maccody/KanaChordPlus/software/kanji_ms.h

/* kanji_ms.h */
/**
This file is part of KanaChordPlus Keyboard.
 Copyright (C) 2024 Mac A. Cody

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
 You should have received a copy of the GNU General Public License
 along with this program.  If not, see <http://www.gnu.org/licenses/>.
**/

const char kanji_ms4E00[] = "one, one radical (no.1)";
const char kanji_ms5927[] = "large, big";
const char kanji_ms4EBA[] = "person";
const char kanji_ms898B[] = "see, hopes, chances, idea, opinion, look at, visible";
const char kanji_ms51FA[] = "exit, leave, go out, come out, put out, protrude";
const char kanji_ms4E2D[] = "in, inside, middle, mean, center";
const char kanji_ms601D[] = "think";
const char kanji_ms6642[] = "time, hour";
const char kanji_ms65E5[] = "day, sun, Japan, counter for days";
const char kanji_ms4E0A[] = "above, up";
const char kanji_ms6C17[] = "spirit, mind, air, atmosphere, mood";
const char kanji_ms884C[] = "going, journey, carry out, conduct, act, line, row, bank";
const char kanji_ms76EE[] = "eye, class, look, insight, experience, care, favor";
const char kanji_ms9593[] = "interval, space";
const char kanji_ms751F[] = "life, genuine, birth";
const char kanji_ms5F8C[] = "behind, back, later";
const char kanji_ms8A00[] = "say, word";
const char kanji_ms5206[] = "part, minute of time, segment, share, degree, one's lot, duty, understand, know, rate, 1%, chances, shaku/100";
const char kanji_ms524D[] = "in front, before";
const char kanji_ms81EA[] = "oneself";
const char kanji_ms77E5[] = "know, wisdom";
const char kanji_ms624B[] = "hand";
const char kanji_ms5168[] = "whole, entire, all, complete, fulfill";
const char kanji_ms672C[] = "book, present, main, origin, true, real, counter for long cylindrical things";
const char kanji_ms6765[] = "come, due, next, cause, become";
const char kanji_ms4E8B[] = "matter, thing, fact, business, reason, possibly";
const char kanji_ms65B9[] = "direction, person, alternative";
const char kanji_ms7269[] = "thing, object, matter";
const char kanji_ms4E0B[] = "below, down, descend, give, low, inferior";
const char kanji_ms610F[] = "idea, mind, heart, taste, thought, desire, care, liking";
const char kanji_ms5EA6[] = "degrees, occurrence, time, counter for occurrences, consider, attitude";
const char kanji_ms5165[] = "enter, insert";
const char kanji_ms5B50[] = "child, sign of the rat, 11PM-1AM, first sign of Chinese zodiac";
const char kanji_ms4E8C[] = "two, two radical (no. 7)";
const char kanji_ms8A71[] = "tale, talk";
const char kanji_ms7ACB[] = "stand up, rise, set up, erect";
const char kanji_ms4F53[] = "body, substance, object, reality, counter for images";
const char kanji_ms4E0D[] = "negative, non-, bad, ugly, clumsy";
const char kanji_ms5FC3[] = "heart, mind, spirit, heart radical (no. 61)";
const char kanji_ms8EAB[] = "somebody, person, one's station in life";
const char kanji_ms660E[] = "bright, light";
const char kanji_ms4F55[] = "what";
const char kanji_ms5473[] = "flavor, taste";
const char kanji_ms90E8[] = "section, bureau, dept, class, copy, part, portion, counter for copies of a newspaper or magazine";
const char kanji_ms5E74[] = "year, counter for years";
const char kanji_ms5834[] = "location, place";
const char kanji_ms7121[] = "nothingness, none, ain't, nothing, nil, not";
const char kanji_ms6700[] = "utmost, most, extreme";
const char kanji_ms5C0F[] = "little, small";
const char kanji_ms8005[] = "someone, person";
const char kanji_ms9577[] = "long, leader, superior, senior";
const char kanji_ms901A[] = "traffic, pass through, avenue, commute, counter for letters, notes, documents, etc.";
const char kanji_ms540C[] = "same, agree, equal";
const char kanji_ms611F[] = "emotion, feeling, sensation";
const char kanji_ms5F53[] = "hit, right, appropriate, himself";
const char kanji_ms529B[] = "power, strength, strong, strain, bear up, exert";
const char kanji_ms5916[] = "outside";
const char kanji_ms5730[] = "ground, earth";
const char kanji_ms9762[] = "mask, face, features, surface";
const char kanji_ms5408[] = "fit, suit, join, 0.1";
const char kanji_ms7406[] = "logic, arrangement, reason, justice, truth";
const char kanji_ms4EE5[] = "by means of, because, in view of, compared with";
const char kanji_ms9AD8[] = "tall, high, expensive";
const char kanji_ms8FD1[] = "near, early, akin, tantamount";
const char kanji_ms4F1A[] = "meeting, meet, party, association, interview, join";
const char kanji_ms6301[] = "hold, have";
const char kanji_ms5B9F[] = "reality, truth, seed, fruit, nut";
const char kanji_ms767D[] = "white";
const char kanji_ms58F0[] = "voice";
const char kanji_ms53E3[] = "mouth";
const char kanji_ms5148[] = "before, ahead, previous, future, precedence";
const char kanji_ms52D5[] = "move, motion, change, confusion, shift, shake";
const char kanji_ms982D[] = "head, counter for large animals";
const char kanji_ms4ECA[] = "now";
const char kanji_ms6240[] = "place, extent";
const char kanji_ms6587[] = "sentence, literature, style, art, decoration, figures, plan, literary radical (no. 67)";
const char kanji_ms5909[] = "unusual, change, strange";
const char kanji_ms9854[] = "face, expression";
const char kanji_ms4E16[] = "generation, world, society, public";
const char kanji_ms767A[] = "departure, discharge, publish, emit, start from, disclose, counter for gunshots";
const char kanji_ms540D[] = "name, noted, distinguished, reputation";
const char kanji_ms8DB3[] = "leg, foot, be sufficient, counter for pairs of footwear";
const char kanji_ms7684[] = "bull's eye, mark, target, object, adjective ending";
const char kanji_ms8272[] = "color";
const char kanji_ms60AA[] = "bad, vice, rascal, false, evil, wrong";
const char kanji_ms60C5[] = "feelings, emotion, passion, sympathy, circumstances, facts";
const char kanji_ms5207[] = "cut, cutoff, be sharp";
const char kanji_ms7136[] = "sort of thing, so, if so, in that case, well";
const char kanji_ms8003[] = "consider, think over";
const char kanji_ms4F5C[] = "make, production, prepare, build";
const char kanji_ms8FD4[] = "return, answer, fade, repay";
const char kanji_ms843D[] = "fall, drop, come down, village, hamlet";
const char kanji_ms7D50[] = "tie, bind, contract, join, organize, do up hair, fasten";
const char kanji_ms958B[] = "open, unfold, unseal";
const char kanji_ms5BB6[] = "house, home, family, professional, expert, performer";
const char kanji_ms6B63[] = "correct, justice, righteous, 10**40";
const char kanji_ms98A8[] = "wind, air, style, manner";
const char kanji_ms521D[] = "first time, beginning";
const char kanji_ms4E09[] = "three";
const char kanji_ms91CD[] = "heavy, important, esteem, respect, heap up, pile up, nest of boxes, -fold";
const char kanji_ms5C11[] = "few, little";
const char kanji_ms5411[] = "yonder, facing, beyond, confront, defy, tend toward, approach";
const char kanji_ms6708[] = "month, moon";
const char kanji_ms73FE[] = "present, existing, actual";
const char kanji_ms6570[] = "number, strength, fate, law, figures";
const char kanji_ms7528[] = "utilize, business, service, use, employ";
const char kanji_ms7A7A[] = "empty, sky, void, vacant, vacuum";
const char kanji_ms8868[] = "surface, table, chart, diagram";
const char kanji_ms5185[] = "inside, within, between, among, house, home";
const char kanji_ms97F3[] = "sound, noise";
const char kanji_ms805E[] = "hear, ask, listen";
const char kanji_ms69D8[] = "Esq., way, manner, situation, polite suffix";
const char kanji_ms771F[] = "true, reality, Buddhist sect";
const char kanji_ms9053[] = "road-way, street, district, journey, course, moral, teachings";
const char kanji_ms7740[] = "don, arrive, wear, counter for suits of clothing";
const char kanji_ms4EE3[] = "substitute, change, convert, replace, period, age, counter for decades of ages, eras, etc., generation, charge, rate, fee";
const char kanji_ms5973[] = "woman, female";
const char kanji_ms76F8[] = "inter-, mutual, together, each other, minister of state, councillor, aspect, phase, physiognomy";
const char kanji_ms8449[] = "leaf, plane, lobe, needle, blade, spear, counter for flat things, fragment, piece";
const char kanji_ms597D[] = "fond, pleasing, like something";
const char kanji_ms591A[] = "many, frequent, much";
const char kanji_ms5B89[] = "relax, cheap, low, quiet, rested, contented, peaceful";
const char kanji_ms554F[] = "question, ask, problem";
const char kanji_ms5F85[] = "wait, depend on";
const char kanji_ms76F4[] = "straightaway, honesty, frankness, fix, repair";
const char kanji_ms5B9A[] = "determine, fix, establish, decide";
const char kanji_ms66F8[] = "write";
const char kanji_ms4FE1[] = "faith, truth, fidelity, trust";
const char kanji_ms5BFE[] = "vis-a-vis, opposite, even, equal, versus, anti-, compare";
const char kanji_ms5149[] = "ray, light";
const char kanji_ms534A[] = "half, middle, odd number, semi-, part-";
const char kanji_ms96C6[] = "gather, meet, congregate, swarm, flock";
const char kanji_ms5225[] = "separate, branch off, diverge, fork, another, extra, specially";
const char kanji_ms6C7A[] = "decide, fix, agree upon, appoint";
const char kanji_ms4E3B[] = "lord, chief, master, main thing, principal";
const char kanji_ms6B69[] = "walk, counter for steps";
const char kanji_ms89E3[] = "unravel, notes, key, explanation, understanding, untie, undo, solve, answer, cancel, absolve, explain, minute";
const char kanji_ms6B7B[] = "death, die";
const char kanji_ms6027[] = "sex, gender, nature";
const char kanji_ms5F37[] = "strong";
const char kanji_ms7F6E[] = "placement, put, set, deposit, leave behind, keep, employ, pawn";
const char kanji_ms7B11[] = "laugh";
const char kanji_ms98DF[] = "eat, food";
const char kanji_ms6307[] = "finger, point to, indicate, put into, play (chess), measure (ruler)";
const char kanji_ms6B8B[] = "remainder, leftover, balance";
const char kanji_ms5143[] = "beginning, former time, origin";
const char kanji_ms5C4B[] = "roof, house, shop, dealer, seller";
const char kanji_ms6D41[] = "current, a sink, flow, forfeit";
const char kanji_ms65B0[] = "new";
const char kanji_ms547C[] = "call, call out to, invite";
const char kanji_ms9060[] = "distant, far";
const char kanji_ms5341[] = "ten";
const char kanji_ms4F7F[] = "use, send on a mission, order, messenger, envoy, ambassador, cause";
const char kanji_ms7D42[] = "end, finish";
const char kanji_ms6559[] = "teach, faith, doctrine";
const char kanji_ms95A2[] = "connection, barrier, gateway, involve, concerning";
const char kanji_ms606F[] = "breath, respiration, son, interest (on money), nuture, rest, coming to an end";
const char kanji_ms914D[] = "distribute, spouse, exile, rationing";
const char kanji_ms8AAC[] = "opinion, theory, explanation, rumor";
const char kanji_ms795E[] = "gods, mind, soul";
const char kanji_ms53D6[] = "take, fetch, take up";
const char kanji_ms7537[] = "male";
const char kanji_ms5929[] = "heavens, sky, imperial";
const char kanji_ms8ABF[] = "tune, tone, meter, key (music), writing style, prepare, exorcise, investigate, harmonize, mediate";
const char kanji_ms6B21[] = "next, order, sequence";
const char kanji_ms59FF[] = "figure, form, shape";
const char kanji_ms80CC[] = "stature, height, back, behind, disobey, defy, go back on, rebel";
const char kanji_ms899A[] = "memorize, learn, remember, awake, sober up";
const char kanji_ms697D[] = "music, comfort, ease";
const char kanji_ms7D76[] = "discontinue, sever, cut off, abstain, interrupt, suppress, be beyond, without match, peerless, unparalleled";
const char kanji_ms91D1[] = "gold";
const char kanji_ms60F3[] = "concept, think, idea, thought";
const char kanji_ms679C[] = "fruit, reward, carry out, achieve, complete, end, finish, succeed";
const char kanji_ms8D77[] = "rouse, wake up, get up";
const char kanji_ms5F62[] = "shape, form, style";
const char kanji_ms5E73[] = "even, flat, peace";
const char kanji_ms8981[] = "need, main point, essence, pivot, key to";
const char kanji_ms5F15[] = "pull, tug, jerk, admit, install, quote, refer to";
const char kanji_ms547D[] = "fate, command, decree, destiny, life, appoint";
const char kanji_ms904B[] = "carry, luck, destiny, fate, lot, transport, progress, advance";
const char kanji_ms82E6[] = "suffering, trial, worry, hardship, feel bitter, scowl";
const char kanji_ms5F97[] = "gain, get, find, earn, acquire, can, may, able to, profit, advantage, benefit";
const char kanji_ms4ED5[] = "attend, doing, official, serve";
const char kanji_ms591C[] = "night, evening";
const char kanji_ms4F1D[] = "transmit, go along, walk along, follow, report, communicate, legend, tradition";
const char kanji_ms653E[] = "set free, release, fire, shoot, emit, banish, liberate";
const char kanji_ms5931[] = "lose, error, fault, disadvantage, loss";
const char kanji_ms9023[] = "take along, lead, join, connect, party, gang, clique";
const char kanji_ms6DF1[] = "deep, heighten, intensify, strengthen";
const char kanji_ms7A81[] = "stab, protruding, thrust, pierce, prick, collision, sudden";
const char kanji_ms754C[] = "world, boundary";
const char kanji_ms6210[] = "turn into, become, get, grow, elapse, reach";
const char kanji_ms70B9[] = "spot, point, mark, speck, decimal point";
const char kanji_ms65E9[] = "early, fast";
const char kanji_ms6D88[] = "extinguish, blow out, turn off, neutralize, cancel";
const char kanji_ms56DE[] = "-times, round, game, revolve, counter for occurrences";
const char kanji_ms53D7[] = "accept, undergo, answer (phone), take, get, catch, receive";
const char kanji_ms5F35[] = "counter for bows & stringed instruments, stretch, spread, put up (tent)";
const char kanji_ms53CD[] = "anti-";
const char kanji_ms7531[] = "wherefore, a reason";
const char kanji_ms5B57[] = "character, letter, word, section of village";
const char kanji_ms5FC5[] = "invariably, certain, inevitable";
const char kanji_ms5316[] = "change, take the form of, influence, enchant, delude, -ization";
const char kanji_ms96E2[] = "detach, separation, disjoin, digress";
const char kanji_ms7279[] = "special";
const char kanji_ms8A18[] = "scribe, account, narrative";
const char kanji_ms5728[] = "exist, outskirts, suburbs, located in";
const char kanji_ms904E[] = "overdo, exceed, go beyond, error";
const char kanji_ms4ED6[] = "other, another, the others";
const char kanji_ms6A5F[] = "loom, mechanism, machine, airplane, opportunity, potency, efficacy, occasion";
const char kanji_ms8FFD[] = "chase, drive away, follow, pursue, meanwhile";
const char kanji_ms53BB[] = "gone, past, quit, leave, elapse, eliminate, divorce";
const char kanji_ms5E30[] = "homecoming, arrive at, lead to, result in";
const char kanji_ms4E57[] = "ride, power, multiplication, record, counter for vehicles, board, mount, join";
const char kanji_ms6025[] = "hurry, emergency, sudden, steep";
const char kanji_ms6C34[] = "water";
const char kanji_ms65AD[] = "severance, decline, refuse, apologize, warn, dismiss, prohibit, decision, judgement, cutting";
const char kanji_ms89AA[] = "parent, intimacy, relative, familiarity, dealer (cards)";
const char kanji_ms5B66[] = "study, learning, science";
const char kanji_ms4E21[] = "both, old Japanese coin, counter for carriages (e.g., in a train), two";
const char kanji_ms6A2A[] = "sideways, side, horizontal, width, woof, unreasonable, perverse";
const char kanji_ms5E83[] = "wide, broad, spacious";
const char kanji_ms5E38[] = "usual, ordinary, normal, common, regular, continually, always, long-lasting";
const char kanji_ms5F7C[] = "he, that, the";
const char kanji_ms8A9E[] = "word, speech, language";
const char kanji_ms8D70[] = "run";
const char kanji_ms6E80[] = "full, fullness, enough, satisfy";
const char kanji_ms91CE[] = "plains, field, rustic, civilian life";
const char kanji_ms9996[] = "neck, counter for songs and poems";
const char kanji_ms5BC4[] = "draw near, stop in, bring near, gather, collect, send, forward";
const char kanji_ms56DB[] = "four";
const char kanji_ms9ED2[] = "black";
const char kanji_ms696D[] = "business, vocation, arts, performance";
const char kanji_ms756A[] = "turn, number in a series";
const char kanji_ms9032[] = "advance, proceed, progress, promote";
const char kanji_ms984C[] = "topic, subject";
const char kanji_ms7F8E[] = "beauty, beautiful";
const char kanji_ms6BB5[] = "grade, steps, stairs";
const char kanji_ms7DDA[] = "line, track";
const char kanji_ms6253[] = "strike, hit, knock, pound, dozen";
const char kanji_ms7D4C[] = "sutra, longitude, pass thru, expire, warp";
const char kanji_ms6697[] = "darkness, disappear, shade, informal, grow dark, be blinded";
const char kanji_ms7D30[] = "dainty, get thin, taper, slender, narrow, detailed, precise";
const char kanji_ms5FF5[] = "wish, sense, idea, thought, feeling, desire, attention";
const char kanji_ms72B6[] = "status quo, conditions, circumstances, form, appearance";
const char kanji_ms671F[] = "period, time, date, term";
const char kanji_ms9001[] = "escort, send";
const char kanji_ms98DB[] = "fly, skip (pages), scatter";
const char kanji_ms4F3C[] = "becoming, resemble, counterfeit, imitate, suitable";
const char kanji_ms6709[] = "possess, have, exist, happen, occur, approx";
const char kanji_ms7D20[] = "elementary, principle, naked, uncovered";
const char kanji_ms7B54[] = "solution, answer";
const char kanji_ms8AAD[] = "read";
const char kanji_ms544A[] = "revelation, tell, inform, announce";
const char kanji_ms611B[] = "love, affection, favourite";
const char kanji_ms6B62[] = "stop, halt";
const char kanji_ms9003[] = "escape, flee, shirk, evade, set free";
const char kanji_ms6D6E[] = "floating, float, rise to surface";
const char kanji_ms683C[] = "status, rank, capacity, character, case (law, grammar)";
const char kanji_ms51B7[] = "cool, cold (beer, person), chill";
const char kanji_ms8D64[] = "red";
const char kanji_ms78BA[] = "assurance, firm, tight, hard, solid, confirm, clear, evident";
const char kanji_ms8033[] = "ear";
const char kanji_ms59CB[] = "commence, begin";
const char kanji_ms52DD[] = "victory, win, prevail, excel";
const char kanji_ms80FD[] = "ability, talent, skill, capacity";
const char kanji_ms4E94[] = "five";
const char kanji_ms6CE8[] = "pour, irrigate, shed (tears), flow into, concentrate on, notes, comment, annotate";
const char kanji_ms5C71[] = "mountain";
const char kanji_ms8EE2[] = "revolve, turn around, change";
const char kanji_ms5FDC[] = "apply, answer, yes, OK, reply, accept";
const char kanji_ms5FD8[] = "forget";
const char kanji_ms5B58[] = "exist, suppose, be aware of, believe, feel";
const char kanji_ms614B[] = "attitude, condition, figure, appearance, voice (of verbs)";
const char kanji_ms670D[] = "clothing, admit, obey, discharge";
const char kanji_ms6839[] = "root, radical, head (pimple)";
const char kanji_ms539F[] = "meadow, original, primitive, field, plain, prairie, tundra, wilderness";
const char kanji_ms671B[] = "ambition, full moon, hope, desire, aspire to, expect";
const char kanji_ms7247[] = "one-sided, leaf, sheet, right-side kata radical (no. 91)";
const char kanji_ms5012[] = "overthrow, fall, collapse, drop, break down";
const char kanji_ms6050[] = "fear, dread, awe";
const char kanji_ms9759[] = "quiet";
const char kanji_ms7B2C[] = "No., residence";
const char kanji_ms671D[] = "morning, dynasty, regime, epoch, period, (North) Korea";
const char kanji_ms53F0[] = "pedestal, a stand, counter for machines and vehicles";
const char kanji_ms8B70[] = "deliberation, consultation, debate, consideration";
const char kanji_ms62BC[] = "push, stop, check, subdue, attach, seize, weight, shove, press, seal, do in spite of";
const char kanji_ms9752[] = "blue, green";
const char kanji_ms6CD5[] = "method, law, rule, principle, model, system";
const char kanji_ms6D3B[] = "lively, resuscitation, being helped, living";
const char kanji_ms9CF4[] = "chirp, cry, bark, sound, ring, echo, honk";
const char kanji_ms7D44[] = "association, braid, plait, construct, assemble, unite, cooperate, grapple";
const char kanji_ms5177[] = "tool, utensil, means, possess, ingredients, counter for armor, suits, sets of furniture";
const char kanji_ms592B[] = "husband, man";
const char kanji_ms8A08[] = "plot, plan, scheme, measure";
const char kanji_ms4ED8[] = "adhere, attach, refer to, append";
const char kanji_ms54C1[] = "goods, refinement, dignity, article, counter for meal courses";
const char kanji_ms60B2[] = "grieve, sad, deplore, regret";
const char kanji_ms52A0[] = "add, addition, increase, join, include, Canada";
const char kanji_ms7D04[] = "promise, approximately, shrink";
const char kanji_ms5EA7[] = "squat, seat, cushion, gathering, sit";
const char kanji_ms52E2[] = "forces, energy, military strength";
const char kanji_ms4EA4[] = "mingle, mixing, association, coming & going";
const char kanji_ms53EF[] = "can, passable, mustn't, should not, do not";
const char kanji_ms80F8[] = "bosom, breast, chest, heart, feelings";
const char kanji_ms8996[] = "inspection, regard as, see, look at";
const char kanji_ms53E4[] = "old";
const char kanji_ms5999[] = "exquisite, strange, queer, mystery, miracle, excellent, delicate, charming";
const char kanji_ms71B1[] = "heat, temperature, fever, mania, passion";
const char kanji_ms4E88[] = "beforehand, previous, myself, I";
const char kanji_ms8CEA[] = "substance, quality, matter, temperament";
const char kanji_ms6728[] = "tree, wood";
const char kanji_ms629C[] = "slip out, extract, pull out, pilfer, quote, remove, omit";
const char kanji_ms5074[] = "side, lean, oppose, regret";
const char kanji_ms5229[] = "profit, advantage, benefit";
const char kanji_ms9858[] = "petition, request, vow, wish, hope";
const char kanji_ms5F71[] = "shadow, silhouette, phantom";
const char kanji_ms6BBA[] = "kill, murder, butcher, slice off, split, diminish, reduce, spoil";
const char kanji_ms5922[] = "dream, vision, illusion";
const char kanji_ms592A[] = "plump, thick, big around";
const char kanji_ms5F79[] = "duty, war, campaign, drafted labor, office, service, role";
const char kanji_ms8B58[] = "discriminating, know, write";
const char kanji_ms5B88[] = "guard, protect, defend, obey";
const char kanji_ms5E95[] = "bottom, sole, depth, bottom price, base, kind, sort";
const char kanji_ms9650[] = "limit, restrict, to best of ability";
const char kanji_ms9014[] = "route, way, road";
const char kanji_ms6563[] = "scatter, disperse, spend, squander";
const char kanji_ms8840[] = "blood";
const char kanji_ms7D9A[] = "continue, series, sequel";
const char kanji_ms5C45[] = "reside, to be, exist, live with";
const char kanji_ms88CF[] = "back, amidst, in, reverse, inside, palm, sole, rear, lining, wrong side";
const char kanji_ms8EFD[] = "lightly, trifling, unimportant";
const char kanji_ms4E71[] = "riot, war, disorder, disturb";
const char kanji_ms4F4F[] = "dwell, reside, live, inhabit";
const char kanji_ms5DEE[] = "distinction, difference, variation, discrepancy, margin, balance";
const char kanji_ms5BB9[] = "contain, form, looks";
const char kanji_ms7AEF[] = "edge, origin, end, point, border, verge, cape";
const char kanji_ms82E5[] = "young, if, perhaps, possibly, low number, immature";
const char kanji_ms969B[] = "occasion, side, edge, verge, dangerous, adventurous, indecent, time, when";
const char kanji_ms6295[] = "throw, discard, abandon, launch into, join, invest in, hurl, give up, sell at a loss";
const char kanji_ms4FC2[] = "person in charge, connection, duty, concern oneself";
const char kanji_ms96E3[] = "difficult, impossible, trouble, accident, defect";
const char kanji_ms5358[] = "simple, one, single, merely";
const char kanji_ms56F2[] = "surround, besiege, store, paling, enclosure, encircle, preserve, keep";
const char kanji_ms8CA0[] = "defeat, negative, -, minus, bear, owe, assume a responsibility";
const char kanji_ms516B[] = "eight, eight radical (no. 12)";
const char kanji_ms5668[] = "utensil, vessel, receptacle, implement, instrument, ability, container, tool, set";
const char kanji_ms666F[] = "scenery, view";
const char kanji_ms5965[] = "heart, interior";
const char kanji_ms5DFB[] = "scroll, volume, book, part, roll up, wind up, tie, coil, counter for texts (or book scrolls)";
const char kanji_ms56FD[] = "country";
const char kanji_ms52A9[] = "help, rescue, assist";
const char kanji_ms7CBE[] = "refined, ghost, fairy, energy, vitality, semen, excellence, purity, skill";
const char kanji_ms62B1[] = "embrace, hug, hold in arms";
const char kanji_ms7834[] = "rend, rip, tear, break, destroy, defeat, frustrate";
const char kanji_ms9055[] = "difference, differ";
const char kanji_ms75DB[] = "pain, hurt, damage, bruise";
const char kanji_ms5BA4[] = "room, apartment, chamber, greenhouse, cellar";
const char kanji_ms8155[] = "arm, ability, talent";
const char kanji_ms6E21[] = "transit, ford, ferry, cross, import, deliver, diameter, migrate";
const char kanji_ms50CF[] = "statue, picture, image, figure, portrait";
const char kanji_ms9054[] = "accomplished, reach, arrive, attain";
const char kanji_ms983C[] = "trust, request";
const char kanji_ms8179[] = "abdomen, belly, stomach";
const char kanji_ms4F8B[] = "example, custom, usage, precedent";
const char kanji_ms53F3[] = "right";
const char kanji_ms8208[] = "entertain, revive, retrieve, interest, pleasure";
const char kanji_ms706B[] = "fire";
const char kanji_ms793C[] = "salute, bow, ceremony, thanks, remuneration";
const char kanji_ms523B[] = "engrave, cut fine, chop, hash, mince, time, carving";
const char kanji_ms5BDD[] = "lie down, sleep, rest, bed, remain unsold";
const char kanji_ms53CB[] = "friend";
const char kanji_ms5272[] = "proportion, comparatively, divide, cut, separate, split";
const char kanji_ms8DEF[] = "path, route, road, distance";
const char kanji_ms7570[] = "uncommon, different, queerness, strangeness, wonderful, curious, unusual";
const char kanji_ms5F0F[] = "style, ceremony, rite, function, method, system, form, expression";
const char kanji_ms4F59[] = "too much, myself, surplus, other, remainder";
const char kanji_ms56F0[] = "quandary, become distressed, annoyed";
const char kanji_ms632F[] = "shake, wave, wag, swing";
const char kanji_ms89D2[] = "angle, corner, square, horn, antlers";
const char kanji_ms8AC7[] = "discuss, talk";
const char kanji_ms675F[] = "bundle, sheaf, ream, tie in bundles, govern, manage, control";
const char kanji_ms6539[] = "reformation, change, modify, mend, renew, examine, inspect, search";
const char kanji_ms516D[] = "six";
const char kanji_ms5E78[] = "happiness, blessing, fortune";
const char kanji_ms6298[] = "fold, break, fracture, bend, yield, submit";
const char kanji_ms6848[] = "plan, suggestion, draft, ponder, fear, proposition, idea, expectation, worry, table, bench";
const char kanji_ms5F31[] = "weak, frail";
const char kanji_ms58EB[] = "gentleman, scholar, samurai, samurai radical (no. 33)";
const char kanji_ms571F[] = "soil, earth, ground, Turkey";
const char kanji_ms8089[] = "meat";
const char kanji_ms7A2E[] = "species, kind, class, variety, seed";
const char kanji_ms8D8A[] = "surpass, cross over, move to, exceed, Vietnam";
const char kanji_ms77F3[] = "stone";
const char kanji_ms6012[] = "angry, be offended";
const char kanji_ms652F[] = "branch, support, sustain, branch radical (no. 65)";
const char kanji_ms56F3[] = "map, drawing, plan, extraordinary, audacious";
const char kanji_ms767E[] = "hundred";
const char kanji_ms4E03[] = "seven";
const char kanji_ms88C5[] = "attire, dress, pretend, disguise, profess";
const char kanji_ms826F[] = "good, pleasing, skilled";
const char kanji_ms964D[] = "descend, precipitate, fall, surrender";
const char kanji_ms9ED9[] = "silence, become silent, stop speaking, leave as is";
const char kanji_ms9589[] = "closed, shut";
const char kanji_ms4F11[] = "rest, day off, retire, sleep";
const char kanji_ms5224[] = "judgement, judgment, signature, stamp, seal";
const char kanji_ms80A9[] = "shoulder";
const char kanji_ms7167[] = "illuminate, shine, compare, bashful";
const char kanji_ms5DE6[] = "left";
const char kanji_ms8A31[] = "permit, approve";
const char kanji_ms7D19[] = "paper";
const char kanji_ms4F9B[] = "submit, offer, present, serve (meal), accompany";
const char kanji_ms77AC[] = "wink, blink, twinkle";
const char kanji_ms6599[] = "fee, materials";
const char kanji_ms548C[] = "harmony, Japanese style, peace, soften, Japan";
const char kanji_ms4F4D[] = "rank, grade, throne, crown, about, some";
const char kanji_ms968E[] = "storey, stair, counter for storeys of a building";
const char kanji_ms96D1[] = "miscellaneous";
const char kanji_ms985E[] = "sort, kind, variety, class, genus";
const char kanji_ms8FF7[] = "astray, be perplexed, in doubt, lost, err, illusion";
const char kanji_ms98F2[] = "drink, smoke, take";
const char kanji_ms672B[] = "end, close, tip, powder, posterity";
const char kanji_ms4E26[] = "row, and, besides, as well as, line up, rank with, rival, equal";
const char kanji_ms4EF6[] = "affair, case, matter, item";
const char kanji_ms4EF2[] = "go-between, relationship";
const char kanji_ms9000[] = "retreat, withdraw, retire, resign, repel, expel, reject";
const char kanji_ms89B3[] = "outlook, look, appearance, condition, view";
const char kanji_ms821E[] = "dance, flit, circle, wheel";
const char kanji_ms5BC6[] = "secrecy, density (pop), minuteness, carefulness";
const char kanji_ms9AEA[] = "hair of the head";
const char kanji_ms5831[] = "report, news, reward, retribution";
const char kanji_ms5947[] = "strange, strangeness, curiosity";
const char kanji_ms9006[] = "inverted, reverse, opposite, wicked";
const char kanji_ms516C[] = "public, prince, official, governmental";
const char kanji_ms5439[] = "blow, breathe, puff, emit, smoke";
const char kanji_ms4E07[] = "ten thousand, 10,000";
const char kanji_ms5371[] = "dangerous, fear, uneasy";
const char kanji_ms8170[] = "loins, hips, waist, low wainscoting";
const char kanji_ms5B8C[] = "perfect, completion, end";
const char kanji_ms60D1[] = "beguile, delusion, perplexity";
const char kanji_ms6FC0[] = "violent, get excited, enraged, chafe, incite";
const char kanji_ms90FD[] = "metropolis, capital, all, everything";
const char kanji_ms77ED[] = "short, brevity, fault, defect, weak point";
const char kanji_ms6226[] = "war, battle, match";
const char kanji_ms9A5A[] = "wonder, be surprised, frightened, amazed";
const char kanji_ms4FDD[] = "protect, guarantee, keep, preserve, sustain, support";
const char kanji_ms75C5[] = "ill, sick";
const char kanji_ms79C1[] = "private, I, me";
const char kanji_ms8A3C[] = "evidence, proof, certificate";
const char kanji_ms8ECA[] = "car";
const char kanji_ms753B[] = "brush-stroke, picture";
const char kanji_ms6B32[] = "longing, covetousness, greed, passion, desire, craving";
const char kanji_ms4EFB[] = "responsibility, duty, term, entrust to, appoint";
const char kanji_ms8CB7[] = "buy";
const char kanji_ms72EC[] = "single, alone, spontaneously, Germany";
const char kanji_ms9B54[] = "witch, demon, evil spirit";
const char kanji_ms904A[] = "play";
const char kanji_ms4F4E[] = "lower, short, humble";
const char kanji_ms9580[] = "gate, counter for cannons";
const char kanji_ms69CB[] = "posture, stance, appearance, build, set up";
const char kanji_ms99AC[] = "horse";
const char kanji_ms5BA2[] = "guest, visitor, customer, client";
const char kanji_ms793A[] = "show, indicate, point out, express, display";
const char kanji_ms7591[] = "doubt, distrust, be suspicious, question";
const char kanji_ms6C42[] = "request, want, wish for, require, demand";
const char kanji_ms512A[] = "tenderness, excel, surpass, actor, superiority, gentleness";
const char kanji_ms6BCD[] = "mother";
const char kanji_ms7720[] = "sleep, die, sleepy";
const char kanji_ms8584[] = "dilute, thin, weak (tea), pampas grass";
const char kanji_ms8E0F[] = "step, trample, carry through, appraise, evade payment";
const char kanji_ms8A8D[] = "acknowledge, witness, discern, recognize, appreciate, believe";
const char kanji_ms5FAE[] = "delicate, minuteness, insignificance";
const char kanji_ms5099[] = "equip, provision, preparation";
const char kanji_ms52B4[] = "labor, thank for, reward for, toil, trouble";
const char kanji_ms5ACC[] = "dislike, detest, hate";
const char kanji_ms7533[] = "have the honor to, sign of the monkey, 3-5PM, ninth sign of Chinese zodiac";
const char kanji_ms5BDF[] = "guess, presume, surmise, judge, understand";
const char kanji_ms5236[] = "system, law, rule";
const char kanji_ms79FB[] = "shift, move, change, drift, catch (cold, fire), pass into";
const char kanji_ms8FBC[] = "crowded, mixture, in bulk, included, (kokuji)";
const char kanji_ms7236[] = "father";
const char kanji_ms82B1[] = "flower";
const char kanji_ms518D[] = "again, twice, second time";
const char kanji_ms559C[] = "rejoice, take pleasure in";
const char kanji_ms58F2[] = "sell";
const char kanji_ms50B7[] = "wound, hurt, injure, impair, pain, injury, cut, gash, scar, weak point";
const char kanji_ms6B73[] = "year-end, age, occasion, opportunity";
const char kanji_ms58C1[] = "wall, lining (stomach), fence";
const char kanji_ms8336[] = "tea";
const char kanji_ms65CF[] = "tribe, family";
const char kanji_ms713C[] = "bake, burning";
const char kanji_ms4ECB[] = "jammed in, shellfish, mediate, concern oneself with";
const char kanji_ms8FBA[] = "environs, boundary, border, vicinity";
const char kanji_ms66AE[] = "evening, twilight, season's end, livelihood, make a living, spend time";
const char kanji_ms6C88[] = "sink, be submerged, subside, be depressed, aloes";
const char kanji_ms7B4B[] = "muscle, sinew, tendon, fiber, plot, plan, descent";
const char kanji_ms6211[] = "ego, I, selfish, our, oneself";
const char kanji_ms6255[] = "pay, clear out, prune, banish, dispose of";
const char kanji_ms5468[] = "circumference, circuit, lap";
const char kanji_ms975E[] = "un-, mistake, negative, injustice, non-";
const char kanji_ms672A[] = "un-, not yet, hitherto, still, even now, sign of the ram, 1-3PM, eighth sign of Chinese zodiac";
const char kanji_ms7FA9[] = "righteousness, justice, morality, honor, loyalty, meaning";
const char kanji_ms663C[] = "daytime, noon";
const char kanji_ms54E1[] = "employee, member, number, the one in charge";
const char kanji_ms5915[] = "evening";
const char kanji_ms5E8A[] = "bed, counter for beds, floor, padding, tatami";
const char kanji_ms6483[] = "beat, attack, defeat, conquer";
const char kanji_ms8AD6[] = "argument, discourse";
const char kanji_ms63A2[] = "grope, search, look for";
const char kanji_ms53C2[] = "nonplussed, three (in documents), going, coming, visiting, visit, be defeated, die, be madly in love, participate, take part in";
const char kanji_ms96A0[] = "conceal, hide, cover";
const char kanji_ms9020[] = "create, make, structure, physique";
const char kanji_ms5370[] = "stamp, seal, mark, imprint, symbol, emblem, trademark, evidence, souvenir, India";
const char kanji_ms5EFA[] = "build";
const char kanji_ms8853[] = "art, technique, skill, means, trick, resources, magic";
const char kanji_ms63A5[] = "touch, contact, adjoin, piece together";
const char kanji_ms5C40[] = "bureau, board, office, affair, conclusion, court lady, lady-in-waiting, her apartment";
const char kanji_ms6BDB[] = "fur, hair, feather, down";
const char kanji_ms5E2F[] = "sash, belt, obi, zone, region";
const char kanji_ms6D3E[] = "faction, group, party, clique, sect, school";
const char kanji_ms8C61[] = "elephant, pattern after, imitate, image, shape, sign (of the times)";
const char kanji_ms523A[] = "thorn, pierce, stab, prick, sting, calling card";
const char kanji_ms6CE3[] = "cry, weep, moan";
const char kanji_ms6238[] = "door, counter for houses, door radical (no. 63)";
const char kanji_ms5438[] = "suck, imbibe, inhale, sip";
const char kanji_ms6614[] = "once upon a time, antiquity, old times";
const char kanji_ms6016[] = "dreadful, be frightened, fearful";
const char kanji_ms9078[] = "elect, select, choose, prefer";
const char kanji_ms773C[] = "eyeball";
const char kanji_ms8349[] = "grass, weeds, herbs, pasture, write, draft";
const char kanji_ms9A12[] = "boisterous, make noise, clamor, disturb, excite";
const char kanji_ms5FEB[] = "cheerful, pleasant, agreeable, comfortable";
const char kanji_ms56FA[] = "harden, set, clot, curdle";
const char kanji_ms6BCE[] = "every";
const char kanji_ms9A13[] = "verification, effect, testing";
const char kanji_ms79D8[] = "secret, conceal";
const char kanji_ms6D77[] = "sea, ocean";
const char kanji_ms89E6[] = "contact, touch, feel, hit, proclaim, announce, conflict";
const char kanji_ms6545[] = "happenstance, especially, intentionally, reason, cause, circumstances, the late, therefore, consequently";
const char kanji_ms8131[] = "undress, removing, escape from, get rid of, be left out, take off";
const char kanji_ms967A[] = "precipitous, inaccessible place, impregnable position, steep place, sharp eyes";
const char kanji_ms97FF[] = "echo, sound, resound, ring, vibrate";
const char kanji_ms9F3B[] = "nose, snout";
const char kanji_ms5C48[] = "yield, bend, flinch, submit";
const char kanji_ms793E[] = "company, firm, office, association, shrine";
const char kanji_ms4E08[] = "length, ten shaku, measure, Mr., Ms., height, stature, all (one has), only, that's all, merely";
const char kanji_ms5305[] = "wrap, pack up, cover, conceal";
const char kanji_ms6DF7[] = "mix, blend, confuse";
const char kanji_ms8FCE[] = "welcome, meet, greet";
const char kanji_ms4E38[] = "round, full (month), perfection, -ship, pills, make round, roll up, curl up, seduce, explain away";
const char kanji_ms4E5D[] = "nine";
const char kanji_ms5171[] = "together, both, neither, all, and, alike, with";
const char kanji_ms5343[] = "thousand";
const char kanji_ms5E03[] = "linen, cloth, spread, distribute";
const char kanji_ms8352[] = "laid waste, rough, rude, wild";
const char kanji_ms5E2B[] = "expert, teacher, master, model, exemplar, army (incl. counter), war";
const char kanji_ms5E2D[] = "seat, mat, occasion, place";
const char kanji_ms50CD[] = "work, (kokuji)";
const char kanji_ms7D0D[] = "settlement, obtain, reap, pay, supply, store";
const char kanji_ms7A0B[] = "extent, degree, law, formula, distance, limits, amount";
const char kanji_ms6975[] = "poles, settlement, conclusion, end, highest rank, electric poles, very, extremely, most, highly, 10**48";
const char kanji_ms66F2[] = "bend, music, melody, composition, pleasure, injustice, fault, curve, crooked, perverse, lean";
const char kanji_ms901F[] = "quick, fast";
const char kanji_ms63E1[] = "grip, hold, mould sushi, bribe";
const char kanji_ms967D[] = "sunshine, yang principle, positive, male, heaven, daytime";
const char kanji_ms66B4[] = "outburst, rave, fret, force, violence, cruelty, outrage";
const char kanji_ms53F7[] = "nickname, number, item, title, pseudonym, name, call";
const char kanji_ms7A4D[] = "volume, product (x*y), acreage, contents, pile up, stack, load, amass";
const char kanji_ms53EB[] = "shout, exclaim, yell";
const char kanji_ms80B2[] = "bring up, grow up, raise, rear";
const char kanji_ms5EAD[] = "courtyard, garden, yard";
const char kanji_ms9AA8[] = "skeleton, bone, remains, frame";
const char kanji_ms7A93[] = "window, pane";
const char kanji_ms6575[] = "enemy, foe, opponent";
const char kanji_ms56E3[] = "group, association";
const char kanji_ms7523[] = "products, bear, give birth, yield, childbirth, native, property";
const char kanji_ms602A[] = "suspicious, mystery, apparition";
const char kanji_ms76AE[] = "pelt, skin, hide, leather, skin radical (no. 107)";
const char kanji_ms7E01[] = "affinity, relation, connection, edge, border, verge, brink";
const char kanji_ms6368[] = "discard, throw away, abandon, resign, reject, sacrifice";
const char kanji_ms5BBF[] = "inn, lodging, relay station, dwell, lodge, be pregnant, home, dwelling";
const char kanji_ms67C4[] = "design, pattern, build, nature, character, handle, crank, grip, knob, shaft";
const char kanji_ms90AA[] = "wicked, injustice, wrong";
const char kanji_ms53CE[] = "income, obtain, reap, pay, supply, store";
const char kanji_ms8001[] = "old man, old age, grow old";
const char kanji_ms6CBB[] = "reign, be at peace, calm down, subdue, quell, govt, cure, heal, rule, conserve";
const char kanji_ms53E5[] = "phrase, clause, sentence, passage, paragraph, counter for haiku";
const char kanji_ms7FD2[] = "learn";
const char kanji_ms8FEB[] = "urge, force, imminent, spur on";
const char kanji_ms6771[] = "east";
const char kanji_ms5DE5[] = "craft, construction, katakana e radical (no. 48)";
const char kanji_ms91CF[] = "quantity, measure, weight, amount, consider, estimate, surmise";
const char kanji_ms8CAC[] = "blame, condemn, censure";
const char kanji_ms7B49[] = "etc., and so forth, class (first), quality, equal, similar";
const char kanji_ms76DB[] = "boom, prosper, copulate";
const char kanji_ms7C21[] = "simplicity, brevity";
const char kanji_ms6BD4[] = "compare, race, ratio, Philippines";
const char kanji_ms4E95[] = "well, well crib, town, community";
const char kanji_ms6620[] = "reflect, reflection, projection";
const char kanji_ms52D9[] = "task, duties";
const char kanji_ms5F93[] = "accompany, obey, submit to, comply, follow, secondary, incidental, subordinate";
const char kanji_ms4E0E[] = "bestow, participate in, give, award, impart, provide, cause, gift, godsend";
const char kanji_ms75B2[] = "exhausted, tire, weary";
const char kanji_ms8A2A[] = "call on, visit, look up, offer sympathy";
const char kanji_ms7BC0[] = "node, season, period, occasion, verse, clause, stanza, honor, joint, knuckle, knob, knot, tune, melody";
const char kanji_ms5410[] = "spit, vomit, belch, confess, tell (lies)";
const char kanji_ms679A[] = "sheet of..., counter for flat thin objects or sheets";
const char kanji_ms6CE2[] = "waves, billows, Poland";
const char kanji_ms67D3[] = "dye, color, paint, stain, print";
const char kanji_ms5C04[] = "shoot, shine into, onto, archery";
const char kanji_ms65C5[] = "trip, travel";
const char kanji_ms9045[] = "slow, late, back, later";
const char kanji_ms541B[] = "mister, you, ruler, male name suffix";
const char kanji_ms8A98[] = "entice, lead, tempt, invite, ask, call for, seduce, allure";
const char kanji_ms7559[] = "detain, fasten, halt, stop";
const char kanji_ms53B3[] = "stern, strictness, severity, rigidity";
const char kanji_ms6D17[] = "wash, inquire into, probe";
const char kanji_ms6B20[] = "lack, gap, fail, yawning radical (no. 76)";
const char kanji_ms6577[] = "spread, pave, sit, promulgate";
const char kanji_ms8077[] = "post, employment, work";
const char kanji_ms5BB3[] = "harm, injury";
const char kanji_ms5897[] = "increase, add, augment, gain, promote";
const char kanji_ms8DE1[] = "tracks, mark, print, impression";
const char kanji_ms5883[] = "boundary, border, region";
const char kanji_ms8F2A[] = "wheel, ring, circle, link, loop, counter for wheels and flowers";
const char kanji_ms7F6A[] = "guilt, sin, crime, fault, blame, offense";
const char kanji_ms6162[] = "ridicule, laziness";
const char kanji_ms5FA9[] = "restore, return to, revert, resume";
const char kanji_ms501F[] = "borrow, rent";
const char kanji_ms4E45[] = "long time, old story";
const char kanji_ms5A18[] = "daughter, girl";
const char kanji_ms51E6[] = "dispose, manage, deal with, sentence, condemn, act, behave, place";
const char kanji_ms6EC5[] = "destroy, ruin, overthrow, perish";
const char kanji_ms9664[] = "exclude, division (x/3), remove, abolish, cancel, except";
const char kanji_ms500B[] = "individual, counter for articles";
const char kanji_ms99C6[] = "drive, run, gallop, advance, inspire, impel";
const char kanji_ms7DD2[] = "thong, beginning, inception, end, cord, strap, mental or emotional state";
const char kanji_ms9244[] = "iron";
const char kanji_ms61B6[] = "recollection, think, remember";
const char kanji_ms72C2[] = "lunatic, insane, crazy, confuse";
const char kanji_ms6674[] = "clear up";
const char kanji_ms6297[] = "confront, resist, defy, oppose";
const char kanji_ms62E0[] = "foothold, based on, follow, therefore";
const char kanji_ms767B[] = "ascend, climb up";
const char kanji_ms56E0[] = "cause, factor, be associated with, depend on, be limited to";
const char kanji_ms5100[] = "ceremony, rule, affair, case, a matter";
const char kanji_ms677F[] = "plank, board, plate, stage";
const char kanji_ms7518[] = "sweet, coax, pamper, be content, sugary";
const char kanji_ms6557[] = "failure, defeat, reversal";
const char kanji_ms7DF4[] = "practice, gloss, train, drill, polish, refine";
const char kanji_ms578B[] = "mould, type, model";
const char kanji_ms4E89[] = "contend, dispute, argue";
const char kanji_ms984D[] = "forehead, tablet, plaque, framed picture, sum, amount, volume";
const char kanji_ms9670[] = "shade, yin, negative, sex organs, secret, shadow";
const char kanji_ms6628[] = "yesterday, previous";
const char kanji_ms8B1D[] = "apologize, thank, refuse";
const char kanji_ms8B66[] = "admonish, commandment";
const char kanji_ms96A3[] = "neighboring";
const char kanji_ms5F01[] = "valve, petal, braid, speech, dialect, discrimination, dispose of, distinguish, conical cap";
const char kanji_ms5217[] = "file, row, rank, tier, column";
const char kanji_ms6065[] = "shame, dishonor";
const char kanji_ms6551[] = "salvation, save, help, rescue, reclaim";
const char kanji_ms666E[] = "universal, wide(ly), generally, Prussia";
const char kanji_ms6B6F[] = "tooth, cog";
const char kanji_ms50BE[] = "lean, incline, tilt, trend, wane, sink, ruin, bias";
const char kanji_ms7530[] = "rice field, rice paddy";
const char kanji_ms907F[] = "evade, avoid, avert, ward off, shirk, shun";
const char kanji_ms9806[] = "obey, order, turn, right, docility, occasion";
const char kanji_ms8CB4[] = "precious, value, prize, esteem, honor";
const char kanji_ms8A66[] = "test, try, attempt, experiment, ordeal";
const char kanji_ms6A29[] = "authority, power, rights";
const char kanji_ms6574[] = "organize, arranging, tune, tone, meter, key (music)";
const char kanji_ms8863[] = "garment, clothes, dressing";
const char kanji_ms63FA[] = "swing, shake, sway, rock, tremble, vibrate";
const char kanji_ms539A[] = "thick, heavy, rich, kind, cordial, brazen, shameless";
const char kanji_ms6163[] = "accustomed, get used to, become experienced";
const char kanji_ms7D14[] = "genuine, purity, innocence, net (profit)";
const char kanji_ms616E[] = "prudence, thought, concern, consider, deliberate, fear";
const char kanji_ms5C3E[] = "tail, end, counter for fish, lower slope of mountain";
const char kanji_ms8A70[] = "packed, close, pressed, reprove, rebuke, blame";
const char kanji_ms6D99[] = "tears, sympathy";
const char kanji_ms63CF[] = "sketch, compose, write, draw, paint";
const char kanji_ms5426[] = "negate, no, noes, refuse, decline, deny";
const char kanji_ms6669[] = "nightfall, night";
const char kanji_ms5263[] = "sabre, sword, blade, clock hand";
const char kanji_ms57CB[] = "bury, be filled up, embedded";
const char kanji_ms8B77[] = "safeguard, protect";
const char kanji_ms9280[] = "silver";
const char kanji_ms5E97[] = "store, shop";
const char kanji_ms4F0F[] = "prostrated, bend down, bow, cover, lay (pipes)";
const char kanji_ms5802[] = "public chamber, hall";
const char kanji_ms5DDD[] = "stream, river, river or three-stroke river radical (no. 47)";
const char kanji_ms8857[] = "boulevard, street, town";
const char kanji_ms4EA1[] = "deceased, the late, dying, perish";
const char kanji_ms6BD2[] = "poison, virus, venom, germ, harm, injury, spite";
const char kanji_ms5186[] = "circle, yen, round";
const char kanji_ms5FD7[] = "intention, plan, resolve, aspire, motive, hopes, shilling";
const char kanji_ms8972[] = "attack, advance on, succeed to, pile, heap";
const char kanji_ms4FBF[] = "convenience, facility, excrement, feces, letter, chance";
const char kanji_ms8AB0[] = "who, someone, somebody";
const char kanji_ms820C[] = "tongue, reed, clapper";
const char kanji_ms5024[] = "price, cost, value";
const char kanji_ms6E1B[] = "dwindle, decrease, reduce, decline, curtail, get hungry";
const char kanji_ms627F[] = "acquiesce, hear, listen to, be informed, receive";
const char kanji_ms63D0[] = "propose, take along, carry in hand";
const char kanji_ms9069[] = "suitable, occasional, rare, qualified, capable";
const char kanji_ms52B9[] = "merit, efficacy, efficiency, benefit";
const char kanji_ms5EAB[] = "warehouse, storehouse";
const char kanji_ms7A74[] = "hole, aperture, slit, cave, den";
const char kanji_ms897F[] = "west, Spain";
const char kanji_ms85AC[] = "medicine, chemical, enamel, gunpowder, benefit";
const char kanji_ms609F[] = "enlightenment, perceive, discern, realize, understand";
const char kanji_ms96FB[] = "electricity";
const char kanji_ms7FBD[] = "feathers, counter for birds, rabbits";
const char kanji_ms639B[] = "hang, suspend, depend, arrive at, tax, pour";
const char kanji_ms5317[] = "north";
const char kanji_ms6E29[] = "warm";
const char kanji_ms9152[] = "sake, alcohol";
const char kanji_ms5C4A[] = "deliver, reach, arrive, report, notify, forward";
const char kanji_ms5727[] = "pressure, push, overwhelm, oppress, dominate";
const char kanji_ms6E96[] = "semi-, correspond to, proportionate to, conform, imitate";
const char kanji_ms5E02[] = "market, city, town";
const char kanji_ms5546[] = "make a deal, selling, dealing in, merchant";
const char kanji_ms7389[] = "jewel, ball";
const char kanji_ms5F3E[] = "bullet, twang, flip, snap";
const char kanji_ms4FA1[] = "value, price";
const char kanji_ms4E92[] = "mutually, reciprocally, together";
const char kanji_ms5FA1[] = "honorable, manipulate, govern";
const char kanji_ms623B[] = "re-, return, revert, resume, restore, go backwards";
const char kanji_ms6C11[] = "people, nation, subjects";
const char kanji_ms6A21[] = "imitation, copy, mock";
const char kanji_ms4F38[] = "expand, stretch, extend, lengthen, increase";
const char kanji_ms96E8[] = "rain";
const char kanji_ms888B[] = "sack, bag, pouch";
const char kanji_ms5BD2[] = "cold";
const char kanji_ms8377[] = "baggage, shoulder-pole load, bear (a burden), shoulder (a gun), load, cargo, freight";
const char kanji_ms6C57[] = "sweat, perspire";
const char kanji_ms6C5A[] = "dirty, pollute, disgrace, rape, defile";
const char kanji_ms4EF0[] = "face-up, look up, depend, seek, respect, revere, drink, take";
const char kanji_ms9632[] = "ward off, defend, protect, resist";
const char kanji_ms8A33[] = "translate, reason, circumstance, case";
const char kanji_ms4FEE[] = "discipline, conduct oneself well, study, master";
const char kanji_ms6761[] = "article, clause, counter for articles, clauses, paragraphs, etc., twig, item, stripe, streak";
const char kanji_ms7159[] = "smoke";
const char kanji_ms5A66[] = "lady, woman, wife, bride";
const char kanji_ms9732[] = "dew, tears, expose, Russia";
const char kanji_ms4EE4[] = "orders, laws, command, decree, good";
const char kanji_ms6750[] = "lumber, log, timber, wood, materials, ingredients, talent";
const char kanji_ms7D75[] = "picture, drawing, painting, sketch";
const char kanji_ms7532[] = "armor, high (voice), A grade, first class, former, instep, carapace";
const char kanji_ms99C4[] = "burdensome, pack horse, horse load, send by horse, trivial, worthless";
const char kanji_ms7BA1[] = "pipe, tube, wind instrument, drunken talk, control, jurisdiction";
const char kanji_ms5230[] = "arrival, proceed, reach, attain, result in";
const char kanji_ms81F3[] = "climax, arrive, proceed, reach, attain, result in";
const char kanji_ms6821[] = "exam, school, printing, proof, correction";
const char kanji_ms5A01[] = "intimidate, dignity, majesty, menace, threaten";
const char kanji_ms71C3[] = "burn, blaze, glow";
const char kanji_ms93E1[] = "mirror, speculum, barrel-head, round rice-cake offering";
const char kanji_ms68D2[] = "rod, stick, cane, pole, club, line";
const char kanji_ms7DCA[] = "tense, solid, hard, reliable, tight";
const char kanji_ms8CC7[] = "assets, resources, capital, funds, data, be conducive to, contribute to";
const char kanji_ms9685[] = "corner, nook";
const char kanji_ms5348[] = "noon, sign of the horse, 11AM-1PM, seventh sign of Chinese zodiac";
const char kanji_ms9CE5[] = "bird, chicken";
const char kanji_ms5B98[] = "bureaucrat, the government, organ";
const char kanji_ms9EC4[] = "yellow";
const char kanji_ms5144[] = "elder brother, big brother";
const char kanji_ms8A55[] = "evaluate, criticism, comment";
const char kanji_ms95C7[] = "get dark, gloom, disorder";
const char kanji_ms66FF[] = "exchange, spare, substitute, per-";
const char kanji_ms60A9[] = "trouble, worry, in pain, distress, illness";
const char kanji_ms6B4C[] = "song, sing";
const char kanji_ms6F14[] = "performance, act, play, render, stage";
const char kanji_ms7BB1[] = "box, chest, case, bin, railway car";
const char kanji_ms73CD[] = "rare, curious, strange";
const char kanji_ms676F[] = "counter for cupfuls, wine glass, glass, toast";
const char kanji_ms6625[] = "springtime, spring (season)";
const char kanji_ms6D74[] = "bathe, be favored with, bask in";
const char kanji_ms6280[] = "skill, art, craft, ability, feat, performance, vocation, arts";
const char kanji_ms92ED[] = "pointed, sharpness, edge, weapon, sharp, violent";
const char kanji_ms9662[] = "Inst., institution, temple, mansion, school";
const char kanji_ms6094[] = "repent, regret";
const char kanji_ms604B[] = "romance, in love, yearn for, miss, darling";
const char kanji_ms4E01[] = "street, ward, town, counter for guns, tools, leaves or cakes of something, even number, 4th calendar sign";
const char kanji_ms590F[] = "summer";
const char kanji_ms661F[] = "star, spot, dot, mark";
const char kanji_ms5199[] = "copy, be photographed, describe";
const char kanji_ms6CB9[] = "oil, fat";
const char kanji_ms8F1D[] = "radiance, shine, sparkle, gleam, twinkle";
const char kanji_ms83EF[] = "splendor, flower, petal, shine, luster, ostentatious, showy, gay, gorgeous";
const char kanji_ms596A[] = "rob, take by force, snatch away, dispossess, plunder, usurp";
const char kanji_ms7FA4[] = "flock, group, crowd, herd, swarm, cluster";
const char kanji_ms8A2D[] = "establishment, provision, prepare";
const char kanji_ms753A[] = "town, village, block, street";
const char kanji_ms7981[] = "prohibition, ban, forbid";
const char kanji_ms98FE[] = "decorate, ornament, adorn, embellish";
const char kanji_ms5712[] = "park, garden, yard, farm";
const char kanji_ms88C2[] = "split, rend, tear";
const char kanji_ms9154[] = "drunk, feel sick, poisoned, elated, spellbound";
const char kanji_ms982C[] = "cheeks, jaw";
const char kanji_ms6355[] = "catch, capture";
const char kanji_ms7D1A[] = "class, rank, grade";
const char kanji_ms798F[] = "blessing, fortune, luck, wealth";
const char kanji_ms5C5E[] = "belong, genus, subordinate official, affiliated";
const char kanji_ms7B97[] = "calculate, divining, number, abacus, probability";
const char kanji_ms6C38[] = "eternity, long, lengthy";
const char kanji_ms9818[] = "jurisdiction, dominion, territory, fief, reign";
const char kanji_ms5065[] = "healthy, health, strength, persistence";
const char kanji_ms6E08[] = "settle (debt, etc.), relieve (burden), finish, come to an end, excusable, need not";
const char kanji_ms70BA[] = "do, change, make, benefit, welfare, be of use, reach to, try, practice, cost, serve as, good, advantage, as a result of";
const char kanji_ms533A[] = "ward, district";
const char kanji_ms9999[] = "incense, smell, perfume";
const char kanji_ms62C5[] = "shouldering, carry, raise, bear";
const char kanji_ms8F9E[] = "resign, word, term, expression";
const char kanji_ms5D29[] = "crumble, die, demolish, level";
const char kanji_ms773A[] = "stare, watch, look at, see, scrutinize";
const char kanji_ms88FD[] = "made in..., manufacture";
const char kanji_ms6B74[] = "curriculum, continuation, passage of time";
const char kanji_ms6B66[] = "warrior, military, chivalry, arms";
const char kanji_ms529F[] = "achievement, merits, success, honor, credit";
const char kanji_ms885D[] = "collide, brunt, highway, opposition (astronomy), thrust, pierce, stab, prick";
const char kanji_ms52C7[] = "courage, cheer up, be in high spirits, bravery, heroism";
const char kanji_ms6E05[] = "pure, purify, cleanse, exorcise, Manchu dynasty";
const char kanji_ms656C[] = "awe, respect, honor, revere";
const char kanji_ms866B[] = "insect, bug, temper";
const char kanji_ms72AF[] = "crime, sin, offense";
const char kanji_ms63DB[] = "interchange, period, change, convert, replace, renew";
const char kanji_ms7D61[] = "entwine, coil around, get caught in";
const char kanji_ms738B[] = "king, rule, magnate";
const char kanji_ms53CA[] = "reach out, exert, exercise, cause";
const char kanji_ms62DB[] = "beckon, invite, summon, engage";
const char kanji_ms990A[] = "foster, bring up, rear, develop, nurture";
const char kanji_ms72AC[] = "dog";
const char kanji_ms5357[] = "south";
const char kanji_ms9802[] = "place on the head, receive, top of head, top, summit, peak";
const char kanji_ms808C[] = "texture, skin, body, grain";
const char kanji_ms7DE8[] = "compilation, knit, plait, braid, twist, editing, completed poem, part of a book";
const char kanji_ms618E[] = "hate, detest";
const char kanji_ms59BB[] = "wife, spouse";
const char kanji_ms9707[] = "quake, shake, tremble, quiver, shiver";
const char kanji_ms61D0[] = "feelings, heart, yearn, miss someone, become attached to, bosom, breast, pocket";
const char kanji_ms72ED[] = "cramped, narrow, contract, tight";
const char kanji_ms969C[] = "hinder, hurt, harm";
const char kanji_ms8CB8[] = "lend";
const char kanji_ms500D[] = "double, twice, times, fold";
const char kanji_ms9803[] = "time, about, toward";
const char kanji_ms596E[] = "stirred up, be invigorated, flourish";
const char kanji_ms5C06[] = "leader, commander, general, admiral, or, and again, soon, from now on, just about";
const char kanji_ms96F2[] = "cloud";
const char kanji_ms6CC1[] = "condition, situation";
const char kanji_ms6613[] = "easy, ready to, simple, fortune-telling, divination";
const char kanji_ms706F[] = "lamp, a light, light, counter for lights";
const char kanji_ms5C02[] = "specialty, exclusive, mainly, solely";
const char kanji_ms6FC3[] = "concentrated, thick, dark, undiluted";
const char kanji_ms63A8[] = "conjecture, infer, guess, suppose, support, push (for)";
const char kanji_ms7FCC[] = "the following, next";
const char kanji_ms5A5A[] = "marriage";
const char kanji_ms5E7C[] = "infancy, childhood";
const char kanji_ms4EEE[] = "sham, temporary, interim, assumed (name), informal";
const char kanji_ms6271[] = "handle, entertain, thresh, strip";
const char kanji_ms5B85[] = "home, house, residence, our house, my husband";
const char kanji_ms8F9B[] = "spicy, bitter, hot, acrid";
const char kanji_ms54C0[] = "pathetic, grief, sorrow, pathos, pity, sympathize";
const char kanji_ms542B[] = "contain, include, hold in the mouth, bear in mind, understand, cherish";
const char kanji_ms7709[] = "eyebrow";
const char kanji_ms62FE[] = "pick up, gather, find, go on foot, ten";
const char kanji_ms5F1F[] = "younger brother, faithful service to elders";
const char kanji_ms6319[] = "raise, plan, project, behavior, actions";
const char kanji_ms8133[] = "brain, memory";
const char kanji_ms5197[] = "superfluous, uselessness";
const char kanji_ms9928[] = "building, mansion, large building, palace";
const char kanji_ms5C0E[] = "guidance, leading, conduct, usher";
const char kanji_ms8AA4[] = "mistake, err, do wrong, mislead";
const char kanji_ms6804[] = "flourish, prosperity, honor, glory, splendor";
const char kanji_ms623F[] = "tassel, tuft, fringe, bunch, lock (hair), segment (orange), house, room";
const char kanji_ms691C[] = "examination, investigate";
const char kanji_ms57F7[] = "tenacious, take hold, grasp, take to heart";
const char kanji_ms52D8[] = "intuition, perception, check, compare, sixth sense";
const char kanji_ms90CE[] = "son, counter for sons";
const char kanji_ms5C3B[] = "buttocks, hips, butt, rear";
const char kanji_ms508D[] = "bystander, side, besides, while, nearby, third person";
const char kanji_ms58CA[] = "demolition, break, destroy";
const char kanji_ms7D05[] = "crimson, deep red";
const char kanji_ms7DCF[] = "general, whole, all, full, total";
const char kanji_ms95D8[] = "fight, war";
const char kanji_ms5C3D[] = "exhaust, use up, run out of, deplete, befriend, serve";
const char kanji_ms8DDD[] = "long-distance, spur, fetlock";
const char kanji_ms907A[] = "bequeath, leave behind, reserve";
const char kanji_ms4E7E[] = "drought, dry, dessicate, drink up, heaven, emperor";
const char kanji_ms7E2E[] = "shrink, contract, shrivel, wrinkle, reduce";
const char kanji_ms7802[] = "sand";
const char kanji_ms898F[] = "standard, measure";
const char kanji_ms88D5[] = "abundant, rich, fertile";
const char kanji_ms79D1[] = "department, course, section";
const char kanji_ms819D[] = "knee, lap";
const char kanji_ms5DE8[] = "gigantic, big, large, great";
const char kanji_ms70C8[] = "ardent, violent, vehement, furious, severe, extreme";
const char kanji_ms5ECA[] = "corridor, hall, tower";
const char kanji_ms5C55[] = "unfold, expand";
const char kanji_ms5373[] = "instant, namely, as is, conform, agree, adapt";
const char kanji_ms76D7[] = "steal, rob, pilfer";
const char kanji_ms62B5[] = "resist, reach, touch";
const char kanji_ms5E72[] = "dry, parch, ebb, recede, interfere, intercede";
const char kanji_ms653B[] = "aggression, attack, criticize, polish";
const char kanji_ms8CA1[] = "property, money, wealth, assets";
const char kanji_ms5076[] = "accidentally, even number, couple, man & wife, same kind";
const char kanji_ms82B8[] = "technique, art, craft, performance, acting, trick, stunt";
const char kanji_ms79F0[] = "appellation, praise, admire, name, title, fame";
const char kanji_ms7B46[] = "writing brush, writing, painting brush, handwriting";
const char kanji_ms7E54[] = "weave, fabric";
const char kanji_ms9BAE[] = "fresh, vivid, clear, brilliant, Korea";
const char kanji_ms533B[] = "doctor, medicine";
const char kanji_ms9031[] = "week";
const char kanji_ms5C01[] = "seal, closing";
const char kanji_ms8A87[] = "boast, be proud, pride, triumphantly";
const char kanji_ms9E7F[] = "deer";
const char kanji_ms5145[] = "allot, fill";
const char kanji_ms5FCD[] = "endure, bear, put up with, conceal, secrete, spy, sneak";
const char kanji_ms7D66[] = "salary, wage, gift, allow, grant, bestow on";
const char kanji_ms52AA[] = "toil, diligent, as much as possible";
const char kanji_ms8E8D[] = "leap, dance, skip";
const char kanji_ms5618[] = "lie, falsehood";
const char kanji_ms8CBB[] = "expense, cost, spend, consume, waste";
const char kanji_ms9F62[] = "age";
const char kanji_ms5404[] = "each, every, either";
const char kanji_ms8239[] = "ship, boat";
const char kanji_ms91DD[] = "needle, pin, staple, stinger";
const char kanji_ms91C8[] = "explanation";
const char kanji_ms8907[] = "duplicate, double, compound, multiple";
const char kanji_ms8DA3[] = "purport, gist, elegance, interest, proceed to, tend, become";
const char kanji_ms7DE0[] = "tighten, tie, shut, lock, fasten";
const char kanji_ms624D[] = "genius, years old, cubic shaku";
const char kanji_ms55B6[] = "camp, perform, build, conduct (business)";
const char kanji_ms81ED[] = "stinking, ill-smelling, suspicious looking, odor, savor, fragrance, be fragrant, stink, glow, be bright";
const char kanji_ms7384[] = "mysterious, occultness, black, deep, profound";
const char kanji_ms81F4[] = "doth, do, send, forward, cause, exert, incur, engage";
const char kanji_ms9811[] = "stubborn, foolish, firmly";
const char kanji_ms640D[] = "damage, loss, disadvantage, hurt, injure";
const char kanji_ms7387[] = "ratio, rate, proportion, %, factor, lead, spearhead, command";
const char kanji_ms6075[] = "favor, blessing, grace, kindness";
const char kanji_ms88AB[] = "incur, cover, veil, brood over, shelter, wear, put on, be exposed (film), receiving";
const char kanji_ms6B53[] = "delight, joy";
const char kanji_ms7D99[] = "inherit, succeed, continue, patch, graft (tree)";
const char kanji_ms7126[] = "char, hurry, impatient, irritate, burn, scorch, singe";
const char kanji_ms6687[] = "spare time, rest, leisure, time, leave of absence";
const char kanji_ms820E[] = "cottage, inn, hut, house, mansion";
const char kanji_ms5CF6[] = "island";
const char kanji_ms6751[] = "village, town";
const char kanji_ms57FA[] = "fundamentals, radical (chem), counter for machines, foundation";
const char kanji_ms8010[] = "-proof, enduring";
const char kanji_ms5507[] = "lips";
const char kanji_ms5360[] = "fortune-telling, divining, forecasting, occupy, hold, have, get, take";
const char kanji_ms5E0C[] = "hope, beg, request, pray, beseech, Greece, dilute (acid), rare, few, phenomenal";
const char kanji_ms9063[] = "dispatch, despatch, send, give, donate, do, undertake";
const char kanji_ms6CA2[] = "swamp, marsh, brilliance, grace";
const char kanji_ms865A[] = "void, emptiness, unpreparedness, crack, fissure, untruth";
const char kanji_ms8F09[] = "ride, board, get on, place, spread, 10**44, record, publish";
const char kanji_ms5354[] = "co-, cooperation";
const char kanji_ms66F4[] = "grow late, night watch, sit up late, of course, renew, renovate, again, more and more, further";
const char kanji_ms81D3[] = "entrails, viscera, bowels";
const char kanji_ms6CCA[] = "overnight stay, put up at, ride at anchor";
const char kanji_ms7686[] = "all, everything";
const char kanji_ms5F92[] = "on foot, junior, emptiness, vanity, futility, uselessness, ephemeral thing, gang, set, party, people";
const char kanji_ms4E86[] = "complete, finish";
const char kanji_ms53E9[] = "strike, beat, kow tow, hit, thrash, criticize";
const char kanji_ms52E4[] = "diligence, become employed, serve";
const char kanji_ms8CA7[] = "poverty, poor";
const char kanji_ms5857[] = "paint, plaster, daub, smear, coating";
const char kanji_ms8535[] = "storehouse, hide, own, have, possess";
const char kanji_ms9332[] = "record";
const char kanji_ms7CF8[] = "thread";
const char kanji_ms7248[] = "printing block, printing plate, edition, impression, label";
const char kanji_ms7D39[] = "introduce, inherit, help";
const char kanji_ms7AE0[] = "badge, chapter, composition, poem, design";
const char kanji_ms5DF1[] = "self";
const char kanji_ms77E2[] = "dart, arrow";
const char kanji_ms822C[] = "carrier, carry, all, general, sort, kind";
const char kanji_ms67D4[] = "tender, weakness, gentleness, softness";
const char kanji_ms61F8[] = "state of suspension, hang, depend, consult, distant, far apart";
const char kanji_ms8ECD[] = "army, force, troops, war, battle";
const char kanji_ms5584[] = "virtuous, good, goodness";
const char kanji_ms5974[] = "guy, slave, manservant, fellow";
const char kanji_ms6CE5[] = "mud, mire, adhere to, be attached to";
const char kanji_ms7E70[] = "winding, reel, spin, turn (pages), look up, refer to";
const char kanji_ms6ED1[] = "slippery, slide, slip, fail exam";
const char kanji_ms60DC[] = "pity, be sparing of, frugal, stingy, regret";
const char kanji_ms9177[] = "cruel, severe, atrocious, unjust";
const char kanji_ms690D[] = "plant";
const char kanji_ms67F1[] = "pillar, post, cylinder, support";
const char kanji_ms770B[] = "watch over, see";
const char kanji_ms5C0A[] = "revered, valuable, precious, noble, exalted";
const char kanji_ms811A[] = "skids, leg, undercarriage, lower part, base";
const char kanji_ms5EF6[] = "prolong, stretching";
const char kanji_ms62CD[] = "clap, beat (music)";
const char kanji_ms82F1[] = "England, English, hero, outstanding, calyx";
const char kanji_ms6E6F[] = "hot water, bath, hot spring";
const char kanji_ms5446[] = "be amazed, disgusted, shocked";
const char kanji_ms5FB4[] = "indications, sign, omen, symptom, collect, seek, refer to, question";
const char kanji_ms574A[] = "boy, priest's residence, priest";
const char kanji_ms67FB[] = "investigate";
const char kanji_ms6D45[] = "shallow, superficial, frivolous, wretched, shameful";
const char kanji_ms8C4A[] = "bountiful, excellent, rich";
const char kanji_ms505C[] = "halt, stopping";
const char kanji_ms5B9D[] = "treasure, wealth, valuables";
const char kanji_ms7070[] = "ashes, puckery juice, cremate";
const char kanji_ms552F[] = "solely, only, merely, simply";
const char kanji_ms5FD9[] = "busy, occupied, restless";
const char kanji_ms98EF[] = "meal, boiled rice";
const char kanji_ms6E2C[] = "fathom, plan, scheme, measure";
const char kanji_ms900F[] = "transparent, permeate, filter, penetrate";
const char kanji_ms63DA[] = "raise, elevate, hoist, praise, extol, fry in deep fat";
const char kanji_ms5E45[] = "hanging scroll, width";
const char kanji_ms731B[] = "fierce, rave, rush, become furious, wildness, strength";
const char kanji_ms8C37[] = "valley";
const char kanji_ms5FE0[] = "loyalty, fidelity, faithfulness";
const char kanji_ms5287[] = "drama, play";
const char kanji_ms8D85[] = "transcend, super-, ultra-";
const char kanji_ms8C6A[] = "overpowering, great, powerful, excelling, Australia";
const char kanji_ms7DD1[] = "green";
const char kanji_ms653F[] = "politics, government";
const char kanji_ms53F2[] = "history, chronicle";
const char kanji_ms592E[] = "center, middle";
const char kanji_ms5C64[] = "stratum, social class, layer, story, floor";
const char kanji_ms5BCC[] = "wealth, enrich, abundant";
const char kanji_ms6905[] = "chair";
const char kanji_ms5BA3[] = "proclaim, say, announce";
const char kanji_ms5302[] = "fragrant, stink, glow, insinuate, (kokuji)";
const char kanji_ms5642[] = "rumor, gossip, hearsay";
const char kanji_ms6DFB[] = "annexed, accompany, marry, suit, meet, satisfy, attach, append, garnish, imitate";
const char kanji_ms8107[] = "armpit, the other way, another place, flank, supporting role";
const char kanji_ms8A34[] = "accusation, sue, complain of pain, appeal to";
const char kanji_ms6A4B[] = "bridge";
const char kanji_ms5F80[] = "journey, travel, chase away, let go, going, before, formerly";
const char kanji_ms6D0B[] = "ocean, sea, foreign, Western style";
const char kanji_ms9B5A[] = "fish";
const char kanji_ms6212[] = "commandment";
const char kanji_ms53F8[] = "director, official, govt office, rule, administer";
const char kanji_ms7D71[] = "overall, relationship, ruling, governing";
const char kanji_ms5150[] = "newborn babe, child, young of animals";
const char kanji_ms5FB9[] = "penetrate, clear, pierce, strike home, sit up (all night)";
const char kanji_ms51AC[] = "winter";
const char kanji_ms8A73[] = "detailed, full, minute, accurate, well-informed";
const char kanji_ms68EE[] = "forest, woods";
const char kanji_ms611A[] = "foolish, folly, absurdity, stupid";
const char kanji_ms7B56[] = "scheme, plan, policy, step, means";
const char kanji_ms79CB[] = "autumn";
const char kanji_ms8846[] = "masses, great numbers, multitude, populace";
const char kanji_ms6DE1[] = "thin, faint, pale, fleeting";
const char kanji_ms885B[] = "defense, protection";
const char kanji_ms9B45[] = "fascination, charm, bewitch";
const char kanji_ms5B99[] = "mid-air, air, space, sky, memorization, interval of time";
const char kanji_ms7948[] = "pray, wish";
const char kanji_ms88DC[] = "supplement, supply, make good, offset, compensate, assistant, learner";
const char kanji_ms6383[] = "sweep, brush";
const char kanji_ms7A4F[] = "calm, quiet, moderation";
const char kanji_ms64CD[] = "maneuver, manipulate, operate, steer, chastity, virginity, fidelity";
const char kanji_ms6328[] = "approach, draw near, push open";
const char kanji_ms76E3[] = "oversee, official, govt office, rule, administer";
const char kanji_ms5782[] = "droop, suspend, hang, slouch";
const char kanji_ms970A[] = "spirits, soul";
const char kanji_ms5DE1[] = "patrol, go around, circumference";
const char kanji_ms62F6[] = "be imminent, draw close";
const char kanji_ms5E55[] = "curtain, bunting, act of play";
const char kanji_ms5606[] = "sigh, lament, moan, grieve, sigh of admiration";
const char kanji_ms5175[] = "soldier, private, troops, army, warfare, strategy, tactics";
const char kanji_ms6607[] = "rise up";
const char kanji_ms5019[] = "climate, season, weather, wait for, expect";
const char kanji_ms7BC9[] = "fabricate, build, construct";
const char kanji_ms7814[] = "polish, study of, sharpen";
const char kanji_ms6797[] = "grove, forest";
const char kanji_ms4F9D[] = "reliant, depend on, consequently, therefore, due to";
const char kanji_ms5247[] = "rule, law, follow, based on, model after";
const char kanji_ms5BF8[] = "measurement, tenth of a shaku, a little, small";
const char kanji_ms5BAE[] = "Shinto shrine, constellations, palace, princess";
const char kanji_ms68DA[] = "shelf, ledge, rack, mount, mantle, trellis";
const char kanji_ms5E33[] = "notebook, account book, album, curtain, veil, net, tent";
const char kanji_ms59B9[] = "younger sister";
const char kanji_ms6388[] = "impart, instruct, grant, confer";
const char kanji_ms673A[] = "desk, table";
const char kanji_ms7403[] = "ball, sphere";
const char kanji_ms51DD[] = "congeal, freeze, stiff, be absorbed in";
const char kanji_ms9B3C[] = "ghost, devil";
const char kanji_ms5E7E[] = "how many, how much, how far, how long, some, several";
const char kanji_ms7C89[] = "flour, powder, dust";
const char kanji_ms96EA[] = "snow";
const char kanji_ms565B[] = "chew, bite, gnaw";
const char kanji_ms62D2[] = "repel, refuse, reject, decline";
const char kanji_ms80C6[] = "gall bladder, courage, pluck, nerve";
const char kanji_ms9EBB[] = "hemp, flax, numb";
const char kanji_ms5F8B[] = "rhythm, law, regulation, gauge, control";
const char kanji_ms7206[] = "bomb, burst open, pop, split";
const char kanji_ms8074[] = "listen, headstrong, naughty, careful inquiry";
const char kanji_ms88F8[] = "naked, nude, uncovered, partially clothed";
const char kanji_ms4EAC[] = "capital, 10**16";
const char kanji_ms6C0F[] = "family name, surname, clan";
const char kanji_ms7701[] = "government ministry, conserve, omit";
const char kanji_ms5409[] = "good luck, joy, congratulations";
const char kanji_ms5C0B[] = "inquire, fathom, look for";
const char kanji_ms659C[] = "diagonal, slanting, oblique";
const char kanji_ms5CB8[] = "beach";
const char kanji_ms614E[] = "humility, be careful, discreet, prudent";
const char kanji_ms968A[] = "regiment, party, company, squad";
const char kanji_ms6291[] = "repress, well, now, in the first place, push, shove, press, seal, do in spite of";
const char kanji_ms672D[] = "tag, paper money, counter for bonds, placard, bid";
const char kanji_ms732B[] = "cat";
const char kanji_ms5BC2[] = "loneliness, quietly, mellow, mature, death of a priest";
const char kanji_ms6F5C[] = "submerge, conceal, hide, lower (voice), hush";
const char kanji_ms7956[] = "ancestor, pioneer, founder";
const char kanji_ms8150[] = "rot, decay, sour";
const char kanji_ms60E8[] = "wretched, disaster, cruelty, harsh";
const char kanji_ms6E90[] = "source, origin";
const char kanji_ms7CFB[] = "lineage, system";
const char kanji_ms57CE[] = "castle";
const char kanji_ms7565[] = "abbreviation, omission, outline, shorten, capture, plunder";
const char kanji_ms6A19[] = "signpost, seal, mark, stamp, imprint, symbol, emblem, trademark, evidence, souvenir, target";
const char kanji_ms96F0[] = "atmosphere, fog";
const char kanji_ms796D[] = "ritual, offer prayers, celebrate, deify, enshrine, worship";
const char kanji_ms7656[] = "mannerism, habit, vice, trait, fault, kink";
const char kanji_ms6F6E[] = "tide, salt water, opportunity";
const char kanji_ms708E[] = "inflammation, flame, blaze";
const char kanji_ms719F[] = "mellow, ripen, mature, acquire skill";
const char kanji_ms62DD[] = "worship, adore, pray to";
const char kanji_ms8986[] = "capsize, cover, shade, mantle, be ruined";
const char kanji_ms96C4[] = "masculine, male, hero, leader, superiority, excellence";
const char kanji_ms6068[] = "regret, bear a grudge, resentment, malice, hatred";
const char kanji_ms5BE9[] = "hearing, judge, trial";
const char kanji_ms8ACB[] = "solicit, invite, ask";
const char kanji_ms7A76[] = "research, study";
const char kanji_ms6CA1[] = "drown, sink, hide, fall into, disappear, die";
const char kanji_ms9774[] = "shoes";
const char kanji_ms88C1[] = "tailor, judge, decision, cut out (pattern)";
const char kanji_ms72D9[] = "aim at, sight, shadow, stalk";
const char kanji_ms59C9[] = "elder sister";
const char kanji_ms9699[] = "crevice, fissure, discord, opportunity, leisure";
const char kanji_ms8FF0[] = "mention, state, speak, relate";
const char kanji_ms5339[] = "equal, head, counter for small animals, roll of cloth";
const char kanji_ms5E7B[] = "phantasm, vision, dream, illusion, apparition";
const char kanji_ms8CAB[] = "pierce, 8 1/3lbs, penetrate, brace";
const char kanji_ms829D[] = "turf, lawn";
const char kanji_ms795D[] = "celebrate, congratulate";
const char kanji_ms6CB3[] = "river";
const char kanji_ms679D[] = "bough, branch, twig, limb, counter for branches";
const char kanji_ms8E74[] = "kick";
const char kanji_ms5200[] = "sword, saber, knife";
const char kanji_ms9375[] = "key";
const char kanji_ms6249[] = "front door, title page, front page";
const char kanji_ms9B42[] = "soul, spirit";
const char kanji_ms6696[] = "warmth";
const char kanji_ms6FE1[] = "get wet, damp, make love";
const char kanji_ms5451[] = "drink";
const char kanji_ms920D[] = "dull, slow, foolish, blunt";
const char kanji_ms7E1B[] = "truss, arrest, bind, tie, restrain";
const char kanji_ms7E41[] = "luxuriant, thick, overgrown, frequency, complexity, trouble";
const char kanji_ms8F29[] = "comrade, fellow, people, companions";
const char kanji_ms76BF[] = "dish, a helping, plate";
const char kanji_ms5589[] = "throat, voice";
const char kanji_ms62ED[] = "wipe, mop, swab";
const char kanji_ms8E0A[] = "jump, dance, leap, skip";
const char kanji_ms5CA9[] = "boulder, rock, cliff";
const char kanji_ms4F01[] = "undertake, scheme, design, attempt, plan";
const char kanji_ms8CDE[] = "prize, reward, praise";
const char kanji_ms786C[] = "stiff, hard";
const char kanji_ms5049[] = "admirable, greatness, remarkable, conceited, famous, excellent";
const char kanji_ms809D[] = "liver, pluck, nerve, chutzpah";
const char kanji_ms90F7[] = "home town, village, native place, district";
const char kanji_ms8ED2[] = "flats, counter for houses, eaves";
const char kanji_ms5982[] = "likeness, like, such as, as if, better, best, equal";
const char kanji_ms5742[] = "slope, incline, hill";
const char kanji_ms6F02[] = "drift, float (on liquid)";
const char kanji_ms6F84[] = "lucidity, be clear, clear, clarify, settle, strain, look grave";
const char kanji_ms5352[] = "graduate, soldier, private, die";
const char kanji_ms5EB7[] = "ease, peace";
const char kanji_ms9678[] = "land, six";
const char kanji_ms6A39[] = "timber, trees, wood, establish, set up";
const char kanji_ms654F[] = "cleverness, agile, alert";
const char kanji_ms52C9[] = "exertion, endeavour, encourage, strive, make effort, diligent";
const char kanji_ms514D[] = "excuse, dismissal";
const char kanji_ms7573[] = "tatami mat, counter for tatami mats, fold, shut up, do away with";
const char kanji_ms63EE[] = "brandish, wave, wag, swing, shake";
const char kanji_ms57DF[] = "range, region, limits, stage, level";
const char kanji_ms5B09[] = "glad, pleased, rejoice";
const char kanji_ms7344[] = "prison, jail";
const char kanji_ms6398[] = "dig, delve, excavate";
const char kanji_ms55A7[] = "noisy, boisterous";
const char kanji_ms9047[] = "meet, encounter, interview, treat, entertain, receive, deal with";
const char kanji_ms63F4[] = "abet, help, save";
const char kanji_ms65E7[] = "old times, old things, old friend, former, ex-";
const char kanji_ms8AB2[] = "chapter, lesson, section, department, division, counter for chapters (of a book)";
const char kanji_ms8896[] = "sleeve, wing (building), extension, give cold shoulder";
const char kanji_ms74B0[] = "ring, circle, loop";
const char kanji_ms8108[] = "vein, pulse, hope";
const char kanji_ms5211[] = "punish, penalty, sentence, punishment";
const char kanji_ms5178[] = "code, ceremony, law, rule";
const char kanji_ms507D[] = "falsehood, lie, deceive, pretend, counterfeit, forgery";
const char kanji_ms6F54[] = "undefiled, pure, clean, righteous, gallant";
const char kanji_ms6E0B[] = "astringent, hesitate, reluctant, have diarrhea";
const char kanji_ms52A3[] = "inferiority, be inferior to, be worse";
const char kanji_ms53F1[] = "scold, reprove";
const char kanji_ms8105[] = "threaten, coerce";
const char kanji_ms846C[] = "interment, bury, shelve";
const char kanji_ms520A[] = "publish, carve, engrave";
const char kanji_ms5805[] = "strict, hard, solid, tough, tight, reliable";
const char kanji_ms5B63[] = "seasons";
const char kanji_ms5B64[] = "orphan, alone";
const char kanji_ms725B[] = "cow";
const char kanji_ms7D22[] = "cord, rope, searching, inquiring";
const char kanji_ms7E26[] = "vertical, length, height, self-indulgent, wayward";
const char kanji_ms8C8C[] = "form, appearance, countenance";
const char kanji_ms5351[] = "lowly, base, vile, vulgar, despise";
const char kanji_ms677E[] = "pine tree";
const char kanji_ms635C[] = "search, look for, locate";
const char kanji_ms9810[] = "deposit, custody, leave with, entrust to";
const char kanji_ms63A7[] = "withdraw, draw in, hold back, refrain from, be moderate";
const char kanji_ms4E73[] = "milk, breasts";
const char kanji_ms6109[] = "pleasure, happy, rejoice";
const char kanji_ms9769[] = "leather, skin, reform, become serious";
const char kanji_ms7BC4[] = "pattern, example, model";
const char kanji_ms932F[] = "confused, mix, be in disorder";
const char kanji_ms7C8B[] = "chic, style, purity, essence, pith, cream, elite, choice";
const char kanji_ms79C0[] = "excel, excellence, beauty, surpass";
const char kanji_ms5275[] = "genesis, wound, injury, hurt, start, originate";
const char kanji_ms9663[] = "camp, battle array, ranks, position, sudden, brief time";
const char kanji_ms6691[] = "sultry, hot, summer heat";
const char kanji_ms5009[] = "godown, warehouse, storehouse, cellar, treasury";
const char kanji_ms722A[] = "claw, nail, talon";
const char kanji_ms7AF6[] = "emulate, compete with, bid, sell at auction, bout, contest, race";
const char kanji_ms7DB2[] = "netting, network";
const char kanji_ms6E9C[] = "collect, gather, be in arrears";
const char kanji_ms53CC[] = "pair, set, comparison, counter for pairs";
const char kanji_ms9665[] = "collapse, fall into, cave in, fall (castle), slide into";
const char kanji_ms8A0E[] = "chastise, attack, defeat, destroy, conquer";
const char kanji_ms81E8[] = "look to, face, meet, confront, attend, call on";
const char kanji_ms8AF8[] = "various, many, several, together";
const char kanji_ms6CBF[] = "run alongside, follow along, run along, lie along";
const char kanji_ms8056[] = "holy, saint, sage, master, priest";
const char kanji_ms6B8A[] = "particularly, especially, exceptionally";
const char kanji_ms6458[] = "pinch, pick, pluck, trim, clip, summarize";
const char kanji_ms8B1B[] = "lecture, club, association";
const char kanji_ms5DE7[] = "adroit, skilled, ingenuity";
const char kanji_ms5203[] = "blade, sword, edge";
const char kanji_ms9E97[] = "lovely, beautiful, graceful, resplendent";
const char kanji_ms6069[] = "grace, kindness, goodness, favor, mercy, blessing, benefit";
const char kanji_ms4F34[] = "consort, accompany, bring with, companion";
const char kanji_ms8CDB[] = "approve, praise, title or inscription on picture, assist, agree with";
const char kanji_ms8A8C[] = "document, records";
const char kanji_ms8DF3[] = "hop, leap up, spring, jerk, prance, buck, splash, sputter, snap";
const char kanji_ms9019[] = "crawl, creep, grovel, trail (vines)";
const char kanji_ms51CD[] = "frozen, congeal, refrigerate";
const char kanji_ms7F70[] = "penalty, punishment";
const char kanji_ms9F13[] = "drum, beat, rouse, muster";
const char kanji_ms6BBF[] = "Mr., hall, mansion, palace, temple, lord";
const char kanji_ms9694[] = "isolate, alternate, distance, separate, gulf";
const char kanji_ms64AB[] = "stroke, pat, smooth down";
const char kanji_ms5FB3[] = "benevolence, virtue, goodness, commanding respect";
const char kanji_ms7815[] = "smash, break, crush, familiar, popular";
const char kanji_ms84CB[] = "cover, lid, flap";
const char kanji_ms50AC[] = "sponsor, hold (a meeting), give (a dinner)";
const char kanji_ms6182[] = "melancholy, grieve, lament, be anxious, sad, unhappy";
const char kanji_ms5531[] = "chant, recite, call upon, yell";
const char kanji_ms6170[] = "consolation, amusement, seduce, cheer, make sport of, comfort, console";
const char kanji_ms8457[] = "renowned, publish, write, remarkable, phenomenal, put on, don, wear, arrival, finish (race), counter for suits of clothing, literary work";
const char kanji_ms7363[] = "animal, beast";
const char kanji_ms63C3[] = "be complete, uniform, all present";
const char kanji_ms65BD[] = "give, bestow, perform, alms";
const char kanji_ms51C4[] = "uncanny, weird, threatening, horrible";
const char kanji_ms62F3[] = "fist";
const char kanji_ms7D5E[] = "strangle, constrict, wring";
const char kanji_ms99C5[] = "station";
const char kanji_ms7D00[] = "chronicle, account, narrative, history, annals, geologic period";
const char kanji_ms7B52[] = "cylinder, pipe, tube, gun barrel, sleeve";
const char kanji_ms6E67[] = "boil, ferment, seethe, uproar, breed";
const char kanji_ms7C97[] = "coarse, rough, rugged";
const char kanji_ms5192[] = "risk, face, defy, dare, damage, assume (a name)";
const char kanji_ms8B72[] = "defer, turnover, transfer, convey";
const char kanji_ms85E4[] = "wisteria";
const char kanji_ms6795[] = "pillow";
const char kanji_ms6311[] = "challenge, contend for, make love to";
const char kanji_ms4E4F[] = "destitution, scarce, limited";
const char kanji_ms535A[] = "Dr., command, esteem, win acclaim, Ph.D., exposition, fair";
const char kanji_ms602F[] = "cowardice, wince, flinch, hesitate, waver";
const char kanji_ms91CC[] = "ri, village, parent's home, league";
const char kanji_ms6DBC[] = "refreshing, nice and cool";
const char kanji_ms8F03[] = "contrast, compare";
const char kanji_ms4ECF[] = "Buddha, the dead, France";
const char kanji_ms5C31[] = "concerning, settle, take position, depart, study, per";
const char kanji_ms5EC3[] = "abolish, obsolete, cessation, discarding, abandon";
const char kanji_ms5442[] = "spine, backbone";
const char kanji_ms6DB2[] = "fluid, liquid, juice, sap, secretion";
const char kanji_ms50D5[] = "me, I (male), servant, manservant";
const char kanji_ms86C7[] = "snake, serpent, hard drinker";
const char kanji_ms68C4[] = "abandon, throw away, discard, resign, reject, sacrifice";
const char kanji_ms76E4[] = "tray, shallow bowl, platter, tub, board, phonograph record";
const char kanji_ms5F69[] = "coloring, paint, makeup";
const char kanji_ms7C73[] = "rice, USA, metre";
const char kanji_ms6C37[] = "icicle, ice, hail, freeze, congeal";
const char kanji_ms517C[] = "concurrently, and, beforehand, in advance";
const char kanji_ms54B2[] = "blossom, bloom";
const char kanji_ms716E[] = "boil, cook";
const char kanji_ms4FB5[] = "encroach, invade, raid, trespass, violate";
const char kanji_ms53EC[] = "seduce, call, send for, wear, put on, ride in, buy, eat, drink, catch (cold)";
const char kanji_ms5E79[] = "tree trunk, main part, talent, capability";
const char kanji_ms6CF3[] = "swim";
const char kanji_ms60DA[] = "fall in love with, admire, grow senile";
const char kanji_ms78E8[] = "grind, polish, scour, improve, brush (teeth)";
const char kanji_ms9038[] = "deviate, idleness, leisure, miss the mark, evade, elude, parry, diverge";
const char kanji_ms546A[] = "spell, curse, charm, malediction";
const char kanji_ms5893[] = "grave, tomb";
const char kanji_ms9396[] = "chain, irons, connection";
const char kanji_ms61A4[] = "aroused, resent, be indignant, anger";
const char kanji_ms5510[] = "T'ang, China, foreign";
const char kanji_ms90A3[] = "what?";
const char kanji_ms6C60[] = "pond, cistern, pool, reservoir";
const char kanji_ms8A89[] = "reputation, praise, honor, glory";
const char kanji_ms8B0E[] = "riddle, puzzle, enigma, hint, tip";
const char kanji_ms7372[] = "seize, get, find, earn, acquire, can, may, able to";
const char kanji_ms6E7F[] = "damp, wet, moist";
const char kanji_ms7D2B[] = "purple, violet";
const char kanji_ms707D[] = "disaster, calamity, woe, curse, evil";
const char kanji_ms63A1[] = "pick, take, fetch, take up";
const char kanji_ms5B22[] = "lass, girl, Miss, daughter";
const char kanji_ms91E3[] = "angling, fish, catch, allure, ensnare";
const char kanji_ms6EDE[] = "stagnate, be delayed, overdue, arrears";
const char kanji_ms6EB6[] = "melt, dissolve, thaw";
const char kanji_ms9042[] = "consummate, accomplish, attain, commit (suicide)";
const char kanji_ms638C[] = "manipulate, rule, administer, conduct, palm of hand";
const char kanji_ms8CE2[] = "intelligent, wise, wisdom, cleverness";
const char kanji_ms5E8F[] = "preface, beginning, order, precedence, occasion, chance, incidentally";
const char kanji_ms8A17[] = "consign, requesting, entrusting with, pretend, hint";
const char kanji_ms76CA[] = "benefit, gain, profit, advantage";
const char kanji_ms4F50[] = "assistant, help";
const char kanji_ms66DC[] = "weekday";
const char kanji_ms5353[] = "eminent, table, desk, high";
const char kanji_ms7C92[] = "grains, drop, counter for tiny particles";
const char kanji_ms5E3D[] = "cap, headgear";
const char kanji_ms7761[] = "drowsy, sleep, die";
const char kanji_ms8A93[] = "vow, swear, pledge";
const char kanji_ms7AAE[] = "hard up, destitute, suffer, perplexed, cornered";
const char kanji_ms5265[] = "come off, peel, fade, discolor";
const char kanji_ms68B0[] = "contraption, fetter, machine, instrument";
const char kanji_ms5DE3[] = "nest, rookery, hive, cobweb, den";
const char kanji_ms98FD[] = "sated, tired of, bored, satiate";
const char kanji_ms6F22[] = "Sino-, China";
const char kanji_ms58C7[] = "podium, stage, rostrum, terrace";
const char kanji_ms8AA0[] = "sincerity, admonish, warn, prohibit, truth, fidelity";
const char kanji_ms8B00[] = "conspire, cheat, impose on, plan, devise, scheme, have in mind, deceive";
const char kanji_ms8A13[] = "instruction, Japanese character reading, explanation, read";
const char kanji_ms7D1B[] = "distract, be mistaken for, go astray, divert";
const char kanji_ms5674[] = "erupt, spout, emit, flush out";
const char kanji_ms98FC[] = "domesticate, raise, keep, feed";
const char kanji_ms80A1[] = "thigh, crotch";
const char kanji_ms6D6A[] = "wandering, waves, billows, reckless, unrestrained";
const char kanji_ms4FC3[] = "stimulate, urge, press, demand, incite";
const char kanji_ms99B4[] = "get used to, experienced, tamed";
const char kanji_ms518A[] = "tome, counter for books, volume";
const char kanji_ms8CED[] = "gamble, wager, bet";
const char kanji_ms5384[] = "unlucky, misfortune, bad luck, disaster";
const char kanji_ms51E1[] = "commonplace, ordinary, mediocre";
const char kanji_ms636E[] = "set, lay a foundation, install, equip, squat down, sit down";
const char kanji_ms92AD[] = "coin, .01 yen, money";
const char kanji_ms7A3C[] = "earnings, work, earn money";
const char kanji_ms6CC9[] = "spring, fountain";
const char kanji_ms5F6B[] = "carve, engrave, chisel";
const char kanji_ms72A0[] = "sacrifice";
const char kanji_ms7C60[] = "basket, devote oneself, seclude oneself, cage, coop, implied";
const char kanji_ms7272[] = "animal sacrifice, offering";
const char kanji_ms968F[] = "follow, though, notwithstanding, while, during, both, all, obey, submit to, comply, at the mercy of (the waves)";
const char kanji_ms906D[] = "encounter, meet, party, association, interview, join";
const char kanji_ms66C7[] = "cloudy weather, cloud up";
const char kanji_ms84BC[] = "blue, pale";
const char kanji_ms72FC[] = "wolf";
const char kanji_ms4FD7[] = "vulgar, customs, manners, worldliness, mundane things";
const char kanji_ms77B3[] = "pupil (of eye)";
const char kanji_ms9727[] = "fog, mist";
const char kanji_ms9B31[] = "gloom, depression, melancholy, luxuriant";
const char kanji_ms5B97[] = "religion, sect, denomination, main point, origin, essence";
const char kanji_ms8A5E[] = "part of speech, words, poetry";
const char kanji_ms7E3E[] = "exploits, achievements, unreeling cocoons";
const char kanji_ms8997[] = "peep, peek, come in sight";
const char kanji_ms5AC1[] = "marry into, bride";
const char kanji_ms57A3[] = "hedge, fence, wall";
const char kanji_ms65E6[] = "daybreak, dawn, morning";
const char kanji_ms6E09[] = "ford, go cross, transit, ferry, import, involve";
const char kanji_ms6D78[] = "immersed, soak, dip, steep, moisten, wet, dunk";
const char kanji_ms5B6B[] = "grandchild, descendants";
const char kanji_ms984E[] = "jaw, chin, gill";
const char kanji_ms52B1[] = "encourage, be diligent, inspire";
const char kanji_ms6CE1[] = "bubbles, foam, suds, froth";
const char kanji_ms7642[] = "heal, cure";
const char kanji_ms79D2[] = "second (1/60 minute)";
const char kanji_ms5629[] = "noisy";
const char kanji_ms58EE[] = "robust, manhood, prosperity";
const char kanji_ms59D4[] = "committee, entrust to, leave to, devote, discard";
const char kanji_ms89A7[] = "perusal, see";
const char kanji_ms6F70[] = "crush, smash, break, dissipate";
const char kanji_ms5374[] = "instead, on the contrary, rather, step back, withdraw, retreat";
const char kanji_ms7E2B[] = "sew, stitch, embroider";
const char kanji_ms67AF[] = "wither, die, dry up, be seasoned";
const char kanji_ms63B2[] = "put up (a notice), put up, hoist, display, hang out, publish, describe";
const char kanji_ms8CBC[] = "stick, paste, apply";
const char kanji_ms5237[] = "printing, print, brush";
const char kanji_ms82DB[] = "torment, scold, chastise";
const char kanji_ms8FB1[] = "embarrass, humiliate, shame";
const char kanji_ms75F4[] = "stupid, foolish";
const char kanji_ms7DBF[] = "cotton";
const char kanji_ms5BFA[] = "Buddhist temple";
const char kanji_ms5BE7[] = "rather, preferably, peaceful, quiet, tranquility";
const char kanji_ms6E26[] = "whirlpool, eddy, vortex";
const char kanji_ms6BB4[] = "assault, hit, beat, thrash";
const char kanji_ms6EF4[] = "drip, drop";
const char kanji_ms622F[] = "frolic, play, sport";
const char kanji_ms8D66[] = "pardon, forgiveness";
const char kanji_ms5DDE[] = "state, province";
const char kanji_ms6C99[] = "sand";
const char kanji_ms540A[] = "suspend, hang, wear (sword)";
const char kanji_ms8A0A[] = "request, question, investigate";
const char kanji_ms7768[] = "glaring at, authority, power, scowl at";
const char kanji_ms6DAF[] = "horizon, shore, limit, bound";
const char kanji_ms7D0B[] = "family crest, figures";
const char kanji_ms7C4D[] = "enroll, domiciliary register, membership";
const char kanji_ms8511[] = "ignore, despise, neglect, ridicule";
const char kanji_ms88FE[] = "cuff, hem, foot of mountain";
const char kanji_ms6C5F[] = "creek, inlet, bay";
const char kanji_ms5869[] = "salt";
const char kanji_ms75C7[] = "symptoms, illness";
const char kanji_ms8870[] = "decline, wane, weaken";
const char kanji_ms5E9C[] = "borough, urban prefecture, govt office, representative body, storehouse";
const char kanji_ms6F20[] = "vague, obscure, desert, wide";
const char kanji_ms9AB8[] = "bone, body, corpse";
const char kanji_ms7B1B[] = "flute, clarinet, pipe, whistle, bagpipe, piccolo";
const char kanji_ms84B8[] = "steam, heat, sultry, foment, get musty";
const char kanji_ms62E1[] = "broaden, extend, expand, enlarge";
const char kanji_ms96F7[] = "thunder, lightning bolt";
const char kanji_ms8FB2[] = "agriculture, farmers";
const char kanji_ms50E7[] = "Buddhist priest, monk";
const char kanji_ms75E9[] = "get thin";
const char kanji_ms7CA7[] = "cosmetics, adorn (one's person)";
const char kanji_ms51F6[] = "villain, evil, bad luck, disaster";
const char kanji_ms643A[] = "portable, carry (in hand), armed with, bring along";
const char kanji_ms59D3[] = "surname";
const char kanji_ms582A[] = "withstand, endure, support, resist";
const char kanji_ms919C[] = "ugly, unclean, shame, bad looking";
const char kanji_ms74F6[] = "bottle, vial, jar, jug, vat, urn";
const char kanji_ms96C5[] = "gracious, elegant, graceful, refined";
const char kanji_ms8302[] = "overgrown, grow thick, be luxuriant";
const char kanji_ms75D5[] = "mark, foot print";
const char kanji_ms5632[] = "ridicule, insult";
const char kanji_ms4FFA[] = "I, myself";
const char kanji_ms7FFB[] = "flip, turn over, wave, flutter, change (mind)";
const char kanji_ms5B87[] = "eaves, roof, house, heaven";
const char kanji_ms52E7[] = "persuade, recommend, advise, encourage, offer";
const char kanji_ms8A95[] = "nativity, be born, declension, lie, be arbitrary";
const char kanji_ms895F[] = "collar, neck, lapel, one's inner feelings";
const char kanji_ms8C46[] = "beans, pea, midget";
const char kanji_ms584A[] = "clod, lump, chunk, clot, mass";
const char kanji_ms8AE6[] = "truth, clarity, abandon, give up";
const char kanji_ms6E2F[] = "harbor";
const char kanji_ms83DC[] = "vegetable, side dish, greens";
const char kanji_ms5E7D[] = "seclude, confine to a room, deep, profound, secluded, faint, dark, tranquil, calm";
const char kanji_ms524A[] = "plane, sharpen, whittle, pare, shave";
const char kanji_ms7832[] = "cannon, gun";
const char kanji_ms6020[] = "neglect, laziness";
const char kanji_ms63BB[] = "scratch, rake, comb, paddle, behead";
const char kanji_ms55AB[] = "consume, eat, drink, smoke, receive (a blow)";
const char kanji_ms553E[] = "saliva, sputum";
const char kanji_ms8D08[] = "presents, send, give to, award to, confer on, presenting something";
const char kanji_ms93AE[] = "tranquilize, ancient peace-preservation centers";
const char kanji_ms59AC[] = "jealous, envy";
const char kanji_ms682A[] = "stocks, stump, shares, stock, counter for small plants";
const char kanji_ms5747[] = "level, average";
const char kanji_ms4E18[] = "hill, knoll";
const char kanji_ms6D25[] = "haven, port, harbor, ferry";
const char kanji_ms67B6[] = "erect, frame, mount, support, shelf, construct";
const char kanji_ms819A[] = "skin, body, grain, texture, disposition";
const char kanji_ms6FC1[] = "voiced, uncleanness, wrong, nigori, impurity";
const char kanji_ms7551[] = "farm, field, garden, one's specialty, (kokuji)";
const char kanji_ms65D7[] = "national flag, banner, standard";
const char kanji_ms9262[] = "bowl, rice tub, pot, crown";
const char kanji_ms7DB1[] = "hawser, class (genus), rope, cord, cable";
const char kanji_ms6115[] = "surprised, frightened";
const char kanji_ms594F[] = "play music, speak to a ruler, complete";
const char kanji_ms7E04[] = "straw rope, cord";
const char kanji_ms614C[] = "disconcerted, be confused, lose one's head";
const char kanji_ms8102[] = "fat, grease, tallow, lard, rosin, gum, tar";
const char kanji_ms9283[] = "gun, arms";
const char kanji_ms81C6[] = "timidity, heart, mind, fear, cowardly";
const char kanji_ms9234[] = "small bell, buzzer";
const char kanji_ms7AE5[] = "juvenile, child";
const char kanji_ms7DE9[] = "slacken, loosen, relax, lessen, be moderate, ease";
const char kanji_ms80A5[] = "fertilizer, get fat, fertile, manure, pamper";
const char kanji_ms732E[] = "offering, counter for drinks, present, offer";
const char kanji_ms9298[] = "inscription, signature (of artisan)";
const char kanji_ms5375[] = "egg, ovum, spawn, roe";
const char kanji_ms6C70[] = "washing, sieving, filtering, weeding out, luxury";
const char kanji_ms906E[] = "intercept, interrupt, obstruct";
const char kanji_ms65CB[] = "rotation, go around";
const char kanji_ms7F85[] = "gauze, thin silk, Rome, arrange, spread out";
const char kanji_ms6392[] = "repudiate, exclude, expel, reject, line up, arrange";
const char kanji_ms7AF9[] = "bamboo";
const char kanji_ms5C16[] = "be pointed, sharp, taper, displeased, angry, edgy";
const char kanji_ms8CA8[] = "freight, goods, property";
const char kanji_ms7A3D[] = "think, consider";
const char kanji_ms4F0A[] = "Italy, that one";
const char kanji_ms9084[] = "send back, return";
const char kanji_ms80C3[] = "stomach, paunch, crop, craw";
const char kanji_ms9451[] = "specimen, take warning from, learn from";
const char kanji_ms702C[] = "rapids, current, torrent, shallows, shoal";
const char kanji_ms7B26[] = "token, sign, mark, tally, charm";
const char kanji_ms76FE[] = "shield, escutcheon, pretext";
const char kanji_ms60A3[] = "afflicted, disease, suffer from, be ill";
const char kanji_ms5C65[] = "perform, complete, footgear, shoes, boots, put on (the feet)";
const char kanji_ms515A[] = "party, faction, clique";
const char kanji_ms6EA2[] = "overflow, inundate, spill";
const char kanji_ms7F72[] = "signature, govt office, police station";
const char kanji_ms80F4[] = "trunk, torso, hull (ship), hub of wheel";
const char kanji_ms9178[] = "acid, bitterness, sour, tart";
const char kanji_ms511F[] = "reparation, make up for, recompense, redeem";
const char kanji_ms50DA[] = "colleague, official, companion";
const char kanji_ms629E[] = "choose, select, elect, prefer";
const char kanji_ms6D5C[] = "seacoast, beach, seashore";
const char kanji_ms6589[] = "adjusted, alike, equal, similar variety of";
const char kanji_ms6168[] = "rue, be sad, sigh, lament";
const char kanji_ms5A46[] = "old woman, grandma, wet nurse";
const char kanji_ms6B6A[] = "warp, bend, strained, distort";
const char kanji_ms65E8[] = "delicious, relish, show a liking for, purport, will, clever, expert";
const char kanji_ms55C5[] = "smell, sniff, scent";
const char kanji_ms81A8[] = "swell, get fat, thick";
const char kanji_ms6F0F[] = "leak, escape, time";
const char kanji_ms60A0[] = "permanence, distant, long time, leisure";
const char kanji_ms54B3[] = "cough, clear throat";
const char kanji_ms83D3[] = "candy, cakes, fruit";
const char kanji_ms91D8[] = "nail, tack, peg";
const char kanji_ms7DAD[] = "fiber, tie, rope";
const char kanji_ms5949[] = "observance, offer, present, dedicate";
const char kanji_ms6982[] = "outline, condition, approximation, generally";
const char kanji_ms585E[] = "close, shut, cover, block, obstruct";
const char kanji_ms6562[] = "daring, brave, bold, sad, tragic, pitiful";
const char kanji_ms5951[] = "pledge, promise, vow";
const char kanji_ms99B3[] = "run, gallop, sail, drive (a wagon), win (fame), despatch";
const char kanji_ms963F[] = "Africa, flatter, fawn upon, corner, nook, recess";
const char kanji_ms5D50[] = "storm, tempest";
const char kanji_ms7D10[] = "string, cord, braid, lace, tape, strap, ribbon";
const char kanji_ms5AC9[] = "jealous, envy";
const char kanji_ms631F[] = "pinch, between";
const char kanji_ms6D1E[] = "den, cave, excavation";
const char kanji_ms96C7[] = "employ, hire";
const char kanji_ms8A69[] = "poem, poetry";
const char kanji_ms8358[] = "villa, inn, cottage, feudal manor, solemn, dignified";
const char kanji_ms990C[] = "food, bait, prey, tempting profit";
const char kanji_ms7763[] = "coach, command, urge, lead, supervise";
const char kanji_ms8A3A[] = "checkup, seeing, diagnose, examine";
const char kanji_ms628A[] = "grasp, faggot, bunch, counter for bundles";
const char kanji_ms6627[] = "dark, foolish";
const char kanji_ms5FCC[] = "mourning, abhor, detestable, death anniversary";
const char kanji_ms5996[] = "attractive, bewitching, calamity";
const char kanji_ms4EAD[] = "pavilion, restaurant, mansion, arbor, cottage, vaudeville, music hall, stage name";
const char kanji_ms5BFF[] = "longevity, congratulations, one's natural life";
const char kanji_ms7F75[] = "abuse, insult";
const char kanji_ms5BB4[] = "banquet, feast, party";
const char kanji_ms8098[] = "elbow, arm";
const char kanji_ms5835[] = "fence, railing, enclosure";
const char kanji_ms526F[] = "vice-, assistant, aide, duplicate, copy";
const char kanji_ms99D0[] = "stop-over, reside in, resident";
const char kanji_ms60B6[] = "be in agony, worry";
const char kanji_ms6590[] = "beautiful, patterned";
const char kanji_ms7FFC[] = "wing, plane, flank";
const char kanji_ms6C41[] = "soup, juice, broth, sap, gravy, pus";
const char kanji_ms5875[] = "dust, trash, garbage";
const char kanji_ms77DB[] = "halberd, arms, festival float";
const char kanji_ms755C[] = "livestock, domestic fowl and animals";
const char kanji_ms9676[] = "pottery, porcelain";
const char kanji_ms5F90[] = "gradually, slowly, deliberately, gently";
const char kanji_ms8A6E[] = "discussion, methods called for, selection, result";
const char kanji_ms72E9[] = "hunt, raid, gather";
const char kanji_ms5264[] = "dose, medicine, drug";
const char kanji_ms63B4[] = "catch, seize, grasp, hold, arrest, capture";
const char kanji_ms65E2[] = "previously, already, long ago";
const char kanji_ms9805[] = "paragraph, nape of neck, clause, item, term (expression)";
const char kanji_ms76C6[] = "basin, lantern festival, tray";
const char kanji_ms822A[] = "navigate, sail, cruise, fly";
const char kanji_ms821F[] = "boat, ship";
const char kanji_ms55AA[] = "miss, mourning";
const char kanji_ms621A[] = "grieve, relatives";
const char kanji_ms925B[] = "lead";
const char kanji_ms5854[] = "pagoda, tower, steeple";
const char kanji_ms6CB8[] = "seethe, boil, ferment, uproar, breed";
const char kanji_ms5CA1[] = "mount, hill, knoll";
const char kanji_ms6148[] = "mercy";
const char kanji_ms64AE[] = "snapshot, take pictures";
const char kanji_ms98E2[] = "hungry, starve";
const char kanji_ms662D[] = "shining, bright";
const char kanji_ms559A[] = "yell, cry, call, scream, summon";
const char kanji_ms8CAF[] = "savings, store, lay in, keep, wear mustache";
const char kanji_ms770C[] = "prefecture";
const char kanji_ms5BDB[] = "tolerant, leniency, generosity, relax, feel at home, be at ease, broadminded";
const char kanji_ms5538[] = "groan, roar";
const char kanji_ms758E[] = "alienate, rough, neglect, shun, sparse, penetrate";
const char kanji_ms7FA8[] = "envious, be jealous, covet";
const char kanji_ms74A7[] = "sphere, ball";
const char kanji_ms685C[] = "cherry";
const char kanji_ms4E39[] = "rust-colored, red, red lead, pills, sincerity";
const char kanji_ms55B0[] = "eat, drink, receive (a blow), (kokuji)";
const char kanji_ms8650[] = "tyrannize, oppress";
const char kanji_ms4EC1[] = "humanity, virtue, benevolence, charity, man, kernel";
const char kanji_ms82BD[] = "bud, sprout, spear, germ";
const char kanji_ms6D29[] = "leak, escape";
const char kanji_ms5F04[] = "play with, tamper, trifle with";
const char kanji_ms5D0E[] = "promontory, cape, spit";
const char kanji_ms5E1D[] = "sovereign, the emperor, god, creator";
const char kanji_ms90B8[] = "residence, mansion";
const char kanji_ms54F2[] = "philosophy, clear";
const char kanji_ms64E6[] = "grate, rub, scratch, scrape, chafe, scour";
const char kanji_ms9867[] = "look back, review, examine oneself, turn around";
const char kanji_ms6279[] = "criticism, strike";
const char kanji_ms545F[] = "mutter, grumble, murmur";
const char kanji_ms504F[] = "partial, side, left-side radical, inclining, biased";
const char kanji_ms81E3[] = "retainer, subject";
const char kanji_ms5984[] = "delusion, unnecessarily, without authority, reckless";
const char kanji_ms5104[] = "hundred million, 10**8";
const char kanji_ms7A32[] = "rice plant";
const char kanji_ms9813[] = "suddenly, immediately, in a hurry, arrange, stay in place, bow, kowtow";
const char kanji_ms6EBA[] = "drown, indulge";
const char kanji_ms75BE[] = "rapidly";
const char kanji_ms6BBB[] = "husk, nut shell";
const char kanji_ms662F[] = "just so, this, right, justice";
const char kanji_ms7652[] = "healing, cure, quench (thirst), wreak";
const char kanji_ms6756[] = "staff, cane";
const char kanji_ms4FAE[] = "scorn, despise, make light of, contempt";
const char kanji_ms7C98[] = "sticky, glutinous, greasy, persevere";
const char kanji_ms70AD[] = "charcoal, coal";
const char kanji_ms61C7[] = "sociable, kind, courteous, hospitable, cordial";
const char kanji_ms6469[] = "chafe, rub, polish, grind, scrape";
const char kanji_ms9EA6[] = "barley, wheat";
const char kanji_ms9192[] = "awake, be disillusioned, sober up";
const char kanji_ms6367[] = "lift up, give, offer, consecrate, sacrifice, dedicate";
const char kanji_ms9591[] = "leisure";
const char kanji_ms65AC[] = "beheading, kill, murder";
const char kanji_ms59EB[] = "princess";
const char kanji_ms5840[] = "fence, wall, (kokuji)";
const char kanji_ms57C3[] = "dust";
const char kanji_ms733F[] = "monkey";
const char kanji_ms90ED[] = "enclosure, quarters, fortification, red-light district";
const char kanji_ms7A1A[] = "immature, young";
const char kanji_ms6CBC[] = "marsh, lake, bog, swamp, pond";
const char kanji_ms7259[] = "tusk, fang, tusk radical (no. 92)";
const char kanji_ms7ADC[] = "dragon, imperial";
const char kanji_ms8276[] = "glossy, luster, glaze, polish, charm, colorful, captivating";
const char kanji_ms4E5E[] = "beg, invite, ask";
const char kanji_ms935B[] = "forge, discipline, train";
const char kanji_ms5F84[] = "diameter, path, method";
const char kanji_ms74E6[] = "tile, gram";
const char kanji_ms8A6B[] = "apologize";
const char kanji_ms5075[] = "spy";
const char kanji_ms8B90[] = "enemy, revenge";
const char kanji_ms9418[] = "bell, gong, chimes";
const char kanji_ms6F01[] = "fishing, fishery";
const char kanji_ms878D[] = "dissolve, melt";
const char kanji_ms6E56[] = "lake";
const char kanji_ms7A3F[] = "draft, copy, manuscript, straw";
const char kanji_ms5954[] = "run, bustle";
const char kanji_ms8AFE[] = "consent, assent, agreement";
const char kanji_ms59A8[] = "disturb, prevent, hamper, obstruct";
const char kanji_ms7729[] = "faint, dizzy";
const char kanji_ms75FA[] = "palsy, become numb, paralysed";
const char kanji_ms9320[] = "lock, fetters, shackles";
const char kanji_ms718A[] = "bear";
const char kanji_ms4E80[] = "tortoise, turtle";
const char kanji_ms7F8A[] = "sheep";
const char kanji_ms9583[] = "flash, brandish";
const char kanji_ms6190[] = "pity, have mercy, sympathise, compassion";
const char kanji_ms558B[] = "talk, chat, chatter";
const char kanji_ms7E4A[] = "slender, fine, thin kimono";
const char kanji_ms5750[] = "sit";
const char kanji_ms76BA[] = "wrinkles, creases, folds";
const char kanji_ms6602[] = "rise";
const char kanji_ms6885[] = "plum";
const char kanji_ms7687[] = "emperor";
const char kanji_ms6FEF[] = "laundry, wash, pour on, rinse";
const char kanji_ms4F3A[] = "pay respects, visit, ask, inquire, question, implore";
const char kanji_ms8D05[] = "luxury";
const char kanji_ms73E0[] = "pearl, gem, jewel";
const char kanji_ms6838[] = "nucleus, core, kernel";
const char kanji_ms8EDF[] = "soft";
const char kanji_ms51A0[] = "crown, best, peerless";
const char kanji_ms90CA[] = "outskirts, suburbs, rural area";
const char kanji_ms8F38[] = "transport, send, be inferior";
const char kanji_ms76F2[] = "blind, blind man, ignoramus";
const char kanji_ms658E[] = "purification, Buddhist food, room, worship, avoid, alike";
const char kanji_ms6F2B[] = "cartoon, involuntarily, unrestrained, in spite of oneself, corrupt";
const char kanji_ms6070[] = "just as, as though, fortunately";
const char kanji_ms559D[] = "hoarse, scold";
const char kanji_ms5098[] = "umbrella";
const char kanji_ms8CC3[] = "fare, fee, hire, rent, wages, charge";
const char kanji_ms62D7[] = "crooked, twisted, distorted, perverted, cross";
const char kanji_ms6717[] = "melodious, clear, bright, serene, cheerful";
const char kanji_ms9285[] = "copper";
const char kanji_ms5948[] = "Nara, what?";
const char kanji_ms6B3A[] = "deceit, cheat, delude";
const char kanji_ms6247[] = "fan, folding fan";
const char kanji_ms7A0E[] = "tax, duty";
const char kanji_ms56C1[] = "whisper, murmur";
const char kanji_ms9A0E[] = "equestrian, riding on horses, counter for equestrians";
const char kanji_ms68F2[] = "live, dwell";
const char kanji_ms7089[] = "hearth, furnace, kiln, reactor";
const char kanji_ms80AF[] = "agreement, consent, comply with";
const char kanji_ms80A2[] = "limb, arms & legs";
const char kanji_ms5208[] = "reap, cut, clip, trim, prune";
const char kanji_ms62D8[] = "arrest, seize, concerned, adhere to, despite";
const char kanji_ms84C4[] = "amass, raise, hoard, store";
const char kanji_ms4F2F[] = "chief, count, earl, uncle, Brazil";
const char kanji_ms52DF[] = "recruit, campaign, gather (contributions), enlist, grow violent";
const char kanji_ms62AB[] = "expose, open";
const char kanji_ms67A0[] = "frame, framework, spindle, spool, bounding-box, (kokuji)";
const char kanji_ms6790[] = "chop, divide, tear, analyze";
const char kanji_ms6349[] = "catch, capture";
const char kanji_ms5F13[] = "bow, bow (archery, violin)";
const char kanji_ms5146[] = "portent, 10**12, trillion, sign, omen, symptoms";
const char kanji_ms5F81[] = "subjugate, attack the rebellious, collect taxes";
const char kanji_ms832B[] = "wide, extensive";
const char kanji_ms57A2[] = "dirt, grime, earwax";
const char kanji_ms61A7[] = "yearn after, long for, aspire to, admire, adore";
const char kanji_ms80BA[] = "lungs";
const char kanji_ms6843[] = "peach";
const char kanji_ms8F5F[] = "roar, thunder, boom resound";
const char kanji_ms6E07[] = "thirst, dry up, parch";
const char kanji_ms934B[] = "pot, pan, kettle";
const char kanji_ms6191[] = "depend, rely, evidence, proof, according to, possess, haunt";
const char kanji_ms8A1D[] = "doubt";
const char kanji_ms723D[] = "refreshing, bracing, resonant, sweet, clear";
const char kanji_ms5962[] = "extravagance, luxury";
const char kanji_ms5448[] = "display, offer, present, send, exhibit";
const char kanji_ms633F[] = "insert, put in, graft, wear (sword)";
const char kanji_ms7D3A[] = "dark blue, navy";
const char kanji_ms7267[] = "breed, care for, shepherd, feed, pasture";
const char kanji_ms5E81[] = "government office";
const char kanji_ms6F64[] = "wet, be watered, profit by, receive benefits, favor, charm, steep";
const char kanji_ms7D33[] = "sire, good belt, gentleman";
const char kanji_ms58A8[] = "black ink, India ink, ink stick, Mexico";
const char kanji_ms66D6[] = "dark, not clear";
const char kanji_ms5D16[] = "cliff, bluff, precipice";
const char kanji_ms9AED[] = "beard, mustache";
const char kanji_ms67F3[] = "willow";
const char kanji_ms9DF9[] = "hawk";
const char kanji_ms8E87[] = "hesitate";
const char kanji_ms8E8A[] = "hesitate";
const char kanji_ms8912[] = "praise, extol";
const char kanji_ms5DFE[] = "towel, hanging scroll, width, cloth radical (no. 50)";
const char kanji_ms90F5[] = "mail, stagecoach stop";
const char kanji_ms5420[] = "bark, howl, cry";
const char kanji_ms4E4B[] = "of, this";
const char kanji_ms983B[] = "repeatedly, recur";
const char kanji_ms6D44[] = "clean, purify, cleanse, exorcise, Manchu Dynasty";
const char kanji_ms667A[] = "wisdom, intellect, reason";
const char kanji_ms8CC0[] = "congratulations, joy";
const char kanji_ms7D79[] = "silk";
const char kanji_ms7E4B[] = "tie, fasten, chain, tether, connect";
const char kanji_ms819C[] = "membrane";
const char kanji_ms71E5[] = "parch, dry up";
const char kanji_ms7A00[] = "rare, phenomenal, dilute (acid)";
const char kanji_ms9855[] = "appear, existing";
const char kanji_ms72FD[] = "wolf, be flurried";
const char kanji_ms9686[] = "hump, high, noble, prosperity";
const char kanji_ms5B54[] = "cavity, hole, slit, very, great, exceedingly";
const char kanji_ms916C[] = "repay, reward, retribution";
const char kanji_ms6234[] = "be crowned with, live under (a ruler), receive";
const char kanji_ms60F9[] = "attract, captivate";
const char kanji_ms6734[] = "crude, simple, plain, docile";
const char kanji_ms7BB8[] = "chopsticks";
const char kanji_ms69CC[] = "hammer, mallet";
const char kanji_ms61A9[] = "recess, rest, relax, repose";
const char kanji_ms60A6[] = "ecstasy, joy, rapture";
const char kanji_ms864E[] = "tiger, drunkard";
const char kanji_ms5B9B[] = "address, just like, fortunately";
const char kanji_ms6B04[] = "column, handrail, blank, space";
const char kanji_ms6676[] = "sparkle, clear, crystal";
const char kanji_ms8ECC[] = "rut, wheel, track, model, way of doing";
const char kanji_ms547B[] = "moan, groan";
const char kanji_ms80E1[] = "barbarian, foreign";
const char kanji_ms963B[] = "thwart, separate from, prevent, obstruct, deter, impede";
const char kanji_ms8776[] = "butterfly";
const char kanji_ms6EDD[] = "waterfall, rapids, cascade";
const char kanji_ms77AD[] = "clear";
const char kanji_ms6731[] = "vermilion, cinnabar, scarlet, red, bloody";
const char kanji_ms5EFB[] = "round, game, revolve, go around, circumference";
const char kanji_ms6028[] = "grudge, show resentment, be jealous";
const char kanji_ms7DBA[] = "figured cloth, beautiful";
const char kanji_ms69CD[] = "spear, lance, javelin";
const char kanji_ms7CD6[] = "sugar";
const char kanji_ms68DF[] = "ridgepole, ridge";
const char kanji_ms8CB0[] = "get, have, obtain";
const char kanji_ms8607[] = "be resuscitated, revived, perilla, shiso";
const char kanji_ms754F[] = "fear, majestic, graciously, be apprehensive";
const char kanji_ms902E[] = "apprehend, chase";
const char kanji_ms51B4[] = "be clear, serene, cold, skilful";
const char kanji_ms8FBF[] = "follow (road), pursue";
const char kanji_ms4EC7[] = "foe, enemy, revenge, grudge, feud";
const char kanji_ms8CCA[] = "burglar, rebel, traitor, robber";
const char kanji_ms6144[] = "fear";
const char kanji_ms54BD[] = "throat, choked, smothered, stuffy";
const char kanji_ms5815[] = "degenerate, descend to, lapse into";
const char kanji_ms9673[] = "exhibit, state, relate, explain";
const char kanji_ms6C72[] = "draw (water), ladle, scoop, pump";
const char kanji_ms7B87[] = "counter for articles";
const char kanji_ms8CD1[] = "flourish, be bustling, prosperity";
const char kanji_ms5516[] = "mute, dumb";
const char kanji_ms63C9[] = "rub, massage, shampoo, debate vigorously, train, coach, worry, get in trouble";
const char kanji_ms5132[] = "be profitable, yield profit";
const char kanji_ms6E7E[] = "gulf, bay, inlet";
const char kanji_ms731F[] = "game-hunting, shooting, game, bag";
const char kanji_ms660F[] = "dark, evening, dusk";
const char kanji_ms6155[] = "pining, yearn for, love dearly, adore";
const char kanji_ms6749[] = "cedar, cryptomeria";
const char kanji_ms5D07[] = "adore, respect, revere, worship";
const char kanji_ms61F2[] = "penal, chastise, punish, discipline";
const char kanji_ms8C9E[] = "upright, chastity, constancy, righteousness";
const char kanji_ms82B3[] = "perfume, balmy, favorable, fragrant";
const char kanji_ms97AD[] = "whip, rod, counter for whippings";
const char kanji_ms5C3A[] = "shaku, Japanese foot, measure, scale, rule";
const char kanji_ms7169[] = "anxiety, trouble, worry, pain, ill, annoy, nuisance, irksome";
const char kanji_ms7F60[] = "trap, snare";
const char kanji_ms53D4[] = "uncle, youth";
const char kanji_ms8217[] = "shop, store, pave";
const char kanji_ms6E9D[] = "gutter, ditch, sewer, drain, 10**32";
const char kanji_ms8CA9[] = "marketing, sell, trade";
const char kanji_ms6D12[] = "wash, sprinkle";
const char kanji_ms723A[] = "old man, grampa";
const char kanji_ms8FC2[] = "roundabout way";
const char kanji_ms7262[] = "prison, jail, hardness";
const char kanji_ms6F2C[] = "pickling, soak, moisten, steep";
const char kanji_ms50B2[] = "be proud";
const char kanji_ms56DA[] = "captured, criminal, arrest, catch";
const char kanji_ms96C0[] = "sparrow";
const char kanji_ms5F66[] = "lad, boy (ancient)";
const char kanji_ms7CE7[] = "provisions, food, bread";
const char kanji_ms7ABA[] = "lie in wait, spy on, reconnoiter";
const char kanji_ms9A19[] = "deceive";
const char kanji_ms5091[] = "greatness, excellence";
const char kanji_ms6C96[] = "open sea, offing, rise high into sky";
const char kanji_ms6DF5[] = "abyss, edge, deep pool, the depths";
const char kanji_ms816B[] = "tumor, swelling";
const char kanji_ms59A5[] = "gentle, peace, depravity";
const char kanji_ms7C3F[] = "register, record book";
const char kanji_ms95A3[] = "tower, tall building, palace";
const char kanji_ms6817[] = "chestnut";
const char kanji_ms8D74[] = "proceed, get, become, tend";
const char kanji_ms9D8F[] = "chicken";
const char kanji_ms5C1A[] = "esteem, furthermore, still, yet";
const char kanji_ms62B9[] = "rub, paint, erase";
const char kanji_ms548E[] = "blame, censure, reprimand";
const char kanji_ms8CFC[] = "subscription, buy";
const char kanji_ms9022[] = "meeting, tryst, date, rendezvous";
const char kanji_ms6F06[] = "lacquer, varnish, seven";
const char kanji_ms64B2[] = "slap, strike, hit, beat, tell, speak";
const char kanji_ms514B[] = "overcome, kindly, skillfully";
const char kanji_ms8E35[] = "heel";
const char kanji_ms9905[] = "mochi rice cake";
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
