maccody/KanaChordPlus/software/kana.h

// kana.h - Hiragana and Katakana Unicode characters.
/**
This file is part of KanaChordPlus Keyboard.
 Copyright (C) 2024 Mac A. Cody

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
 You should have received a copy of the GNU General Public License
 along with this program.  If not, see <http://www.gnu.org/licenses/>.
**/

// Hiragana base table.
//    a       i       u       e       o       n
const uint32_t hiraBase[10][6] =
  {{0x00003042, 0x00003044, 0x00003046, 0x00003048, 0x0000304a, 0x00003093},  // vowel
   {0x0000304b, 0x0000304d, 0x0000304f, 0x00003051, 0x00003053, 0x00000000},  // k
   {0x00003055, 0x00003057, 0x00003059, 0x0000305b, 0x0000305d, 0x00000000},  // s
   {0x0000305f, 0x00003061, 0x00003064, 0x00003066, 0x00003068, 0x00000000},  // t
   {0x0000306a, 0x0000306b, 0x0000306c, 0x0000306d, 0x0000306e, 0x00000000},  // n
   {0x0000306f, 0x00003072, 0x00003075, 0x00003078, 0x0000307b, 0x00000000},  // h
   {0x0000307e, 0x0000307f, 0x00003080, 0x00003081, 0x00003082, 0x00000000},  // m
   {0x00003084, 0x00000000, 0x00003086, 0x00000000, 0x00003088, 0x00000000},  // y
   {0x00003089, 0x0000308a, 0x0000308b, 0x0000308c, 0x0000308d, 0x00000000},  // r
   {0x0000308f, 0x00000000, 0x00000000, 0x00000000, 0x00003092, 0x00000000}}; // w
//    a       i       u       e       o       n

// Hiragana Ten-Ten table.
//    a       i       u       e       o       n
const uint32_t hiraTenTen[10][6] =
  {{0x00000000, 0x00000000, 0x00003094, 0x00000000, 0x00000000, 0x00000000},  // vowel
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
   {0x00000000, 0x00000000, 0x00000000, 0x00000000, 0x00000000, 0x00000000}};

const uint32_t specialKataChi [2][6] =
  {{0x01003005, 0x01003035, 0x010030fb, 0x01003001, 0x0100ff1f, 0x01002026},
   {0x0100300e, 0x0100300f, 0x01003008, 0x01003009, 0x0100203b, 0x00000000}};
