maccody/KanaChordPlus/software/kanji_md.h

/* kanji_md.h */
/**
This file is part of KanaChordPlus Keyboard.
 Copyright (C) 2024 Mac A. Cody

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
 You should have received a copy of the GNU General Public License
 along with this program.  If not, see <http://www.gnu.org/licenses/>.
**/

#ifndef KANJI_METADATA_TYPE
#define KANJI_METADATA_TYPE
typedef struct kanji_md {
  const uint16_t unicode;
  const uint16_t rank;
  const char* const meaning;
} kanji_md;
#endif

const kanji_md kanji_md4E00 = {0x4E00, 1, kanji_ms4E00};
const kanji_md kanji_md5927 = {0x5927, 2, kanji_ms5927};
const kanji_md kanji_md4EBA = {0x4EBA, 3, kanji_ms4EBA};
const kanji_md kanji_md898B = {0x898B, 4, kanji_ms898B};
const kanji_md kanji_md51FA = {0x51FA, 5, kanji_ms51FA};
const kanji_md kanji_md4E2D = {0x4E2D, 6, kanji_ms4E2D};
const kanji_md kanji_md601D = {0x601D, 7, kanji_ms601D};
const kanji_md kanji_md6642 = {0x6642, 8, kanji_ms6642};
const kanji_md kanji_md65E5 = {0x65E5, 9, kanji_ms65E5};
const kanji_md kanji_md4E0A = {0x4E0A, 10, kanji_ms4E0A};
const kanji_md kanji_md6C17 = {0x6C17, 11, kanji_ms6C17};
const kanji_md kanji_md884C = {0x884C, 12, kanji_ms884C};
const kanji_md kanji_md76EE = {0x76EE, 13, kanji_ms76EE};
const kanji_md kanji_md9593 = {0x9593, 14, kanji_ms9593};
const kanji_md kanji_md751F = {0x751F, 15, kanji_ms751F};
const kanji_md kanji_md5F8C = {0x5F8C, 16, kanji_ms5F8C};
const kanji_md kanji_md8A00 = {0x8A00, 17, kanji_ms8A00};
const kanji_md kanji_md5206 = {0x5206, 18, kanji_ms5206};
const kanji_md kanji_md524D = {0x524D, 19, kanji_ms524D};
const kanji_md kanji_md81EA = {0x81EA, 20, kanji_ms81EA};
const kanji_md kanji_md77E5 = {0x77E5, 21, kanji_ms77E5};
const kanji_md kanji_md624B = {0x624B, 22, kanji_ms624B};
const kanji_md kanji_md5168 = {0x5168, 23, kanji_ms5168};
const kanji_md kanji_md672C = {0x672C, 24, kanji_ms672C};
const kanji_md kanji_md6765 = {0x6765, 25, kanji_ms6765};
const kanji_md kanji_md4E8B = {0x4E8B, 26, kanji_ms4E8B};
const kanji_md kanji_md65B9 = {0x65B9, 27, kanji_ms65B9};
const kanji_md kanji_md7269 = {0x7269, 28, kanji_ms7269};
const kanji_md kanji_md4E0B = {0x4E0B, 29, kanji_ms4E0B};
const kanji_md kanji_md610F = {0x610F, 30, kanji_ms610F};
const kanji_md kanji_md5EA6 = {0x5EA6, 31, kanji_ms5EA6};
const kanji_md kanji_md5165 = {0x5165, 32, kanji_ms5165};
const kanji_md kanji_md5B50 = {0x5B50, 33, kanji_ms5B50};
const kanji_md kanji_md4E8C = {0x4E8C, 34, kanji_ms4E8C};
const kanji_md kanji_md8A71 = {0x8A71, 35, kanji_ms8A71};
const kanji_md kanji_md7ACB = {0x7ACB, 36, kanji_ms7ACB};
const kanji_md kanji_md4F53 = {0x4F53, 37, kanji_ms4F53};
const kanji_md kanji_md4E0D = {0x4E0D, 38, kanji_ms4E0D};
const kanji_md kanji_md5FC3 = {0x5FC3, 39, kanji_ms5FC3};
const kanji_md kanji_md8EAB = {0x8EAB, 40, kanji_ms8EAB};
const kanji_md kanji_md660E = {0x660E, 41, kanji_ms660E};
const kanji_md kanji_md4F55 = {0x4F55, 42, kanji_ms4F55};
const kanji_md kanji_md5473 = {0x5473, 43, kanji_ms5473};
const kanji_md kanji_md90E8 = {0x90E8, 44, kanji_ms90E8};
const kanji_md kanji_md5E74 = {0x5E74, 45, kanji_ms5E74};
const kanji_md kanji_md5834 = {0x5834, 46, kanji_ms5834};
const kanji_md kanji_md7121 = {0x7121, 47, kanji_ms7121};
const kanji_md kanji_md6700 = {0x6700, 48, kanji_ms6700};
const kanji_md kanji_md5C0F = {0x5C0F, 49, kanji_ms5C0F};
const kanji_md kanji_md8005 = {0x8005, 50, kanji_ms8005};
const kanji_md kanji_md9577 = {0x9577, 51, kanji_ms9577};
const kanji_md kanji_md901A = {0x901A, 52, kanji_ms901A};
const kanji_md kanji_md540C = {0x540C, 53, kanji_ms540C};
const kanji_md kanji_md611F = {0x611F, 54, kanji_ms611F};
const kanji_md kanji_md5F53 = {0x5F53, 55, kanji_ms5F53};
const kanji_md kanji_md529B = {0x529B, 56, kanji_ms529B};
const kanji_md kanji_md5916 = {0x5916, 57, kanji_ms5916};
const kanji_md kanji_md5730 = {0x5730, 58, kanji_ms5730};
const kanji_md kanji_md9762 = {0x9762, 59, kanji_ms9762};
const kanji_md kanji_md5408 = {0x5408, 60, kanji_ms5408};
const kanji_md kanji_md7406 = {0x7406, 61, kanji_ms7406};
const kanji_md kanji_md4EE5 = {0x4EE5, 62, kanji_ms4EE5};
const kanji_md kanji_md9AD8 = {0x9AD8, 63, kanji_ms9AD8};
const kanji_md kanji_md8FD1 = {0x8FD1, 64, kanji_ms8FD1};
const kanji_md kanji_md4F1A = {0x4F1A, 65, kanji_ms4F1A};
const kanji_md kanji_md6301 = {0x6301, 66, kanji_ms6301};
const kanji_md kanji_md5B9F = {0x5B9F, 67, kanji_ms5B9F};
const kanji_md kanji_md767D = {0x767D, 68, kanji_ms767D};
const kanji_md kanji_md58F0 = {0x58F0, 69, kanji_ms58F0};
const kanji_md kanji_md53E3 = {0x53E3, 70, kanji_ms53E3};
const kanji_md kanji_md5148 = {0x5148, 71, kanji_ms5148};
const kanji_md kanji_md52D5 = {0x52D5, 72, kanji_ms52D5};
const kanji_md kanji_md982D = {0x982D, 73, kanji_ms982D};
const kanji_md kanji_md4ECA = {0x4ECA, 74, kanji_ms4ECA};
const kanji_md kanji_md6240 = {0x6240, 75, kanji_ms6240};
const kanji_md kanji_md6587 = {0x6587, 76, kanji_ms6587};
const kanji_md kanji_md5909 = {0x5909, 77, kanji_ms5909};
const kanji_md kanji_md9854 = {0x9854, 78, kanji_ms9854};
const kanji_md kanji_md4E16 = {0x4E16, 79, kanji_ms4E16};
const kanji_md kanji_md767A = {0x767A, 80, kanji_ms767A};
const kanji_md kanji_md540D = {0x540D, 81, kanji_ms540D};
const kanji_md kanji_md8DB3 = {0x8DB3, 82, kanji_ms8DB3};
const kanji_md kanji_md7684 = {0x7684, 83, kanji_ms7684};
const kanji_md kanji_md8272 = {0x8272, 84, kanji_ms8272};
const kanji_md kanji_md60AA = {0x60AA, 85, kanji_ms60AA};
const kanji_md kanji_md60C5 = {0x60C5, 86, kanji_ms60C5};
const kanji_md kanji_md5207 = {0x5207, 87, kanji_ms5207};
const kanji_md kanji_md7136 = {0x7136, 88, kanji_ms7136};
const kanji_md kanji_md8003 = {0x8003, 89, kanji_ms8003};
const kanji_md kanji_md4F5C = {0x4F5C, 90, kanji_ms4F5C};
const kanji_md kanji_md8FD4 = {0x8FD4, 91, kanji_ms8FD4};
const kanji_md kanji_md843D = {0x843D, 92, kanji_ms843D};
const kanji_md kanji_md7D50 = {0x7D50, 93, kanji_ms7D50};
const kanji_md kanji_md958B = {0x958B, 94, kanji_ms958B};
const kanji_md kanji_md5BB6 = {0x5BB6, 95, kanji_ms5BB6};
const kanji_md kanji_md6B63 = {0x6B63, 96, kanji_ms6B63};
const kanji_md kanji_md98A8 = {0x98A8, 97, kanji_ms98A8};
const kanji_md kanji_md521D = {0x521D, 98, kanji_ms521D};
const kanji_md kanji_md4E09 = {0x4E09, 99, kanji_ms4E09};
const kanji_md kanji_md91CD = {0x91CD, 100, kanji_ms91CD};
const kanji_md kanji_md5C11 = {0x5C11, 101, kanji_ms5C11};
const kanji_md kanji_md5411 = {0x5411, 102, kanji_ms5411};
const kanji_md kanji_md6708 = {0x6708, 103, kanji_ms6708};
const kanji_md kanji_md73FE = {0x73FE, 104, kanji_ms73FE};
const kanji_md kanji_md6570 = {0x6570, 105, kanji_ms6570};
const kanji_md kanji_md7528 = {0x7528, 106, kanji_ms7528};
const kanji_md kanji_md7A7A = {0x7A7A, 107, kanji_ms7A7A};
const kanji_md kanji_md8868 = {0x8868, 108, kanji_ms8868};
const kanji_md kanji_md5185 = {0x5185, 109, kanji_ms5185};
const kanji_md kanji_md97F3 = {0x97F3, 110, kanji_ms97F3};
const kanji_md kanji_md805E = {0x805E, 111, kanji_ms805E};
const kanji_md kanji_md69D8 = {0x69D8, 112, kanji_ms69D8};
const kanji_md kanji_md771F = {0x771F, 113, kanji_ms771F};
const kanji_md kanji_md9053 = {0x9053, 114, kanji_ms9053};
const kanji_md kanji_md7740 = {0x7740, 115, kanji_ms7740};
const kanji_md kanji_md4EE3 = {0x4EE3, 116, kanji_ms4EE3};
const kanji_md kanji_md5973 = {0x5973, 117, kanji_ms5973};
const kanji_md kanji_md76F8 = {0x76F8, 118, kanji_ms76F8};
const kanji_md kanji_md8449 = {0x8449, 119, kanji_ms8449};
const kanji_md kanji_md597D = {0x597D, 120, kanji_ms597D};
const kanji_md kanji_md591A = {0x591A, 121, kanji_ms591A};
const kanji_md kanji_md5B89 = {0x5B89, 122, kanji_ms5B89};
const kanji_md kanji_md554F = {0x554F, 123, kanji_ms554F};
const kanji_md kanji_md5F85 = {0x5F85, 124, kanji_ms5F85};
const kanji_md kanji_md76F4 = {0x76F4, 125, kanji_ms76F4};
const kanji_md kanji_md5B9A = {0x5B9A, 126, kanji_ms5B9A};
const kanji_md kanji_md66F8 = {0x66F8, 127, kanji_ms66F8};
const kanji_md kanji_md4FE1 = {0x4FE1, 128, kanji_ms4FE1};
const kanji_md kanji_md5BFE = {0x5BFE, 129, kanji_ms5BFE};
const kanji_md kanji_md5149 = {0x5149, 130, kanji_ms5149};
const kanji_md kanji_md534A = {0x534A, 131, kanji_ms534A};
const kanji_md kanji_md96C6 = {0x96C6, 132, kanji_ms96C6};
const kanji_md kanji_md5225 = {0x5225, 133, kanji_ms5225};
const kanji_md kanji_md6C7A = {0x6C7A, 134, kanji_ms6C7A};
const kanji_md kanji_md4E3B = {0x4E3B, 135, kanji_ms4E3B};
const kanji_md kanji_md6B69 = {0x6B69, 136, kanji_ms6B69};
const kanji_md kanji_md89E3 = {0x89E3, 137, kanji_ms89E3};
const kanji_md kanji_md6B7B = {0x6B7B, 138, kanji_ms6B7B};
const kanji_md kanji_md6027 = {0x6027, 139, kanji_ms6027};
const kanji_md kanji_md5F37 = {0x5F37, 140, kanji_ms5F37};
const kanji_md kanji_md7F6E = {0x7F6E, 141, kanji_ms7F6E};
const kanji_md kanji_md7B11 = {0x7B11, 142, kanji_ms7B11};
const kanji_md kanji_md98DF = {0x98DF, 143, kanji_ms98DF};
const kanji_md kanji_md6307 = {0x6307, 144, kanji_ms6307};
const kanji_md kanji_md6B8B = {0x6B8B, 145, kanji_ms6B8B};
const kanji_md kanji_md5143 = {0x5143, 146, kanji_ms5143};
const kanji_md kanji_md5C4B = {0x5C4B, 147, kanji_ms5C4B};
const kanji_md kanji_md6D41 = {0x6D41, 148, kanji_ms6D41};
const kanji_md kanji_md65B0 = {0x65B0, 149, kanji_ms65B0};
const kanji_md kanji_md547C = {0x547C, 150, kanji_ms547C};
const kanji_md kanji_md9060 = {0x9060, 151, kanji_ms9060};
const kanji_md kanji_md5341 = {0x5341, 152, kanji_ms5341};
const kanji_md kanji_md4F7F = {0x4F7F, 153, kanji_ms4F7F};
const kanji_md kanji_md7D42 = {0x7D42, 154, kanji_ms7D42};
const kanji_md kanji_md6559 = {0x6559, 155, kanji_ms6559};
const kanji_md kanji_md95A2 = {0x95A2, 156, kanji_ms95A2};
const kanji_md kanji_md606F = {0x606F, 157, kanji_ms606F};
const kanji_md kanji_md914D = {0x914D, 158, kanji_ms914D};
const kanji_md kanji_md8AAC = {0x8AAC, 159, kanji_ms8AAC};
const kanji_md kanji_md795E = {0x795E, 160, kanji_ms795E};
const kanji_md kanji_md53D6 = {0x53D6, 161, kanji_ms53D6};
const kanji_md kanji_md7537 = {0x7537, 162, kanji_ms7537};
const kanji_md kanji_md5929 = {0x5929, 163, kanji_ms5929};
const kanji_md kanji_md8ABF = {0x8ABF, 164, kanji_ms8ABF};
const kanji_md kanji_md6B21 = {0x6B21, 165, kanji_ms6B21};
const kanji_md kanji_md59FF = {0x59FF, 166, kanji_ms59FF};
const kanji_md kanji_md80CC = {0x80CC, 167, kanji_ms80CC};
const kanji_md kanji_md899A = {0x899A, 168, kanji_ms899A};
const kanji_md kanji_md697D = {0x697D, 169, kanji_ms697D};
const kanji_md kanji_md7D76 = {0x7D76, 170, kanji_ms7D76};
const kanji_md kanji_md91D1 = {0x91D1, 171, kanji_ms91D1};
const kanji_md kanji_md60F3 = {0x60F3, 172, kanji_ms60F3};
const kanji_md kanji_md679C = {0x679C, 173, kanji_ms679C};
const kanji_md kanji_md8D77 = {0x8D77, 174, kanji_ms8D77};
const kanji_md kanji_md5F62 = {0x5F62, 175, kanji_ms5F62};
const kanji_md kanji_md5E73 = {0x5E73, 176, kanji_ms5E73};
const kanji_md kanji_md8981 = {0x8981, 177, kanji_ms8981};
const kanji_md kanji_md5F15 = {0x5F15, 178, kanji_ms5F15};
const kanji_md kanji_md547D = {0x547D, 179, kanji_ms547D};
const kanji_md kanji_md904B = {0x904B, 180, kanji_ms904B};
const kanji_md kanji_md82E6 = {0x82E6, 181, kanji_ms82E6};
const kanji_md kanji_md5F97 = {0x5F97, 182, kanji_ms5F97};
const kanji_md kanji_md4ED5 = {0x4ED5, 183, kanji_ms4ED5};
const kanji_md kanji_md591C = {0x591C, 184, kanji_ms591C};
const kanji_md kanji_md4F1D = {0x4F1D, 185, kanji_ms4F1D};
const kanji_md kanji_md653E = {0x653E, 186, kanji_ms653E};
const kanji_md kanji_md5931 = {0x5931, 187, kanji_ms5931};
const kanji_md kanji_md9023 = {0x9023, 188, kanji_ms9023};
const kanji_md kanji_md6DF1 = {0x6DF1, 189, kanji_ms6DF1};
const kanji_md kanji_md7A81 = {0x7A81, 190, kanji_ms7A81};
const kanji_md kanji_md754C = {0x754C, 191, kanji_ms754C};
const kanji_md kanji_md6210 = {0x6210, 192, kanji_ms6210};
const kanji_md kanji_md70B9 = {0x70B9, 193, kanji_ms70B9};
const kanji_md kanji_md65E9 = {0x65E9, 194, kanji_ms65E9};
const kanji_md kanji_md6D88 = {0x6D88, 195, kanji_ms6D88};
const kanji_md kanji_md56DE = {0x56DE, 196, kanji_ms56DE};
const kanji_md kanji_md53D7 = {0x53D7, 197, kanji_ms53D7};
const kanji_md kanji_md5F35 = {0x5F35, 198, kanji_ms5F35};
const kanji_md kanji_md53CD = {0x53CD, 199, kanji_ms53CD};
const kanji_md kanji_md7531 = {0x7531, 200, kanji_ms7531};
const kanji_md kanji_md5B57 = {0x5B57, 201, kanji_ms5B57};
const kanji_md kanji_md5FC5 = {0x5FC5, 202, kanji_ms5FC5};
const kanji_md kanji_md5316 = {0x5316, 203, kanji_ms5316};
const kanji_md kanji_md96E2 = {0x96E2, 204, kanji_ms96E2};
const kanji_md kanji_md7279 = {0x7279, 205, kanji_ms7279};
const kanji_md kanji_md8A18 = {0x8A18, 206, kanji_ms8A18};
const kanji_md kanji_md5728 = {0x5728, 207, kanji_ms5728};
const kanji_md kanji_md904E = {0x904E, 208, kanji_ms904E};
const kanji_md kanji_md4ED6 = {0x4ED6, 209, kanji_ms4ED6};
const kanji_md kanji_md6A5F = {0x6A5F, 210, kanji_ms6A5F};
const kanji_md kanji_md8FFD = {0x8FFD, 211, kanji_ms8FFD};
const kanji_md kanji_md53BB = {0x53BB, 212, kanji_ms53BB};
const kanji_md kanji_md5E30 = {0x5E30, 213, kanji_ms5E30};
const kanji_md kanji_md4E57 = {0x4E57, 214, kanji_ms4E57};
const kanji_md kanji_md6025 = {0x6025, 215, kanji_ms6025};
const kanji_md kanji_md6C34 = {0x6C34, 216, kanji_ms6C34};
const kanji_md kanji_md65AD = {0x65AD, 217, kanji_ms65AD};
const kanji_md kanji_md89AA = {0x89AA, 218, kanji_ms89AA};
const kanji_md kanji_md5B66 = {0x5B66, 219, kanji_ms5B66};
const kanji_md kanji_md4E21 = {0x4E21, 220, kanji_ms4E21};
const kanji_md kanji_md6A2A = {0x6A2A, 221, kanji_ms6A2A};
const kanji_md kanji_md5E83 = {0x5E83, 222, kanji_ms5E83};
const kanji_md kanji_md5E38 = {0x5E38, 223, kanji_ms5E38};
const kanji_md kanji_md5F7C = {0x5F7C, 224, kanji_ms5F7C};
const kanji_md kanji_md8A9E = {0x8A9E, 225, kanji_ms8A9E};
const kanji_md kanji_md8D70 = {0x8D70, 226, kanji_ms8D70};
const kanji_md kanji_md6E80 = {0x6E80, 227, kanji_ms6E80};
const kanji_md kanji_md91CE = {0x91CE, 228, kanji_ms91CE};
const kanji_md kanji_md9996 = {0x9996, 229, kanji_ms9996};
const kanji_md kanji_md5BC4 = {0x5BC4, 230, kanji_ms5BC4};
const kanji_md kanji_md56DB = {0x56DB, 231, kanji_ms56DB};
const kanji_md kanji_md9ED2 = {0x9ED2, 232, kanji_ms9ED2};
const kanji_md kanji_md696D = {0x696D, 233, kanji_ms696D};
const kanji_md kanji_md756A = {0x756A, 234, kanji_ms756A};
const kanji_md kanji_md9032 = {0x9032, 235, kanji_ms9032};
const kanji_md kanji_md984C = {0x984C, 236, kanji_ms984C};
const kanji_md kanji_md7F8E = {0x7F8E, 237, kanji_ms7F8E};
const kanji_md kanji_md6BB5 = {0x6BB5, 238, kanji_ms6BB5};
const kanji_md kanji_md7DDA = {0x7DDA, 239, kanji_ms7DDA};
const kanji_md kanji_md6253 = {0x6253, 240, kanji_ms6253};
const kanji_md kanji_md7D4C = {0x7D4C, 241, kanji_ms7D4C};
const kanji_md kanji_md6697 = {0x6697, 242, kanji_ms6697};
const kanji_md kanji_md7D30 = {0x7D30, 243, kanji_ms7D30};
const kanji_md kanji_md5FF5 = {0x5FF5, 244, kanji_ms5FF5};
const kanji_md kanji_md72B6 = {0x72B6, 245, kanji_ms72B6};
const kanji_md kanji_md671F = {0x671F, 246, kanji_ms671F};
const kanji_md kanji_md9001 = {0x9001, 247, kanji_ms9001};
const kanji_md kanji_md98DB = {0x98DB, 248, kanji_ms98DB};
const kanji_md kanji_md4F3C = {0x4F3C, 249, kanji_ms4F3C};
const kanji_md kanji_md6709 = {0x6709, 250, kanji_ms6709};
const kanji_md kanji_md7D20 = {0x7D20, 251, kanji_ms7D20};
const kanji_md kanji_md7B54 = {0x7B54, 252, kanji_ms7B54};
const kanji_md kanji_md8AAD = {0x8AAD, 253, kanji_ms8AAD};
const kanji_md kanji_md544A = {0x544A, 254, kanji_ms544A};
const kanji_md kanji_md611B = {0x611B, 255, kanji_ms611B};
const kanji_md kanji_md6B62 = {0x6B62, 256, kanji_ms6B62};
const kanji_md kanji_md9003 = {0x9003, 257, kanji_ms9003};
const kanji_md kanji_md6D6E = {0x6D6E, 258, kanji_ms6D6E};
const kanji_md kanji_md683C = {0x683C, 259, kanji_ms683C};
const kanji_md kanji_md51B7 = {0x51B7, 260, kanji_ms51B7};
const kanji_md kanji_md8D64 = {0x8D64, 261, kanji_ms8D64};
const kanji_md kanji_md78BA = {0x78BA, 262, kanji_ms78BA};
const kanji_md kanji_md8033 = {0x8033, 263, kanji_ms8033};
const kanji_md kanji_md59CB = {0x59CB, 264, kanji_ms59CB};
const kanji_md kanji_md52DD = {0x52DD, 265, kanji_ms52DD};
const kanji_md kanji_md80FD = {0x80FD, 266, kanji_ms80FD};
const kanji_md kanji_md4E94 = {0x4E94, 267, kanji_ms4E94};
const kanji_md kanji_md6CE8 = {0x6CE8, 268, kanji_ms6CE8};
const kanji_md kanji_md5C71 = {0x5C71, 269, kanji_ms5C71};
const kanji_md kanji_md8EE2 = {0x8EE2, 270, kanji_ms8EE2};
const kanji_md kanji_md5FDC = {0x5FDC, 271, kanji_ms5FDC};
const kanji_md kanji_md5FD8 = {0x5FD8, 272, kanji_ms5FD8};
const kanji_md kanji_md5B58 = {0x5B58, 273, kanji_ms5B58};
const kanji_md kanji_md614B = {0x614B, 274, kanji_ms614B};
const kanji_md kanji_md670D = {0x670D, 275, kanji_ms670D};
const kanji_md kanji_md6839 = {0x6839, 276, kanji_ms6839};
const kanji_md kanji_md539F = {0x539F, 277, kanji_ms539F};
const kanji_md kanji_md671B = {0x671B, 278, kanji_ms671B};
const kanji_md kanji_md7247 = {0x7247, 279, kanji_ms7247};
const kanji_md kanji_md5012 = {0x5012, 280, kanji_ms5012};
const kanji_md kanji_md6050 = {0x6050, 281, kanji_ms6050};
const kanji_md kanji_md9759 = {0x9759, 282, kanji_ms9759};
const kanji_md kanji_md7B2C = {0x7B2C, 283, kanji_ms7B2C};
const kanji_md kanji_md671D = {0x671D, 284, kanji_ms671D};
const kanji_md kanji_md53F0 = {0x53F0, 285, kanji_ms53F0};
const kanji_md kanji_md8B70 = {0x8B70, 286, kanji_ms8B70};
const kanji_md kanji_md62BC = {0x62BC, 287, kanji_ms62BC};
const kanji_md kanji_md9752 = {0x9752, 288, kanji_ms9752};
const kanji_md kanji_md6CD5 = {0x6CD5, 289, kanji_ms6CD5};
const kanji_md kanji_md6D3B = {0x6D3B, 290, kanji_ms6D3B};
const kanji_md kanji_md9CF4 = {0x9CF4, 291, kanji_ms9CF4};
const kanji_md kanji_md7D44 = {0x7D44, 292, kanji_ms7D44};
const kanji_md kanji_md5177 = {0x5177, 293, kanji_ms5177};
const kanji_md kanji_md592B = {0x592B, 294, kanji_ms592B};
const kanji_md kanji_md8A08 = {0x8A08, 295, kanji_ms8A08};
const kanji_md kanji_md4ED8 = {0x4ED8, 296, kanji_ms4ED8};
const kanji_md kanji_md54C1 = {0x54C1, 297, kanji_ms54C1};
const kanji_md kanji_md60B2 = {0x60B2, 298, kanji_ms60B2};
const kanji_md kanji_md52A0 = {0x52A0, 299, kanji_ms52A0};
const kanji_md kanji_md7D04 = {0x7D04, 300, kanji_ms7D04};
const kanji_md kanji_md5EA7 = {0x5EA7, 301, kanji_ms5EA7};
const kanji_md kanji_md52E2 = {0x52E2, 302, kanji_ms52E2};
const kanji_md kanji_md4EA4 = {0x4EA4, 303, kanji_ms4EA4};
const kanji_md kanji_md53EF = {0x53EF, 304, kanji_ms53EF};
const kanji_md kanji_md80F8 = {0x80F8, 305, kanji_ms80F8};
const kanji_md kanji_md8996 = {0x8996, 306, kanji_ms8996};
const kanji_md kanji_md53E4 = {0x53E4, 307, kanji_ms53E4};
const kanji_md kanji_md5999 = {0x5999, 308, kanji_ms5999};
const kanji_md kanji_md71B1 = {0x71B1, 309, kanji_ms71B1};
const kanji_md kanji_md4E88 = {0x4E88, 310, kanji_ms4E88};
const kanji_md kanji_md8CEA = {0x8CEA, 311, kanji_ms8CEA};
const kanji_md kanji_md6728 = {0x6728, 312, kanji_ms6728};
const kanji_md kanji_md629C = {0x629C, 313, kanji_ms629C};
const kanji_md kanji_md5074 = {0x5074, 314, kanji_ms5074};
const kanji_md kanji_md5229 = {0x5229, 315, kanji_ms5229};
const kanji_md kanji_md9858 = {0x9858, 316, kanji_ms9858};
const kanji_md kanji_md5F71 = {0x5F71, 317, kanji_ms5F71};
const kanji_md kanji_md6BBA = {0x6BBA, 318, kanji_ms6BBA};
const kanji_md kanji_md5922 = {0x5922, 319, kanji_ms5922};
const kanji_md kanji_md592A = {0x592A, 320, kanji_ms592A};
const kanji_md kanji_md5F79 = {0x5F79, 321, kanji_ms5F79};
const kanji_md kanji_md8B58 = {0x8B58, 322, kanji_ms8B58};
const kanji_md kanji_md5B88 = {0x5B88, 323, kanji_ms5B88};
const kanji_md kanji_md5E95 = {0x5E95, 324, kanji_ms5E95};
const kanji_md kanji_md9650 = {0x9650, 325, kanji_ms9650};
const kanji_md kanji_md9014 = {0x9014, 326, kanji_ms9014};
const kanji_md kanji_md6563 = {0x6563, 327, kanji_ms6563};
const kanji_md kanji_md8840 = {0x8840, 328, kanji_ms8840};
const kanji_md kanji_md7D9A = {0x7D9A, 329, kanji_ms7D9A};
const kanji_md kanji_md5C45 = {0x5C45, 330, kanji_ms5C45};
const kanji_md kanji_md88CF = {0x88CF, 331, kanji_ms88CF};
const kanji_md kanji_md8EFD = {0x8EFD, 332, kanji_ms8EFD};
const kanji_md kanji_md4E71 = {0x4E71, 333, kanji_ms4E71};
const kanji_md kanji_md4F4F = {0x4F4F, 334, kanji_ms4F4F};
const kanji_md kanji_md5DEE = {0x5DEE, 335, kanji_ms5DEE};
const kanji_md kanji_md5BB9 = {0x5BB9, 336, kanji_ms5BB9};
const kanji_md kanji_md7AEF = {0x7AEF, 337, kanji_ms7AEF};
const kanji_md kanji_md82E5 = {0x82E5, 338, kanji_ms82E5};
const kanji_md kanji_md969B = {0x969B, 339, kanji_ms969B};
const kanji_md kanji_md6295 = {0x6295, 340, kanji_ms6295};
const kanji_md kanji_md4FC2 = {0x4FC2, 341, kanji_ms4FC2};
const kanji_md kanji_md96E3 = {0x96E3, 342, kanji_ms96E3};
const kanji_md kanji_md5358 = {0x5358, 343, kanji_ms5358};
const kanji_md kanji_md56F2 = {0x56F2, 344, kanji_ms56F2};
const kanji_md kanji_md8CA0 = {0x8CA0, 345, kanji_ms8CA0};
const kanji_md kanji_md516B = {0x516B, 346, kanji_ms516B};
const kanji_md kanji_md5668 = {0x5668, 347, kanji_ms5668};
const kanji_md kanji_md666F = {0x666F, 348, kanji_ms666F};
const kanji_md kanji_md5965 = {0x5965, 349, kanji_ms5965};
const kanji_md kanji_md5DFB = {0x5DFB, 350, kanji_ms5DFB};
const kanji_md kanji_md56FD = {0x56FD, 351, kanji_ms56FD};
const kanji_md kanji_md52A9 = {0x52A9, 352, kanji_ms52A9};
const kanji_md kanji_md7CBE = {0x7CBE, 353, kanji_ms7CBE};
const kanji_md kanji_md62B1 = {0x62B1, 354, kanji_ms62B1};
const kanji_md kanji_md7834 = {0x7834, 355, kanji_ms7834};
const kanji_md kanji_md9055 = {0x9055, 356, kanji_ms9055};
const kanji_md kanji_md75DB = {0x75DB, 357, kanji_ms75DB};
const kanji_md kanji_md5BA4 = {0x5BA4, 358, kanji_ms5BA4};
const kanji_md kanji_md8155 = {0x8155, 359, kanji_ms8155};
const kanji_md kanji_md6E21 = {0x6E21, 360, kanji_ms6E21};
const kanji_md kanji_md50CF = {0x50CF, 361, kanji_ms50CF};
const kanji_md kanji_md9054 = {0x9054, 362, kanji_ms9054};
const kanji_md kanji_md983C = {0x983C, 363, kanji_ms983C};
const kanji_md kanji_md8179 = {0x8179, 364, kanji_ms8179};
const kanji_md kanji_md4F8B = {0x4F8B, 365, kanji_ms4F8B};
const kanji_md kanji_md53F3 = {0x53F3, 366, kanji_ms53F3};
const kanji_md kanji_md8208 = {0x8208, 367, kanji_ms8208};
const kanji_md kanji_md706B = {0x706B, 368, kanji_ms706B};
const kanji_md kanji_md793C = {0x793C, 369, kanji_ms793C};
const kanji_md kanji_md523B = {0x523B, 370, kanji_ms523B};
const kanji_md kanji_md5BDD = {0x5BDD, 371, kanji_ms5BDD};
const kanji_md kanji_md53CB = {0x53CB, 372, kanji_ms53CB};
const kanji_md kanji_md5272 = {0x5272, 373, kanji_ms5272};
const kanji_md kanji_md8DEF = {0x8DEF, 374, kanji_ms8DEF};
const kanji_md kanji_md7570 = {0x7570, 375, kanji_ms7570};
const kanji_md kanji_md5F0F = {0x5F0F, 376, kanji_ms5F0F};
const kanji_md kanji_md4F59 = {0x4F59, 377, kanji_ms4F59};
const kanji_md kanji_md56F0 = {0x56F0, 378, kanji_ms56F0};
const kanji_md kanji_md632F = {0x632F, 379, kanji_ms632F};
const kanji_md kanji_md89D2 = {0x89D2, 380, kanji_ms89D2};
const kanji_md kanji_md8AC7 = {0x8AC7, 381, kanji_ms8AC7};
const kanji_md kanji_md675F = {0x675F, 382, kanji_ms675F};
const kanji_md kanji_md6539 = {0x6539, 383, kanji_ms6539};
const kanji_md kanji_md516D = {0x516D, 384, kanji_ms516D};
const kanji_md kanji_md5E78 = {0x5E78, 385, kanji_ms5E78};
const kanji_md kanji_md6298 = {0x6298, 386, kanji_ms6298};
const kanji_md kanji_md6848 = {0x6848, 387, kanji_ms6848};
const kanji_md kanji_md5F31 = {0x5F31, 388, kanji_ms5F31};
const kanji_md kanji_md58EB = {0x58EB, 389, kanji_ms58EB};
const kanji_md kanji_md571F = {0x571F, 390, kanji_ms571F};
const kanji_md kanji_md8089 = {0x8089, 391, kanji_ms8089};
const kanji_md kanji_md7A2E = {0x7A2E, 392, kanji_ms7A2E};
const kanji_md kanji_md8D8A = {0x8D8A, 393, kanji_ms8D8A};
const kanji_md kanji_md77F3 = {0x77F3, 394, kanji_ms77F3};
const kanji_md kanji_md6012 = {0x6012, 395, kanji_ms6012};
const kanji_md kanji_md652F = {0x652F, 396, kanji_ms652F};
const kanji_md kanji_md56F3 = {0x56F3, 397, kanji_ms56F3};
const kanji_md kanji_md767E = {0x767E, 398, kanji_ms767E};
const kanji_md kanji_md4E03 = {0x4E03, 399, kanji_ms4E03};
const kanji_md kanji_md88C5 = {0x88C5, 400, kanji_ms88C5};
const kanji_md kanji_md826F = {0x826F, 401, kanji_ms826F};
const kanji_md kanji_md964D = {0x964D, 402, kanji_ms964D};
const kanji_md kanji_md9ED9 = {0x9ED9, 403, kanji_ms9ED9};
const kanji_md kanji_md9589 = {0x9589, 404, kanji_ms9589};
const kanji_md kanji_md4F11 = {0x4F11, 405, kanji_ms4F11};
const kanji_md kanji_md5224 = {0x5224, 406, kanji_ms5224};
const kanji_md kanji_md80A9 = {0x80A9, 407, kanji_ms80A9};
const kanji_md kanji_md7167 = {0x7167, 408, kanji_ms7167};
const kanji_md kanji_md5DE6 = {0x5DE6, 409, kanji_ms5DE6};
const kanji_md kanji_md8A31 = {0x8A31, 410, kanji_ms8A31};
const kanji_md kanji_md7D19 = {0x7D19, 411, kanji_ms7D19};
const kanji_md kanji_md4F9B = {0x4F9B, 412, kanji_ms4F9B};
const kanji_md kanji_md77AC = {0x77AC, 413, kanji_ms77AC};
const kanji_md kanji_md6599 = {0x6599, 414, kanji_ms6599};
const kanji_md kanji_md548C = {0x548C, 415, kanji_ms548C};
const kanji_md kanji_md4F4D = {0x4F4D, 416, kanji_ms4F4D};
const kanji_md kanji_md968E = {0x968E, 417, kanji_ms968E};
const kanji_md kanji_md96D1 = {0x96D1, 418, kanji_ms96D1};
const kanji_md kanji_md985E = {0x985E, 419, kanji_ms985E};
const kanji_md kanji_md8FF7 = {0x8FF7, 420, kanji_ms8FF7};
const kanji_md kanji_md98F2 = {0x98F2, 421, kanji_ms98F2};
const kanji_md kanji_md672B = {0x672B, 422, kanji_ms672B};
const kanji_md kanji_md4E26 = {0x4E26, 423, kanji_ms4E26};
const kanji_md kanji_md4EF6 = {0x4EF6, 424, kanji_ms4EF6};
const kanji_md kanji_md4EF2 = {0x4EF2, 425, kanji_ms4EF2};
const kanji_md kanji_md9000 = {0x9000, 426, kanji_ms9000};
const kanji_md kanji_md89B3 = {0x89B3, 427, kanji_ms89B3};
const kanji_md kanji_md821E = {0x821E, 428, kanji_ms821E};
const kanji_md kanji_md5BC6 = {0x5BC6, 429, kanji_ms5BC6};
const kanji_md kanji_md9AEA = {0x9AEA, 430, kanji_ms9AEA};
const kanji_md kanji_md5831 = {0x5831, 431, kanji_ms5831};
const kanji_md kanji_md5947 = {0x5947, 432, kanji_ms5947};
const kanji_md kanji_md9006 = {0x9006, 433, kanji_ms9006};
const kanji_md kanji_md516C = {0x516C, 434, kanji_ms516C};
const kanji_md kanji_md5439 = {0x5439, 435, kanji_ms5439};
const kanji_md kanji_md4E07 = {0x4E07, 436, kanji_ms4E07};
const kanji_md kanji_md5371 = {0x5371, 437, kanji_ms5371};
const kanji_md kanji_md8170 = {0x8170, 438, kanji_ms8170};
const kanji_md kanji_md5B8C = {0x5B8C, 439, kanji_ms5B8C};
const kanji_md kanji_md60D1 = {0x60D1, 440, kanji_ms60D1};
const kanji_md kanji_md6FC0 = {0x6FC0, 441, kanji_ms6FC0};
const kanji_md kanji_md90FD = {0x90FD, 442, kanji_ms90FD};
const kanji_md kanji_md77ED = {0x77ED, 443, kanji_ms77ED};
const kanji_md kanji_md6226 = {0x6226, 444, kanji_ms6226};
const kanji_md kanji_md9A5A = {0x9A5A, 445, kanji_ms9A5A};
const kanji_md kanji_md4FDD = {0x4FDD, 446, kanji_ms4FDD};
const kanji_md kanji_md75C5 = {0x75C5, 447, kanji_ms75C5};
const kanji_md kanji_md79C1 = {0x79C1, 448, kanji_ms79C1};
const kanji_md kanji_md8A3C = {0x8A3C, 449, kanji_ms8A3C};
const kanji_md kanji_md8ECA = {0x8ECA, 450, kanji_ms8ECA};
const kanji_md kanji_md753B = {0x753B, 451, kanji_ms753B};
const kanji_md kanji_md6B32 = {0x6B32, 452, kanji_ms6B32};
const kanji_md kanji_md4EFB = {0x4EFB, 453, kanji_ms4EFB};
const kanji_md kanji_md8CB7 = {0x8CB7, 454, kanji_ms8CB7};
const kanji_md kanji_md72EC = {0x72EC, 455, kanji_ms72EC};
const kanji_md kanji_md9B54 = {0x9B54, 456, kanji_ms9B54};
const kanji_md kanji_md904A = {0x904A, 457, kanji_ms904A};
const kanji_md kanji_md4F4E = {0x4F4E, 458, kanji_ms4F4E};
const kanji_md kanji_md9580 = {0x9580, 459, kanji_ms9580};
const kanji_md kanji_md69CB = {0x69CB, 460, kanji_ms69CB};
const kanji_md kanji_md99AC = {0x99AC, 461, kanji_ms99AC};
const kanji_md kanji_md5BA2 = {0x5BA2, 462, kanji_ms5BA2};
const kanji_md kanji_md793A = {0x793A, 463, kanji_ms793A};
const kanji_md kanji_md7591 = {0x7591, 464, kanji_ms7591};
const kanji_md kanji_md6C42 = {0x6C42, 465, kanji_ms6C42};
const kanji_md kanji_md512A = {0x512A, 466, kanji_ms512A};
const kanji_md kanji_md6BCD = {0x6BCD, 467, kanji_ms6BCD};
const kanji_md kanji_md7720 = {0x7720, 468, kanji_ms7720};
const kanji_md kanji_md8584 = {0x8584, 469, kanji_ms8584};
const kanji_md kanji_md8E0F = {0x8E0F, 470, kanji_ms8E0F};
const kanji_md kanji_md8A8D = {0x8A8D, 471, kanji_ms8A8D};
const kanji_md kanji_md5FAE = {0x5FAE, 472, kanji_ms5FAE};
const kanji_md kanji_md5099 = {0x5099, 473, kanji_ms5099};
const kanji_md kanji_md52B4 = {0x52B4, 474, kanji_ms52B4};
const kanji_md kanji_md5ACC = {0x5ACC, 475, kanji_ms5ACC};
const kanji_md kanji_md7533 = {0x7533, 476, kanji_ms7533};
const kanji_md kanji_md5BDF = {0x5BDF, 477, kanji_ms5BDF};
const kanji_md kanji_md5236 = {0x5236, 478, kanji_ms5236};
const kanji_md kanji_md79FB = {0x79FB, 479, kanji_ms79FB};
const kanji_md kanji_md8FBC = {0x8FBC, 480, kanji_ms8FBC};
const kanji_md kanji_md7236 = {0x7236, 481, kanji_ms7236};
const kanji_md kanji_md82B1 = {0x82B1, 482, kanji_ms82B1};
const kanji_md kanji_md518D = {0x518D, 483, kanji_ms518D};
const kanji_md kanji_md559C = {0x559C, 484, kanji_ms559C};
const kanji_md kanji_md58F2 = {0x58F2, 485, kanji_ms58F2};
const kanji_md kanji_md50B7 = {0x50B7, 486, kanji_ms50B7};
const kanji_md kanji_md6B73 = {0x6B73, 487, kanji_ms6B73};
const kanji_md kanji_md58C1 = {0x58C1, 488, kanji_ms58C1};
const kanji_md kanji_md8336 = {0x8336, 489, kanji_ms8336};
const kanji_md kanji_md65CF = {0x65CF, 490, kanji_ms65CF};
const kanji_md kanji_md713C = {0x713C, 491, kanji_ms713C};
const kanji_md kanji_md4ECB = {0x4ECB, 492, kanji_ms4ECB};
const kanji_md kanji_md8FBA = {0x8FBA, 493, kanji_ms8FBA};
const kanji_md kanji_md66AE = {0x66AE, 494, kanji_ms66AE};
const kanji_md kanji_md6C88 = {0x6C88, 495, kanji_ms6C88};
const kanji_md kanji_md7B4B = {0x7B4B, 496, kanji_ms7B4B};
const kanji_md kanji_md6211 = {0x6211, 497, kanji_ms6211};
const kanji_md kanji_md6255 = {0x6255, 498, kanji_ms6255};
const kanji_md kanji_md5468 = {0x5468, 499, kanji_ms5468};
const kanji_md kanji_md975E = {0x975E, 500, kanji_ms975E};
const kanji_md kanji_md672A = {0x672A, 501, kanji_ms672A};
const kanji_md kanji_md7FA9 = {0x7FA9, 502, kanji_ms7FA9};
const kanji_md kanji_md663C = {0x663C, 503, kanji_ms663C};
const kanji_md kanji_md54E1 = {0x54E1, 504, kanji_ms54E1};
const kanji_md kanji_md5915 = {0x5915, 505, kanji_ms5915};
const kanji_md kanji_md5E8A = {0x5E8A, 506, kanji_ms5E8A};
const kanji_md kanji_md6483 = {0x6483, 507, kanji_ms6483};
const kanji_md kanji_md8AD6 = {0x8AD6, 508, kanji_ms8AD6};
const kanji_md kanji_md63A2 = {0x63A2, 509, kanji_ms63A2};
const kanji_md kanji_md53C2 = {0x53C2, 510, kanji_ms53C2};
const kanji_md kanji_md96A0 = {0x96A0, 511, kanji_ms96A0};
const kanji_md kanji_md9020 = {0x9020, 512, kanji_ms9020};
const kanji_md kanji_md5370 = {0x5370, 513, kanji_ms5370};
const kanji_md kanji_md5EFA = {0x5EFA, 514, kanji_ms5EFA};
const kanji_md kanji_md8853 = {0x8853, 515, kanji_ms8853};
const kanji_md kanji_md63A5 = {0x63A5, 516, kanji_ms63A5};
const kanji_md kanji_md5C40 = {0x5C40, 517, kanji_ms5C40};
const kanji_md kanji_md6BDB = {0x6BDB, 518, kanji_ms6BDB};
const kanji_md kanji_md5E2F = {0x5E2F, 519, kanji_ms5E2F};
const kanji_md kanji_md6D3E = {0x6D3E, 520, kanji_ms6D3E};
const kanji_md kanji_md8C61 = {0x8C61, 521, kanji_ms8C61};
const kanji_md kanji_md523A = {0x523A, 522, kanji_ms523A};
const kanji_md kanji_md6CE3 = {0x6CE3, 523, kanji_ms6CE3};
const kanji_md kanji_md6238 = {0x6238, 524, kanji_ms6238};
const kanji_md kanji_md5438 = {0x5438, 525, kanji_ms5438};
const kanji_md kanji_md6614 = {0x6614, 526, kanji_ms6614};
const kanji_md kanji_md6016 = {0x6016, 527, kanji_ms6016};
const kanji_md kanji_md9078 = {0x9078, 528, kanji_ms9078};
const kanji_md kanji_md773C = {0x773C, 529, kanji_ms773C};
const kanji_md kanji_md8349 = {0x8349, 530, kanji_ms8349};
const kanji_md kanji_md9A12 = {0x9A12, 531, kanji_ms9A12};
const kanji_md kanji_md5FEB = {0x5FEB, 532, kanji_ms5FEB};
const kanji_md kanji_md56FA = {0x56FA, 533, kanji_ms56FA};
const kanji_md kanji_md6BCE = {0x6BCE, 534, kanji_ms6BCE};
const kanji_md kanji_md9A13 = {0x9A13, 535, kanji_ms9A13};
const kanji_md kanji_md79D8 = {0x79D8, 536, kanji_ms79D8};
const kanji_md kanji_md6D77 = {0x6D77, 537, kanji_ms6D77};
const kanji_md kanji_md89E6 = {0x89E6, 538, kanji_ms89E6};
const kanji_md kanji_md6545 = {0x6545, 539, kanji_ms6545};
const kanji_md kanji_md8131 = {0x8131, 540, kanji_ms8131};
const kanji_md kanji_md967A = {0x967A, 541, kanji_ms967A};
const kanji_md kanji_md97FF = {0x97FF, 542, kanji_ms97FF};
const kanji_md kanji_md9F3B = {0x9F3B, 543, kanji_ms9F3B};
const kanji_md kanji_md5C48 = {0x5C48, 544, kanji_ms5C48};
const kanji_md kanji_md793E = {0x793E, 545, kanji_ms793E};
const kanji_md kanji_md4E08 = {0x4E08, 546, kanji_ms4E08};
const kanji_md kanji_md5305 = {0x5305, 547, kanji_ms5305};
const kanji_md kanji_md6DF7 = {0x6DF7, 548, kanji_ms6DF7};
const kanji_md kanji_md8FCE = {0x8FCE, 549, kanji_ms8FCE};
const kanji_md kanji_md4E38 = {0x4E38, 550, kanji_ms4E38};
const kanji_md kanji_md4E5D = {0x4E5D, 551, kanji_ms4E5D};
const kanji_md kanji_md5171 = {0x5171, 552, kanji_ms5171};
const kanji_md kanji_md5343 = {0x5343, 553, kanji_ms5343};
const kanji_md kanji_md5E03 = {0x5E03, 554, kanji_ms5E03};
const kanji_md kanji_md8352 = {0x8352, 555, kanji_ms8352};
const kanji_md kanji_md5E2B = {0x5E2B, 556, kanji_ms5E2B};
const kanji_md kanji_md5E2D = {0x5E2D, 557, kanji_ms5E2D};
const kanji_md kanji_md50CD = {0x50CD, 558, kanji_ms50CD};
const kanji_md kanji_md7D0D = {0x7D0D, 559, kanji_ms7D0D};
const kanji_md kanji_md7A0B = {0x7A0B, 560, kanji_ms7A0B};
const kanji_md kanji_md6975 = {0x6975, 561, kanji_ms6975};
const kanji_md kanji_md66F2 = {0x66F2, 562, kanji_ms66F2};
const kanji_md kanji_md901F = {0x901F, 563, kanji_ms901F};
const kanji_md kanji_md63E1 = {0x63E1, 564, kanji_ms63E1};
const kanji_md kanji_md967D = {0x967D, 565, kanji_ms967D};
const kanji_md kanji_md66B4 = {0x66B4, 566, kanji_ms66B4};
const kanji_md kanji_md53F7 = {0x53F7, 567, kanji_ms53F7};
const kanji_md kanji_md7A4D = {0x7A4D, 568, kanji_ms7A4D};
const kanji_md kanji_md53EB = {0x53EB, 569, kanji_ms53EB};
const kanji_md kanji_md80B2 = {0x80B2, 570, kanji_ms80B2};
const kanji_md kanji_md5EAD = {0x5EAD, 571, kanji_ms5EAD};
const kanji_md kanji_md9AA8 = {0x9AA8, 572, kanji_ms9AA8};
const kanji_md kanji_md7A93 = {0x7A93, 573, kanji_ms7A93};
const kanji_md kanji_md6575 = {0x6575, 574, kanji_ms6575};
const kanji_md kanji_md56E3 = {0x56E3, 575, kanji_ms56E3};
const kanji_md kanji_md7523 = {0x7523, 576, kanji_ms7523};
const kanji_md kanji_md602A = {0x602A, 577, kanji_ms602A};
const kanji_md kanji_md76AE = {0x76AE, 578, kanji_ms76AE};
const kanji_md kanji_md7E01 = {0x7E01, 579, kanji_ms7E01};
const kanji_md kanji_md6368 = {0x6368, 580, kanji_ms6368};
const kanji_md kanji_md5BBF = {0x5BBF, 581, kanji_ms5BBF};
const kanji_md kanji_md67C4 = {0x67C4, 582, kanji_ms67C4};
const kanji_md kanji_md90AA = {0x90AA, 583, kanji_ms90AA};
const kanji_md kanji_md53CE = {0x53CE, 584, kanji_ms53CE};
const kanji_md kanji_md8001 = {0x8001, 585, kanji_ms8001};
const kanji_md kanji_md6CBB = {0x6CBB, 586, kanji_ms6CBB};
const kanji_md kanji_md53E5 = {0x53E5, 587, kanji_ms53E5};
const kanji_md kanji_md7FD2 = {0x7FD2, 588, kanji_ms7FD2};
const kanji_md kanji_md8FEB = {0x8FEB, 589, kanji_ms8FEB};
const kanji_md kanji_md6771 = {0x6771, 590, kanji_ms6771};
const kanji_md kanji_md5DE5 = {0x5DE5, 591, kanji_ms5DE5};
const kanji_md kanji_md91CF = {0x91CF, 592, kanji_ms91CF};
const kanji_md kanji_md8CAC = {0x8CAC, 593, kanji_ms8CAC};
const kanji_md kanji_md7B49 = {0x7B49, 594, kanji_ms7B49};
const kanji_md kanji_md76DB = {0x76DB, 595, kanji_ms76DB};
const kanji_md kanji_md7C21 = {0x7C21, 596, kanji_ms7C21};
const kanji_md kanji_md6BD4 = {0x6BD4, 597, kanji_ms6BD4};
const kanji_md kanji_md4E95 = {0x4E95, 598, kanji_ms4E95};
const kanji_md kanji_md6620 = {0x6620, 599, kanji_ms6620};
const kanji_md kanji_md52D9 = {0x52D9, 600, kanji_ms52D9};
const kanji_md kanji_md5F93 = {0x5F93, 601, kanji_ms5F93};
const kanji_md kanji_md4E0E = {0x4E0E, 602, kanji_ms4E0E};
const kanji_md kanji_md75B2 = {0x75B2, 603, kanji_ms75B2};
const kanji_md kanji_md8A2A = {0x8A2A, 604, kanji_ms8A2A};
const kanji_md kanji_md7BC0 = {0x7BC0, 605, kanji_ms7BC0};
const kanji_md kanji_md5410 = {0x5410, 606, kanji_ms5410};
const kanji_md kanji_md679A = {0x679A, 607, kanji_ms679A};
const kanji_md kanji_md6CE2 = {0x6CE2, 608, kanji_ms6CE2};
const kanji_md kanji_md67D3 = {0x67D3, 609, kanji_ms67D3};
const kanji_md kanji_md5C04 = {0x5C04, 610, kanji_ms5C04};
const kanji_md kanji_md65C5 = {0x65C5, 611, kanji_ms65C5};
const kanji_md kanji_md9045 = {0x9045, 612, kanji_ms9045};
const kanji_md kanji_md541B = {0x541B, 613, kanji_ms541B};
const kanji_md kanji_md8A98 = {0x8A98, 614, kanji_ms8A98};
const kanji_md kanji_md7559 = {0x7559, 615, kanji_ms7559};
const kanji_md kanji_md53B3 = {0x53B3, 616, kanji_ms53B3};
const kanji_md kanji_md6D17 = {0x6D17, 617, kanji_ms6D17};
const kanji_md kanji_md6B20 = {0x6B20, 618, kanji_ms6B20};
const kanji_md kanji_md6577 = {0x6577, 619, kanji_ms6577};
const kanji_md kanji_md8077 = {0x8077, 620, kanji_ms8077};
const kanji_md kanji_md5BB3 = {0x5BB3, 621, kanji_ms5BB3};
const kanji_md kanji_md5897 = {0x5897, 622, kanji_ms5897};
const kanji_md kanji_md8DE1 = {0x8DE1, 623, kanji_ms8DE1};
const kanji_md kanji_md5883 = {0x5883, 624, kanji_ms5883};
const kanji_md kanji_md8F2A = {0x8F2A, 625, kanji_ms8F2A};
const kanji_md kanji_md7F6A = {0x7F6A, 626, kanji_ms7F6A};
const kanji_md kanji_md6162 = {0x6162, 627, kanji_ms6162};
const kanji_md kanji_md5FA9 = {0x5FA9, 628, kanji_ms5FA9};
const kanji_md kanji_md501F = {0x501F, 629, kanji_ms501F};
const kanji_md kanji_md4E45 = {0x4E45, 630, kanji_ms4E45};
const kanji_md kanji_md5A18 = {0x5A18, 631, kanji_ms5A18};
const kanji_md kanji_md51E6 = {0x51E6, 632, kanji_ms51E6};
const kanji_md kanji_md6EC5 = {0x6EC5, 633, kanji_ms6EC5};
const kanji_md kanji_md9664 = {0x9664, 634, kanji_ms9664};
const kanji_md kanji_md500B = {0x500B, 635, kanji_ms500B};
const kanji_md kanji_md99C6 = {0x99C6, 636, kanji_ms99C6};
const kanji_md kanji_md7DD2 = {0x7DD2, 637, kanji_ms7DD2};
const kanji_md kanji_md9244 = {0x9244, 638, kanji_ms9244};
const kanji_md kanji_md61B6 = {0x61B6, 639, kanji_ms61B6};
const kanji_md kanji_md72C2 = {0x72C2, 640, kanji_ms72C2};
const kanji_md kanji_md6674 = {0x6674, 641, kanji_ms6674};
const kanji_md kanji_md6297 = {0x6297, 642, kanji_ms6297};
const kanji_md kanji_md62E0 = {0x62E0, 643, kanji_ms62E0};
const kanji_md kanji_md767B = {0x767B, 644, kanji_ms767B};
const kanji_md kanji_md56E0 = {0x56E0, 645, kanji_ms56E0};
const kanji_md kanji_md5100 = {0x5100, 646, kanji_ms5100};
const kanji_md kanji_md677F = {0x677F, 647, kanji_ms677F};
const kanji_md kanji_md7518 = {0x7518, 648, kanji_ms7518};
const kanji_md kanji_md6557 = {0x6557, 649, kanji_ms6557};
const kanji_md kanji_md7DF4 = {0x7DF4, 650, kanji_ms7DF4};
const kanji_md kanji_md578B = {0x578B, 651, kanji_ms578B};
const kanji_md kanji_md4E89 = {0x4E89, 652, kanji_ms4E89};
const kanji_md kanji_md984D = {0x984D, 653, kanji_ms984D};
const kanji_md kanji_md9670 = {0x9670, 654, kanji_ms9670};
const kanji_md kanji_md6628 = {0x6628, 655, kanji_ms6628};
const kanji_md kanji_md8B1D = {0x8B1D, 656, kanji_ms8B1D};
const kanji_md kanji_md8B66 = {0x8B66, 657, kanji_ms8B66};
const kanji_md kanji_md96A3 = {0x96A3, 658, kanji_ms96A3};
const kanji_md kanji_md5F01 = {0x5F01, 659, kanji_ms5F01};
const kanji_md kanji_md5217 = {0x5217, 660, kanji_ms5217};
const kanji_md kanji_md6065 = {0x6065, 661, kanji_ms6065};
const kanji_md kanji_md6551 = {0x6551, 662, kanji_ms6551};
const kanji_md kanji_md666E = {0x666E, 663, kanji_ms666E};
const kanji_md kanji_md6B6F = {0x6B6F, 664, kanji_ms6B6F};
const kanji_md kanji_md50BE = {0x50BE, 665, kanji_ms50BE};
const kanji_md kanji_md7530 = {0x7530, 666, kanji_ms7530};
const kanji_md kanji_md907F = {0x907F, 667, kanji_ms907F};
const kanji_md kanji_md9806 = {0x9806, 668, kanji_ms9806};
const kanji_md kanji_md8CB4 = {0x8CB4, 669, kanji_ms8CB4};
const kanji_md kanji_md8A66 = {0x8A66, 670, kanji_ms8A66};
const kanji_md kanji_md6A29 = {0x6A29, 671, kanji_ms6A29};
const kanji_md kanji_md6574 = {0x6574, 672, kanji_ms6574};
const kanji_md kanji_md8863 = {0x8863, 673, kanji_ms8863};
const kanji_md kanji_md63FA = {0x63FA, 674, kanji_ms63FA};
const kanji_md kanji_md539A = {0x539A, 675, kanji_ms539A};
const kanji_md kanji_md6163 = {0x6163, 676, kanji_ms6163};
const kanji_md kanji_md7D14 = {0x7D14, 677, kanji_ms7D14};
const kanji_md kanji_md616E = {0x616E, 678, kanji_ms616E};
const kanji_md kanji_md5C3E = {0x5C3E, 679, kanji_ms5C3E};
const kanji_md kanji_md8A70 = {0x8A70, 680, kanji_ms8A70};
const kanji_md kanji_md6D99 = {0x6D99, 681, kanji_ms6D99};
const kanji_md kanji_md63CF = {0x63CF, 682, kanji_ms63CF};
const kanji_md kanji_md5426 = {0x5426, 683, kanji_ms5426};
const kanji_md kanji_md6669 = {0x6669, 684, kanji_ms6669};
const kanji_md kanji_md5263 = {0x5263, 685, kanji_ms5263};
const kanji_md kanji_md57CB = {0x57CB, 686, kanji_ms57CB};
const kanji_md kanji_md8B77 = {0x8B77, 687, kanji_ms8B77};
const kanji_md kanji_md9280 = {0x9280, 688, kanji_ms9280};
const kanji_md kanji_md5E97 = {0x5E97, 689, kanji_ms5E97};
const kanji_md kanji_md4F0F = {0x4F0F, 690, kanji_ms4F0F};
const kanji_md kanji_md5802 = {0x5802, 691, kanji_ms5802};
const kanji_md kanji_md5DDD = {0x5DDD, 692, kanji_ms5DDD};
const kanji_md kanji_md8857 = {0x8857, 693, kanji_ms8857};
const kanji_md kanji_md4EA1 = {0x4EA1, 694, kanji_ms4EA1};
const kanji_md kanji_md6BD2 = {0x6BD2, 695, kanji_ms6BD2};
const kanji_md kanji_md5186 = {0x5186, 696, kanji_ms5186};
const kanji_md kanji_md5FD7 = {0x5FD7, 697, kanji_ms5FD7};
const kanji_md kanji_md8972 = {0x8972, 698, kanji_ms8972};
const kanji_md kanji_md4FBF = {0x4FBF, 699, kanji_ms4FBF};
const kanji_md kanji_md8AB0 = {0x8AB0, 700, kanji_ms8AB0};
const kanji_md kanji_md820C = {0x820C, 701, kanji_ms820C};
const kanji_md kanji_md5024 = {0x5024, 702, kanji_ms5024};
const kanji_md kanji_md6E1B = {0x6E1B, 703, kanji_ms6E1B};
const kanji_md kanji_md627F = {0x627F, 704, kanji_ms627F};
const kanji_md kanji_md63D0 = {0x63D0, 705, kanji_ms63D0};
const kanji_md kanji_md9069 = {0x9069, 706, kanji_ms9069};
const kanji_md kanji_md52B9 = {0x52B9, 707, kanji_ms52B9};
const kanji_md kanji_md5EAB = {0x5EAB, 708, kanji_ms5EAB};
const kanji_md kanji_md7A74 = {0x7A74, 709, kanji_ms7A74};
const kanji_md kanji_md897F = {0x897F, 710, kanji_ms897F};
const kanji_md kanji_md85AC = {0x85AC, 711, kanji_ms85AC};
const kanji_md kanji_md609F = {0x609F, 712, kanji_ms609F};
const kanji_md kanji_md96FB = {0x96FB, 713, kanji_ms96FB};
const kanji_md kanji_md7FBD = {0x7FBD, 714, kanji_ms7FBD};
const kanji_md kanji_md639B = {0x639B, 715, kanji_ms639B};
const kanji_md kanji_md5317 = {0x5317, 716, kanji_ms5317};
const kanji_md kanji_md6E29 = {0x6E29, 717, kanji_ms6E29};
const kanji_md kanji_md9152 = {0x9152, 718, kanji_ms9152};
const kanji_md kanji_md5C4A = {0x5C4A, 719, kanji_ms5C4A};
const kanji_md kanji_md5727 = {0x5727, 720, kanji_ms5727};
const kanji_md kanji_md6E96 = {0x6E96, 721, kanji_ms6E96};
const kanji_md kanji_md5E02 = {0x5E02, 722, kanji_ms5E02};
const kanji_md kanji_md5546 = {0x5546, 723, kanji_ms5546};
const kanji_md kanji_md7389 = {0x7389, 724, kanji_ms7389};
const kanji_md kanji_md5F3E = {0x5F3E, 725, kanji_ms5F3E};
const kanji_md kanji_md4FA1 = {0x4FA1, 726, kanji_ms4FA1};
const kanji_md kanji_md4E92 = {0x4E92, 727, kanji_ms4E92};
const kanji_md kanji_md5FA1 = {0x5FA1, 728, kanji_ms5FA1};
const kanji_md kanji_md623B = {0x623B, 729, kanji_ms623B};
const kanji_md kanji_md6C11 = {0x6C11, 730, kanji_ms6C11};
const kanji_md kanji_md6A21 = {0x6A21, 731, kanji_ms6A21};
const kanji_md kanji_md4F38 = {0x4F38, 732, kanji_ms4F38};
const kanji_md kanji_md96E8 = {0x96E8, 733, kanji_ms96E8};
const kanji_md kanji_md888B = {0x888B, 734, kanji_ms888B};
const kanji_md kanji_md5BD2 = {0x5BD2, 735, kanji_ms5BD2};
const kanji_md kanji_md8377 = {0x8377, 736, kanji_ms8377};
const kanji_md kanji_md6C57 = {0x6C57, 737, kanji_ms6C57};
const kanji_md kanji_md6C5A = {0x6C5A, 738, kanji_ms6C5A};
const kanji_md kanji_md4EF0 = {0x4EF0, 739, kanji_ms4EF0};
const kanji_md kanji_md9632 = {0x9632, 740, kanji_ms9632};
const kanji_md kanji_md8A33 = {0x8A33, 741, kanji_ms8A33};
const kanji_md kanji_md4FEE = {0x4FEE, 742, kanji_ms4FEE};
const kanji_md kanji_md6761 = {0x6761, 743, kanji_ms6761};
const kanji_md kanji_md7159 = {0x7159, 744, kanji_ms7159};
const kanji_md kanji_md5A66 = {0x5A66, 745, kanji_ms5A66};
const kanji_md kanji_md9732 = {0x9732, 746, kanji_ms9732};
const kanji_md kanji_md4EE4 = {0x4EE4, 747, kanji_ms4EE4};
const kanji_md kanji_md6750 = {0x6750, 748, kanji_ms6750};
const kanji_md kanji_md7D75 = {0x7D75, 749, kanji_ms7D75};
const kanji_md kanji_md7532 = {0x7532, 750, kanji_ms7532};
const kanji_md kanji_md99C4 = {0x99C4, 751, kanji_ms99C4};
const kanji_md kanji_md7BA1 = {0x7BA1, 752, kanji_ms7BA1};
const kanji_md kanji_md5230 = {0x5230, 753, kanji_ms5230};
const kanji_md kanji_md81F3 = {0x81F3, 754, kanji_ms81F3};
const kanji_md kanji_md6821 = {0x6821, 755, kanji_ms6821};
const kanji_md kanji_md5A01 = {0x5A01, 756, kanji_ms5A01};
const kanji_md kanji_md71C3 = {0x71C3, 757, kanji_ms71C3};
const kanji_md kanji_md93E1 = {0x93E1, 758, kanji_ms93E1};
const kanji_md kanji_md68D2 = {0x68D2, 759, kanji_ms68D2};
const kanji_md kanji_md7DCA = {0x7DCA, 760, kanji_ms7DCA};
const kanji_md kanji_md8CC7 = {0x8CC7, 761, kanji_ms8CC7};
const kanji_md kanji_md9685 = {0x9685, 762, kanji_ms9685};
const kanji_md kanji_md5348 = {0x5348, 763, kanji_ms5348};
const kanji_md kanji_md9CE5 = {0x9CE5, 764, kanji_ms9CE5};
const kanji_md kanji_md5B98 = {0x5B98, 765, kanji_ms5B98};
const kanji_md kanji_md9EC4 = {0x9EC4, 766, kanji_ms9EC4};
const kanji_md kanji_md5144 = {0x5144, 767, kanji_ms5144};
const kanji_md kanji_md8A55 = {0x8A55, 768, kanji_ms8A55};
const kanji_md kanji_md95C7 = {0x95C7, 769, kanji_ms95C7};
const kanji_md kanji_md66FF = {0x66FF, 770, kanji_ms66FF};
const kanji_md kanji_md60A9 = {0x60A9, 771, kanji_ms60A9};
const kanji_md kanji_md6B4C = {0x6B4C, 772, kanji_ms6B4C};
const kanji_md kanji_md6F14 = {0x6F14, 773, kanji_ms6F14};
const kanji_md kanji_md7BB1 = {0x7BB1, 774, kanji_ms7BB1};
const kanji_md kanji_md73CD = {0x73CD, 775, kanji_ms73CD};
const kanji_md kanji_md676F = {0x676F, 776, kanji_ms676F};
const kanji_md kanji_md6625 = {0x6625, 777, kanji_ms6625};
const kanji_md kanji_md6D74 = {0x6D74, 778, kanji_ms6D74};
const kanji_md kanji_md6280 = {0x6280, 779, kanji_ms6280};
const kanji_md kanji_md92ED = {0x92ED, 780, kanji_ms92ED};
const kanji_md kanji_md9662 = {0x9662, 781, kanji_ms9662};
const kanji_md kanji_md6094 = {0x6094, 782, kanji_ms6094};
const kanji_md kanji_md604B = {0x604B, 783, kanji_ms604B};
const kanji_md kanji_md4E01 = {0x4E01, 784, kanji_ms4E01};
const kanji_md kanji_md590F = {0x590F, 785, kanji_ms590F};
const kanji_md kanji_md661F = {0x661F, 786, kanji_ms661F};
const kanji_md kanji_md5199 = {0x5199, 787, kanji_ms5199};
const kanji_md kanji_md6CB9 = {0x6CB9, 788, kanji_ms6CB9};
const kanji_md kanji_md8F1D = {0x8F1D, 789, kanji_ms8F1D};
const kanji_md kanji_md83EF = {0x83EF, 790, kanji_ms83EF};
const kanji_md kanji_md596A = {0x596A, 791, kanji_ms596A};
const kanji_md kanji_md7FA4 = {0x7FA4, 792, kanji_ms7FA4};
const kanji_md kanji_md8A2D = {0x8A2D, 793, kanji_ms8A2D};
const kanji_md kanji_md753A = {0x753A, 794, kanji_ms753A};
const kanji_md kanji_md7981 = {0x7981, 795, kanji_ms7981};
const kanji_md kanji_md98FE = {0x98FE, 796, kanji_ms98FE};
const kanji_md kanji_md5712 = {0x5712, 797, kanji_ms5712};
const kanji_md kanji_md88C2 = {0x88C2, 798, kanji_ms88C2};
const kanji_md kanji_md9154 = {0x9154, 799, kanji_ms9154};
const kanji_md kanji_md982C = {0x982C, 800, kanji_ms982C};
const kanji_md kanji_md6355 = {0x6355, 801, kanji_ms6355};
const kanji_md kanji_md7D1A = {0x7D1A, 802, kanji_ms7D1A};
const kanji_md kanji_md798F = {0x798F, 803, kanji_ms798F};
const kanji_md kanji_md5C5E = {0x5C5E, 804, kanji_ms5C5E};
const kanji_md kanji_md7B97 = {0x7B97, 805, kanji_ms7B97};
const kanji_md kanji_md6C38 = {0x6C38, 806, kanji_ms6C38};
const kanji_md kanji_md9818 = {0x9818, 807, kanji_ms9818};
const kanji_md kanji_md5065 = {0x5065, 808, kanji_ms5065};
const kanji_md kanji_md6E08 = {0x6E08, 809, kanji_ms6E08};
const kanji_md kanji_md70BA = {0x70BA, 810, kanji_ms70BA};
const kanji_md kanji_md533A = {0x533A, 811, kanji_ms533A};
const kanji_md kanji_md9999 = {0x9999, 812, kanji_ms9999};
const kanji_md kanji_md62C5 = {0x62C5, 813, kanji_ms62C5};
const kanji_md kanji_md8F9E = {0x8F9E, 814, kanji_ms8F9E};
const kanji_md kanji_md5D29 = {0x5D29, 815, kanji_ms5D29};
const kanji_md kanji_md773A = {0x773A, 816, kanji_ms773A};
const kanji_md kanji_md88FD = {0x88FD, 817, kanji_ms88FD};
const kanji_md kanji_md6B74 = {0x6B74, 818, kanji_ms6B74};
const kanji_md kanji_md6B66 = {0x6B66, 819, kanji_ms6B66};
const kanji_md kanji_md529F = {0x529F, 820, kanji_ms529F};
const kanji_md kanji_md885D = {0x885D, 821, kanji_ms885D};
const kanji_md kanji_md52C7 = {0x52C7, 822, kanji_ms52C7};
const kanji_md kanji_md6E05 = {0x6E05, 823, kanji_ms6E05};
const kanji_md kanji_md656C = {0x656C, 824, kanji_ms656C};
const kanji_md kanji_md866B = {0x866B, 825, kanji_ms866B};
const kanji_md kanji_md72AF = {0x72AF, 826, kanji_ms72AF};
const kanji_md kanji_md63DB = {0x63DB, 827, kanji_ms63DB};
const kanji_md kanji_md7D61 = {0x7D61, 828, kanji_ms7D61};
const kanji_md kanji_md738B = {0x738B, 829, kanji_ms738B};
const kanji_md kanji_md53CA = {0x53CA, 830, kanji_ms53CA};
const kanji_md kanji_md62DB = {0x62DB, 831, kanji_ms62DB};
const kanji_md kanji_md990A = {0x990A, 832, kanji_ms990A};
const kanji_md kanji_md72AC = {0x72AC, 833, kanji_ms72AC};
const kanji_md kanji_md5357 = {0x5357, 834, kanji_ms5357};
const kanji_md kanji_md9802 = {0x9802, 835, kanji_ms9802};
const kanji_md kanji_md808C = {0x808C, 836, kanji_ms808C};
const kanji_md kanji_md7DE8 = {0x7DE8, 837, kanji_ms7DE8};
const kanji_md kanji_md618E = {0x618E, 838, kanji_ms618E};
const kanji_md kanji_md59BB = {0x59BB, 839, kanji_ms59BB};
const kanji_md kanji_md9707 = {0x9707, 840, kanji_ms9707};
const kanji_md kanji_md61D0 = {0x61D0, 841, kanji_ms61D0};
const kanji_md kanji_md72ED = {0x72ED, 842, kanji_ms72ED};
const kanji_md kanji_md969C = {0x969C, 843, kanji_ms969C};
const kanji_md kanji_md8CB8 = {0x8CB8, 844, kanji_ms8CB8};
const kanji_md kanji_md500D = {0x500D, 845, kanji_ms500D};
const kanji_md kanji_md9803 = {0x9803, 846, kanji_ms9803};
const kanji_md kanji_md596E = {0x596E, 847, kanji_ms596E};
const kanji_md kanji_md5C06 = {0x5C06, 848, kanji_ms5C06};
const kanji_md kanji_md96F2 = {0x96F2, 849, kanji_ms96F2};
const kanji_md kanji_md6CC1 = {0x6CC1, 850, kanji_ms6CC1};
const kanji_md kanji_md6613 = {0x6613, 851, kanji_ms6613};
const kanji_md kanji_md706F = {0x706F, 852, kanji_ms706F};
const kanji_md kanji_md5C02 = {0x5C02, 853, kanji_ms5C02};
const kanji_md kanji_md6FC3 = {0x6FC3, 854, kanji_ms6FC3};
const kanji_md kanji_md63A8 = {0x63A8, 855, kanji_ms63A8};
const kanji_md kanji_md7FCC = {0x7FCC, 856, kanji_ms7FCC};
const kanji_md kanji_md5A5A = {0x5A5A, 857, kanji_ms5A5A};
const kanji_md kanji_md5E7C = {0x5E7C, 858, kanji_ms5E7C};
const kanji_md kanji_md4EEE = {0x4EEE, 859, kanji_ms4EEE};
const kanji_md kanji_md6271 = {0x6271, 860, kanji_ms6271};
const kanji_md kanji_md5B85 = {0x5B85, 861, kanji_ms5B85};
const kanji_md kanji_md8F9B = {0x8F9B, 862, kanji_ms8F9B};
const kanji_md kanji_md54C0 = {0x54C0, 863, kanji_ms54C0};
const kanji_md kanji_md542B = {0x542B, 864, kanji_ms542B};
const kanji_md kanji_md7709 = {0x7709, 865, kanji_ms7709};
const kanji_md kanji_md62FE = {0x62FE, 866, kanji_ms62FE};
const kanji_md kanji_md5F1F = {0x5F1F, 867, kanji_ms5F1F};
const kanji_md kanji_md6319 = {0x6319, 868, kanji_ms6319};
const kanji_md kanji_md8133 = {0x8133, 869, kanji_ms8133};
const kanji_md kanji_md5197 = {0x5197, 870, kanji_ms5197};
const kanji_md kanji_md9928 = {0x9928, 871, kanji_ms9928};
const kanji_md kanji_md5C0E = {0x5C0E, 872, kanji_ms5C0E};
const kanji_md kanji_md8AA4 = {0x8AA4, 873, kanji_ms8AA4};
const kanji_md kanji_md6804 = {0x6804, 874, kanji_ms6804};
const kanji_md kanji_md623F = {0x623F, 875, kanji_ms623F};
const kanji_md kanji_md691C = {0x691C, 876, kanji_ms691C};
const kanji_md kanji_md57F7 = {0x57F7, 877, kanji_ms57F7};
const kanji_md kanji_md52D8 = {0x52D8, 878, kanji_ms52D8};
const kanji_md kanji_md90CE = {0x90CE, 879, kanji_ms90CE};
const kanji_md kanji_md5C3B = {0x5C3B, 880, kanji_ms5C3B};
const kanji_md kanji_md508D = {0x508D, 881, kanji_ms508D};
const kanji_md kanji_md58CA = {0x58CA, 882, kanji_ms58CA};
const kanji_md kanji_md7D05 = {0x7D05, 883, kanji_ms7D05};
const kanji_md kanji_md7DCF = {0x7DCF, 884, kanji_ms7DCF};
const kanji_md kanji_md95D8 = {0x95D8, 885, kanji_ms95D8};
const kanji_md kanji_md5C3D = {0x5C3D, 886, kanji_ms5C3D};
const kanji_md kanji_md8DDD = {0x8DDD, 887, kanji_ms8DDD};
const kanji_md kanji_md907A = {0x907A, 888, kanji_ms907A};
const kanji_md kanji_md4E7E = {0x4E7E, 889, kanji_ms4E7E};
const kanji_md kanji_md7E2E = {0x7E2E, 890, kanji_ms7E2E};
const kanji_md kanji_md7802 = {0x7802, 891, kanji_ms7802};
const kanji_md kanji_md898F = {0x898F, 892, kanji_ms898F};
const kanji_md kanji_md88D5 = {0x88D5, 893, kanji_ms88D5};
const kanji_md kanji_md79D1 = {0x79D1, 894, kanji_ms79D1};
const kanji_md kanji_md819D = {0x819D, 895, kanji_ms819D};
const kanji_md kanji_md5DE8 = {0x5DE8, 896, kanji_ms5DE8};
const kanji_md kanji_md70C8 = {0x70C8, 897, kanji_ms70C8};
const kanji_md kanji_md5ECA = {0x5ECA, 898, kanji_ms5ECA};
const kanji_md kanji_md5C55 = {0x5C55, 899, kanji_ms5C55};
const kanji_md kanji_md5373 = {0x5373, 900, kanji_ms5373};
const kanji_md kanji_md76D7 = {0x76D7, 901, kanji_ms76D7};
const kanji_md kanji_md62B5 = {0x62B5, 902, kanji_ms62B5};
const kanji_md kanji_md5E72 = {0x5E72, 903, kanji_ms5E72};
const kanji_md kanji_md653B = {0x653B, 904, kanji_ms653B};
const kanji_md kanji_md8CA1 = {0x8CA1, 905, kanji_ms8CA1};
const kanji_md kanji_md5076 = {0x5076, 906, kanji_ms5076};
const kanji_md kanji_md82B8 = {0x82B8, 907, kanji_ms82B8};
const kanji_md kanji_md79F0 = {0x79F0, 908, kanji_ms79F0};
const kanji_md kanji_md7B46 = {0x7B46, 909, kanji_ms7B46};
const kanji_md kanji_md7E54 = {0x7E54, 910, kanji_ms7E54};
const kanji_md kanji_md9BAE = {0x9BAE, 911, kanji_ms9BAE};
const kanji_md kanji_md533B = {0x533B, 912, kanji_ms533B};
const kanji_md kanji_md9031 = {0x9031, 913, kanji_ms9031};
const kanji_md kanji_md5C01 = {0x5C01, 914, kanji_ms5C01};
const kanji_md kanji_md8A87 = {0x8A87, 915, kanji_ms8A87};
const kanji_md kanji_md9E7F = {0x9E7F, 916, kanji_ms9E7F};
const kanji_md kanji_md5145 = {0x5145, 917, kanji_ms5145};
const kanji_md kanji_md5FCD = {0x5FCD, 918, kanji_ms5FCD};
const kanji_md kanji_md7D66 = {0x7D66, 919, kanji_ms7D66};
const kanji_md kanji_md52AA = {0x52AA, 920, kanji_ms52AA};
const kanji_md kanji_md8E8D = {0x8E8D, 921, kanji_ms8E8D};
const kanji_md kanji_md5618 = {0x5618, 922, kanji_ms5618};
const kanji_md kanji_md8CBB = {0x8CBB, 923, kanji_ms8CBB};
const kanji_md kanji_md9F62 = {0x9F62, 924, kanji_ms9F62};
const kanji_md kanji_md5404 = {0x5404, 925, kanji_ms5404};
const kanji_md kanji_md8239 = {0x8239, 926, kanji_ms8239};
const kanji_md kanji_md91DD = {0x91DD, 927, kanji_ms91DD};
const kanji_md kanji_md91C8 = {0x91C8, 928, kanji_ms91C8};
const kanji_md kanji_md8907 = {0x8907, 929, kanji_ms8907};
const kanji_md kanji_md8DA3 = {0x8DA3, 930, kanji_ms8DA3};
const kanji_md kanji_md7DE0 = {0x7DE0, 931, kanji_ms7DE0};
const kanji_md kanji_md624D = {0x624D, 932, kanji_ms624D};
const kanji_md kanji_md55B6 = {0x55B6, 933, kanji_ms55B6};
const kanji_md kanji_md81ED = {0x81ED, 934, kanji_ms81ED};
const kanji_md kanji_md7384 = {0x7384, 935, kanji_ms7384};
const kanji_md kanji_md81F4 = {0x81F4, 936, kanji_ms81F4};
const kanji_md kanji_md9811 = {0x9811, 937, kanji_ms9811};
const kanji_md kanji_md640D = {0x640D, 938, kanji_ms640D};
const kanji_md kanji_md7387 = {0x7387, 939, kanji_ms7387};
const kanji_md kanji_md6075 = {0x6075, 940, kanji_ms6075};
const kanji_md kanji_md88AB = {0x88AB, 941, kanji_ms88AB};
const kanji_md kanji_md6B53 = {0x6B53, 942, kanji_ms6B53};
const kanji_md kanji_md7D99 = {0x7D99, 943, kanji_ms7D99};
const kanji_md kanji_md7126 = {0x7126, 944, kanji_ms7126};
const kanji_md kanji_md6687 = {0x6687, 945, kanji_ms6687};
const kanji_md kanji_md820E = {0x820E, 946, kanji_ms820E};
const kanji_md kanji_md5CF6 = {0x5CF6, 947, kanji_ms5CF6};
const kanji_md kanji_md6751 = {0x6751, 948, kanji_ms6751};
const kanji_md kanji_md57FA = {0x57FA, 949, kanji_ms57FA};
const kanji_md kanji_md8010 = {0x8010, 950, kanji_ms8010};
const kanji_md kanji_md5507 = {0x5507, 951, kanji_ms5507};
const kanji_md kanji_md5360 = {0x5360, 952, kanji_ms5360};
const kanji_md kanji_md5E0C = {0x5E0C, 953, kanji_ms5E0C};
const kanji_md kanji_md9063 = {0x9063, 954, kanji_ms9063};
const kanji_md kanji_md6CA2 = {0x6CA2, 955, kanji_ms6CA2};
const kanji_md kanji_md865A = {0x865A, 956, kanji_ms865A};
const kanji_md kanji_md8F09 = {0x8F09, 957, kanji_ms8F09};
const kanji_md kanji_md5354 = {0x5354, 958, kanji_ms5354};
const kanji_md kanji_md66F4 = {0x66F4, 959, kanji_ms66F4};
const kanji_md kanji_md81D3 = {0x81D3, 960, kanji_ms81D3};
const kanji_md kanji_md6CCA = {0x6CCA, 961, kanji_ms6CCA};
const kanji_md kanji_md7686 = {0x7686, 962, kanji_ms7686};
const kanji_md kanji_md5F92 = {0x5F92, 963, kanji_ms5F92};
const kanji_md kanji_md4E86 = {0x4E86, 964, kanji_ms4E86};
const kanji_md kanji_md53E9 = {0x53E9, 965, kanji_ms53E9};
const kanji_md kanji_md52E4 = {0x52E4, 966, kanji_ms52E4};
const kanji_md kanji_md8CA7 = {0x8CA7, 967, kanji_ms8CA7};
const kanji_md kanji_md5857 = {0x5857, 968, kanji_ms5857};
const kanji_md kanji_md8535 = {0x8535, 969, kanji_ms8535};
const kanji_md kanji_md9332 = {0x9332, 970, kanji_ms9332};
const kanji_md kanji_md7CF8 = {0x7CF8, 971, kanji_ms7CF8};
const kanji_md kanji_md7248 = {0x7248, 972, kanji_ms7248};
const kanji_md kanji_md7D39 = {0x7D39, 973, kanji_ms7D39};
const kanji_md kanji_md7AE0 = {0x7AE0, 974, kanji_ms7AE0};
const kanji_md kanji_md5DF1 = {0x5DF1, 975, kanji_ms5DF1};
const kanji_md kanji_md77E2 = {0x77E2, 976, kanji_ms77E2};
const kanji_md kanji_md822C = {0x822C, 977, kanji_ms822C};
const kanji_md kanji_md67D4 = {0x67D4, 978, kanji_ms67D4};
const kanji_md kanji_md61F8 = {0x61F8, 979, kanji_ms61F8};
const kanji_md kanji_md8ECD = {0x8ECD, 980, kanji_ms8ECD};
const kanji_md kanji_md5584 = {0x5584, 981, kanji_ms5584};
const kanji_md kanji_md5974 = {0x5974, 982, kanji_ms5974};
const kanji_md kanji_md6CE5 = {0x6CE5, 983, kanji_ms6CE5};
const kanji_md kanji_md7E70 = {0x7E70, 984, kanji_ms7E70};
const kanji_md kanji_md6ED1 = {0x6ED1, 985, kanji_ms6ED1};
const kanji_md kanji_md60DC = {0x60DC, 986, kanji_ms60DC};
const kanji_md kanji_md9177 = {0x9177, 987, kanji_ms9177};
const kanji_md kanji_md690D = {0x690D, 988, kanji_ms690D};
const kanji_md kanji_md67F1 = {0x67F1, 989, kanji_ms67F1};
const kanji_md kanji_md770B = {0x770B, 990, kanji_ms770B};
const kanji_md kanji_md5C0A = {0x5C0A, 991, kanji_ms5C0A};
const kanji_md kanji_md811A = {0x811A, 992, kanji_ms811A};
const kanji_md kanji_md5EF6 = {0x5EF6, 993, kanji_ms5EF6};
const kanji_md kanji_md62CD = {0x62CD, 994, kanji_ms62CD};
const kanji_md kanji_md82F1 = {0x82F1, 995, kanji_ms82F1};
const kanji_md kanji_md6E6F = {0x6E6F, 996, kanji_ms6E6F};
const kanji_md kanji_md5446 = {0x5446, 997, kanji_ms5446};
const kanji_md kanji_md5FB4 = {0x5FB4, 998, kanji_ms5FB4};
const kanji_md kanji_md574A = {0x574A, 999, kanji_ms574A};
const kanji_md kanji_md67FB = {0x67FB, 1000, kanji_ms67FB};
const kanji_md kanji_md6D45 = {0x6D45, 1001, kanji_ms6D45};
const kanji_md kanji_md8C4A = {0x8C4A, 1002, kanji_ms8C4A};
const kanji_md kanji_md505C = {0x505C, 1003, kanji_ms505C};
const kanji_md kanji_md5B9D = {0x5B9D, 1004, kanji_ms5B9D};
const kanji_md kanji_md7070 = {0x7070, 1005, kanji_ms7070};
const kanji_md kanji_md552F = {0x552F, 1006, kanji_ms552F};
const kanji_md kanji_md5FD9 = {0x5FD9, 1007, kanji_ms5FD9};
const kanji_md kanji_md98EF = {0x98EF, 1008, kanji_ms98EF};
const kanji_md kanji_md6E2C = {0x6E2C, 1009, kanji_ms6E2C};
const kanji_md kanji_md900F = {0x900F, 1010, kanji_ms900F};
const kanji_md kanji_md63DA = {0x63DA, 1011, kanji_ms63DA};
const kanji_md kanji_md5E45 = {0x5E45, 1012, kanji_ms5E45};
const kanji_md kanji_md731B = {0x731B, 1013, kanji_ms731B};
const kanji_md kanji_md8C37 = {0x8C37, 1014, kanji_ms8C37};
const kanji_md kanji_md5FE0 = {0x5FE0, 1015, kanji_ms5FE0};
const kanji_md kanji_md5287 = {0x5287, 1016, kanji_ms5287};
const kanji_md kanji_md8D85 = {0x8D85, 1017, kanji_ms8D85};
const kanji_md kanji_md8C6A = {0x8C6A, 1018, kanji_ms8C6A};
const kanji_md kanji_md7DD1 = {0x7DD1, 1019, kanji_ms7DD1};
const kanji_md kanji_md653F = {0x653F, 1020, kanji_ms653F};
const kanji_md kanji_md53F2 = {0x53F2, 1021, kanji_ms53F2};
const kanji_md kanji_md592E = {0x592E, 1022, kanji_ms592E};
const kanji_md kanji_md5C64 = {0x5C64, 1023, kanji_ms5C64};
const kanji_md kanji_md5BCC = {0x5BCC, 1024, kanji_ms5BCC};
const kanji_md kanji_md6905 = {0x6905, 1025, kanji_ms6905};
const kanji_md kanji_md5BA3 = {0x5BA3, 1026, kanji_ms5BA3};
const kanji_md kanji_md5302 = {0x5302, 1027, kanji_ms5302};
const kanji_md kanji_md5642 = {0x5642, 1028, kanji_ms5642};
const kanji_md kanji_md6DFB = {0x6DFB, 1029, kanji_ms6DFB};
const kanji_md kanji_md8107 = {0x8107, 1030, kanji_ms8107};
const kanji_md kanji_md8A34 = {0x8A34, 1031, kanji_ms8A34};
const kanji_md kanji_md6A4B = {0x6A4B, 1032, kanji_ms6A4B};
const kanji_md kanji_md5F80 = {0x5F80, 1033, kanji_ms5F80};
const kanji_md kanji_md6D0B = {0x6D0B, 1034, kanji_ms6D0B};
const kanji_md kanji_md9B5A = {0x9B5A, 1035, kanji_ms9B5A};
const kanji_md kanji_md6212 = {0x6212, 1036, kanji_ms6212};
const kanji_md kanji_md53F8 = {0x53F8, 1037, kanji_ms53F8};
const kanji_md kanji_md7D71 = {0x7D71, 1038, kanji_ms7D71};
const kanji_md kanji_md5150 = {0x5150, 1039, kanji_ms5150};
const kanji_md kanji_md5FB9 = {0x5FB9, 1040, kanji_ms5FB9};
const kanji_md kanji_md51AC = {0x51AC, 1041, kanji_ms51AC};
const kanji_md kanji_md8A73 = {0x8A73, 1042, kanji_ms8A73};
const kanji_md kanji_md68EE = {0x68EE, 1043, kanji_ms68EE};
const kanji_md kanji_md611A = {0x611A, 1044, kanji_ms611A};
const kanji_md kanji_md7B56 = {0x7B56, 1045, kanji_ms7B56};
const kanji_md kanji_md79CB = {0x79CB, 1046, kanji_ms79CB};
const kanji_md kanji_md8846 = {0x8846, 1047, kanji_ms8846};
const kanji_md kanji_md6DE1 = {0x6DE1, 1048, kanji_ms6DE1};
const kanji_md kanji_md885B = {0x885B, 1049, kanji_ms885B};
const kanji_md kanji_md9B45 = {0x9B45, 1050, kanji_ms9B45};
const kanji_md kanji_md5B99 = {0x5B99, 1051, kanji_ms5B99};
const kanji_md kanji_md7948 = {0x7948, 1052, kanji_ms7948};
const kanji_md kanji_md88DC = {0x88DC, 1053, kanji_ms88DC};
const kanji_md kanji_md6383 = {0x6383, 1054, kanji_ms6383};
const kanji_md kanji_md7A4F = {0x7A4F, 1055, kanji_ms7A4F};
const kanji_md kanji_md64CD = {0x64CD, 1056, kanji_ms64CD};
const kanji_md kanji_md6328 = {0x6328, 1057, kanji_ms6328};
const kanji_md kanji_md76E3 = {0x76E3, 1058, kanji_ms76E3};
const kanji_md kanji_md5782 = {0x5782, 1059, kanji_ms5782};
const kanji_md kanji_md970A = {0x970A, 1060, kanji_ms970A};
const kanji_md kanji_md5DE1 = {0x5DE1, 1061, kanji_ms5DE1};
const kanji_md kanji_md62F6 = {0x62F6, 1062, kanji_ms62F6};
const kanji_md kanji_md5E55 = {0x5E55, 1063, kanji_ms5E55};
const kanji_md kanji_md5606 = {0x5606, 1064, kanji_ms5606};
const kanji_md kanji_md5175 = {0x5175, 1065, kanji_ms5175};
const kanji_md kanji_md6607 = {0x6607, 1066, kanji_ms6607};
const kanji_md kanji_md5019 = {0x5019, 1067, kanji_ms5019};
const kanji_md kanji_md7BC9 = {0x7BC9, 1068, kanji_ms7BC9};
const kanji_md kanji_md7814 = {0x7814, 1069, kanji_ms7814};
const kanji_md kanji_md6797 = {0x6797, 1070, kanji_ms6797};
const kanji_md kanji_md4F9D = {0x4F9D, 1071, kanji_ms4F9D};
const kanji_md kanji_md5247 = {0x5247, 1072, kanji_ms5247};
const kanji_md kanji_md5BF8 = {0x5BF8, 1073, kanji_ms5BF8};
const kanji_md kanji_md5BAE = {0x5BAE, 1074, kanji_ms5BAE};
const kanji_md kanji_md68DA = {0x68DA, 1075, kanji_ms68DA};
const kanji_md kanji_md5E33 = {0x5E33, 1076, kanji_ms5E33};
const kanji_md kanji_md59B9 = {0x59B9, 1077, kanji_ms59B9};
const kanji_md kanji_md6388 = {0x6388, 1078, kanji_ms6388};
const kanji_md kanji_md673A = {0x673A, 1079, kanji_ms673A};
const kanji_md kanji_md7403 = {0x7403, 1080, kanji_ms7403};
const kanji_md kanji_md51DD = {0x51DD, 1081, kanji_ms51DD};
const kanji_md kanji_md9B3C = {0x9B3C, 1082, kanji_ms9B3C};
const kanji_md kanji_md5E7E = {0x5E7E, 1083, kanji_ms5E7E};
const kanji_md kanji_md7C89 = {0x7C89, 1084, kanji_ms7C89};
const kanji_md kanji_md96EA = {0x96EA, 1085, kanji_ms96EA};
const kanji_md kanji_md565B = {0x565B, 1086, kanji_ms565B};
const kanji_md kanji_md62D2 = {0x62D2, 1087, kanji_ms62D2};
const kanji_md kanji_md80C6 = {0x80C6, 1088, kanji_ms80C6};
const kanji_md kanji_md9EBB = {0x9EBB, 1089, kanji_ms9EBB};
const kanji_md kanji_md5F8B = {0x5F8B, 1090, kanji_ms5F8B};
const kanji_md kanji_md7206 = {0x7206, 1091, kanji_ms7206};
const kanji_md kanji_md8074 = {0x8074, 1092, kanji_ms8074};
const kanji_md kanji_md88F8 = {0x88F8, 1093, kanji_ms88F8};
const kanji_md kanji_md4EAC = {0x4EAC, 1094, kanji_ms4EAC};
const kanji_md kanji_md6C0F = {0x6C0F, 1095, kanji_ms6C0F};
const kanji_md kanji_md7701 = {0x7701, 1096, kanji_ms7701};
const kanji_md kanji_md5409 = {0x5409, 1097, kanji_ms5409};
const kanji_md kanji_md5C0B = {0x5C0B, 1098, kanji_ms5C0B};
const kanji_md kanji_md659C = {0x659C, 1099, kanji_ms659C};
const kanji_md kanji_md5CB8 = {0x5CB8, 1100, kanji_ms5CB8};
const kanji_md kanji_md614E = {0x614E, 1101, kanji_ms614E};
const kanji_md kanji_md968A = {0x968A, 1102, kanji_ms968A};
const kanji_md kanji_md6291 = {0x6291, 1103, kanji_ms6291};
const kanji_md kanji_md672D = {0x672D, 1104, kanji_ms672D};
const kanji_md kanji_md732B = {0x732B, 1105, kanji_ms732B};
const kanji_md kanji_md5BC2 = {0x5BC2, 1106, kanji_ms5BC2};
const kanji_md kanji_md6F5C = {0x6F5C, 1107, kanji_ms6F5C};
const kanji_md kanji_md7956 = {0x7956, 1108, kanji_ms7956};
const kanji_md kanji_md8150 = {0x8150, 1109, kanji_ms8150};
const kanji_md kanji_md60E8 = {0x60E8, 1110, kanji_ms60E8};
const kanji_md kanji_md6E90 = {0x6E90, 1111, kanji_ms6E90};
const kanji_md kanji_md7CFB = {0x7CFB, 1112, kanji_ms7CFB};
const kanji_md kanji_md57CE = {0x57CE, 1113, kanji_ms57CE};
const kanji_md kanji_md7565 = {0x7565, 1114, kanji_ms7565};
const kanji_md kanji_md6A19 = {0x6A19, 1115, kanji_ms6A19};
const kanji_md kanji_md96F0 = {0x96F0, 1116, kanji_ms96F0};
const kanji_md kanji_md796D = {0x796D, 1117, kanji_ms796D};
const kanji_md kanji_md7656 = {0x7656, 1118, kanji_ms7656};
const kanji_md kanji_md6F6E = {0x6F6E, 1119, kanji_ms6F6E};
const kanji_md kanji_md708E = {0x708E, 1120, kanji_ms708E};
const kanji_md kanji_md719F = {0x719F, 1121, kanji_ms719F};
const kanji_md kanji_md62DD = {0x62DD, 1122, kanji_ms62DD};
const kanji_md kanji_md8986 = {0x8986, 1123, kanji_ms8986};
const kanji_md kanji_md96C4 = {0x96C4, 1124, kanji_ms96C4};
const kanji_md kanji_md6068 = {0x6068, 1125, kanji_ms6068};
const kanji_md kanji_md5BE9 = {0x5BE9, 1126, kanji_ms5BE9};
const kanji_md kanji_md8ACB = {0x8ACB, 1127, kanji_ms8ACB};
const kanji_md kanji_md7A76 = {0x7A76, 1128, kanji_ms7A76};
const kanji_md kanji_md6CA1 = {0x6CA1, 1129, kanji_ms6CA1};
const kanji_md kanji_md9774 = {0x9774, 1130, kanji_ms9774};
const kanji_md kanji_md88C1 = {0x88C1, 1131, kanji_ms88C1};
const kanji_md kanji_md72D9 = {0x72D9, 1132, kanji_ms72D9};
const kanji_md kanji_md59C9 = {0x59C9, 1133, kanji_ms59C9};
const kanji_md kanji_md9699 = {0x9699, 1134, kanji_ms9699};
const kanji_md kanji_md8FF0 = {0x8FF0, 1135, kanji_ms8FF0};
const kanji_md kanji_md5339 = {0x5339, 1136, kanji_ms5339};
const kanji_md kanji_md5E7B = {0x5E7B, 1137, kanji_ms5E7B};
const kanji_md kanji_md8CAB = {0x8CAB, 1138, kanji_ms8CAB};
const kanji_md kanji_md829D = {0x829D, 1139, kanji_ms829D};
const kanji_md kanji_md795D = {0x795D, 1140, kanji_ms795D};
const kanji_md kanji_md6CB3 = {0x6CB3, 1141, kanji_ms6CB3};
const kanji_md kanji_md679D = {0x679D, 1142, kanji_ms679D};
const kanji_md kanji_md8E74 = {0x8E74, 1143, kanji_ms8E74};
const kanji_md kanji_md5200 = {0x5200, 1144, kanji_ms5200};
const kanji_md kanji_md9375 = {0x9375, 1145, kanji_ms9375};
const kanji_md kanji_md6249 = {0x6249, 1146, kanji_ms6249};
const kanji_md kanji_md9B42 = {0x9B42, 1147, kanji_ms9B42};
const kanji_md kanji_md6696 = {0x6696, 1148, kanji_ms6696};
const kanji_md kanji_md6FE1 = {0x6FE1, 1149, kanji_ms6FE1};
const kanji_md kanji_md5451 = {0x5451, 1150, kanji_ms5451};
const kanji_md kanji_md920D = {0x920D, 1151, kanji_ms920D};
const kanji_md kanji_md7E1B = {0x7E1B, 1152, kanji_ms7E1B};
const kanji_md kanji_md7E41 = {0x7E41, 1153, kanji_ms7E41};
const kanji_md kanji_md8F29 = {0x8F29, 1154, kanji_ms8F29};
const kanji_md kanji_md76BF = {0x76BF, 1155, kanji_ms76BF};
const kanji_md kanji_md5589 = {0x5589, 1156, kanji_ms5589};
const kanji_md kanji_md62ED = {0x62ED, 1157, kanji_ms62ED};
const kanji_md kanji_md8E0A = {0x8E0A, 1158, kanji_ms8E0A};
const kanji_md kanji_md5CA9 = {0x5CA9, 1159, kanji_ms5CA9};
const kanji_md kanji_md4F01 = {0x4F01, 1160, kanji_ms4F01};
const kanji_md kanji_md8CDE = {0x8CDE, 1161, kanji_ms8CDE};
const kanji_md kanji_md786C = {0x786C, 1162, kanji_ms786C};
const kanji_md kanji_md5049 = {0x5049, 1163, kanji_ms5049};
const kanji_md kanji_md809D = {0x809D, 1164, kanji_ms809D};
const kanji_md kanji_md90F7 = {0x90F7, 1165, kanji_ms90F7};
const kanji_md kanji_md8ED2 = {0x8ED2, 1166, kanji_ms8ED2};
const kanji_md kanji_md5982 = {0x5982, 1167, kanji_ms5982};
const kanji_md kanji_md5742 = {0x5742, 1168, kanji_ms5742};
const kanji_md kanji_md6F02 = {0x6F02, 1169, kanji_ms6F02};
const kanji_md kanji_md6F84 = {0x6F84, 1170, kanji_ms6F84};
const kanji_md kanji_md5352 = {0x5352, 1171, kanji_ms5352};
const kanji_md kanji_md5EB7 = {0x5EB7, 1172, kanji_ms5EB7};
const kanji_md kanji_md9678 = {0x9678, 1173, kanji_ms9678};
const kanji_md kanji_md6A39 = {0x6A39, 1174, kanji_ms6A39};
const kanji_md kanji_md654F = {0x654F, 1175, kanji_ms654F};
const kanji_md kanji_md52C9 = {0x52C9, 1176, kanji_ms52C9};
const kanji_md kanji_md514D = {0x514D, 1177, kanji_ms514D};
const kanji_md kanji_md7573 = {0x7573, 1178, kanji_ms7573};
const kanji_md kanji_md63EE = {0x63EE, 1179, kanji_ms63EE};
const kanji_md kanji_md57DF = {0x57DF, 1180, kanji_ms57DF};
const kanji_md kanji_md5B09 = {0x5B09, 1181, kanji_ms5B09};
const kanji_md kanji_md7344 = {0x7344, 1182, kanji_ms7344};
const kanji_md kanji_md6398 = {0x6398, 1183, kanji_ms6398};
const kanji_md kanji_md55A7 = {0x55A7, 1184, kanji_ms55A7};
const kanji_md kanji_md9047 = {0x9047, 1185, kanji_ms9047};
const kanji_md kanji_md63F4 = {0x63F4, 1186, kanji_ms63F4};
const kanji_md kanji_md65E7 = {0x65E7, 1187, kanji_ms65E7};
const kanji_md kanji_md8AB2 = {0x8AB2, 1188, kanji_ms8AB2};
const kanji_md kanji_md8896 = {0x8896, 1189, kanji_ms8896};
const kanji_md kanji_md74B0 = {0x74B0, 1190, kanji_ms74B0};
const kanji_md kanji_md8108 = {0x8108, 1191, kanji_ms8108};
const kanji_md kanji_md5211 = {0x5211, 1192, kanji_ms5211};
const kanji_md kanji_md5178 = {0x5178, 1193, kanji_ms5178};
const kanji_md kanji_md507D = {0x507D, 1194, kanji_ms507D};
const kanji_md kanji_md6F54 = {0x6F54, 1195, kanji_ms6F54};
const kanji_md kanji_md6E0B = {0x6E0B, 1196, kanji_ms6E0B};
const kanji_md kanji_md52A3 = {0x52A3, 1197, kanji_ms52A3};
const kanji_md kanji_md53F1 = {0x53F1, 1198, kanji_ms53F1};
const kanji_md kanji_md8105 = {0x8105, 1199, kanji_ms8105};
const kanji_md kanji_md846C = {0x846C, 1200, kanji_ms846C};
const kanji_md kanji_md520A = {0x520A, 1201, kanji_ms520A};
const kanji_md kanji_md5805 = {0x5805, 1202, kanji_ms5805};
const kanji_md kanji_md5B63 = {0x5B63, 1203, kanji_ms5B63};
const kanji_md kanji_md5B64 = {0x5B64, 1204, kanji_ms5B64};
const kanji_md kanji_md725B = {0x725B, 1205, kanji_ms725B};
const kanji_md kanji_md7D22 = {0x7D22, 1206, kanji_ms7D22};
const kanji_md kanji_md7E26 = {0x7E26, 1207, kanji_ms7E26};
const kanji_md kanji_md8C8C = {0x8C8C, 1208, kanji_ms8C8C};
const kanji_md kanji_md5351 = {0x5351, 1209, kanji_ms5351};
const kanji_md kanji_md677E = {0x677E, 1210, kanji_ms677E};
const kanji_md kanji_md635C = {0x635C, 1211, kanji_ms635C};
const kanji_md kanji_md9810 = {0x9810, 1212, kanji_ms9810};
const kanji_md kanji_md63A7 = {0x63A7, 1213, kanji_ms63A7};
const kanji_md kanji_md4E73 = {0x4E73, 1214, kanji_ms4E73};
const kanji_md kanji_md6109 = {0x6109, 1215, kanji_ms6109};
const kanji_md kanji_md9769 = {0x9769, 1216, kanji_ms9769};
const kanji_md kanji_md7BC4 = {0x7BC4, 1217, kanji_ms7BC4};
const kanji_md kanji_md932F = {0x932F, 1218, kanji_ms932F};
const kanji_md kanji_md7C8B = {0x7C8B, 1219, kanji_ms7C8B};
const kanji_md kanji_md79C0 = {0x79C0, 1220, kanji_ms79C0};
const kanji_md kanji_md5275 = {0x5275, 1221, kanji_ms5275};
const kanji_md kanji_md9663 = {0x9663, 1222, kanji_ms9663};
const kanji_md kanji_md6691 = {0x6691, 1223, kanji_ms6691};
const kanji_md kanji_md5009 = {0x5009, 1224, kanji_ms5009};
const kanji_md kanji_md722A = {0x722A, 1225, kanji_ms722A};
const kanji_md kanji_md7AF6 = {0x7AF6, 1226, kanji_ms7AF6};
const kanji_md kanji_md7DB2 = {0x7DB2, 1227, kanji_ms7DB2};
const kanji_md kanji_md6E9C = {0x6E9C, 1228, kanji_ms6E9C};
const kanji_md kanji_md53CC = {0x53CC, 1229, kanji_ms53CC};
const kanji_md kanji_md9665 = {0x9665, 1230, kanji_ms9665};
const kanji_md kanji_md8A0E = {0x8A0E, 1231, kanji_ms8A0E};
const kanji_md kanji_md81E8 = {0x81E8, 1232, kanji_ms81E8};
const kanji_md kanji_md8AF8 = {0x8AF8, 1233, kanji_ms8AF8};
const kanji_md kanji_md6CBF = {0x6CBF, 1234, kanji_ms6CBF};
const kanji_md kanji_md8056 = {0x8056, 1235, kanji_ms8056};
const kanji_md kanji_md6B8A = {0x6B8A, 1236, kanji_ms6B8A};
const kanji_md kanji_md6458 = {0x6458, 1237, kanji_ms6458};
const kanji_md kanji_md8B1B = {0x8B1B, 1238, kanji_ms8B1B};
const kanji_md kanji_md5DE7 = {0x5DE7, 1239, kanji_ms5DE7};
const kanji_md kanji_md5203 = {0x5203, 1240, kanji_ms5203};
const kanji_md kanji_md9E97 = {0x9E97, 1241, kanji_ms9E97};
const kanji_md kanji_md6069 = {0x6069, 1242, kanji_ms6069};
const kanji_md kanji_md4F34 = {0x4F34, 1243, kanji_ms4F34};
const kanji_md kanji_md8CDB = {0x8CDB, 1244, kanji_ms8CDB};
const kanji_md kanji_md8A8C = {0x8A8C, 1245, kanji_ms8A8C};
const kanji_md kanji_md8DF3 = {0x8DF3, 1246, kanji_ms8DF3};
const kanji_md kanji_md9019 = {0x9019, 1247, kanji_ms9019};
const kanji_md kanji_md51CD = {0x51CD, 1248, kanji_ms51CD};
const kanji_md kanji_md7F70 = {0x7F70, 1249, kanji_ms7F70};
const kanji_md kanji_md9F13 = {0x9F13, 1250, kanji_ms9F13};
const kanji_md kanji_md6BBF = {0x6BBF, 1251, kanji_ms6BBF};
const kanji_md kanji_md9694 = {0x9694, 1252, kanji_ms9694};
const kanji_md kanji_md64AB = {0x64AB, 1253, kanji_ms64AB};
const kanji_md kanji_md5FB3 = {0x5FB3, 1254, kanji_ms5FB3};
const kanji_md kanji_md7815 = {0x7815, 1255, kanji_ms7815};
const kanji_md kanji_md84CB = {0x84CB, 1256, kanji_ms84CB};
const kanji_md kanji_md50AC = {0x50AC, 1257, kanji_ms50AC};
const kanji_md kanji_md6182 = {0x6182, 1258, kanji_ms6182};
const kanji_md kanji_md5531 = {0x5531, 1259, kanji_ms5531};
const kanji_md kanji_md6170 = {0x6170, 1260, kanji_ms6170};
const kanji_md kanji_md8457 = {0x8457, 1261, kanji_ms8457};
const kanji_md kanji_md7363 = {0x7363, 1262, kanji_ms7363};
const kanji_md kanji_md63C3 = {0x63C3, 1263, kanji_ms63C3};
const kanji_md kanji_md65BD = {0x65BD, 1264, kanji_ms65BD};
const kanji_md kanji_md51C4 = {0x51C4, 1265, kanji_ms51C4};
const kanji_md kanji_md62F3 = {0x62F3, 1266, kanji_ms62F3};
const kanji_md kanji_md7D5E = {0x7D5E, 1267, kanji_ms7D5E};
const kanji_md kanji_md99C5 = {0x99C5, 1268, kanji_ms99C5};
const kanji_md kanji_md7D00 = {0x7D00, 1269, kanji_ms7D00};
const kanji_md kanji_md7B52 = {0x7B52, 1270, kanji_ms7B52};
const kanji_md kanji_md6E67 = {0x6E67, 1271, kanji_ms6E67};
const kanji_md kanji_md7C97 = {0x7C97, 1272, kanji_ms7C97};
const kanji_md kanji_md5192 = {0x5192, 1273, kanji_ms5192};
const kanji_md kanji_md8B72 = {0x8B72, 1274, kanji_ms8B72};
const kanji_md kanji_md85E4 = {0x85E4, 1275, kanji_ms85E4};
const kanji_md kanji_md6795 = {0x6795, 1276, kanji_ms6795};
const kanji_md kanji_md6311 = {0x6311, 1277, kanji_ms6311};
const kanji_md kanji_md4E4F = {0x4E4F, 1278, kanji_ms4E4F};
const kanji_md kanji_md535A = {0x535A, 1279, kanji_ms535A};
const kanji_md kanji_md602F = {0x602F, 1280, kanji_ms602F};
const kanji_md kanji_md91CC = {0x91CC, 1281, kanji_ms91CC};
const kanji_md kanji_md6DBC = {0x6DBC, 1282, kanji_ms6DBC};
const kanji_md kanji_md8F03 = {0x8F03, 1283, kanji_ms8F03};
const kanji_md kanji_md4ECF = {0x4ECF, 1284, kanji_ms4ECF};
const kanji_md kanji_md5C31 = {0x5C31, 1285, kanji_ms5C31};
const kanji_md kanji_md5EC3 = {0x5EC3, 1286, kanji_ms5EC3};
const kanji_md kanji_md5442 = {0x5442, 1287, kanji_ms5442};
const kanji_md kanji_md6DB2 = {0x6DB2, 1288, kanji_ms6DB2};
const kanji_md kanji_md50D5 = {0x50D5, 1289, kanji_ms50D5};
const kanji_md kanji_md86C7 = {0x86C7, 1290, kanji_ms86C7};
const kanji_md kanji_md68C4 = {0x68C4, 1291, kanji_ms68C4};
const kanji_md kanji_md76E4 = {0x76E4, 1292, kanji_ms76E4};
const kanji_md kanji_md5F69 = {0x5F69, 1293, kanji_ms5F69};
const kanji_md kanji_md7C73 = {0x7C73, 1294, kanji_ms7C73};
const kanji_md kanji_md6C37 = {0x6C37, 1295, kanji_ms6C37};
const kanji_md kanji_md517C = {0x517C, 1296, kanji_ms517C};
const kanji_md kanji_md54B2 = {0x54B2, 1297, kanji_ms54B2};
const kanji_md kanji_md716E = {0x716E, 1298, kanji_ms716E};
const kanji_md kanji_md4FB5 = {0x4FB5, 1299, kanji_ms4FB5};
const kanji_md kanji_md53EC = {0x53EC, 1300, kanji_ms53EC};
const kanji_md kanji_md5E79 = {0x5E79, 1301, kanji_ms5E79};
const kanji_md kanji_md6CF3 = {0x6CF3, 1302, kanji_ms6CF3};
const kanji_md kanji_md60DA = {0x60DA, 1303, kanji_ms60DA};
const kanji_md kanji_md78E8 = {0x78E8, 1304, kanji_ms78E8};
const kanji_md kanji_md9038 = {0x9038, 1305, kanji_ms9038};
const kanji_md kanji_md546A = {0x546A, 1306, kanji_ms546A};
const kanji_md kanji_md5893 = {0x5893, 1307, kanji_ms5893};
const kanji_md kanji_md9396 = {0x9396, 1308, kanji_ms9396};
const kanji_md kanji_md61A4 = {0x61A4, 1309, kanji_ms61A4};
const kanji_md kanji_md5510 = {0x5510, 1310, kanji_ms5510};
const kanji_md kanji_md90A3 = {0x90A3, 1311, kanji_ms90A3};
const kanji_md kanji_md6C60 = {0x6C60, 1312, kanji_ms6C60};
const kanji_md kanji_md8A89 = {0x8A89, 1313, kanji_ms8A89};
const kanji_md kanji_md8B0E = {0x8B0E, 1314, kanji_ms8B0E};
const kanji_md kanji_md7372 = {0x7372, 1315, kanji_ms7372};
const kanji_md kanji_md6E7F = {0x6E7F, 1316, kanji_ms6E7F};
const kanji_md kanji_md7D2B = {0x7D2B, 1317, kanji_ms7D2B};
const kanji_md kanji_md707D = {0x707D, 1318, kanji_ms707D};
const kanji_md kanji_md63A1 = {0x63A1, 1319, kanji_ms63A1};
const kanji_md kanji_md5B22 = {0x5B22, 1320, kanji_ms5B22};
const kanji_md kanji_md91E3 = {0x91E3, 1321, kanji_ms91E3};
const kanji_md kanji_md6EDE = {0x6EDE, 1322, kanji_ms6EDE};
const kanji_md kanji_md6EB6 = {0x6EB6, 1323, kanji_ms6EB6};
const kanji_md kanji_md9042 = {0x9042, 1324, kanji_ms9042};
const kanji_md kanji_md638C = {0x638C, 1325, kanji_ms638C};
const kanji_md kanji_md8CE2 = {0x8CE2, 1326, kanji_ms8CE2};
const kanji_md kanji_md5E8F = {0x5E8F, 1327, kanji_ms5E8F};
const kanji_md kanji_md8A17 = {0x8A17, 1328, kanji_ms8A17};
const kanji_md kanji_md76CA = {0x76CA, 1329, kanji_ms76CA};
const kanji_md kanji_md4F50 = {0x4F50, 1330, kanji_ms4F50};
const kanji_md kanji_md66DC = {0x66DC, 1331, kanji_ms66DC};
const kanji_md kanji_md5353 = {0x5353, 1332, kanji_ms5353};
const kanji_md kanji_md7C92 = {0x7C92, 1333, kanji_ms7C92};
const kanji_md kanji_md5E3D = {0x5E3D, 1334, kanji_ms5E3D};
const kanji_md kanji_md7761 = {0x7761, 1335, kanji_ms7761};
const kanji_md kanji_md8A93 = {0x8A93, 1336, kanji_ms8A93};
const kanji_md kanji_md7AAE = {0x7AAE, 1337, kanji_ms7AAE};
const kanji_md kanji_md5265 = {0x5265, 1338, kanji_ms5265};
const kanji_md kanji_md68B0 = {0x68B0, 1339, kanji_ms68B0};
const kanji_md kanji_md5DE3 = {0x5DE3, 1340, kanji_ms5DE3};
const kanji_md kanji_md98FD = {0x98FD, 1341, kanji_ms98FD};
const kanji_md kanji_md6F22 = {0x6F22, 1342, kanji_ms6F22};
const kanji_md kanji_md58C7 = {0x58C7, 1343, kanji_ms58C7};
const kanji_md kanji_md8AA0 = {0x8AA0, 1344, kanji_ms8AA0};
const kanji_md kanji_md8B00 = {0x8B00, 1345, kanji_ms8B00};
const kanji_md kanji_md8A13 = {0x8A13, 1346, kanji_ms8A13};
const kanji_md kanji_md7D1B = {0x7D1B, 1347, kanji_ms7D1B};
const kanji_md kanji_md5674 = {0x5674, 1348, kanji_ms5674};
const kanji_md kanji_md98FC = {0x98FC, 1349, kanji_ms98FC};
const kanji_md kanji_md80A1 = {0x80A1, 1350, kanji_ms80A1};
const kanji_md kanji_md6D6A = {0x6D6A, 1351, kanji_ms6D6A};
const kanji_md kanji_md4FC3 = {0x4FC3, 1352, kanji_ms4FC3};
const kanji_md kanji_md99B4 = {0x99B4, 1353, kanji_ms99B4};
const kanji_md kanji_md518A = {0x518A, 1354, kanji_ms518A};
const kanji_md kanji_md8CED = {0x8CED, 1355, kanji_ms8CED};
const kanji_md kanji_md5384 = {0x5384, 1356, kanji_ms5384};
const kanji_md kanji_md51E1 = {0x51E1, 1357, kanji_ms51E1};
const kanji_md kanji_md636E = {0x636E, 1358, kanji_ms636E};
const kanji_md kanji_md92AD = {0x92AD, 1359, kanji_ms92AD};
const kanji_md kanji_md7A3C = {0x7A3C, 1360, kanji_ms7A3C};
const kanji_md kanji_md6CC9 = {0x6CC9, 1361, kanji_ms6CC9};
const kanji_md kanji_md5F6B = {0x5F6B, 1362, kanji_ms5F6B};
const kanji_md kanji_md72A0 = {0x72A0, 1363, kanji_ms72A0};
const kanji_md kanji_md7C60 = {0x7C60, 1364, kanji_ms7C60};
const kanji_md kanji_md7272 = {0x7272, 1365, kanji_ms7272};
const kanji_md kanji_md968F = {0x968F, 1366, kanji_ms968F};
const kanji_md kanji_md906D = {0x906D, 1367, kanji_ms906D};
const kanji_md kanji_md66C7 = {0x66C7, 1368, kanji_ms66C7};
const kanji_md kanji_md84BC = {0x84BC, 1369, kanji_ms84BC};
const kanji_md kanji_md72FC = {0x72FC, 1370, kanji_ms72FC};
const kanji_md kanji_md4FD7 = {0x4FD7, 1371, kanji_ms4FD7};
const kanji_md kanji_md77B3 = {0x77B3, 1372, kanji_ms77B3};
const kanji_md kanji_md9727 = {0x9727, 1373, kanji_ms9727};
const kanji_md kanji_md9B31 = {0x9B31, 1374, kanji_ms9B31};
const kanji_md kanji_md5B97 = {0x5B97, 1375, kanji_ms5B97};
const kanji_md kanji_md8A5E = {0x8A5E, 1376, kanji_ms8A5E};
const kanji_md kanji_md7E3E = {0x7E3E, 1377, kanji_ms7E3E};
const kanji_md kanji_md8997 = {0x8997, 1378, kanji_ms8997};
const kanji_md kanji_md5AC1 = {0x5AC1, 1379, kanji_ms5AC1};
const kanji_md kanji_md57A3 = {0x57A3, 1380, kanji_ms57A3};
const kanji_md kanji_md65E6 = {0x65E6, 1381, kanji_ms65E6};
const kanji_md kanji_md6E09 = {0x6E09, 1382, kanji_ms6E09};
const kanji_md kanji_md6D78 = {0x6D78, 1383, kanji_ms6D78};
const kanji_md kanji_md5B6B = {0x5B6B, 1384, kanji_ms5B6B};
const kanji_md kanji_md984E = {0x984E, 1385, kanji_ms984E};
const kanji_md kanji_md52B1 = {0x52B1, 1386, kanji_ms52B1};
const kanji_md kanji_md6CE1 = {0x6CE1, 1387, kanji_ms6CE1};
const kanji_md kanji_md7642 = {0x7642, 1388, kanji_ms7642};
const kanji_md kanji_md79D2 = {0x79D2, 1389, kanji_ms79D2};
const kanji_md kanji_md5629 = {0x5629, 1390, kanji_ms5629};
const kanji_md kanji_md58EE = {0x58EE, 1391, kanji_ms58EE};
const kanji_md kanji_md59D4 = {0x59D4, 1392, kanji_ms59D4};
const kanji_md kanji_md89A7 = {0x89A7, 1393, kanji_ms89A7};
const kanji_md kanji_md6F70 = {0x6F70, 1394, kanji_ms6F70};
const kanji_md kanji_md5374 = {0x5374, 1395, kanji_ms5374};
const kanji_md kanji_md7E2B = {0x7E2B, 1396, kanji_ms7E2B};
const kanji_md kanji_md67AF = {0x67AF, 1397, kanji_ms67AF};
const kanji_md kanji_md63B2 = {0x63B2, 1398, kanji_ms63B2};
const kanji_md kanji_md8CBC = {0x8CBC, 1399, kanji_ms8CBC};
const kanji_md kanji_md5237 = {0x5237, 1400, kanji_ms5237};
const kanji_md kanji_md82DB = {0x82DB, 1401, kanji_ms82DB};
const kanji_md kanji_md8FB1 = {0x8FB1, 1402, kanji_ms8FB1};
const kanji_md kanji_md75F4 = {0x75F4, 1403, kanji_ms75F4};
const kanji_md kanji_md7DBF = {0x7DBF, 1404, kanji_ms7DBF};
const kanji_md kanji_md5BFA = {0x5BFA, 1405, kanji_ms5BFA};
const kanji_md kanji_md5BE7 = {0x5BE7, 1406, kanji_ms5BE7};
const kanji_md kanji_md6E26 = {0x6E26, 1407, kanji_ms6E26};
const kanji_md kanji_md6BB4 = {0x6BB4, 1408, kanji_ms6BB4};
const kanji_md kanji_md6EF4 = {0x6EF4, 1409, kanji_ms6EF4};
const kanji_md kanji_md622F = {0x622F, 1410, kanji_ms622F};
const kanji_md kanji_md8D66 = {0x8D66, 1411, kanji_ms8D66};
const kanji_md kanji_md5DDE = {0x5DDE, 1412, kanji_ms5DDE};
const kanji_md kanji_md6C99 = {0x6C99, 1413, kanji_ms6C99};
const kanji_md kanji_md540A = {0x540A, 1414, kanji_ms540A};
const kanji_md kanji_md8A0A = {0x8A0A, 1415, kanji_ms8A0A};
const kanji_md kanji_md7768 = {0x7768, 1416, kanji_ms7768};
const kanji_md kanji_md6DAF = {0x6DAF, 1417, kanji_ms6DAF};
const kanji_md kanji_md7D0B = {0x7D0B, 1418, kanji_ms7D0B};
const kanji_md kanji_md7C4D = {0x7C4D, 1419, kanji_ms7C4D};
const kanji_md kanji_md8511 = {0x8511, 1420, kanji_ms8511};
const kanji_md kanji_md88FE = {0x88FE, 1421, kanji_ms88FE};
const kanji_md kanji_md6C5F = {0x6C5F, 1422, kanji_ms6C5F};
const kanji_md kanji_md5869 = {0x5869, 1423, kanji_ms5869};
const kanji_md kanji_md75C7 = {0x75C7, 1424, kanji_ms75C7};
const kanji_md kanji_md8870 = {0x8870, 1425, kanji_ms8870};
const kanji_md kanji_md5E9C = {0x5E9C, 1426, kanji_ms5E9C};
const kanji_md kanji_md6F20 = {0x6F20, 1427, kanji_ms6F20};
const kanji_md kanji_md9AB8 = {0x9AB8, 1428, kanji_ms9AB8};
const kanji_md kanji_md7B1B = {0x7B1B, 1429, kanji_ms7B1B};
const kanji_md kanji_md84B8 = {0x84B8, 1430, kanji_ms84B8};
const kanji_md kanji_md62E1 = {0x62E1, 1431, kanji_ms62E1};
const kanji_md kanji_md96F7 = {0x96F7, 1432, kanji_ms96F7};
const kanji_md kanji_md8FB2 = {0x8FB2, 1433, kanji_ms8FB2};
const kanji_md kanji_md50E7 = {0x50E7, 1434, kanji_ms50E7};
const kanji_md kanji_md75E9 = {0x75E9, 1435, kanji_ms75E9};
const kanji_md kanji_md7CA7 = {0x7CA7, 1436, kanji_ms7CA7};
const kanji_md kanji_md51F6 = {0x51F6, 1437, kanji_ms51F6};
const kanji_md kanji_md643A = {0x643A, 1438, kanji_ms643A};
const kanji_md kanji_md59D3 = {0x59D3, 1439, kanji_ms59D3};
const kanji_md kanji_md582A = {0x582A, 1440, kanji_ms582A};
const kanji_md kanji_md919C = {0x919C, 1441, kanji_ms919C};
const kanji_md kanji_md74F6 = {0x74F6, 1442, kanji_ms74F6};
const kanji_md kanji_md96C5 = {0x96C5, 1443, kanji_ms96C5};
const kanji_md kanji_md8302 = {0x8302, 1444, kanji_ms8302};
const kanji_md kanji_md75D5 = {0x75D5, 1445, kanji_ms75D5};
const kanji_md kanji_md5632 = {0x5632, 1446, kanji_ms5632};
const kanji_md kanji_md4FFA = {0x4FFA, 1447, kanji_ms4FFA};
const kanji_md kanji_md7FFB = {0x7FFB, 1448, kanji_ms7FFB};
const kanji_md kanji_md5B87 = {0x5B87, 1449, kanji_ms5B87};
const kanji_md kanji_md52E7 = {0x52E7, 1450, kanji_ms52E7};
const kanji_md kanji_md8A95 = {0x8A95, 1451, kanji_ms8A95};
const kanji_md kanji_md895F = {0x895F, 1452, kanji_ms895F};
const kanji_md kanji_md8C46 = {0x8C46, 1453, kanji_ms8C46};
const kanji_md kanji_md584A = {0x584A, 1454, kanji_ms584A};
const kanji_md kanji_md8AE6 = {0x8AE6, 1455, kanji_ms8AE6};
const kanji_md kanji_md6E2F = {0x6E2F, 1456, kanji_ms6E2F};
const kanji_md kanji_md83DC = {0x83DC, 1457, kanji_ms83DC};
const kanji_md kanji_md5E7D = {0x5E7D, 1458, kanji_ms5E7D};
const kanji_md kanji_md524A = {0x524A, 1459, kanji_ms524A};
const kanji_md kanji_md7832 = {0x7832, 1460, kanji_ms7832};
const kanji_md kanji_md6020 = {0x6020, 1461, kanji_ms6020};
const kanji_md kanji_md63BB = {0x63BB, 1462, kanji_ms63BB};
const kanji_md kanji_md55AB = {0x55AB, 1463, kanji_ms55AB};
const kanji_md kanji_md553E = {0x553E, 1464, kanji_ms553E};
const kanji_md kanji_md8D08 = {0x8D08, 1465, kanji_ms8D08};
const kanji_md kanji_md93AE = {0x93AE, 1466, kanji_ms93AE};
const kanji_md kanji_md59AC = {0x59AC, 1467, kanji_ms59AC};
const kanji_md kanji_md682A = {0x682A, 1468, kanji_ms682A};
const kanji_md kanji_md5747 = {0x5747, 1469, kanji_ms5747};
const kanji_md kanji_md4E18 = {0x4E18, 1470, kanji_ms4E18};
const kanji_md kanji_md6D25 = {0x6D25, 1471, kanji_ms6D25};
const kanji_md kanji_md67B6 = {0x67B6, 1472, kanji_ms67B6};
const kanji_md kanji_md819A = {0x819A, 1473, kanji_ms819A};
const kanji_md kanji_md6FC1 = {0x6FC1, 1474, kanji_ms6FC1};
const kanji_md kanji_md7551 = {0x7551, 1475, kanji_ms7551};
const kanji_md kanji_md65D7 = {0x65D7, 1476, kanji_ms65D7};
const kanji_md kanji_md9262 = {0x9262, 1477, kanji_ms9262};
const kanji_md kanji_md7DB1 = {0x7DB1, 1478, kanji_ms7DB1};
const kanji_md kanji_md6115 = {0x6115, 1479, kanji_ms6115};
const kanji_md kanji_md594F = {0x594F, 1480, kanji_ms594F};
const kanji_md kanji_md7E04 = {0x7E04, 1481, kanji_ms7E04};
const kanji_md kanji_md614C = {0x614C, 1482, kanji_ms614C};
const kanji_md kanji_md8102 = {0x8102, 1483, kanji_ms8102};
const kanji_md kanji_md9283 = {0x9283, 1484, kanji_ms9283};
const kanji_md kanji_md81C6 = {0x81C6, 1485, kanji_ms81C6};
const kanji_md kanji_md9234 = {0x9234, 1486, kanji_ms9234};
const kanji_md kanji_md7AE5 = {0x7AE5, 1487, kanji_ms7AE5};
const kanji_md kanji_md7DE9 = {0x7DE9, 1488, kanji_ms7DE9};
const kanji_md kanji_md80A5 = {0x80A5, 1489, kanji_ms80A5};
const kanji_md kanji_md732E = {0x732E, 1490, kanji_ms732E};
const kanji_md kanji_md9298 = {0x9298, 1491, kanji_ms9298};
const kanji_md kanji_md5375 = {0x5375, 1492, kanji_ms5375};
const kanji_md kanji_md6C70 = {0x6C70, 1493, kanji_ms6C70};
const kanji_md kanji_md906E = {0x906E, 1494, kanji_ms906E};
const kanji_md kanji_md65CB = {0x65CB, 1495, kanji_ms65CB};
const kanji_md kanji_md7F85 = {0x7F85, 1496, kanji_ms7F85};
const kanji_md kanji_md6392 = {0x6392, 1497, kanji_ms6392};
const kanji_md kanji_md7AF9 = {0x7AF9, 1498, kanji_ms7AF9};
const kanji_md kanji_md5C16 = {0x5C16, 1499, kanji_ms5C16};
const kanji_md kanji_md8CA8 = {0x8CA8, 1500, kanji_ms8CA8};
const kanji_md kanji_md7A3D = {0x7A3D, 1501, kanji_ms7A3D};
const kanji_md kanji_md4F0A = {0x4F0A, 1502, kanji_ms4F0A};
const kanji_md kanji_md9084 = {0x9084, 1503, kanji_ms9084};
const kanji_md kanji_md80C3 = {0x80C3, 1504, kanji_ms80C3};
const kanji_md kanji_md9451 = {0x9451, 1505, kanji_ms9451};
const kanji_md kanji_md702C = {0x702C, 1506, kanji_ms702C};
const kanji_md kanji_md7B26 = {0x7B26, 1507, kanji_ms7B26};
const kanji_md kanji_md76FE = {0x76FE, 1508, kanji_ms76FE};
const kanji_md kanji_md60A3 = {0x60A3, 1509, kanji_ms60A3};
const kanji_md kanji_md5C65 = {0x5C65, 1510, kanji_ms5C65};
const kanji_md kanji_md515A = {0x515A, 1511, kanji_ms515A};
const kanji_md kanji_md6EA2 = {0x6EA2, 1512, kanji_ms6EA2};
const kanji_md kanji_md7F72 = {0x7F72, 1513, kanji_ms7F72};
const kanji_md kanji_md80F4 = {0x80F4, 1514, kanji_ms80F4};
const kanji_md kanji_md9178 = {0x9178, 1515, kanji_ms9178};
const kanji_md kanji_md511F = {0x511F, 1516, kanji_ms511F};
const kanji_md kanji_md50DA = {0x50DA, 1517, kanji_ms50DA};
const kanji_md kanji_md629E = {0x629E, 1518, kanji_ms629E};
const kanji_md kanji_md6D5C = {0x6D5C, 1519, kanji_ms6D5C};
const kanji_md kanji_md6589 = {0x6589, 1520, kanji_ms6589};
const kanji_md kanji_md6168 = {0x6168, 1521, kanji_ms6168};
const kanji_md kanji_md5A46 = {0x5A46, 1522, kanji_ms5A46};
const kanji_md kanji_md6B6A = {0x6B6A, 1523, kanji_ms6B6A};
const kanji_md kanji_md65E8 = {0x65E8, 1524, kanji_ms65E8};
const kanji_md kanji_md55C5 = {0x55C5, 1525, kanji_ms55C5};
const kanji_md kanji_md81A8 = {0x81A8, 1526, kanji_ms81A8};
const kanji_md kanji_md6F0F = {0x6F0F, 1527, kanji_ms6F0F};
const kanji_md kanji_md60A0 = {0x60A0, 1528, kanji_ms60A0};
const kanji_md kanji_md54B3 = {0x54B3, 1529, kanji_ms54B3};
const kanji_md kanji_md83D3 = {0x83D3, 1530, kanji_ms83D3};
const kanji_md kanji_md91D8 = {0x91D8, 1531, kanji_ms91D8};
const kanji_md kanji_md7DAD = {0x7DAD, 1532, kanji_ms7DAD};
const kanji_md kanji_md5949 = {0x5949, 1533, kanji_ms5949};
const kanji_md kanji_md6982 = {0x6982, 1534, kanji_ms6982};
const kanji_md kanji_md585E = {0x585E, 1535, kanji_ms585E};
const kanji_md kanji_md6562 = {0x6562, 1536, kanji_ms6562};
const kanji_md kanji_md5951 = {0x5951, 1537, kanji_ms5951};
const kanji_md kanji_md99B3 = {0x99B3, 1538, kanji_ms99B3};
const kanji_md kanji_md963F = {0x963F, 1539, kanji_ms963F};
const kanji_md kanji_md5D50 = {0x5D50, 1540, kanji_ms5D50};
const kanji_md kanji_md7D10 = {0x7D10, 1541, kanji_ms7D10};
const kanji_md kanji_md5AC9 = {0x5AC9, 1542, kanji_ms5AC9};
const kanji_md kanji_md631F = {0x631F, 1543, kanji_ms631F};
const kanji_md kanji_md6D1E = {0x6D1E, 1544, kanji_ms6D1E};
const kanji_md kanji_md96C7 = {0x96C7, 1545, kanji_ms96C7};
const kanji_md kanji_md8A69 = {0x8A69, 1546, kanji_ms8A69};
const kanji_md kanji_md8358 = {0x8358, 1547, kanji_ms8358};
const kanji_md kanji_md990C = {0x990C, 1548, kanji_ms990C};
const kanji_md kanji_md7763 = {0x7763, 1549, kanji_ms7763};
const kanji_md kanji_md8A3A = {0x8A3A, 1550, kanji_ms8A3A};
const kanji_md kanji_md628A = {0x628A, 1551, kanji_ms628A};
const kanji_md kanji_md6627 = {0x6627, 1552, kanji_ms6627};
const kanji_md kanji_md5FCC = {0x5FCC, 1553, kanji_ms5FCC};
const kanji_md kanji_md5996 = {0x5996, 1554, kanji_ms5996};
const kanji_md kanji_md4EAD = {0x4EAD, 1555, kanji_ms4EAD};
const kanji_md kanji_md5BFF = {0x5BFF, 1556, kanji_ms5BFF};
const kanji_md kanji_md7F75 = {0x7F75, 1557, kanji_ms7F75};
const kanji_md kanji_md5BB4 = {0x5BB4, 1558, kanji_ms5BB4};
const kanji_md kanji_md8098 = {0x8098, 1559, kanji_ms8098};
const kanji_md kanji_md5835 = {0x5835, 1560, kanji_ms5835};
const kanji_md kanji_md526F = {0x526F, 1561, kanji_ms526F};
const kanji_md kanji_md99D0 = {0x99D0, 1562, kanji_ms99D0};
const kanji_md kanji_md60B6 = {0x60B6, 1563, kanji_ms60B6};
const kanji_md kanji_md6590 = {0x6590, 1564, kanji_ms6590};
const kanji_md kanji_md7FFC = {0x7FFC, 1565, kanji_ms7FFC};
const kanji_md kanji_md6C41 = {0x6C41, 1566, kanji_ms6C41};
const kanji_md kanji_md5875 = {0x5875, 1567, kanji_ms5875};
const kanji_md kanji_md77DB = {0x77DB, 1568, kanji_ms77DB};
const kanji_md kanji_md755C = {0x755C, 1569, kanji_ms755C};
const kanji_md kanji_md9676 = {0x9676, 1570, kanji_ms9676};
const kanji_md kanji_md5F90 = {0x5F90, 1571, kanji_ms5F90};
const kanji_md kanji_md8A6E = {0x8A6E, 1572, kanji_ms8A6E};
const kanji_md kanji_md72E9 = {0x72E9, 1573, kanji_ms72E9};
const kanji_md kanji_md5264 = {0x5264, 1574, kanji_ms5264};
const kanji_md kanji_md63B4 = {0x63B4, 1575, kanji_ms63B4};
const kanji_md kanji_md65E2 = {0x65E2, 1576, kanji_ms65E2};
const kanji_md kanji_md9805 = {0x9805, 1577, kanji_ms9805};
const kanji_md kanji_md76C6 = {0x76C6, 1578, kanji_ms76C6};
const kanji_md kanji_md822A = {0x822A, 1579, kanji_ms822A};
const kanji_md kanji_md821F = {0x821F, 1580, kanji_ms821F};
const kanji_md kanji_md55AA = {0x55AA, 1581, kanji_ms55AA};
const kanji_md kanji_md621A = {0x621A, 1582, kanji_ms621A};
const kanji_md kanji_md925B = {0x925B, 1583, kanji_ms925B};
const kanji_md kanji_md5854 = {0x5854, 1584, kanji_ms5854};
const kanji_md kanji_md6CB8 = {0x6CB8, 1585, kanji_ms6CB8};
const kanji_md kanji_md5CA1 = {0x5CA1, 1586, kanji_ms5CA1};
const kanji_md kanji_md6148 = {0x6148, 1587, kanji_ms6148};
const kanji_md kanji_md64AE = {0x64AE, 1588, kanji_ms64AE};
const kanji_md kanji_md98E2 = {0x98E2, 1589, kanji_ms98E2};
const kanji_md kanji_md662D = {0x662D, 1590, kanji_ms662D};
const kanji_md kanji_md559A = {0x559A, 1591, kanji_ms559A};
const kanji_md kanji_md8CAF = {0x8CAF, 1592, kanji_ms8CAF};
const kanji_md kanji_md770C = {0x770C, 1593, kanji_ms770C};
const kanji_md kanji_md5BDB = {0x5BDB, 1594, kanji_ms5BDB};
const kanji_md kanji_md5538 = {0x5538, 1595, kanji_ms5538};
const kanji_md kanji_md758E = {0x758E, 1596, kanji_ms758E};
const kanji_md kanji_md7FA8 = {0x7FA8, 1597, kanji_ms7FA8};
const kanji_md kanji_md74A7 = {0x74A7, 1598, kanji_ms74A7};
const kanji_md kanji_md685C = {0x685C, 1599, kanji_ms685C};
const kanji_md kanji_md4E39 = {0x4E39, 1600, kanji_ms4E39};
const kanji_md kanji_md55B0 = {0x55B0, 1601, kanji_ms55B0};
const kanji_md kanji_md8650 = {0x8650, 1602, kanji_ms8650};
const kanji_md kanji_md4EC1 = {0x4EC1, 1603, kanji_ms4EC1};
const kanji_md kanji_md82BD = {0x82BD, 1604, kanji_ms82BD};
const kanji_md kanji_md6D29 = {0x6D29, 1605, kanji_ms6D29};
const kanji_md kanji_md5F04 = {0x5F04, 1606, kanji_ms5F04};
const kanji_md kanji_md5D0E = {0x5D0E, 1607, kanji_ms5D0E};
const kanji_md kanji_md5E1D = {0x5E1D, 1608, kanji_ms5E1D};
const kanji_md kanji_md90B8 = {0x90B8, 1609, kanji_ms90B8};
const kanji_md kanji_md54F2 = {0x54F2, 1610, kanji_ms54F2};
const kanji_md kanji_md64E6 = {0x64E6, 1611, kanji_ms64E6};
const kanji_md kanji_md9867 = {0x9867, 1612, kanji_ms9867};
const kanji_md kanji_md6279 = {0x6279, 1613, kanji_ms6279};
const kanji_md kanji_md545F = {0x545F, 1614, kanji_ms545F};
const kanji_md kanji_md504F = {0x504F, 1615, kanji_ms504F};
const kanji_md kanji_md81E3 = {0x81E3, 1616, kanji_ms81E3};
const kanji_md kanji_md5984 = {0x5984, 1617, kanji_ms5984};
const kanji_md kanji_md5104 = {0x5104, 1618, kanji_ms5104};
const kanji_md kanji_md7A32 = {0x7A32, 1619, kanji_ms7A32};
const kanji_md kanji_md9813 = {0x9813, 1620, kanji_ms9813};
const kanji_md kanji_md6EBA = {0x6EBA, 1621, kanji_ms6EBA};
const kanji_md kanji_md75BE = {0x75BE, 1622, kanji_ms75BE};
const kanji_md kanji_md6BBB = {0x6BBB, 1623, kanji_ms6BBB};
const kanji_md kanji_md662F = {0x662F, 1624, kanji_ms662F};
const kanji_md kanji_md7652 = {0x7652, 1625, kanji_ms7652};
const kanji_md kanji_md6756 = {0x6756, 1626, kanji_ms6756};
const kanji_md kanji_md4FAE = {0x4FAE, 1627, kanji_ms4FAE};
const kanji_md kanji_md7C98 = {0x7C98, 1628, kanji_ms7C98};
const kanji_md kanji_md70AD = {0x70AD, 1629, kanji_ms70AD};
const kanji_md kanji_md61C7 = {0x61C7, 1630, kanji_ms61C7};
const kanji_md kanji_md6469 = {0x6469, 1631, kanji_ms6469};
const kanji_md kanji_md9EA6 = {0x9EA6, 1632, kanji_ms9EA6};
const kanji_md kanji_md9192 = {0x9192, 1633, kanji_ms9192};
const kanji_md kanji_md6367 = {0x6367, 1634, kanji_ms6367};
const kanji_md kanji_md9591 = {0x9591, 1635, kanji_ms9591};
const kanji_md kanji_md65AC = {0x65AC, 1636, kanji_ms65AC};
const kanji_md kanji_md59EB = {0x59EB, 1637, kanji_ms59EB};
const kanji_md kanji_md5840 = {0x5840, 1638, kanji_ms5840};
const kanji_md kanji_md57C3 = {0x57C3, 1639, kanji_ms57C3};
const kanji_md kanji_md733F = {0x733F, 1640, kanji_ms733F};
const kanji_md kanji_md90ED = {0x90ED, 1641, kanji_ms90ED};
const kanji_md kanji_md7A1A = {0x7A1A, 1642, kanji_ms7A1A};
const kanji_md kanji_md6CBC = {0x6CBC, 1643, kanji_ms6CBC};
const kanji_md kanji_md7259 = {0x7259, 1644, kanji_ms7259};
const kanji_md kanji_md7ADC = {0x7ADC, 1645, kanji_ms7ADC};
const kanji_md kanji_md8276 = {0x8276, 1646, kanji_ms8276};
const kanji_md kanji_md4E5E = {0x4E5E, 1647, kanji_ms4E5E};
const kanji_md kanji_md935B = {0x935B, 1648, kanji_ms935B};
const kanji_md kanji_md5F84 = {0x5F84, 1649, kanji_ms5F84};
const kanji_md kanji_md74E6 = {0x74E6, 1650, kanji_ms74E6};
const kanji_md kanji_md8A6B = {0x8A6B, 1651, kanji_ms8A6B};
const kanji_md kanji_md5075 = {0x5075, 1652, kanji_ms5075};
const kanji_md kanji_md8B90 = {0x8B90, 1653, kanji_ms8B90};
const kanji_md kanji_md9418 = {0x9418, 1654, kanji_ms9418};
const kanji_md kanji_md6F01 = {0x6F01, 1655, kanji_ms6F01};
const kanji_md kanji_md878D = {0x878D, 1656, kanji_ms878D};
const kanji_md kanji_md6E56 = {0x6E56, 1657, kanji_ms6E56};
const kanji_md kanji_md7A3F = {0x7A3F, 1658, kanji_ms7A3F};
const kanji_md kanji_md5954 = {0x5954, 1659, kanji_ms5954};
const kanji_md kanji_md8AFE = {0x8AFE, 1660, kanji_ms8AFE};
const kanji_md kanji_md59A8 = {0x59A8, 1661, kanji_ms59A8};
const kanji_md kanji_md7729 = {0x7729, 1662, kanji_ms7729};
const kanji_md kanji_md75FA = {0x75FA, 1663, kanji_ms75FA};
const kanji_md kanji_md9320 = {0x9320, 1664, kanji_ms9320};
const kanji_md kanji_md718A = {0x718A, 1665, kanji_ms718A};
const kanji_md kanji_md4E80 = {0x4E80, 1666, kanji_ms4E80};
const kanji_md kanji_md7F8A = {0x7F8A, 1667, kanji_ms7F8A};
const kanji_md kanji_md9583 = {0x9583, 1668, kanji_ms9583};
const kanji_md kanji_md6190 = {0x6190, 1669, kanji_ms6190};
const kanji_md kanji_md558B = {0x558B, 1670, kanji_ms558B};
const kanji_md kanji_md7E4A = {0x7E4A, 1671, kanji_ms7E4A};
const kanji_md kanji_md5750 = {0x5750, 1672, kanji_ms5750};
const kanji_md kanji_md76BA = {0x76BA, 1673, kanji_ms76BA};
const kanji_md kanji_md6602 = {0x6602, 1674, kanji_ms6602};
const kanji_md kanji_md6885 = {0x6885, 1675, kanji_ms6885};
const kanji_md kanji_md7687 = {0x7687, 1676, kanji_ms7687};
const kanji_md kanji_md6FEF = {0x6FEF, 1677, kanji_ms6FEF};
const kanji_md kanji_md4F3A = {0x4F3A, 1678, kanji_ms4F3A};
const kanji_md kanji_md8D05 = {0x8D05, 1679, kanji_ms8D05};
const kanji_md kanji_md73E0 = {0x73E0, 1680, kanji_ms73E0};
const kanji_md kanji_md6838 = {0x6838, 1681, kanji_ms6838};
const kanji_md kanji_md8EDF = {0x8EDF, 1682, kanji_ms8EDF};
const kanji_md kanji_md51A0 = {0x51A0, 1683, kanji_ms51A0};
const kanji_md kanji_md90CA = {0x90CA, 1684, kanji_ms90CA};
const kanji_md kanji_md8F38 = {0x8F38, 1685, kanji_ms8F38};
const kanji_md kanji_md76F2 = {0x76F2, 1686, kanji_ms76F2};
const kanji_md kanji_md658E = {0x658E, 1687, kanji_ms658E};
const kanji_md kanji_md6F2B = {0x6F2B, 1688, kanji_ms6F2B};
const kanji_md kanji_md6070 = {0x6070, 1689, kanji_ms6070};
const kanji_md kanji_md559D = {0x559D, 1690, kanji_ms559D};
const kanji_md kanji_md5098 = {0x5098, 1691, kanji_ms5098};
const kanji_md kanji_md8CC3 = {0x8CC3, 1692, kanji_ms8CC3};
const kanji_md kanji_md62D7 = {0x62D7, 1693, kanji_ms62D7};
const kanji_md kanji_md6717 = {0x6717, 1694, kanji_ms6717};
const kanji_md kanji_md9285 = {0x9285, 1695, kanji_ms9285};
const kanji_md kanji_md5948 = {0x5948, 1696, kanji_ms5948};
const kanji_md kanji_md6B3A = {0x6B3A, 1697, kanji_ms6B3A};
const kanji_md kanji_md6247 = {0x6247, 1698, kanji_ms6247};
const kanji_md kanji_md7A0E = {0x7A0E, 1699, kanji_ms7A0E};
const kanji_md kanji_md56C1 = {0x56C1, 1700, kanji_ms56C1};
const kanji_md kanji_md9A0E = {0x9A0E, 1701, kanji_ms9A0E};
const kanji_md kanji_md68F2 = {0x68F2, 1702, kanji_ms68F2};
const kanji_md kanji_md7089 = {0x7089, 1703, kanji_ms7089};
const kanji_md kanji_md80AF = {0x80AF, 1704, kanji_ms80AF};
const kanji_md kanji_md80A2 = {0x80A2, 1705, kanji_ms80A2};
const kanji_md kanji_md5208 = {0x5208, 1706, kanji_ms5208};
const kanji_md kanji_md62D8 = {0x62D8, 1707, kanji_ms62D8};
const kanji_md kanji_md84C4 = {0x84C4, 1708, kanji_ms84C4};
const kanji_md kanji_md4F2F = {0x4F2F, 1709, kanji_ms4F2F};
const kanji_md kanji_md52DF = {0x52DF, 1710, kanji_ms52DF};
const kanji_md kanji_md62AB = {0x62AB, 1711, kanji_ms62AB};
const kanji_md kanji_md67A0 = {0x67A0, 1712, kanji_ms67A0};
const kanji_md kanji_md6790 = {0x6790, 1713, kanji_ms6790};
const kanji_md kanji_md6349 = {0x6349, 1714, kanji_ms6349};
const kanji_md kanji_md5F13 = {0x5F13, 1715, kanji_ms5F13};
const kanji_md kanji_md5146 = {0x5146, 1716, kanji_ms5146};
const kanji_md kanji_md5F81 = {0x5F81, 1717, kanji_ms5F81};
const kanji_md kanji_md832B = {0x832B, 1718, kanji_ms832B};
const kanji_md kanji_md57A2 = {0x57A2, 1719, kanji_ms57A2};
const kanji_md kanji_md61A7 = {0x61A7, 1720, kanji_ms61A7};
const kanji_md kanji_md80BA = {0x80BA, 1721, kanji_ms80BA};
const kanji_md kanji_md6843 = {0x6843, 1722, kanji_ms6843};
const kanji_md kanji_md8F5F = {0x8F5F, 1723, kanji_ms8F5F};
const kanji_md kanji_md6E07 = {0x6E07, 1724, kanji_ms6E07};
const kanji_md kanji_md934B = {0x934B, 1725, kanji_ms934B};
const kanji_md kanji_md6191 = {0x6191, 1726, kanji_ms6191};
const kanji_md kanji_md8A1D = {0x8A1D, 1727, kanji_ms8A1D};
const kanji_md kanji_md723D = {0x723D, 1728, kanji_ms723D};
const kanji_md kanji_md5962 = {0x5962, 1729, kanji_ms5962};
const kanji_md kanji_md5448 = {0x5448, 1730, kanji_ms5448};
const kanji_md kanji_md633F = {0x633F, 1731, kanji_ms633F};
const kanji_md kanji_md7D3A = {0x7D3A, 1732, kanji_ms7D3A};
const kanji_md kanji_md7267 = {0x7267, 1733, kanji_ms7267};
const kanji_md kanji_md5E81 = {0x5E81, 1734, kanji_ms5E81};
const kanji_md kanji_md6F64 = {0x6F64, 1735, kanji_ms6F64};
const kanji_md kanji_md7D33 = {0x7D33, 1736, kanji_ms7D33};
const kanji_md kanji_md58A8 = {0x58A8, 1737, kanji_ms58A8};
const kanji_md kanji_md66D6 = {0x66D6, 1738, kanji_ms66D6};
const kanji_md kanji_md5D16 = {0x5D16, 1739, kanji_ms5D16};
const kanji_md kanji_md9AED = {0x9AED, 1740, kanji_ms9AED};
const kanji_md kanji_md67F3 = {0x67F3, 1741, kanji_ms67F3};
const kanji_md kanji_md9DF9 = {0x9DF9, 1742, kanji_ms9DF9};
const kanji_md kanji_md8E87 = {0x8E87, 1743, kanji_ms8E87};
const kanji_md kanji_md8E8A = {0x8E8A, 1744, kanji_ms8E8A};
const kanji_md kanji_md8912 = {0x8912, 1745, kanji_ms8912};
const kanji_md kanji_md5DFE = {0x5DFE, 1746, kanji_ms5DFE};
const kanji_md kanji_md90F5 = {0x90F5, 1747, kanji_ms90F5};
const kanji_md kanji_md5420 = {0x5420, 1748, kanji_ms5420};
const kanji_md kanji_md4E4B = {0x4E4B, 1749, kanji_ms4E4B};
const kanji_md kanji_md983B = {0x983B, 1750, kanji_ms983B};
const kanji_md kanji_md6D44 = {0x6D44, 1751, kanji_ms6D44};
const kanji_md kanji_md667A = {0x667A, 1752, kanji_ms667A};
const kanji_md kanji_md8CC0 = {0x8CC0, 1753, kanji_ms8CC0};
const kanji_md kanji_md7D79 = {0x7D79, 1754, kanji_ms7D79};
const kanji_md kanji_md7E4B = {0x7E4B, 1755, kanji_ms7E4B};
const kanji_md kanji_md819C = {0x819C, 1756, kanji_ms819C};
const kanji_md kanji_md71E5 = {0x71E5, 1757, kanji_ms71E5};
const kanji_md kanji_md7A00 = {0x7A00, 1758, kanji_ms7A00};
const kanji_md kanji_md9855 = {0x9855, 1759, kanji_ms9855};
const kanji_md kanji_md72FD = {0x72FD, 1760, kanji_ms72FD};
const kanji_md kanji_md9686 = {0x9686, 1761, kanji_ms9686};
const kanji_md kanji_md5B54 = {0x5B54, 1762, kanji_ms5B54};
const kanji_md kanji_md916C = {0x916C, 1763, kanji_ms916C};
const kanji_md kanji_md6234 = {0x6234, 1764, kanji_ms6234};
const kanji_md kanji_md60F9 = {0x60F9, 1765, kanji_ms60F9};
const kanji_md kanji_md6734 = {0x6734, 1766, kanji_ms6734};
const kanji_md kanji_md7BB8 = {0x7BB8, 1767, kanji_ms7BB8};
const kanji_md kanji_md69CC = {0x69CC, 1768, kanji_ms69CC};
const kanji_md kanji_md61A9 = {0x61A9, 1769, kanji_ms61A9};
const kanji_md kanji_md60A6 = {0x60A6, 1770, kanji_ms60A6};
const kanji_md kanji_md864E = {0x864E, 1771, kanji_ms864E};
const kanji_md kanji_md5B9B = {0x5B9B, 1772, kanji_ms5B9B};
const kanji_md kanji_md6B04 = {0x6B04, 1773, kanji_ms6B04};
const kanji_md kanji_md6676 = {0x6676, 1774, kanji_ms6676};
const kanji_md kanji_md8ECC = {0x8ECC, 1775, kanji_ms8ECC};
const kanji_md kanji_md547B = {0x547B, 1776, kanji_ms547B};
const kanji_md kanji_md80E1 = {0x80E1, 1777, kanji_ms80E1};
const kanji_md kanji_md963B = {0x963B, 1778, kanji_ms963B};
const kanji_md kanji_md8776 = {0x8776, 1779, kanji_ms8776};
const kanji_md kanji_md6EDD = {0x6EDD, 1780, kanji_ms6EDD};
const kanji_md kanji_md77AD = {0x77AD, 1781, kanji_ms77AD};
const kanji_md kanji_md6731 = {0x6731, 1782, kanji_ms6731};
const kanji_md kanji_md5EFB = {0x5EFB, 1783, kanji_ms5EFB};
const kanji_md kanji_md6028 = {0x6028, 1784, kanji_ms6028};
const kanji_md kanji_md7DBA = {0x7DBA, 1785, kanji_ms7DBA};
const kanji_md kanji_md69CD = {0x69CD, 1786, kanji_ms69CD};
const kanji_md kanji_md7CD6 = {0x7CD6, 1787, kanji_ms7CD6};
const kanji_md kanji_md68DF = {0x68DF, 1788, kanji_ms68DF};
const kanji_md kanji_md8CB0 = {0x8CB0, 1789, kanji_ms8CB0};
const kanji_md kanji_md8607 = {0x8607, 1790, kanji_ms8607};
const kanji_md kanji_md754F = {0x754F, 1791, kanji_ms754F};
const kanji_md kanji_md902E = {0x902E, 1792, kanji_ms902E};
const kanji_md kanji_md51B4 = {0x51B4, 1793, kanji_ms51B4};
const kanji_md kanji_md8FBF = {0x8FBF, 1794, kanji_ms8FBF};
const kanji_md kanji_md4EC7 = {0x4EC7, 1795, kanji_ms4EC7};
const kanji_md kanji_md8CCA = {0x8CCA, 1796, kanji_ms8CCA};
const kanji_md kanji_md6144 = {0x6144, 1797, kanji_ms6144};
const kanji_md kanji_md54BD = {0x54BD, 1798, kanji_ms54BD};
const kanji_md kanji_md5815 = {0x5815, 1799, kanji_ms5815};
const kanji_md kanji_md9673 = {0x9673, 1800, kanji_ms9673};
const kanji_md kanji_md6C72 = {0x6C72, 1801, kanji_ms6C72};
const kanji_md kanji_md7B87 = {0x7B87, 1802, kanji_ms7B87};
const kanji_md kanji_md8CD1 = {0x8CD1, 1803, kanji_ms8CD1};
const kanji_md kanji_md5516 = {0x5516, 1804, kanji_ms5516};
const kanji_md kanji_md63C9 = {0x63C9, 1805, kanji_ms63C9};
const kanji_md kanji_md5132 = {0x5132, 1806, kanji_ms5132};
const kanji_md kanji_md6E7E = {0x6E7E, 1807, kanji_ms6E7E};
const kanji_md kanji_md731F = {0x731F, 1808, kanji_ms731F};
const kanji_md kanji_md660F = {0x660F, 1809, kanji_ms660F};
const kanji_md kanji_md6155 = {0x6155, 1810, kanji_ms6155};
const kanji_md kanji_md6749 = {0x6749, 1811, kanji_ms6749};
const kanji_md kanji_md5D07 = {0x5D07, 1812, kanji_ms5D07};
const kanji_md kanji_md61F2 = {0x61F2, 1813, kanji_ms61F2};
const kanji_md kanji_md8C9E = {0x8C9E, 1814, kanji_ms8C9E};
const kanji_md kanji_md82B3 = {0x82B3, 1815, kanji_ms82B3};
const kanji_md kanji_md97AD = {0x97AD, 1816, kanji_ms97AD};
const kanji_md kanji_md5C3A = {0x5C3A, 1817, kanji_ms5C3A};
const kanji_md kanji_md7169 = {0x7169, 1818, kanji_ms7169};
const kanji_md kanji_md7F60 = {0x7F60, 1819, kanji_ms7F60};
const kanji_md kanji_md53D4 = {0x53D4, 1820, kanji_ms53D4};
const kanji_md kanji_md8217 = {0x8217, 1821, kanji_ms8217};
const kanji_md kanji_md6E9D = {0x6E9D, 1822, kanji_ms6E9D};
const kanji_md kanji_md8CA9 = {0x8CA9, 1823, kanji_ms8CA9};
const kanji_md kanji_md6D12 = {0x6D12, 1824, kanji_ms6D12};
const kanji_md kanji_md723A = {0x723A, 1825, kanji_ms723A};
const kanji_md kanji_md8FC2 = {0x8FC2, 1826, kanji_ms8FC2};
const kanji_md kanji_md7262 = {0x7262, 1827, kanji_ms7262};
const kanji_md kanji_md6F2C = {0x6F2C, 1828, kanji_ms6F2C};
const kanji_md kanji_md50B2 = {0x50B2, 1829, kanji_ms50B2};
const kanji_md kanji_md56DA = {0x56DA, 1830, kanji_ms56DA};
const kanji_md kanji_md96C0 = {0x96C0, 1831, kanji_ms96C0};
const kanji_md kanji_md5F66 = {0x5F66, 1832, kanji_ms5F66};
const kanji_md kanji_md7CE7 = {0x7CE7, 1833, kanji_ms7CE7};
const kanji_md kanji_md7ABA = {0x7ABA, 1834, kanji_ms7ABA};
const kanji_md kanji_md9A19 = {0x9A19, 1835, kanji_ms9A19};
const kanji_md kanji_md5091 = {0x5091, 1836, kanji_ms5091};
const kanji_md kanji_md6C96 = {0x6C96, 1837, kanji_ms6C96};
const kanji_md kanji_md6DF5 = {0x6DF5, 1838, kanji_ms6DF5};
const kanji_md kanji_md816B = {0x816B, 1839, kanji_ms816B};
const kanji_md kanji_md59A5 = {0x59A5, 1840, kanji_ms59A5};
const kanji_md kanji_md7C3F = {0x7C3F, 1841, kanji_ms7C3F};
const kanji_md kanji_md95A3 = {0x95A3, 1842, kanji_ms95A3};
const kanji_md kanji_md6817 = {0x6817, 1843, kanji_ms6817};
const kanji_md kanji_md8D74 = {0x8D74, 1844, kanji_ms8D74};
const kanji_md kanji_md9D8F = {0x9D8F, 1845, kanji_ms9D8F};
const kanji_md kanji_md5C1A = {0x5C1A, 1846, kanji_ms5C1A};
const kanji_md kanji_md62B9 = {0x62B9, 1847, kanji_ms62B9};
const kanji_md kanji_md548E = {0x548E, 1848, kanji_ms548E};
const kanji_md kanji_md8CFC = {0x8CFC, 1849, kanji_ms8CFC};
const kanji_md kanji_md9022 = {0x9022, 1850, kanji_ms9022};
const kanji_md kanji_md6F06 = {0x6F06, 1851, kanji_ms6F06};
const kanji_md kanji_md64B2 = {0x64B2, 1852, kanji_ms64B2};
const kanji_md kanji_md514B = {0x514B, 1853, kanji_ms514B};
const kanji_md kanji_md8E35 = {0x8E35, 1854, kanji_ms8E35};
const kanji_md kanji_md9905 = {0x9905, 1855, kanji_ms9905};
const kanji_md kanji_md64C1 = {0x64C1, 1856, kanji_ms64C1};
const kanji_md kanji_md77A5 = {0x77A5, 1857, kanji_ms77A5};
const kanji_md kanji_md5320 = {0x5320, 1858, kanji_ms5320};
const kanji_md kanji_md711A = {0x711A, 1859, kanji_ms711A};
const kanji_md kanji_md6442 = {0x6442, 1860, kanji_ms6442};
const kanji_md kanji_md83AB = {0x83AB, 1861, kanji_ms83AB};
const kanji_md kanji_md5238 = {0x5238, 1862, kanji_ms5238};
const kanji_md kanji_md8B19 = {0x8B19, 1863, kanji_ms8B19};
const kanji_md kanji_md6523 = {0x6523, 1864, kanji_ms6523};
const kanji_md kanji_md80DE = {0x80DE, 1865, kanji_ms80DE};
const kanji_md kanji_md6492 = {0x6492, 1866, kanji_ms6492};
const kanji_md kanji_md5E87 = {0x5E87, 1867, kanji_ms5E87};
const kanji_md kanji_md4E9B = {0x4E9B, 1868, kanji_ms4E9B};
const kanji_md kanji_md9808 = {0x9808, 1869, kanji_ms9808};
const kanji_md kanji_md790E = {0x790E, 1870, kanji_ms790E};
const kanji_md kanji_md8151 = {0x8151, 1871, kanji_ms8151};
const kanji_md kanji_md8EF8 = {0x8EF8, 1872, kanji_ms8EF8};
const kanji_md kanji_md4E59 = {0x4E59, 1873, kanji_ms4E59};
const kanji_md kanji_md79E9 = {0x79E9, 1874, kanji_ms79E9};
const kanji_md kanji_md96F6 = {0x96F6, 1875, kanji_ms96F6};
const kanji_md kanji_md82AF = {0x82AF, 1876, kanji_ms82AF};
const kanji_md kanji_md6CF0 = {0x6CF0, 1877, kanji_ms6CF0};
const kanji_md kanji_md62BD = {0x62BD, 1878, kanji_ms62BD};
const kanji_md kanji_md9913 = {0x9913, 1879, kanji_ms9913};
const kanji_md kanji_md9688 = {0x9688, 1880, kanji_ms9688};
const kanji_md kanji_md77BC = {0x77BC, 1881, kanji_ms77BC};
const kanji_md kanji_md8B39 = {0x8B39, 1882, kanji_ms8B39};
const kanji_md kanji_md8A02 = {0x8A02, 1883, kanji_ms8A02};
const kanji_md kanji_md6DCB = {0x6DCB, 1884, kanji_ms6DCB};
const kanji_md kanji_md673D = {0x673D, 1885, kanji_ms673D};
const kanji_md kanji_md4F8D = {0x4F8D, 1886, kanji_ms4F8D};
const kanji_md kanji_md6EF2 = {0x6EF2, 1887, kanji_ms6EF2};
const kanji_md kanji_md8702 = {0x8702, 1888, kanji_ms8702};
const kanji_md kanji_md9F20 = {0x9F20, 1889, kanji_ms9F20};
const kanji_md kanji_md6876 = {0x6876, 1890, kanji_ms6876};
const kanji_md kanji_md67D0 = {0x67D0, 1891, kanji_ms67D0};
const kanji_md kanji_md72D0 = {0x72D0, 1892, kanji_ms72D0};
const kanji_md kanji_md8FBB = {0x8FBB, 1893, kanji_ms8FBB};
const kanji_md kanji_md8C9D = {0x8C9D, 1894, kanji_ms8C9D};
const kanji_md kanji_md99D2 = {0x99D2, 1895, kanji_ms99D2};
const kanji_md kanji_md7C9B = {0x7C9B, 1896, kanji_ms7C9B};
const kanji_md kanji_md5243 = {0x5243, 1897, kanji_ms5243};
const kanji_md kanji_md971E = {0x971E, 1898, kanji_ms971E};
const kanji_md kanji_md91C7 = {0x91C7, 1899, kanji_ms91C7};
const kanji_md kanji_md938C = {0x938C, 1900, kanji_ms938C};
const kanji_md kanji_md5BB5 = {0x5BB5, 1901, kanji_ms5BB5};
const kanji_md kanji_md7A9F = {0x7A9F, 1902, kanji_ms7A9F};
const kanji_md kanji_md632B = {0x632B, 1903, kanji_ms632B};
const kanji_md kanji_md8C5A = {0x8C5A, 1904, kanji_ms8C5A};
const kanji_md kanji_md5C51 = {0x5C51, 1905, kanji_ms5C51};
const kanji_md kanji_md840E = {0x840E, 1906, kanji_ms840E};
const kanji_md kanji_md8B83 = {0x8B83, 1907, kanji_ms8B83};
const kanji_md kanji_md7DEF = {0x7DEF, 1908, kanji_ms7DEF};
const kanji_md kanji_md9306 = {0x9306, 1909, kanji_ms9306};
const kanji_md kanji_md4ED9 = {0x4ED9, 1910, kanji_ms4ED9};
const kanji_md kanji_md962A = {0x962A, 1911, kanji_ms962A};
const kanji_md kanji_md9065 = {0x9065, 1912, kanji_ms9065};
const kanji_md kanji_md525B = {0x525B, 1913, kanji_ms525B};
const kanji_md kanji_md7897 = {0x7897, 1914, kanji_ms7897};
const kanji_md kanji_md7A6B = {0x7A6B, 1915, kanji_ms7A6B};
const kanji_md kanji_md7F36 = {0x7F36, 1916, kanji_ms7F36};
const kanji_md kanji_md874B = {0x874B, 1917, kanji_ms874B};
const kanji_md kanji_md6881 = {0x6881, 1918, kanji_ms6881};
const kanji_md kanji_md75D9 = {0x75D9, 1919, kanji_ms75D9};
const kanji_md kanji_md5EF7 = {0x5EF7, 1920, kanji_ms5EF7};
const kanji_md kanji_md585A = {0x585A, 1921, kanji_ms585A};
const kanji_md kanji_md502B = {0x502B, 1922, kanji_ms502B};
const kanji_md kanji_md67F5 = {0x67F5, 1923, kanji_ms67F5};
const kanji_md kanji_md708A = {0x708A, 1924, kanji_ms708A};
const kanji_md kanji_md7A42 = {0x7A42, 1925, kanji_ms7A42};
const kanji_md kanji_md53AD = {0x53AD, 1926, kanji_ms53AD};
const kanji_md kanji_md5B5D = {0x5B5D, 1927, kanji_ms5B5D};
const kanji_md kanji_md86EE = {0x86EE, 1928, kanji_ms86EE};
const kanji_md kanji_md92FC = {0x92FC, 1929, kanji_ms92FC};
const kanji_md kanji_md81B3 = {0x81B3, 1930, kanji_ms81B3};
const kanji_md kanji_md6101 = {0x6101, 1931, kanji_ms6101};
const kanji_md kanji_md62D9 = {0x62D9, 1932, kanji_ms62D9};
const kanji_md kanji_md541F = {0x541F, 1933, kanji_ms541F};
const kanji_md kanji_md9010 = {0x9010, 1934, kanji_ms9010};
const kanji_md kanji_md914C = {0x914C, 1935, kanji_ms914C};
const kanji_md kanji_md9784 = {0x9784, 1936, kanji_ms9784};
const kanji_md kanji_md589C = {0x589C, 1937, kanji_ms589C};
const kanji_md kanji_md8178 = {0x8178, 1938, kanji_ms8178};
const kanji_md kanji_md904D = {0x904D, 1939, kanji_ms904D};
const kanji_md kanji_md871C = {0x871C, 1940, kanji_ms871C};
const kanji_md kanji_md64A4 = {0x64A4, 1941, kanji_ms64A4};
const kanji_md kanji_md9AC4 = {0x9AC4, 1942, kanji_ms9AC4};
const kanji_md kanji_md58FA = {0x58FA, 1943, kanji_ms58FA};
const kanji_md kanji_md4E91 = {0x4E91, 1944, kanji_ms4E91};
const kanji_md kanji_md751A = {0x751A, 1945, kanji_ms751A};
const kanji_md kanji_md4E9C = {0x4E9C, 1946, kanji_ms4E9C};
const kanji_md kanji_md5CF0 = {0x5CF0, 1947, kanji_ms5CF0};
const kanji_md kanji_md4F75 = {0x4F75, 1948, kanji_ms4F75};
const kanji_md kanji_md53F6 = {0x53F6, 1949, kanji_ms53F6};
const kanji_md kanji_md6D66 = {0x6D66, 1950, kanji_ms6D66};
const kanji_md kanji_md5B9C = {0x5B9C, 1951, kanji_ms5B9C};
const kanji_md kanji_md8210 = {0x8210, 1952, kanji_ms8210};
const kanji_md kanji_md5800 = {0x5800, 1953, kanji_ms5800};
const kanji_md kanji_md71ED = {0x71ED, 1954, kanji_ms71ED};
const kanji_md kanji_md9837 = {0x9837, 1955, kanji_ms9837};
const kanji_md kanji_md7B48 = {0x7B48, 1956, kanji_ms7B48};
const kanji_md kanji_md570F = {0x570F, 1957, kanji_ms570F};
const kanji_md kanji_md5F25 = {0x5F25, 1958, kanji_ms5F25};
const kanji_md kanji_md52FF = {0x52FF, 1959, kanji_ms52FF};
const kanji_md kanji_md5270 = {0x5270, 1960, kanji_ms5270};
const kanji_md kanji_md9CE9 = {0x9CE9, 1961, kanji_ms9CE9};
const kanji_md kanji_md5C90 = {0x5C90, 1962, kanji_ms5C90};
const kanji_md kanji_md564C = {0x564C, 1963, kanji_ms564C};
const kanji_md kanji_md83CA = {0x83CA, 1964, kanji_ms83CA};
const kanji_md kanji_md717D = {0x717D, 1965, kanji_ms717D};
const kanji_md kanji_md7A7F = {0x7A7F, 1966, kanji_ms7A7F};
const kanji_md kanji_md5553 = {0x5553, 1967, kanji_ms5553};
const kanji_md kanji_md5504 = {0x5504, 1968, kanji_ms5504};
const kanji_md kanji_md9DB4 = {0x9DB4, 1969, kanji_ms9DB4};
const kanji_md kanji_md7DB4 = {0x7DB4, 1970, kanji_ms7DB4};
const kanji_md kanji_md697C = {0x697C, 1971, kanji_ms697C};
const kanji_md kanji_md5598 = {0x5598, 1972, kanji_ms5598};
const kanji_md kanji_md73A9 = {0x73A9, 1973, kanji_ms73A9};
const kanji_md kanji_md8CAA = {0x8CAA, 1974, kanji_ms8CAA};
const kanji_md kanji_md6B27 = {0x6B27, 1975, kanji_ms6B27};
const kanji_md kanji_md52AB = {0x52AB, 1976, kanji_ms52AB};
const kanji_md kanji_md8CA2 = {0x8CA2, 1977, kanji_ms8CA2};
const kanji_md kanji_md6B96 = {0x6B96, 1978, kanji_ms6B96};
const kanji_md kanji_md4FF3 = {0x4FF3, 1979, kanji_ms4FF3};
const kanji_md kanji_md7968 = {0x7968, 1980, kanji_ms7968};
const kanji_md kanji_md514E = {0x514E, 1981, kanji_ms514E};
const kanji_md kanji_md7B20 = {0x7B20, 1982, kanji_ms7B20};
const kanji_md kanji_md598A = {0x598A, 1983, kanji_ms598A};
const kanji_md kanji_md76DF = {0x76DF, 1984, kanji_ms76DF};
const kanji_md kanji_md5FFD = {0x5FFD, 1985, kanji_ms5FFD};
const kanji_md kanji_md868A = {0x868A, 1986, kanji_ms868A};
const kanji_md kanji_md4FEF = {0x4FEF, 1987, kanji_ms4FEF};
const kanji_md kanji_md7D68 = {0x7D68, 1988, kanji_ms7D68};
const kanji_md kanji_md905C = {0x905C, 1989, kanji_ms905C};
const kanji_md kanji_md7E55 = {0x7E55, 1990, kanji_ms7E55};
const kanji_md kanji_md5B0C = {0x5B0C, 1991, kanji_ms5B0C};
const kanji_md kanji_md65EC = {0x65EC, 1992, kanji_ms65EC};
const kanji_md kanji_md84EE = {0x84EE, 1993, kanji_ms84EE};
const kanji_md kanji_md78C1 = {0x78C1, 1994, kanji_ms78C1};
const kanji_md kanji_md8910 = {0x8910, 1995, kanji_ms8910};
const kanji_md kanji_md88DF = {0x88DF, 1996, kanji_ms88DF};
const kanji_md kanji_md96B7 = {0x96B7, 1997, kanji_ms96B7};
const kanji_md kanji_md845B = {0x845B, 1998, kanji_ms845B};
const kanji_md kanji_md7984 = {0x7984, 1999, kanji_ms7984};
const kanji_md kanji_md7CDE = {0x7CDE, 2000, kanji_ms7CDE};
const kanji_md kanji_md5687 = {0x5687, 2001, kanji_ms5687};
const kanji_md kanji_md8888 = {0x8888, 2002, kanji_ms8888};
const kanji_md kanji_md7E1E = {0x7E1E, 2003, kanji_ms7E1E};
const kanji_md kanji_md5C4D = {0x5C4D, 2004, kanji_ms5C4D};
const kanji_md kanji_md88E1 = {0x88E1, 2005, kanji_ms88E1};
const kanji_md kanji_md95CA = {0x95CA, 2006, kanji_ms95CA};
const kanji_md kanji_md62EC = {0x62EC, 2007, kanji_ms62EC};
const kanji_md kanji_md85C1 = {0x85C1, 2008, kanji_ms85C1};
const kanji_md kanji_md865C = {0x865C, 2009, kanji_ms865C};
const kanji_md kanji_md6681 = {0x6681, 2010, kanji_ms6681};
const kanji_md kanji_md637B = {0x637B, 2011, kanji_ms637B};
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
