maccody/KanaChordPlus/software/nanori.h

/* nanori.h */
/**
This file is part of KanaChordPlus Keyboard.
 Copyright (C) 2024 Mac A. Cody

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
 You should have received a copy of the GNU General Public License
 along with this program.  If not, see <http://www.gnu.org/licenses/>.
**/

#ifndef AFFIX_ENUM
#define AFFIX_ENUM
enum affix_enum {
  none,   // No enhancments to reading (e.g., xyz).
  prefix, // Reading is a prefix (e.g., wxyz-).
  suffix, // Reading is a suffix (e.g., -wxyz).
  jword,  // Japanese word string with jukujikun or irregular reading.
  meaning // English meaning string for Japanese word enumerated above.
};
#endif

#ifndef OKURI_METADATA_TYPE
#define OKURI_METADATA_TYPE
typedef struct okuri_md {
  const uint8_t len;
  const affix_enum * const alist;
  const char **clist;
} okuri_md;
#endif

#ifndef READING_METADATA_TYPE
#define READING_METADATA_TYPE
typedef struct reading_md {
  const uint16_t len;
  const okuri_md * const * olist;
  const kanji_md * const * klist;
} reading_md;
#endif
const kanji_md * const na_kanji0xcca66a8a[] = {&kanji_md65E5, &kanji_md8DB3, &kanji_md76F8, &kanji_md5B89, &kanji_md6B69, &kanji_md56DB, &kanji_md6709, &kanji_md611B, &kanji_md8D64, &kanji_md671D, &kanji_md6211, &kanji_md6D77, &kanji_md539A, &kanji_md82F1, &kanji_md9EBB, &kanji_md7DB2, &kanji_md6676, &kanji_md6731, &kanji_md543E, &kanji_md5EB5, &kanji_md7C9F, &kanji_md82A6};
const reading_md nanori_md0xcca66a8a = {22, NULL, na_kanji0xcca66a8a};
const kanji_md * const na_kanji0x4b2bcdcd[] = {&kanji_md4F1A, &kanji_md548C, &kanji_md6771, &kanji_md82F1, &kanji_md79CB, &kanji_md9022, &kanji_md9957, &kanji_md9B8E, &kanji_md6703};
const reading_md nanori_md0x4b2bcdcd = {9, NULL, na_kanji0x4b2bcdcd};
const kanji_md * const na_kanji0x88e27330[] = {&kanji_md5408};
const reading_md nanori_md0x88e27330 = {1, NULL, na_kanji0x88e27330};
const kanji_md * const na_kanji0xba635922[] = {&kanji_md9957};
const reading_md nanori_md0xba635922 = {1, NULL, na_kanji0xba635922};
const kanji_md * const na_kanji0x6aa727bb[] = {&kanji_md78A7};
const reading_md nanori_md0x6aa727bb = {1, NULL, na_kanji0x6aa727bb};
const kanji_md * const na_kanji0xdd95f023[] = {&kanji_md4E0A};
const reading_md nanori_md0xdd95f023 = {1, NULL, na_kanji0xdd95f023};
const kanji_md * const na_kanji0xaddd2d58[] = {&kanji_md6731};
const reading_md nanori_md0xaddd2d58 = {1, NULL, na_kanji0xaddd2d58};
const kanji_md * const na_kanji0x5642932a[] = {&kanji_md8000};
const reading_md nanori_md0x5642932a = {1, NULL, na_kanji0x5642932a};
const kanji_md * const na_kanji0x4618aa73[] = {&kanji_md4F55, &kanji_md6211, &kanji_md543E};
const reading_md nanori_md0x4618aa73 = {3, NULL, na_kanji0x4618aa73};
const kanji_md * const na_kanji0x80fe9633[] = {&kanji_md770C, &kanji_md7E23};
const reading_md nanori_md0x80fe9633 = {2, NULL, na_kanji0x80fe9633};
const kanji_md * const na_kanji0x8d1f383a[] = {&kanji_md6771, &kanji_md63DA};
const reading_md nanori_md0x8d1f383a = {2, NULL, na_kanji0x8d1f383a};
const kanji_md * const na_kanji0xe6fd9c52[] = {&kanji_md65E5, &kanji_md767D, &kanji_md5149, &kanji_md5929, &kanji_md6210, &kanji_md53F3, &kanji_md7167, &kanji_md559C, &kanji_md967D, &kanji_md5546, &kanji_md93E1, &kanji_md8F1D, &kanji_md6E05, &kanji_md7AE0, &kanji_md5FB9, &kanji_md98FD, &kanji_md5BE7, &kanji_md9451, &kanji_md8A6E, &kanji_md662D, &kanji_md54F2, &kanji_md6602, &kanji_md6717, &kanji_md4E4B, &kanji_md9855, &kanji_md6676, &kanji_md6731, &kanji_md5553, &kanji_md6681, &kanji_md7965, &kanji_md8061, &kanji_md660C, &kanji_md5F70, &kanji_md7483, &kanji_md55E3, &kanji_md4E14, &kanji_md8AD2, &kanji_md65ED, &kanji_md4EAE, &kanji_md73B2, &kanji_md6643, &kanji_md7693, &kanji_md4EA8, &kanji_md5F6C, &kanji_md745B, &kanji_md5C2D, &kanji_md66C4, &kanji_md66C9};
const reading_md nanori_md0xe6fd9c52 = {48, NULL, na_kanji0xe6fd9c52};
const kanji_md * const na_kanji0x8df42165[] = {&kanji_md660E, &kanji_md73FE, &kanji_md5149, &kanji_md6210, &kanji_md516C, &kanji_md967D, &kanji_md6620, &kanji_md8F1D, &kanji_md7AE0, &kanji_md53F2, &kanji_md592E, &kanji_md5BE9, &kanji_md77B3, &kanji_md9451, &kanji_md662D, &kanji_md54F2, &kanji_md878D, &kanji_md6602, &kanji_md6717, &kanji_md667A, &kanji_md9855, &kanji_md6676, &kanji_md5553, &kanji_md6681, &kanji_md7965, &kanji_md8061, &kanji_md660C, &kanji_md6167, &kanji_md5F70, &kanji_md7FE0, &kanji_md65ED, &kanji_md536F, &kanji_md4EAE, &kanji_md73B2, &kanji_md6643, &kanji_md7693, &kanji_md4EA8, &kanji_md5F6C, &kanji_md745B, &kanji_md5F6A, &kanji_md8070, &kanji_md4F83, &kanji_md6636, &kanji_md71B9};
const reading_md nanori_md0x8df42165 = {44, NULL, na_kanji0x8df42165};
const kanji_md * const na_kanji0x88510512[] = {&kanji_md98FD};
const reading_md nanori_md0x88510512 = {1, NULL, na_kanji0x88510512};
const kanji_md * const na_kanji0x892d5c74[] = {&kanji_md660E, &kanji_md967D, &kanji_md6681};
const reading_md nanori_md0x892d5c74 = {3, NULL, na_kanji0x892d5c74};
const kanji_md * const na_kanji0xbb45b9d6[] = {&kanji_md4E0A};
const reading_md nanori_md0xbb45b9d6 = {1, NULL, na_kanji0xbb45b9d6};
const kanji_md * const na_kanji0xd6ba6ffb[] = {&kanji_md8D64};
const reading_md nanori_md0xd6ba6ffb = {1, NULL, na_kanji0xd6ba6ffb};
const kanji_md * const na_kanji0x1181cc17[] = {&kanji_md751F};
const reading_md nanori_md0x1181cc17 = {1, NULL, na_kanji0x1181cc17};
const kanji_md * const na_kanji0x5d6f80c0[] = {&kanji_md6D45, &kanji_md9EBB};
const reading_md nanori_md0x5d6f80c0 = {2, NULL, na_kanji0x5d6f80c0};
const kanji_md * const na_kanji0x8c36cc77[] = {&kanji_md611B, &kanji_md8328};
const reading_md nanori_md0x8c36cc77 = {2, NULL, na_kanji0x8c36cc77};
const kanji_md * const na_kanji0x6c8ad8ae[] = {&kanji_md60E3};
const reading_md nanori_md0x6c8ad8ae = {1, NULL, na_kanji0x6c8ad8ae};
const kanji_md * const na_kanji0x9fd87b04[] = {&kanji_md874B};
const reading_md nanori_md0x9fd87b04 = {1, NULL, na_kanji0x9fd87b04};
const kanji_md * const na_kanji0x33e6c24a[] = {&kanji_md660E, &kanji_md8DB3, &kanji_md5B89, &kanji_md98DB, &kanji_md904A};
const reading_md nanori_md0x33e6c24a = {5, NULL, na_kanji0x33e6c24a};
const kanji_md * const na_kanji0xda7c063b[] = {&kanji_md5B89, &kanji_md963F};
const reading_md nanori_md0xda7c063b = {2, NULL, na_kanji0xda7c063b};
const kanji_md * const na_kanji0xc77e3923[] = {&kanji_md6771, &kanji_md6625};
const reading_md nanori_md0xc77e3923 = {2, NULL, na_kanji0xc77e3923};
const kanji_md * const na_kanji0x4b4b307e[] = {&kanji_md65B0};
const reading_md nanori_md0x4b4b307e = {1, NULL, na_kanji0x4b4b307e};
const kanji_md * const na_kanji0x22a627a3[] = {&kanji_md671D};
const reading_md nanori_md0x22a627a3 = {1, NULL, na_kanji0x22a627a3};
const kanji_md * const na_kanji0x4a21c2d1[] = {&kanji_md71B1, &kanji_md9632};
const reading_md nanori_md0x4a21c2d1 = {2, NULL, na_kanji0x4a21c2d1};
const kanji_md * const na_kanji0x7fffaa43[] = {&kanji_md65B0};
const reading_md nanori_md0x7fffaa43 = {1, NULL, na_kanji0x7fffaa43};
const kanji_md * const na_kanji0xfb34384c[] = {&kanji_md4E2D};
const reading_md nanori_md0xfb34384c = {1, NULL, na_kanji0xfb34384c};
const kanji_md * const na_kanji0x17ad6115[] = {&kanji_md5B89, &kanji_md539A};
const reading_md nanori_md0x17ad6115 = {2, NULL, na_kanji0x17ad6115};
const kanji_md * const na_kanji0x4682bb88[] = {&kanji_md5F97, &kanji_md7D14, &kanji_md6E29, &kanji_md5145, &kanji_md5FB3, &kanji_md660C, &kanji_md7766, &kanji_md5B8F, &kanji_md6DF3, &kanji_md6566, &kanji_md60C7};
const reading_md nanori_md0x4682bb88 = {11, NULL, na_kanji0x4682bb88};
const kanji_md * const na_kanji0x6dc6b486[] = {&kanji_md6E29, &kanji_md6BC5, &kanji_md6DF3, &kanji_md6566, &kanji_md7AFA, &kanji_md6E25, &kanji_md60C7};
const reading_md nanori_md0x6dc6b486 = {7, NULL, na_kanji0x6dc6b486};
const kanji_md * const na_kanji0x4c44dc28[] = {&kanji_md96C6};
const reading_md nanori_md0x4c44dc28 = {1, NULL, na_kanji0x4c44dc28};
const kanji_md * const na_kanji0x957ae5ca[] = {&kanji_md4F0D, &kanji_md4F91};
const reading_md nanori_md0x957ae5ca = {2, NULL, na_kanji0x957ae5ca};
const kanji_md * const na_kanji0x38705359[] = {&kanji_md6771};
const reading_md nanori_md0x38705359 = {1, NULL, na_kanji0x38705359};
const kanji_md * const na_kanji0x6bbbee4a[] = {&kanji_md86C7};
const reading_md nanori_md0x6bbbee4a = {1, NULL, na_kanji0x6bbbee4a};
const kanji_md * const na_kanji0x4d8e96d4[] = {&kanji_md8D64, &kanji_md6D77, &kanji_md5944};
const reading_md nanori_md0x4d8e96d4 = {3, NULL, na_kanji0x4d8e96d4};
const kanji_md * const na_kanji0x486e9d34[] = {&kanji_md5468};
const reading_md nanori_md0x486e9d34 = {1, NULL, na_kanji0x486e9d34};
const kanji_md * const na_kanji0xe14088e8[] = {&kanji_md4F59};
const reading_md nanori_md0xe14088e8 = {1, NULL, na_kanji0xe14088e8};
const kanji_md * const na_kanji0x6e0e02f2[] = {&kanji_md5929};
const reading_md nanori_md0x6e0e02f2 = {1, NULL, na_kanji0x6e0e02f2};
const kanji_md * const na_kanji0x4f5dcb59[] = {&kanji_md7406, &kanji_md793C, &kanji_md9806, &kanji_md6075, &kanji_md7AE0, &kanji_md53F2, &kanji_md5F69, &kanji_md7D0B, &kanji_md6590, &kanji_md9326, &kanji_md82D1, &kanji_md7D62, &kanji_md90C1, &kanji_md7422};
const reading_md nanori_md0x4f5dcb59 = {14, NULL, na_kanji0x4f5dcb59};
const kanji_md * const na_kanji0x47176cd3[] = {&kanji_md6709};
const reading_md nanori_md0x47176cd3 = {1, NULL, na_kanji0x47176cd3};
const kanji_md * const na_kanji0xc4535f93[] = {&kanji_md6D17};
const reading_md nanori_md0xc4535f93 = {1, NULL, na_kanji0xc4535f93};
const kanji_md * const na_kanji0xff39439d[] = {&kanji_md862D};
const reading_md nanori_md0xff39439d = {1, NULL, na_kanji0xff39439d};
const kanji_md * const na_kanji0xa5413674[] = {&kanji_md5BB6, &kanji_md5728, &kanji_md6709, &kanji_md5B58, &kanji_md9806};
const reading_md nanori_md0xa5413674 = {5, NULL, na_kanji0xa5413674};
const kanji_md * const na_kanji0x21d26d31[] = {&kanji_md6709};
const reading_md nanori_md0x21d26d31 = {1, NULL, na_kanji0x21d26d31};
const kanji_md * const na_kanji0x62790ecb[] = {&kanji_md963F};
const reading_md nanori_md0x62790ecb = {1, NULL, na_kanji0x62790ecb};
const kanji_md * const na_kanji0x9b5d2df4[] = {&kanji_md5408};
const reading_md nanori_md0x9b5d2df4 = {1, NULL, na_kanji0x9b5d2df4};
const kanji_md * const na_kanji0x63c05906[] = {&kanji_md4E00, &kanji_md4E0A, &kanji_md5B50, &kanji_md5408, &kanji_md4F1A, &kanji_md98A8, &kanji_md76F8, &kanji_md6307, &kanji_md5341, &kanji_md53BB, &kanji_md544A, &kanji_md4E94, &kanji_md89D2, &kanji_md6BD4, &kanji_md5E02, &kanji_md98EF, &kanji_md9B5A, &kanji_md885B, &kanji_md5E7E, &kanji_md80C6, &kanji_md7956, &kanji_md5E9C, &kanji_md80A5, &kanji_md708A, &kanji_md6591, &kanji_md5EB5, &kanji_md674E, &kanji_md536F, &kanji_md90C1, &kanji_md58F1, &kanji_md63D6, &kanji_md58F9, &kanji_md5A03};
const reading_md nanori_md0x63c05906 = {33, NULL, na_kanji0x63c05906};
const kanji_md * const na_kanji0xddecac66[] = {&kanji_md98EF};
const reading_md nanori_md0xddecac66 = {1, NULL, na_kanji0xddecac66};
const kanji_md * const na_kanji0x3c6eb19d[] = {&kanji_md5B87};
const reading_md nanori_md0x3c6eb19d = {1, NULL, na_kanji0x3c6eb19d};
const kanji_md * const na_kanji0x30487f81[] = {&kanji_md751F, &kanji_md4F2F};
const reading_md nanori_md0x30487f81 = {2, NULL, na_kanji0x30487f81};
const kanji_md * const na_kanji0xae2e9957[] = {&kanji_md884C, &kanji_md751F, &kanji_md57CE, &kanji_md5F81};
const reading_md nanori_md0xae2e9957 = {4, NULL, na_kanji0xae2e9957};
const kanji_md * const na_kanji0x6b5c695e[] = {&kanji_md7684};
const reading_md nanori_md0x6b5c695e = {1, NULL, na_kanji0x6b5c695e};
const kanji_md * const na_kanji0x94c537b0[] = {&kanji_md751F};
const reading_md nanori_md0x94c537b0 = {1, NULL, na_kanji0x94c537b0};
const kanji_md * const na_kanji0x92524ac2[] = {&kanji_md77F3, &kanji_md5A01, &kanji_md529F, &kanji_md7802, &kanji_md9A4D, &kanji_md52F3};
const reading_md nanori_md0x92524ac2 = {6, NULL, na_kanji0x92524ac2};
const kanji_md * const na_kanji0x26963cc7[] = {&kanji_md60B3};
const reading_md nanori_md0x26963cc7 = {1, NULL, na_kanji0x26963cc7};
const kanji_md * const na_kanji0x9af803af[] = {&kanji_md52F2, &kanji_md9A4D};
const reading_md nanori_md0x9af803af = {2, NULL, na_kanji0x9af803af};
const kanji_md * const na_kanji0xb734287e[] = {&kanji_md5C0F};
const reading_md nanori_md0xb734287e = {1, NULL, na_kanji0xb734287e};
const kanji_md * const na_kanji0x67ecbf83[] = {&kanji_md78B5};
const reading_md nanori_md0x67ecbf83 = {1, NULL, na_kanji0x67ecbf83};
const kanji_md * const na_kanji0x5796e1c9[] = {&kanji_md77F3};
const reading_md nanori_md0x5796e1c9 = {1, NULL, na_kanji0x5796e1c9};
const kanji_md * const na_kanji0xd7e9392c[] = {&kanji_md51FA, &kanji_md548C, &kanji_md6CC9};
const reading_md nanori_md0xd7e9392c = {3, NULL, na_kanji0xd7e9392c};
const kanji_md * const na_kanji0x78bafa03[] = {&kanji_md6C50};
const reading_md nanori_md0x78bafa03 = {1, NULL, na_kanji0x78bafa03};
const kanji_md * const na_kanji0x7068d2ef[] = {&kanji_md5206, &kanji_md6F6E};
const reading_md nanori_md0x7068d2ef = {2, NULL, na_kanji0x7068d2ef};
const kanji_md * const na_kanji0x61508bc5[] = {&kanji_md683C, &kanji_md4E4B, &kanji_md66A2, &kanji_md8FEA};
const reading_md nanori_md0x61508bc5 = {4, NULL, na_kanji0x61508bc5};
const kanji_md * const na_kanji0xfcf33057[] = {&kanji_md6ADF, &kanji_md6AAA};
const reading_md nanori_md0xfcf33057 = {2, NULL, na_kanji0xfcf33057};
const kanji_md * const na_kanji0x314981f[] = {&kanji_md4E5D};
const reading_md nanori_md0x314981f = {1, NULL, na_kanji0x314981f};
const kanji_md * const na_kanji0x4390f4b1[] = {&kanji_md4E5D};
const reading_md nanori_md0x4390f4b1 = {1, NULL, na_kanji0x4390f4b1};
const kanji_md * const na_kanji0x1e871ec6[] = {&kanji_md4E00, &kanji_md9038};
const reading_md nanori_md0x1e871ec6 = {2, NULL, na_kanji0x1e871ec6};
const kanji_md * const na_kanji0xcf8f3a3b[] = {&kanji_md53B3, &kanji_md658E};
const reading_md nanori_md0xcf8f3a3b = {2, NULL, na_kanji0xcf8f3a3b};
const kanji_md * const na_kanji0xf4ba4b5a[] = {&kanji_md6A39, &kanji_md658E};
const reading_md nanori_md0xf4ba4b5a = {2, NULL, na_kanji0xf4ba4b5a};
const kanji_md * const na_kanji0x9a9eb486[] = {&kanji_md51FA, &kanji_md53B3};
const reading_md nanori_md0x9a9eb486 = {2, NULL, na_kanji0x9a9eb486};
const kanji_md * const na_kanji0xfdaa1b28[] = {&kanji_md51FA};
const reading_md nanori_md0xfdaa1b28 = {1, NULL, na_kanji0xfdaa1b28};
const kanji_md * const na_kanji0xa3588418[] = {&kanji_md5185, &kanji_md4F0A};
const reading_md nanori_md0xa3588418 = {2, NULL, na_kanji0xa3588418};
const kanji_md * const na_kanji0xb9779328[] = {&kanji_md5F15, &kanji_md54E1};
const reading_md nanori_md0xb9779328 = {2, NULL, na_kanji0xb9779328};
const kanji_md * const na_kanji0xeec50b0a[] = {&kanji_md7530};
const reading_md nanori_md0xeec50b0a = {1, NULL, na_kanji0xeec50b0a};
const kanji_md * const na_kanji0xbf3e2e67[] = {&kanji_md4E95, &kanji_md7A32, &kanji_md732A};
const reading_md nanori_md0xbf3e2e67 = {3, NULL, na_kanji0xbf3e2e67};
const kanji_md * const na_kanji0x2ea2fb5f[] = {&kanji_md6307};
const reading_md nanori_md0x2ea2fb5f = {1, NULL, na_kanji0x2ea2fb5f};
const kanji_md * const na_kanji0xe31ced7b[] = {&kanji_md5EB5};
const reading_md nanori_md0xe31ced7b = {1, NULL, na_kanji0xe31ced7b};
const kanji_md * const na_kanji0x22aae339[] = {&kanji_md5FCC};
const reading_md nanori_md0x22aae339 = {1, NULL, na_kanji0x22aae339};
const kanji_md * const na_kanji0xb3b7bdea[] = {&kanji_md90CE};
const reading_md nanori_md0xb3b7bdea = {1, NULL, na_kanji0xb3b7bdea};
const kanji_md * const na_kanji0x1c9dd9c6[] = {&kanji_md5165, &kanji_md897F, &kanji_md98EF, &kanji_md714E};
const reading_md nanori_md0x1c9dd9c6 = {4, NULL, na_kanji0x1c9dd9c6};
const kanji_md * const na_kanji0xb75ca3be[] = {&kanji_md4E00, &kanji_md65E5, &kanji_md5165};
const reading_md nanori_md0xb75ca3be = {3, NULL, na_kanji0xb75ca3be};
const kanji_md * const na_kanji0x22c25060[] = {&kanji_md77F3};
const reading_md nanori_md0x22c25060 = {1, NULL, na_kanji0x22c25060};
const kanji_md * const na_kanji0x631af3f3[] = {&kanji_md78D0};
const reading_md nanori_md0x631af3f3 = {1, NULL, na_kanji0x631af3f3};
const kanji_md * const na_kanji0x6b998f5[] = {&kanji_md702C};
const reading_md nanori_md0x6b998f5 = {1, NULL, na_kanji0x6b998f5};
const kanji_md * const na_kanji0x982b1106[] = {&kanji_md5B88, &kanji_md53CB, &kanji_md4FDD, &kanji_md904A, &kanji_md5E03, &kanji_md5FA1, &kanji_md9632, &kanji_md6B66, &kanji_md7DBF, &kanji_md5E9C, &kanji_md7B1B, &kanji_md96C5, &kanji_md74DC, &kanji_md7893, &kanji_md83DF};
const reading_md nanori_md0x982b1106 = {15, NULL, na_kanji0x982b1106};
const kanji_md * const na_kanji0xc7da44c6[] = {&kanji_md5916, &kanji_md9EC4};
const reading_md nanori_md0xc7da44c6 = {2, NULL, na_kanji0xc7da44c6};
const kanji_md * const na_kanji0x6942961b[] = {&kanji_md690D, &kanji_md6A39, &kanji_md6B96};
const reading_md nanori_md0x6942961b = {3, NULL, na_kanji0x6942961b};
const kanji_md * const na_kanji0x31313496[] = {&kanji_md6D6E};
const reading_md nanori_md0x31313496 = {1, NULL, na_kanji0x31313496};
const kanji_md * const na_kanji0xf939390e[] = {&kanji_md627F, &kanji_md8ACB};
const reading_md nanori_md0xf939390e = {2, NULL, na_kanji0xf939390e};
const kanji_md * const na_kanji0xf69b9d1[] = {&kanji_md7DCF};
const reading_md nanori_md0xf69b9d1 = {1, NULL, na_kanji0xf69b9d1};
const kanji_md * const na_kanji0x8e718bf2[] = {&kanji_md725B};
const reading_md nanori_md0x8e718bf2 = {1, NULL, na_kanji0x8e718bf2};
const kanji_md * const na_kanji0x8d120c2c[] = {&kanji_md7893};
const reading_md nanori_md0x8d120c2c = {1, NULL, na_kanji0x8d120c2c};
const kanji_md * const na_kanji0x5353e34e[] = {&kanji_md8170};
const reading_md nanori_md0x5353e34e = {1, NULL, na_kanji0x5353e34e};
const kanji_md * const na_kanji0xb7993085[] = {&kanji_md6C34};
const reading_md nanori_md0xb7993085 = {1, NULL, na_kanji0xb7993085};
const kanji_md * const na_kanji0xa161ed32[] = {&kanji_md5BB4, &kanji_md8A60, &kanji_md8CE6};
const reading_md nanori_md0xa161ed32 = {3, NULL, na_kanji0xa161ed32};
const kanji_md * const na_kanji0x10770c83[] = {&kanji_md6253};
const reading_md nanori_md0x10770c83 = {1, NULL, na_kanji0x10770c83};
const kanji_md * const na_kanji0xa3fa030f[] = {&kanji_md7A7A, &kanji_md69CD};
const reading_md nanori_md0xa3fa030f = {2, NULL, na_kanji0xa3fa030f};
const kanji_md * const na_kanji0x8e93fcc6[] = {&kanji_md6D77};
const reading_md nanori_md0x8e93fcc6 = {1, NULL, na_kanji0x8e93fcc6};
const kanji_md * const na_kanji0x7d09c257[] = {&kanji_md91C6};
const reading_md nanori_md0x7d09c257 = {1, NULL, na_kanji0x7d09c257};
const kanji_md * const na_kanji0x6a939d[] = {&kanji_md5927};
const reading_md nanori_md0x6a939d = {1, NULL, na_kanji0x6a939d};
const kanji_md * const na_kanji0x6c53e80[] = {&kanji_md751F, &kanji_md5E7C};
const reading_md nanori_md0x6c53e80 = {2, NULL, na_kanji0x6c53e80};
const kanji_md * const na_kanji0xc98dca74[] = {&kanji_md751F};
const reading_md nanori_md0xc98dca74 = {1, NULL, na_kanji0xc98dca74};
const kanji_md * const na_kanji0xc1aac3d3[] = {&kanji_md6E56};
const reading_md nanori_md0xc1aac3d3 = {1, NULL, na_kanji0xc1aac3d3};
const kanji_md * const na_kanji0xa2b5a14c[] = {&kanji_md8302};
const reading_md nanori_md0xa2b5a14c = {1, NULL, na_kanji0xa2b5a14c};
const kanji_md * const na_kanji0x702e3d46[] = {&kanji_md5360, &kanji_md535C};
const reading_md nanori_md0x702e3d46 = {2, NULL, na_kanji0x702e3d46};
const kanji_md * const na_kanji0xc0737940[] = {&kanji_md5B09};
const reading_md nanori_md0xc0737940 = {1, NULL, na_kanji0xc0737940};
const kanji_md * const na_kanji0xdaae213e[] = {&kanji_md58F2};
const reading_md nanori_md0xdaae213e = {1, NULL, na_kanji0xdaae213e};
const kanji_md * const na_kanji0x12bcc63d[] = {&kanji_md58F2, &kanji_md6F06};
const reading_md nanori_md0x12bcc63d = {2, NULL, na_kanji0x12bcc63d};
const kanji_md * const na_kanji0x40fa2dea[] = {&kanji_md5B09};
const reading_md nanori_md0x40fa2dea = {1, NULL, na_kanji0x40fa2dea};
const kanji_md * const na_kanji0x1edf41c8[] = {&kanji_md6D77, &kanji_md9280};
const reading_md nanori_md0x1edf41c8 = {2, NULL, na_kanji0x1edf41c8};
const kanji_md * const na_kanji0x407f6809[] = {&kanji_md751F, &kanji_md5BB6, &kanji_md98A8, &kanji_md611B, &kanji_md8A08, &kanji_md6238, &kanji_md6D77, &kanji_md6620, &kanji_md5144, &kanji_md6C38, &kanji_md6751, &kanji_md690D, &kanji_md82F1, &kanji_md98EF, &kanji_md592E, &kanji_md5409, &kanji_md679D, &kanji_md8A89, &kanji_md6B96, &kanji_md8A60, &kanji_md698E, &kanji_md834F, &kanji_md745B, &kanji_md9834};
const reading_md nanori_md0x407f6809 = {24, NULL, na_kanji0x407f6809};
const kanji_md * const na_kanji0x54669c8d[] = {&kanji_md8A60};
const reading_md nanori_md0x54669c8d = {1, NULL, na_kanji0x54669c8d};
const kanji_md * const na_kanji0x7fe56fe2[] = {&kanji_md6D74, &kanji_md4F2F};
const reading_md nanori_md0x7fe56fe2 = {2, NULL, na_kanji0x7fe56fe2};
const kanji_md * const na_kanji0x3ee9f506[] = {&kanji_md5E79};
const reading_md nanori_md0x3ee9f506 = {1, NULL, na_kanji0x3ee9f506};
const kanji_md * const na_kanji0xc070a178[] = {&kanji_md8D8A};
const reading_md nanori_md0xc070a178 = {1, NULL, na_kanji0xc070a178};
const kanji_md * const na_kanji0x8b014f8a[] = {&kanji_md8D8A};
const reading_md nanori_md0x8b014f8a = {1, NULL, na_kanji0x8b014f8a};
const kanji_md * const na_kanji0x444dec72[] = {&kanji_md698E};
const reading_md nanori_md0x444dec72 = {1, NULL, na_kanji0x444dec72};
const kanji_md * const na_kanji0xdd50849d[] = {&kanji_md8328};
const reading_md nanori_md0xdd50849d = {1, NULL, na_kanji0xdd50849d};
const kanji_md * const na_kanji0xcd31b114[] = {&kanji_md8001, &kanji_md86ED, &kanji_md620E};
const reading_md nanori_md0xcd31b114 = {3, NULL, na_kanji0xcd31b114};
const kanji_md * const na_kanji0xccdf420c[] = {&kanji_md80E1};
const reading_md nanori_md0xccdf420c = {1, NULL, na_kanji0xccdf420c};
const kanji_md * const na_kanji0x3393e712[] = {&kanji_md7B11, &kanji_md8766};
const reading_md nanori_md0x3393e712 = {2, NULL, na_kanji0x3393e712};
const kanji_md * const na_kanji0x4aef4cfe[] = {&kanji_md6E09};
const reading_md nanori_md0x4aef4cfe = {1, NULL, na_kanji0x4aef4cfe};
const kanji_md * const na_kanji0xe480c8b4[] = {&kanji_md69D0};
const reading_md nanori_md0xe480c8b4 = {1, NULL, na_kanji0xe480c8b4};
const kanji_md * const na_kanji0x61a789d7[] = {&kanji_md5927, &kanji_md9577, &kanji_md9762, &kanji_md97F3, &kanji_md9060, &kanji_md5FDC, &kanji_md9752, &kanji_md592B, &kanji_md5965, &kanji_md6E21, &kanji_md58EB, &kanji_md8D8A, &kanji_md767E, &kanji_md4FDD, &kanji_md96A0, &kanji_md5305, &kanji_md6B66, &kanji_md52C7, &kanji_md623F, &kanji_md90CE, &kanji_md53F2, &kanji_md592E, &kanji_md9EBB, &kanji_md5E9C, &kanji_md96C5, &kanji_md5104, &kanji_md6717, &kanji_md9686, &kanji_md82B3, &kanji_md7A42, &kanji_md5F18, &kanji_md4E43, &kanji_md7FC1, &kanji_md9091, &kanji_md7A57};
const reading_md nanori_md0x61a789d7 = {35, NULL, na_kanji0x61a789d7};
const kanji_md * const na_kanji0x5a306100[] = {&kanji_md751F, &kanji_md8FFD, &kanji_md7A2E, &kanji_md8001, &kanji_md53CA, &kanji_md7B08};
const reading_md nanori_md0x5a306100 = {6, NULL, na_kanji0x5a306100};
const kanji_md * const na_kanji0xe6bd8091[] = {&kanji_md5927, &kanji_md8FD1, &kanji_md76F8, &kanji_md7389, &kanji_md6247, &kanji_md9022, &kanji_md9091};
const reading_md nanori_md0xe6bd8091 = {7, NULL, na_kanji0xe6bd8091};
const kanji_md * const na_kanji0x9f086b47[] = {&kanji_md7687};
const reading_md nanori_md0x9f086b47 = {1, NULL, na_kanji0x9f086b47};
const kanji_md * const na_kanji0x6ecf31fb[] = {&kanji_md8FD1, &kanji_md6B63, &kanji_md592A, &kanji_md5965, &kanji_md738B, &kanji_md5DE8, &kanji_md677E, &kanji_md7687, &kanji_md6B27, &kanji_md9091};
const reading_md nanori_md0x6ecf31fb = {10, NULL, na_kanji0x6ecf31fb};
const kanji_md * const na_kanji0xf8aafc69[] = {&kanji_md738B};
const reading_md nanori_md0xf8aafc69 = {1, NULL, na_kanji0xf8aafc69};
const kanji_md * const na_kanji0x1227e66d[] = {&kanji_md6247};
const reading_md nanori_md0x1227e66d = {1, NULL, na_kanji0x1227e66d};
const kanji_md * const na_kanji0xb8fc3b7d[] = {&kanji_md9CF3};
const reading_md nanori_md0xb8fc3b7d = {1, NULL, na_kanji0xb8fc3b7d};
const kanji_md * const na_kanji0x68d7d4f1[] = {&kanji_md7530, &kanji_md963F, &kanji_md5CB3, &kanji_md5CFB, &kanji_md961C};
const reading_md nanori_md0x68d7d4f1 = {5, NULL, na_kanji0x68d7d4f1};
const kanji_md * const na_kanji0x2bb58c99[] = {&kanji_md7F6E, &kanji_md5C45, &kanji_md8208, &kanji_md9806, &kanji_md4FEE, &kanji_md7155};
const reading_md nanori_md0x2bb58c99 = {6, NULL, na_kanji0x2bb58c99};
const kanji_md * const na_kanji0x4f3d2ee1[] = {&kanji_md7F6E};
const reading_md nanori_md0x4f3d2ee1 = {1, NULL, na_kanji0x4f3d2ee1};
const kanji_md * const na_kanji0x58045dbf[] = {&kanji_md8208};
const reading_md nanori_md0x58045dbf = {1, NULL, na_kanji0x58045dbf};
const kanji_md * const na_kanji0x3c58dae0[] = {&kanji_md5B5F, &kanji_md8129};
const reading_md nanori_md0x3c58dae0 = {2, NULL, na_kanji0x3c58dae0};
const kanji_md * const na_kanji0xf643a648[] = {&kanji_md5211};
const reading_md nanori_md0xf643a648 = {1, NULL, na_kanji0xf643a648};
const kanji_md * const na_kanji0x454fba83[] = {&kanji_md7406, &kanji_md9053, &kanji_md9806, &kanji_md4FEE, &kanji_md653B, &kanji_md7D00, &kanji_md78E8, &kanji_md4E43, &kanji_md60E3, &kanji_md9756, &kanji_md8129};
const reading_md nanori_md0x454fba83 = {11, NULL, na_kanji0x454fba83};
const kanji_md * const na_kanji0x8814378c[] = {&kanji_md62BC, &kanji_md5FCD, &kanji_md6392};
const reading_md nanori_md0x8814378c = {3, NULL, na_kanji0x8814378c};
const kanji_md * const na_kanji0xad30fe63[] = {&kanji_md9577};
const reading_md nanori_md0xad30fe63 = {1, NULL, na_kanji0xad30fe63};
const kanji_md * const na_kanji0x6b17aba1[] = {&kanji_md8DB3, &kanji_md62BC};
const reading_md nanori_md0x6b17aba1 = {2, NULL, na_kanji0x6b17aba1};
const kanji_md * const na_kanji0x722c629f[] = {&kanji_md843D};
const reading_md nanori_md0x722c629f = {1, NULL, na_kanji0x722c629f};
const kanji_md * const na_kanji0x7c82c5e4[] = {&kanji_md4E8C, &kanji_md6708};
const reading_md nanori_md0x7c82c5e4 = {2, NULL, na_kanji0x7c82c5e4};
const kanji_md * const na_kanji0x401a452[] = {&kanji_md8E8D};
const reading_md nanori_md0x401a452 = {1, NULL, na_kanji0x401a452};
const kanji_md * const na_kanji0xc5f3f783[] = {&kanji_md5973, &kanji_md7FC1};
const reading_md nanori_md0xc5f3f783 = {2, NULL, na_kanji0xc5f3f783};
const kanji_md * const na_kanji0x9442a15e[] = {&kanji_md9060};
const reading_md nanori_md0x9442a15e = {1, NULL, na_kanji0x9442a15e};
const kanji_md * const na_kanji0xfcb98023[] = {&kanji_md9996};
const reading_md nanori_md0xfcb98023 = {1, NULL, na_kanji0xfcb98023};
const kanji_md * const na_kanji0xe9c3cf5a[] = {&kanji_md81E3};
const reading_md nanori_md0xe9c3cf5a = {1, NULL, na_kanji0xe9c3cf5a};
const kanji_md * const na_kanji0x98f6ac27[] = {&kanji_md6CA2};
const reading_md nanori_md0x98f6ac27 = {1, NULL, na_kanji0x98f6ac27};
const kanji_md * const na_kanji0xe768ed6a[] = {&kanji_md62BC};
const reading_md nanori_md0xe768ed6a = {1, NULL, na_kanji0xe768ed6a};
const kanji_md * const na_kanji0x13123747[] = {&kanji_md5302};
const reading_md nanori_md0x13123747 = {1, NULL, na_kanji0x13123747};
const kanji_md * const na_kanji0xe3e66e15[] = {&kanji_md5965, &kanji_md5712};
const reading_md nanori_md0xe3e66e15 = {2, NULL, na_kanji0xe3e66e15};
const kanji_md * const na_kanji0xefcf429a[] = {&kanji_md4E0A, &kanji_md5408, &kanji_md9AD8, &kanji_md767D, &kanji_md958B, &kanji_md4E09, &kanji_md5341, &kanji_md795E, &kanji_md6211, &kanji_md6D77, &kanji_md7A4D, &kanji_md5DDD, &kanji_md9CE5, &kanji_md52D8, &kanji_md5DE8, &kanji_md6383, &kanji_md5742, &kanji_md96C5, &kanji_md935B, &kanji_md51A0, &kanji_md4F2F, &kanji_md8CC0, &kanji_md9DB4, &kanji_md845B, &kanji_md7FD4, &kanji_md68A8, &kanji_md862D, &kanji_md6842, &kanji_md54C9, &kanji_md572D, &kanji_md8304, &kanji_md90C1, &kanji_md8431, &kanji_md99A8};
const reading_md nanori_md0xefcf429a = {34, NULL, na_kanji0xefcf429a};
const kanji_md * const na_kanji0xafb2bb34[] = {&kanji_md7AF6, &kanji_md98FC, &kanji_md67CF, &kanji_md9834, &kanji_md5CFD};
const reading_md nanori_md0xafb2bb34 = {5, NULL, na_kanji0xafb2bb34};
const kanji_md * const na_kanji0x68d9a3fd[] = {&kanji_md66FF};
const reading_md nanori_md0x68d9a3fd = {1, NULL, na_kanji0x68d9a3fd};
const kanji_md * const na_kanji0x113c1954[] = {&kanji_md85AB};
const reading_md nanori_md0x113c1954 = {1, NULL, na_kanji0x113c1954};
const kanji_md * const na_kanji0x1b1f214c[] = {&kanji_md82B3, &kanji_md85AB, &kanji_md90C1, &kanji_md99A8, &kanji_md5F6A};
const reading_md nanori_md0x1b1f214c = {5, NULL, na_kanji0x1b1f214c};
const kanji_md * const na_kanji0xfd1b6414[] = {&kanji_md5404};
const reading_md nanori_md0xfd1b6414 = {1, NULL, na_kanji0xfd1b6414};
const kanji_md * const na_kanji0x50927814[] = {&kanji_md5229, &kanji_md93E1, &kanji_md5404};
const reading_md nanori_md0x50927814 = {3, NULL, na_kanji0x50927814};
const kanji_md * const na_kanji0x70badad3[] = {&kanji_md93E1};
const reading_md nanori_md0x70badad3 = {1, NULL, na_kanji0x70badad3};
const kanji_md * const na_kanji0x2ef382d[] = {&kanji_md4E0A, &kanji_md66F8};
const reading_md nanori_md0x2ef382d = {2, NULL, na_kanji0x2ef382d};
const kanji_md * const na_kanji0x77d7c7ca[] = {&kanji_md795E};
const reading_md nanori_md0x77d7c7ca = {1, NULL, na_kanji0x77d7c7ca};
const kanji_md * const na_kanji0x2d5d1d81[] = {&kanji_md639B};
const reading_md nanori_md0x2d5d1d81 = {1, NULL, na_kanji0x2d5d1d81};
const kanji_md * const na_kanji0xb5999cc9[] = {&kanji_md7B67};
const reading_md nanori_md0xb5999cc9 = {1, NULL, na_kanji0xb5999cc9};
const kanji_md * const na_kanji0xacf58a82[] = {&kanji_md666F};
const reading_md nanori_md0xacf58a82 = {1, NULL, na_kanji0xacf58a82};
const kanji_md * const na_kanji0xe0401019[] = {&kanji_md6587};
const reading_md nanori_md0xe0401019 = {1, NULL, na_kanji0xe0401019};
const kanji_md * const na_kanji0xc4b9f88a[] = {&kanji_md67CF};
const reading_md nanori_md0xc4b9f88a = {1, NULL, na_kanji0xc4b9f88a};
const kanji_md * const na_kanji0x47f9c7ed[] = {&kanji_md6625, &kanji_md7CDF};
const reading_md nanori_md0x47f9c7ed = {2, NULL, na_kanji0x47f9c7ed};
const kanji_md * const na_kanji0x735d568c[] = {&kanji_md4E00, &kanji_md4E0A, &kanji_md4E3B, &kanji_md8A08, &kanji_md548C, &kanji_md4E07, &kanji_md54E1, &kanji_md5343, &kanji_md5E2B, &kanji_md91CF, &kanji_md5B97, &kanji_md5BFF, &kanji_md662D, &kanji_md845B, &kanji_md61B2, &kanji_md5609, &kanji_md80E4, &kanji_md58F1, &kanji_md842C, &kanji_md58FD};
const reading_md nanori_md0x735d568c = {20, NULL, na_kanji0x735d568c};
const kanji_md * const na_kanji0x564a55f8[] = {&kanji_md662D};
const reading_md nanori_md0x564a55f8 = {1, NULL, na_kanji0x564a55f8};
const kanji_md * const na_kanji0xf888c3cb[] = {&kanji_md845B, &kanji_md9B18};
const reading_md nanori_md0xf888c3cb = {2, NULL, na_kanji0xf888c3cb};
const kanji_md * const na_kanji0xafb6498a[] = {&kanji_md8B70, &kanji_md4EA4, &kanji_md5BB9, &kanji_md50CF, &kanji_md8CE2, &kanji_md938C, &kanji_md525B};
const reading_md nanori_md0xafb6498a = {7, NULL, na_kanji0xafb6498a};
const kanji_md * const na_kanji0xbaabf6bf[] = {&kanji_md52DD, &kanji_md5F92};
const reading_md nanori_md0xbaabf6bf = {2, NULL, na_kanji0xbaabf6bf};
const kanji_md * const na_kanji0xb54b31eb[] = {&kanji_md6CB3, &kanji_md5208, &kanji_md845B};
const reading_md nanori_md0xb54b31eb = {3, NULL, na_kanji0xb54b31eb};
const kanji_md * const na_kanji0xafd7b290[] = {&kanji_md51A0};
const reading_md nanori_md0xafd7b290 = {1, NULL, na_kanji0xafd7b290};
const kanji_md * const na_kanji0x40ae3c7f[] = {&kanji_md4E00, &kanji_md9054, &kanji_md548C, &kanji_md5065, &kanji_md529F, &kanji_md5C06, &kanji_md96C4, &kanji_md5DE7, &kanji_md514B, &kanji_md6377, &kanji_md6842, &kanji_md4E14};
const reading_md nanori_md0x40ae3c7f = {12, NULL, na_kanji0x40ae3c7f};
const kanji_md * const na_kanji0xe105653[] = {&kanji_md845B};
const reading_md nanori_md0xe105653 = {1, NULL, na_kanji0xe105653};
const kanji_md * const na_kanji0x1d3ad4a9[] = {&kanji_md548C, &kanji_md5C06};
const reading_md nanori_md0x1d3ad4a9 = {2, NULL, na_kanji0x1d3ad4a9};
const kanji_md * const na_kanji0xf46231a3[] = {&kanji_md4E00, &kanji_md548C};
const reading_md nanori_md0xf46231a3 = {2, NULL, na_kanji0xf46231a3};
const kanji_md * const na_kanji0x7d040957[] = {&kanji_md572D};
const reading_md nanori_md0x7d040957 = {1, NULL, na_kanji0x7d040957};
const kanji_md * const na_kanji0x81a74fae[] = {&kanji_md795E, &kanji_md611B, &kanji_md9280};
const reading_md nanori_md0x81a74fae = {3, NULL, na_kanji0x81a74fae};
const kanji_md * const na_kanji0xf6d8c245[] = {&kanji_md4E2D};
const reading_md nanori_md0xf6d8c245 = {1, NULL, na_kanji0xf6d8c245};
const kanji_md * const na_kanji0xaf3d2359[] = {&kanji_md5305, &kanji_md9280, &kanji_md61D0, &kanji_md517C, &kanji_md8B19, &kanji_md938C, &kanji_md9326};
const reading_md nanori_md0xaf3d2359 = {7, NULL, na_kanji0xaf3d2359};
const kanji_md * const na_kanji0x23559aa7[] = {&kanji_md53F6};
const reading_md nanori_md0x23559aa7 = {1, NULL, na_kanji0x23559aa7};
const kanji_md * const na_kanji0x4674e97f[] = {&kanji_md53F6};
const reading_md nanori_md0x4674e97f = {1, NULL, na_kanji0x4674e97f};
const kanji_md * const na_kanji0x669a956e[] = {&kanji_md7532};
const reading_md nanori_md0x669a956e = {1, NULL, na_kanji0x669a956e};
const kanji_md * const na_kanji0xda998fb[] = {&kanji_md85AB};
const reading_md nanori_md0xda998fb = {1, NULL, na_kanji0xda998fb};
const kanji_md * const na_kanji0xe010be79[] = {&kanji_md85AB, &kanji_md99A8};
const reading_md nanori_md0xe010be79 = {2, NULL, na_kanji0xe010be79};
const kanji_md * const na_kanji0xb67f912e[] = {&kanji_md7551, &kanji_md70AF};
const reading_md nanori_md0xb67f912e = {2, NULL, na_kanji0xb67f912e};
const kanji_md * const na_kanji0xf0d29d8e[] = {&kanji_md982D, &kanji_md4F8D};
const reading_md nanori_md0xf0d29d8e = {2, NULL, na_kanji0xf0d29d8e};
const kanji_md * const na_kanji0x8a26d134[] = {&kanji_md795E, &kanji_md7518, &kanji_md6A3A};
const reading_md nanori_md0x8a26d134 = {3, NULL, na_kanji0x8a26d134};
const kanji_md * const na_kanji0xda309a16[] = {&kanji_md6822};
const reading_md nanori_md0xda309a16 = {1, NULL, na_kanji0xda309a16};
const kanji_md * const na_kanji0x7c58e0c9[] = {&kanji_md65B9, &kanji_md67C4, &kanji_md6A3A};
const reading_md nanori_md0x7c58e0c9 = {3, NULL, na_kanji0x7c58e0c9};
const kanji_md * const na_kanji0x3b7b46e0[] = {&kanji_md6ED1, &kanji_md72E9, &kanji_md5208, &kanji_md82C5};
const reading_md nanori_md0x3b7b46e0 = {4, NULL, na_kanji0x3b7b46e0};
const kanji_md * const na_kanji0xf20c47b1[] = {&kanji_md82C5};
const reading_md nanori_md0xf20c47b1 = {1, NULL, na_kanji0xf20c47b1};
const kanji_md * const na_kanji0xa705519a[] = {&kanji_md5510};
const reading_md nanori_md0xa705519a = {1, NULL, na_kanji0xa705519a};
const kanji_md * const na_kanji0xed216150[] = {&kanji_md4E0A, &kanji_md91D1, &kanji_md5EB7, &kanji_md6E5B, &kanji_md6A3A, &kanji_md59DC, &kanji_md82C5};
const reading_md nanori_md0xed216150 = {7, NULL, na_kanji0xed216150};
const kanji_md * const na_kanji0xf3397f3f[] = {&kanji_md9591, &kanji_md73C2};
const reading_md nanori_md0xf3397f3f = {2, NULL, na_kanji0xf3397f3f};
const kanji_md * const na_kanji0xfac27b47[] = {&kanji_md8C37, &kanji_md57A3};
const reading_md nanori_md0xfac27b47 = {2, NULL, na_kanji0xfac27b47};
const kanji_md * const na_kanji0xe3cc17c3[] = {&kanji_md8C37};
const reading_md nanori_md0xe3cc17c3 = {1, NULL, na_kanji0xe3cc17c3};
const kanji_md * const na_kanji0x38b69fb3[] = {&kanji_md57CE};
const reading_md nanori_md0x38b69fb3 = {1, NULL, na_kanji0x38b69fb3};
const kanji_md * const na_kanji0xb507987a[] = {&kanji_md89BA};
const reading_md nanori_md0xb507987a = {1, NULL, na_kanji0xb507987a};
const kanji_md * const na_kanji0x4900bc84[] = {&kanji_md96A0};
const reading_md nanori_md0x4900bc84 = {1, NULL, na_kanji0x4900bc84};
const kanji_md * const na_kanji0x7c89f0bc[] = {&kanji_md7B28};
const reading_md nanori_md0x7c89f0bc = {1, NULL, na_kanji0x7c89f0bc};
const kanji_md * const na_kanji0x8c93cb86[] = {&kanji_md702C};
const reading_md nanori_md0x8c93cb86 = {1, NULL, na_kanji0x8c93cb86};
const kanji_md * const na_kanji0x6eeee0e[] = {&kanji_md9AEA, &kanji_md770C, &kanji_md7E23};
const reading_md nanori_md0x6eeee0e = {3, NULL, na_kanji0x6eeee0e};
const kanji_md * const na_kanji0xc73c7e7d[] = {&kanji_md6708};
const reading_md nanori_md0xc73c7e7d = {1, NULL, na_kanji0xc73c7e7d};
const kanji_md * const na_kanji0x17ab4683[] = {&kanji_md982D, &kanji_md8033, &kanji_md6A21, &kanji_md5C3B};
const reading_md nanori_md0x17ab4683 = {4, NULL, na_kanji0x17ab4683};
const kanji_md * const na_kanji0xdc6b3ef7[] = {&kanji_md8C37};
const reading_md nanori_md0xdc6b3ef7 = {1, NULL, na_kanji0xdc6b3ef7};
const kanji_md * const na_kanji0x2ac8e6d4[] = {&kanji_md6F5F};
const reading_md nanori_md0x2ac8e6d4 = {1, NULL, na_kanji0x2ac8e6d4};
const kanji_md * const na_kanji0x612876a[] = {&kanji_md5B50, &kanji_md7A7A, &kanji_md7F6E, &kanji_md6B21, &kanji_md516C, &kanji_md9152, &kanji_md6750, &kanji_md7532, &kanji_md96F2, &kanji_md82B8, &kanji_md5409, &kanji_md57CE, &kanji_md5200, &kanji_md5982, &kanji_md5E79, &kanji_md8302, &kanji_md4F2F, &kanji_md8217, &kanji_md5B9C, &kanji_md6176, &kanji_md5CE1, &kanji_md5983, &kanji_md6850, &kanji_md96C9, &kanji_md6775, &kanji_md6854, &kanji_md7396};
const reading_md nanori_md0x612876a = {27, NULL, na_kanji0x612876a};
const kanji_md * const na_kanji0x9c653686[] = {&kanji_md7D66, &kanji_md57FA};
const reading_md nanori_md0x9c653686 = {2, NULL, na_kanji0x9c653686};
const kanji_md * const na_kanji0x644bf5dc[] = {&kanji_md8074};
const reading_md nanori_md0x644bf5dc = {1, NULL, na_kanji0x644bf5dc};
const kanji_md * const na_kanji0x43cac2e2[] = {&kanji_md8C61};
const reading_md nanori_md0x43cac2e2 = {1, NULL, na_kanji0x43cac2e2};
const kanji_md * const na_kanji0x8a902df5[] = {&kanji_md840C};
const reading_md nanori_md0x8a902df5 = {1, NULL, na_kanji0x8a902df5};
const kanji_md * const na_kanji0x8702f007[] = {&kanji_md963F};
const reading_md nanori_md0x8702f007 = {1, NULL, na_kanji0x8702f007};
const kanji_md * const na_kanji0x1dc5c359[] = {&kanji_md5409, &kanji_md6A58};
const reading_md nanori_md0x1dc5c359 = {2, NULL, na_kanji0x1dc5c359};
const kanji_md * const na_kanji0x75d80e0f[] = {&kanji_md5207};
const reading_md nanori_md0x75d80e0f = {1, NULL, na_kanji0x75d80e0f};
const kanji_md * const na_kanji0x2ecc7663[] = {&kanji_md516C, &kanji_md4EC1};
const reading_md nanori_md0x2ecc7663 = {2, NULL, na_kanji0x2ecc7663};
const kanji_md * const na_kanji0x18b8e552[] = {&kanji_md91D1};
const reading_md nanori_md0x18b8e552 = {1, NULL, na_kanji0x18b8e552};
const kanji_md * const na_kanji0xeab5f6a[] = {&kanji_md559C, &kanji_md4E45, &kanji_md7A76};
const reading_md nanori_md0xeab5f6a = {3, NULL, na_kanji0xeab5f6a};
const kanji_md * const na_kanji0x72ba68b8[] = {&kanji_md50D1};
const reading_md nanori_md0x72ba68b8 = {1, NULL, na_kanji0x72ba68b8};
const kanji_md * const na_kanji0x29c1c947[] = {&kanji_md53B3};
const reading_md nanori_md0x29c1c947 = {1, NULL, na_kanji0x29c1c947};
const kanji_md * const na_kanji0xf08204ff[] = {&kanji_md4EAE};
const reading_md nanori_md0xf08204ff = {1, NULL, na_kanji0xf08204ff};
const kanji_md * const na_kanji0x87d08435[] = {&kanji_md7CBE, &kanji_md8CB4, &kanji_md6F84, &kanji_md6F54, &kanji_md8056, &kanji_md8AA0, &kanji_md658E, &kanji_md606D, &kanji_md5EC9, &kanji_md6E5B, &kanji_md6DF3, &kanji_md572D, &kanji_md99A8, &kanji_md5321};
const reading_md nanori_md0x87d08435 = {14, NULL, na_kanji0x87d08435};
const kanji_md * const na_kanji0x3fc96789[] = {&kanji_md5FE0, &kanji_md6F54, &kanji_md6DF3, &kanji_md572D, &kanji_md9756, &kanji_md6E19};
const reading_md nanori_md0x3fc96789 = {6, NULL, na_kanji0x3fc96789};
const kanji_md * const na_kanji0x8d128b33[] = {&kanji_md6176};
const reading_md nanori_md0x8d128b33 = {1, NULL, na_kanji0x8d128b33};
const kanji_md * const na_kanji0xaeca2f37[] = {&kanji_md660E, &kanji_md73FE, &kanji_md5317};
const reading_md nanori_md0xaeca2f37 = {3, NULL, na_kanji0xaeca2f37};
const kanji_md * const na_kanji0x43c665cb[] = {&kanji_md5207};
const reading_md nanori_md0x43c665cb = {1, NULL, na_kanji0x43c665cb};
const kanji_md * const na_kanji0x958c327b[] = {&kanji_md5409};
const reading_md nanori_md0x958c327b = {1, NULL, na_kanji0x958c327b};
const kanji_md * const na_kanji0x89f15a88[] = {&kanji_md516C, &kanji_md5805};
const reading_md nanori_md0x89f15a88 = {2, NULL, na_kanji0x89f15a88};
const kanji_md * const na_kanji0xe62e0bb1[] = {&kanji_md5B50, &kanji_md5341, &kanji_md8ABF, &kanji_md89AA, &kanji_md8CB4};
const reading_md nanori_md0xe62e0bb1 = {5, NULL, na_kanji0xe62e0bb1};
const kanji_md * const na_kanji0xe4d7ab06[] = {&kanji_md88AB};
const reading_md nanori_md0xe4d7ab06 = {1, NULL, na_kanji0xe4d7ab06};
const kanji_md * const na_kanji0x5dd962bf[] = {&kanji_md751F};
const reading_md nanori_md0x5dd962bf = {1, NULL, na_kanji0x5dd962bf};
const kanji_md * const na_kanji0x7abf87bc[] = {&kanji_md5211};
const reading_md nanori_md0x7abf87bc = {1, NULL, na_kanji0x7abf87bc};
const kanji_md * const na_kanji0x4ee2b9a5[] = {&kanji_md5207};
const reading_md nanori_md0x4ee2b9a5 = {1, NULL, na_kanji0x4ee2b9a5};
const kanji_md * const na_kanji0x458da2be[] = {&kanji_md65E5, &kanji_md5B50, &kanji_md5BB6, &kanji_md7A7A, &kanji_md516D, &kanji_md7403, &kanji_md5E7E, &kanji_md8A13, &kanji_md4EC1};
const reading_md nanori_md0x458da2be = {9, NULL, na_kanji0x458da2be};
const kanji_md * const na_kanji0xf556a40d[] = {&kanji_md548B};
const reading_md nanori_md0xf556a40d = {1, NULL, na_kanji0xf556a40d};
const kanji_md * const na_kanji0xe9fe8a4e[] = {&kanji_md9678};
const reading_md nanori_md0xe9fe8a4e = {1, NULL, na_kanji0xe9fe8a4e};
const kanji_md * const na_kanji0x10f384f2[] = {&kanji_md65E5, &kanji_md7A2E};
const reading_md nanori_md0x10f384f2 = {2, NULL, na_kanji0x10f384f2};
const kanji_md * const na_kanji0x968c1d9b[] = {&kanji_md91E7};
const reading_md nanori_md0x968c1d9b = {1, NULL, na_kanji0x968c1d9b};
const kanji_md * const na_kanji0x7981bae8[] = {&kanji_md6960};
const reading_md nanori_md0x7981bae8 = {1, NULL, na_kanji0x7981bae8};
const kanji_md * const na_kanji0xf04260b5[] = {&kanji_md5544};
const reading_md nanori_md0xf04260b5 = {1, NULL, na_kanji0xf04260b5};
const kanji_md * const na_kanji0x5e40d4ab[] = {&kanji_md5C48};
const reading_md nanori_md0x5e40d4ab = {1, NULL, na_kanji0x5e40d4ab};
const kanji_md * const na_kanji0xd0761a86[] = {&kanji_md673D};
const reading_md nanori_md0xd0761a86 = {1, NULL, na_kanji0xd0761a86};
const kanji_md * const na_kanji0x15fd14dd[] = {&kanji_md56FD};
const reading_md nanori_md0x15fd14dd = {1, NULL, na_kanji0x15fd14dd};
const kanji_md * const na_kanji0xd53f6a94[] = {&kanji_md6B63, &kanji_md6709, &kanji_md90FD, &kanji_md57CE, &kanji_md90F7, &kanji_md8A13, &kanji_md5DDE, &kanji_md4E4B, &kanji_md85AB, &kanji_md664B, &kanji_md9091};
const reading_md nanori_md0xd53f6a94 = {11, NULL, na_kanji0xd53f6a94};
const kanji_md * const na_kanji0xc1a5c011[] = {&kanji_md529F};
const reading_md nanori_md0xc1a5c011 = {1, NULL, na_kanji0xc1a5c011};
const kanji_md * const na_kanji0xbee5c3de[] = {&kanji_md8A13};
const reading_md nanori_md0xbee5c3de = {1, NULL, na_kanji0xbee5c3de};
const kanji_md * const na_kanji0xe7bcd185[] = {&kanji_md795E};
const reading_md nanori_md0xe7bcd185 = {1, NULL, na_kanji0xe7bcd185};
const kanji_md * const na_kanji0x1b8e52b1[] = {&kanji_md6C72, &kanji_md4F0D};
const reading_md nanori_md0x1b8e52b1 = {2, NULL, na_kanji0x1b8e52b1};
const kanji_md * const na_kanji0xf26b1833[] = {&kanji_md8ECA};
const reading_md nanori_md0xf26b1833 = {1, NULL, na_kanji0xf26b1833};
const kanji_md * const na_kanji0x1ecd8b8a[] = {&kanji_md8535};
const reading_md nanori_md0x1ecd8b8a = {1, NULL, na_kanji0x1ecd8b8a};
const kanji_md * const na_kanji0x813b75b8[] = {&kanji_md8535};
const reading_md nanori_md0x813b75b8 = {1, NULL, na_kanji0x813b75b8};
const kanji_md * const na_kanji0x34bde932[] = {&kanji_md6765, &kanji_md4F5C, &kanji_md7E70};
const reading_md nanori_md0x34bde932 = {3, NULL, na_kanji0x34bde932};
const kanji_md * const na_kanji0xf7d1f462[] = {&kanji_md6765, &kanji_md5E79, &kanji_md80E1, &kanji_md6817};
const reading_md nanori_md0xf7d1f462 = {4, NULL, na_kanji0xf7d1f462};
const kanji_md * const na_kanji0x95d66586[] = {&kanji_md751F, &kanji_md695C};
const reading_md nanori_md0x95d66586 = {2, NULL, na_kanji0x95d66586};
const kanji_md * const na_kanji0x59a300d0[] = {&kanji_md7D05};
const reading_md nanori_md0x59a300d0 = {1, NULL, na_kanji0x59a300d0};
const kanji_md * const na_kanji0xdd843254[] = {&kanji_md60A3};
const reading_md nanori_md0xdd843254 = {1, NULL, na_kanji0xdd843254};
const kanji_md * const na_kanji0x6ba2ee98[] = {&kanji_md8535};
const reading_md nanori_md0x6ba2ee98 = {1, NULL, na_kanji0x6ba2ee98};
const kanji_md * const na_kanji0xa329b93[] = {&kanji_md8ECA};
const reading_md nanori_md0xa329b93 = {1, NULL, na_kanji0xa329b93};
const kanji_md * const na_kanji0x9bd724a4[] = {&kanji_md6C5F};
const reading_md nanori_md0x9bd724a4 = {1, NULL, na_kanji0x9bd724a4};
const kanji_md * const na_kanji0xae0fd607[] = {&kanji_md6728, &kanji_md5C45, &kanji_md7FA4, &kanji_md5BAE, &kanji_md5449};
const reading_md nanori_md0xae0fd607 = {5, NULL, na_kanji0xae0fd607};
const kanji_md * const na_kanji0x5844bbd5[] = {&kanji_md98DF};
const reading_md nanori_md0x5844bbd5 = {1, NULL, na_kanji0x5844bbd5};
const kanji_md * const na_kanji0x49e3dcc9[] = {&kanji_md529F};
const reading_md nanori_md0x49e3dcc9 = {1, NULL, na_kanji0x49e3dcc9};
const kanji_md * const na_kanji0x3d288b1d[] = {&kanji_md679D};
const reading_md nanori_md0x3d288b1d = {1, NULL, na_kanji0x3d288b1d};
const kanji_md * const na_kanji0x9a7264c0[] = {&kanji_md57CE};
const reading_md nanori_md0x9a7264c0 = {1, NULL, na_kanji0x9a7264c0};
const kanji_md * const na_kanji0xff4f3dd9[] = {&kanji_md57CE};
const reading_md nanori_md0xff4f3dd9 = {1, NULL, na_kanji0xff4f3dd9};
const kanji_md * const na_kanji0x8f148f69[] = {&kanji_md5B9F};
const reading_md nanori_md0x8f148f69 = {1, NULL, na_kanji0x8f148f69};
const kanji_md * const na_kanji0x2b42893c[] = {&kanji_md63A0, &kanji_md690B};
const reading_md nanori_md0x2b42893c = {2, NULL, na_kanji0x2b42893c};
const kanji_md * const na_kanji0xb5110122[] = {&kanji_md66AE};
const reading_md nanori_md0xb5110122 = {1, NULL, na_kanji0xb5110122};
const kanji_md * const na_kanji0x1b09d46a[] = {&kanji_md7FA4};
const reading_md nanori_md0x1b09d46a = {1, NULL, na_kanji0x1b09d46a};
const kanji_md * const na_kanji0x205a8ff0[] = {&kanji_md66AE, &kanji_md535A};
const reading_md nanori_md0x205a8ff0 = {2, NULL, na_kanji0x205a8ff0};
const kanji_md * const na_kanji0x30caf112[] = {&kanji_md7554};
const reading_md nanori_md0x30caf112 = {1, NULL, na_kanji0x30caf112};
const kanji_md * const na_kanji0x15adb099[] = {&kanji_md5B50, &kanji_md660E, &kanji_md5916, &kanji_md8A08, &kanji_md656C, &kanji_md5B85, &kanji_md6075, &kanji_md6176, &kanji_md8475};
const reading_md nanori_md0x15adb099 = {9, NULL, na_kanji0x15adb099};
const kanji_md * const na_kanji0xb490512c[] = {&kanji_md4F73};
const reading_md nanori_md0xb490512c = {1, NULL, na_kanji0xb490512c};
const kanji_md * const na_kanji0x50262c49[] = {&kanji_md5CB8};
const reading_md nanori_md0x50262c49 = {1, NULL, na_kanji0x50262c49};
const kanji_md * const na_kanji0xa41934e9[] = {&kanji_md7A74};
const reading_md nanori_md0xa41934e9 = {1, NULL, na_kanji0xa41934e9};
const kanji_md * const na_kanji0x805235fb[] = {&kanji_md9477};
const reading_md nanori_md0x805235fb = {1, NULL, na_kanji0x805235fb};
const kanji_md * const na_kanji0xb864fe71[] = {&kanji_md9244, &kanji_md7384, &kanji_md76E3};
const reading_md nanori_md0xb864fe71 = {3, NULL, na_kanji0xb864fe71};
const kanji_md * const na_kanji0x79b365c1[] = {&kanji_md82B8, &kanji_md690D, &kanji_md524A, &kanji_md6B96};
const reading_md nanori_md0x79b365c1 = {4, NULL, na_kanji0x79b365c1};
const kanji_md * const na_kanji0x839a1ad4[] = {&kanji_md9AD8, &kanji_md597D, &kanji_md795E, &kanji_md91D1, &kanji_md56FD, &kanji_md5E78, &kanji_md5DDD, &kanji_md9999, &kanji_md5DE8, &kanji_md53F2, &kanji_md6CB3, &kanji_md5EB7, &kanji_md6A39, &kanji_md5F13, &kanji_md5F66, &kanji_md6851, &kanji_md570B};
const reading_md nanori_md0x839a1ad4 = {17, NULL, na_kanji0x839a1ad4};
const kanji_md * const na_kanji0x411e148a[] = {&kanji_md80A5};
const reading_md nanori_md0x411e148a = {1, NULL, na_kanji0x411e148a};
const kanji_md * const na_kanji0x468b2e71[] = {&kanji_md65E5, &kanji_md4E0A, &kanji_md5C0F, &kanji_md5408, &kanji_md8C6A, &kanji_md5302, &kanji_md6CB3, &kanji_md525B, &kanji_md7A42};
const reading_md nanori_md0x468b2e71 = {9, NULL, na_kanji0x468b2e71};
const kanji_md * const na_kanji0x457aa9d7[] = {&kanji_md8D8A};
const reading_md nanori_md0x457aa9d7 = {1, NULL, na_kanji0x457aa9d7};
const kanji_md * const na_kanji0x416b1010[] = {&kanji_md5411, &kanji_md5149, &kanji_md7FA4, &kanji_md9999, &kanji_md8015, &kanji_md5F18, &kanji_md6D69};
const reading_md nanori_md0x416b1010 = {7, NULL, na_kanji0x416b1010};
const kanji_md * const na_kanji0x3b9a077c[] = {&kanji_md7FA4, &kanji_md7E54, &kanji_md51CD};
const reading_md nanori_md0x3b9a077c = {3, NULL, na_kanji0x3b9a077c};
const kanji_md * const na_kanji0xcd7de9bc[] = {&kanji_md829D};
const reading_md nanori_md0xcd7de9bc = {1, NULL, na_kanji0xcd7de9bc};
const kanji_md * const na_kanji0xa7ae5c4[] = {&kanji_md5F8C, &kanji_md8D8A, &kanji_md5409};
const reading_md nanori_md0xa7ae5c4 = {3, NULL, na_kanji0xa7ae5c4};
const kanji_md * const na_kanji0x9e57ae3c[] = {&kanji_md793E};
const reading_md nanori_md0x9e57ae3c = {1, NULL, na_kanji0x9e57ae3c};
const kanji_md * const na_kanji0x8b853812[] = {&kanji_md6771};
const reading_md nanori_md0x8b853812 = {1, NULL, na_kanji0x8b853812};
const kanji_md * const na_kanji0x42d74feb[] = {&kanji_md5700};
const reading_md nanori_md0x42d74feb = {1, NULL, na_kanji0x42d74feb};
const kanji_md * const na_kanji0xb795b628[] = {&kanji_md627F, &kanji_md529F};
const reading_md nanori_md0xb795b628 = {2, NULL, na_kanji0xb795b628};
const kanji_md * const na_kanji0x67e6c5a3[] = {&kanji_md8FD1, &kanji_md91D1, &kanji_md4E5D};
const reading_md nanori_md0x67e6c5a3 = {3, NULL, na_kanji0x67e6c5a3};
const kanji_md * const na_kanji0xd960695[] = {&kanji_md795E};
const reading_md nanori_md0xd960695 = {1, NULL, na_kanji0xd960695};
const kanji_md * const na_kanji0x909d7b9a[] = {&kanji_md7B7A};
const reading_md nanori_md0x909d7b9a = {1, NULL, na_kanji0x909d7b9a};
const kanji_md * const na_kanji0x9ae3aac8[] = {&kanji_md5A9A};
const reading_md nanori_md0x9ae3aac8 = {1, NULL, na_kanji0x9ae3aac8};
const kanji_md * const na_kanji0xe3e0a2f6[] = {&kanji_md9996};
const reading_md nanori_md0xe3e0a2f6 = {1, NULL, na_kanji0xe3e0a2f6};
const kanji_md * const na_kanji0x8a723216[] = {&kanji_md8FBC};
const reading_md nanori_md0x8a723216 = {1, NULL, na_kanji0x8a723216};
const kanji_md * const na_kanji0xc153b214[] = {&kanji_md85A6};
const reading_md nanori_md0xc153b214 = {1, NULL, na_kanji0xc153b214};
const kanji_md * const na_kanji0x3db66a9c[] = {&kanji_md7E46};
const reading_md nanori_md0x3db66a9c = {1, NULL, na_kanji0x3db66a9c};
const kanji_md * const na_kanji0xc7693dda[] = {&kanji_md7E54};
const reading_md nanori_md0xc7693dda = {1, NULL, na_kanji0xc7693dda};
const kanji_md * const na_kanji0xa1817ca7[] = {&kanji_md4F0A, &kanji_md7DAD};
const reading_md nanori_md0xa1817ca7 = {2, NULL, na_kanji0xa1817ca7};
const kanji_md * const na_kanji0xf602fe5a[] = {&kanji_md9803};
const reading_md nanori_md0xf602fe5a = {1, NULL, na_kanji0xf602fe5a};
const kanji_md * const na_kanji0x5353c4d3[] = {&kanji_md6BC5};
const reading_md nanori_md0x5353c4d3 = {1, NULL, na_kanji0x5353c4d3};
const kanji_md * const na_kanji0xf54ab753[] = {&kanji_md7802, &kanji_md8C6A, &kanji_md725B, &kanji_md525B};
const reading_md nanori_md0xf54ab753 = {4, NULL, na_kanji0xf54ab753};
const kanji_md * const na_kanji0x88f97674[] = {&kanji_md672C};
const reading_md nanori_md0x88f97674 = {1, NULL, na_kanji0x88f97674};
const kanji_md * const na_kanji0xcbd73a7c[] = {&kanji_md7FA4};
const reading_md nanori_md0xcbd73a7c = {1, NULL, na_kanji0xcbd73a7c};
const kanji_md * const na_kanji0x2eca982[] = {&kanji_md8D8A};
const reading_md nanori_md0x2eca982 = {1, NULL, na_kanji0x2eca982};
const kanji_md * const na_kanji0xa3bbb0fe[] = {&kanji_md5408};
const reading_md nanori_md0xa3bbb0fe = {1, NULL, na_kanji0xa3bbb0fe};
const kanji_md * const na_kanji0x3ff8bd72[] = {&kanji_md8D8A};
const reading_md nanori_md0x3ff8bd72 = {1, NULL, na_kanji0x3ff8bd72};
const kanji_md * const na_kanji0x2d11ca1d[] = {&kanji_md751F};
const reading_md nanori_md0x2d11ca1d = {1, NULL, na_kanji0x2d11ca1d};
const kanji_md * const na_kanji0x83e5fa3[] = {&kanji_md8FBC, &kanji_md7C60, &kanji_md7BED};
const reading_md nanori_md0x83e5fa3 = {3, NULL, na_kanji0x83e5fa3};
const kanji_md * const na_kanji0x39bdc14c[] = {&kanji_md8D8A};
const reading_md nanori_md0x39bdc14c = {1, NULL, na_kanji0x39bdc14c};
const kanji_md * const na_kanji0x601a1284[] = {&kanji_md6765};
const reading_md nanori_md0x601a1284 = {1, NULL, na_kanji0x601a1284};
const kanji_md * const na_kanji0xc1350d02[] = {&kanji_md751F, &kanji_md6765, &kanji_md4E09, &kanji_md9053, &kanji_md76F8, &kanji_md5341, &kanji_md697D, &kanji_md4E94, &kanji_md5C71, &kanji_md4EFB, &kanji_md8B1D, &kanji_md9152, &kanji_md5BD2, &kanji_md820E, &kanji_md6CA2, &kanji_md6D45, &kanji_md91CC, &kanji_md5F69, &kanji_md54B2, &kanji_md7CA7, &kanji_md685C, &kanji_md733F, &kanji_md685F, &kanji_md7B39, &kanji_md6284, &kanji_md9DE6};
const reading_md nanori_md0xc1350d02 = {26, NULL, na_kanji0xc1350d02};
const kanji_md * const na_kanji0xb5a67966[] = {&kanji_md4E09, &kanji_md4E95, &kanji_md6750, &kanji_md7D2B, &kanji_md7A0E, &kanji_md96DC};
const reading_md nanori_md0xb5a67966 = {6, NULL, na_kanji0xb5a67966};
const kanji_md * const na_kanji0x2284ab62[] = {&kanji_md4E09, &kanji_md5F69, &kanji_md658E, &kanji_md6717, &kanji_md51B4};
const reading_md nanori_md0x2284ab62 = {5, NULL, na_kanji0x2284ab62};
const kanji_md * const na_kanji0xd793524d[] = {&kanji_md51B4};
const reading_md nanori_md0xd793524d = {1, NULL, na_kanji0xd793524d};
const kanji_md * const na_kanji0x6b48da1e[] = {&kanji_md64CD};
const reading_md nanori_md0x6b48da1e = {1, NULL, na_kanji0x6b48da1e};
const kanji_md * const na_kanji0x471c145c[] = {&kanji_md4E0B, &kanji_md4F5C, &kanji_md65E9, &kanji_md7A4D, &kanji_md5883, &kanji_md8CE2, &kanji_md7965};
const reading_md nanori_md0x471c145c = {7, NULL, na_kanji0x471c145c};
const kanji_md * const na_kanji0xff98cc3a[] = {&kanji_md6804, &kanji_md660C};
const reading_md nanori_md0xff98cc3a = {2, NULL, na_kanji0xff98cc3a};
const kanji_md * const na_kanji0x6756ec45[] = {&kanji_md76EE};
const reading_md nanori_md0x6756ec45 = {1, NULL, na_kanji0x6756ec45};
const kanji_md * const na_kanji0x89a90a42[] = {&kanji_md76F8};
const reading_md nanori_md0x89a90a42 = {1, NULL, na_kanji0x89a90a42};
const kanji_md * const na_kanji0x7104c5f4[] = {&kanji_md76EE};
const reading_md nanori_md0x7104c5f4 = {1, NULL, na_kanji0x7104c5f4};
const kanji_md * const na_kanji0x6945dfbe[] = {&kanji_md524D, &kanji_md5E78, &kanji_md6771, &kanji_md8F1D, &kanji_md54B2, &kanji_md7965, &kanji_md7B39, &kanji_md5CAC};
const reading_md nanori_md0x6945dfbe = {8, NULL, na_kanji0x6945dfbe};
const kanji_md * const na_kanji0xcaac8036[] = {&kanji_md5302};
const reading_md nanori_md0xcaac8036 = {1, NULL, na_kanji0xcaac8036};
const kanji_md * const na_kanji0xda7a350c[] = {&kanji_md8FEB, &kanji_md6D74, &kanji_md7872};
const reading_md nanori_md0xda7a350c = {3, NULL, na_kanji0xda7a350c};
const kanji_md * const na_kanji0xe825639f[] = {&kanji_md671D};
const reading_md nanori_md0xe825639f = {1, NULL, na_kanji0xe825639f};
const kanji_md * const na_kanji0x63ed37bf[] = {&kanji_md5C0F, &kanji_md8C9E};
const reading_md nanori_md0x63ed37bf = {2, NULL, na_kanji0x63ed37bf};
const kanji_md * const na_kanji0xf822b225[] = {&kanji_md6307, &kanji_md5E78, &kanji_md8535};
const reading_md nanori_md0xf822b225 = {3, NULL, na_kanji0xf822b225};
const kanji_md * const na_kanji0x46753de1[] = {&kanji_md6307};
const reading_md nanori_md0x46753de1 = {1, NULL, na_kanji0x46753de1};
const kanji_md * const na_kanji0x92598837[] = {&kanji_md5B9A, &kanji_md8061};
const reading_md nanori_md0x92598837 = {2, NULL, na_kanji0x92598837};
const kanji_md * const na_kanji0x119169ae[] = {&kanji_md5C0A, &kanji_md798E};
const reading_md nanori_md0x119169ae = {2, NULL, na_kanji0x119169ae};
const kanji_md * const na_kanji0xbda8ed35[] = {&kanji_md7965, &kanji_md7950, &kanji_md798E};
const reading_md nanori_md0xbda8ed35 = {3, NULL, na_kanji0xbda8ed35};
const kanji_md * const na_kanji0xed38c7a7[] = {&kanji_md4F5C, &kanji_md5E78, &kanji_md672D, &kanji_md85A9, &kanji_md7C9F};
const reading_md nanori_md0xed38c7a7 = {5, NULL, na_kanji0xed38c7a7};
const kanji_md * const na_kanji0x93e8a0a6[] = {&kanji_md76EE, &kanji_md5C5E};
const reading_md nanori_md0x93e8a0a6 = {2, NULL, na_kanji0x93e8a0a6};
const kanji_md * const na_kanji0x8394b250[] = {&kanji_md4E94};
const reading_md nanori_md0x8394b250 = {1, NULL, na_kanji0x8394b250};
const kanji_md * const na_kanji0xe2d46fa1[] = {&kanji_md76EE};
const reading_md nanori_md0xe2d46fa1 = {1, NULL, na_kanji0xe2d46fa1};
const kanji_md * const na_kanji0x6044758c[] = {&kanji_md524D, &kanji_md77E5, &kanji_md7406, &kanji_md8B58, &kanji_md9054, &kanji_md6075, &kanji_md592E, &kanji_md8056, &kanji_md8CE2, &kanji_md8AA0, &kanji_md4EC1, &kanji_md54F2, &kanji_md667A, &kanji_md6681, &kanji_md8061, &kanji_md540F, &kanji_md6167, &kanji_md601C, &kanji_md9091, &kanji_md6031};
const reading_md nanori_md0x6044758c = {20, NULL, na_kanji0x6044758c};
const kanji_md * const na_kanji0x15b95b7c[] = {&kanji_md667A};
const reading_md nanori_md0x15b95b7c = {1, NULL, na_kanji0x15b95b7c};
const kanji_md * const na_kanji0x70eb70d0[] = {&kanji_md8AAC, &kanji_md6075, &kanji_md7701, &kanji_md654F, &kanji_md8056, &kanji_md8CE2, &kanji_md8A13, &kanji_md54F2, &kanji_md667A, &kanji_md5553, &kanji_md8061, &kanji_md6167, &kanji_md601C, &kanji_md8A54, &kanji_md8070};
const reading_md nanori_md0x70eb70d0 = {15, NULL, na_kanji0x70eb70d0};
const kanji_md * const na_kanji0x68cca42b[] = {&kanji_md77E5, &kanji_md7406, &kanji_md89E3, &kanji_md8B58, &kanji_md52D8, &kanji_md4E86, &kanji_md54F2, &kanji_md667A, &kanji_md6681, &kanji_md8061, &kanji_md6167, &kanji_md5B78};
const reading_md nanori_md0x68cca42b = {12, NULL, na_kanji0x68cca42b};
const kanji_md * const na_kanji0x2331c224[] = {&kanji_md771F, &kanji_md771E, &kanji_md5BE6};
const reading_md nanori_md0x2331c224 = {3, NULL, na_kanji0x2331c224};
const kanji_md * const na_kanji0xc4889b0c[] = {&kanji_md8B83};
const reading_md nanori_md0xc4889b0c = {1, NULL, na_kanji0xc4889b0c};
const kanji_md * const na_kanji0x4c23f972[] = {&kanji_md5B9F, &kanji_md91CD, &kanji_md771F, &kanji_md5BE6};
const reading_md nanori_md0x4c23f972 = {4, NULL, na_kanji0x4c23f972};
const kanji_md * const na_kanji0x4c7b86ee[] = {&kanji_md4E09};
const reading_md nanori_md0x4c7b86ee = {1, NULL, na_kanji0x4c7b86ee};
const kanji_md * const na_kanji0x19e43533[] = {&kanji_md7965};
const reading_md nanori_md0x19e43533 = {1, NULL, na_kanji0x19e43533};
const kanji_md * const na_kanji0x8fcbc9c5[] = {&kanji_md660E, &kanji_md6E05};
const reading_md nanori_md0x8fcbc9c5 = {2, NULL, na_kanji0x8fcbc9c5};
const kanji_md * const na_kanji0xee30aa3d[] = {&kanji_md660E};
const reading_md nanori_md0xee30aa3d = {1, NULL, na_kanji0xee30aa3d};
const kanji_md * const na_kanji0x5e996f5f[] = {&kanji_md4F5B};
const reading_md nanori_md0x5e996f5f = {1, NULL, na_kanji0x5e996f5f};
const kanji_md * const na_kanji0x2d34a03b[] = {&kanji_md65E9, &kanji_md5DDD, &kanji_md733F};
const reading_md nanori_md0x2d34a03b = {3, NULL, na_kanji0x2d34a03b};
const kanji_md * const na_kanji0xcbe37b4[] = {&kanji_md6CA2};
const reading_md nanori_md0xcbe37b4 = {1, NULL, na_kanji0xcbe37b4};
const kanji_md * const na_kanji0xecd93891[] = {&kanji_md5BD2};
const reading_md nanori_md0xecd93891 = {1, NULL, na_kanji0xecd93891};
const kanji_md * const na_kanji0x65540c7f[] = {&kanji_md4E09, &kanji_md8B1D, &kanji_md8535, &kanji_md5742};
const reading_md nanori_md0x65540c7f = {4, NULL, na_kanji0x65540c7f};
const kanji_md * const na_kanji0x17414d43[] = {&kanji_md4E09};
const reading_md nanori_md0x17414d43 = {1, NULL, na_kanji0x17414d43};
const kanji_md * const na_kanji0x5c8e6519[] = {&kanji_md9DFD};
const reading_md nanori_md0x5c8e6519 = {1, NULL, na_kanji0x5c8e6519};
const kanji_md * const na_kanji0x1baecc4e[] = {&kanji_md96C0};
const reading_md nanori_md0x1baecc4e = {1, NULL, na_kanji0x1baecc4e};
const kanji_md * const na_kanji0xe7ebb411[] = {&kanji_md5EFB};
const reading_md nanori_md0xe7ebb411 = {1, NULL, na_kanji0xe7ebb411};
const kanji_md * const na_kanji0x9db5d77f[] = {&kanji_md4E09};
const reading_md nanori_md0x9db5d77f = {1, NULL, na_kanji0x9db5d77f};
const kanji_md * const na_kanji0x4d59b629[] = {&kanji_md733F};
const reading_md nanori_md0x4d59b629 = {1, NULL, na_kanji0x4d59b629};
const kanji_md * const na_kanji0xc2992670[] = {&kanji_md5F8C, &kanji_md521D, &kanji_md4FE1, &kanji_md65B0, &kanji_md5341, &kanji_md5B88, &kanji_md4F4F, &kanji_md77F3, &kanji_md4E03, &kanji_md6CBB, &kanji_md9152, &kanji_md6E05, &kanji_md57F7, &kanji_md5DF1, &kanji_md811A, &kanji_md6797, &kanji_md5B97, &kanji_md8302, &kanji_md4E5F, &kanji_md540F, &kanji_md78EF, &kanji_md5937, &kanji_md6ECB, &kanji_md6B23, &kanji_md5B8D, &kanji_md6AAE, &kanji_md5CBB};
const reading_md nanori_md0xc2992670 = {27, NULL, na_kanji0xc2992670};
const kanji_md * const na_kanji0xb2453625[] = {&kanji_md5F8C, &kanji_md690E};
const reading_md nanori_md0xb2453625 = {2, NULL, na_kanji0xb2453625};
const kanji_md * const na_kanji0xbb2a18a6[] = {&kanji_md8272, &kanji_md98FE};
const reading_md nanori_md0xbb2a18a6 = {2, NULL, na_kanji0xbb2a18a6};
const kanji_md * const na_kanji0x57f79c3e[] = {&kanji_md4FE1};
const reading_md nanori_md0x57f79c3e = {1, NULL, na_kanji0x57f79c3e};
const kanji_md * const na_kanji0x95e19782[] = {&kanji_md6577, &kanji_md57CE, &kanji_md92EA};
const reading_md nanori_md0x95e19782 = {3, NULL, na_kanji0x95e19782};
const kanji_md * const na_kanji0x1c3fe72f[] = {&kanji_md91CD, &kanji_md6210, &kanji_md9806, &kanji_md6804, &kanji_md6075, &kanji_md6A39, &kanji_md8AA0, &kanji_md93AE, &kanji_md702C, &kanji_md6148, &kanji_md85AB, &kanji_md6ECB, &kanji_md8543, &kanji_md7A63, &kanji_md54B8};
const reading_md nanori_md0x1c3fe72f = {15, NULL, na_kanji0x1c3fe72f};
const kanji_md * const na_kanji0x6337135[] = {&kanji_md91CD, &kanji_md6ECB, &kanji_md536F, &kanji_md8543};
const reading_md nanori_md0x6337135 = {4, NULL, na_kanji0x6337135};
const kanji_md * const na_kanji0x5d785775[] = {&kanji_md8272};
const reading_md nanori_md0x5d785775 = {1, NULL, na_kanji0x5d785775};
const kanji_md * const na_kanji0x9b30f2c2[] = {&kanji_md7A74, &kanji_md9E7F};
const reading_md nanori_md0x9b30f2c2 = {2, NULL, na_kanji0x9b30f2c2};
const kanji_md * const na_kanji0xa29d1947[] = {&kanji_md9756};
const reading_md nanori_md0xa29d1947 = {1, NULL, na_kanji0xa29d1947};
const kanji_md * const na_kanji0xb0a43920[] = {&kanji_md975C};
const reading_md nanori_md0xb0a43920 = {1, NULL, na_kanji0xb0a43920};
const kanji_md * const na_kanji0x800b99b9[] = {&kanji_md8A2D};
const reading_md nanori_md0x800b99b9 = {1, NULL, na_kanji0x800b99b9};
const kanji_md * const na_kanji0x13fb0033[] = {&kanji_md9806};
const reading_md nanori_md0x13fb0033 = {1, NULL, na_kanji0x13fb0033};
const kanji_md * const na_kanji0x929a45c2[] = {&kanji_md4E03};
const reading_md nanori_md0x929a45c2 = {1, NULL, na_kanji0x929a45c2};
const kanji_md * const na_kanji0xd104ee62[] = {&kanji_md9759};
const reading_md nanori_md0xd104ee62 = {1, NULL, na_kanji0xd104ee62};
const kanji_md * const na_kanji0x4322a87f[] = {&kanji_md5E63};
const reading_md nanori_md0x4322a87f = {1, NULL, na_kanji0x4322a87f};
const kanji_md * const na_kanji0x286eda6c[] = {&kanji_md4E0B};
const reading_md nanori_md0x286eda6c = {1, NULL, na_kanji0x286eda6c};
const kanji_md * const na_kanji0x30eb344f[] = {&kanji_md4FE1, &kanji_md59FF, &kanji_md968E, &kanji_md7D1A, &kanji_md79D1};
const reading_md nanori_md0x30eb344f = {5, NULL, na_kanji0x30eb344f};
const kanji_md * const na_kanji0xe27da43d[] = {&kanji_md7A32};
const reading_md nanori_md0xe27da43d = {1, NULL, na_kanji0xe27da43d};
const kanji_md * const na_kanji0xc0abb99f[] = {&kanji_md4FE1, &kanji_md6771, &kanji_md7B39};
const reading_md nanori_md0xc0abb99f = {3, NULL, na_kanji0xc0abb99f};
const kanji_md * const na_kanji0xe7055ae0[] = {&kanji_md4EC1};
const reading_md nanori_md0xe7055ae0 = {1, NULL, na_kanji0xe7055ae0};
const kanji_md * const na_kanji0x2a79fb95[] = {&kanji_md829D};
const reading_md nanori_md0x2a79fb95 = {1, NULL, na_kanji0x2a79fb95};
const kanji_md * const na_kanji0xa3c42041[] = {&kanji_md4FE1};
const reading_md nanori_md0xa3c42041 = {1, NULL, na_kanji0xa3c42041};
const kanji_md * const na_kanji0x5414a9f6[] = {&kanji_md6A19};
const reading_md nanori_md0x5414a9f6 = {1, NULL, na_kanji0x5414a9f6};
const kanji_md * const na_kanji0x2ffd6cea[] = {&kanji_md5360};
const reading_md nanori_md0x2ffd6cea = {1, NULL, na_kanji0x2ffd6cea};
const kanji_md * const na_kanji0x7c31ad7[] = {&kanji_md91C8};
const reading_md nanori_md0x7c31ad7 = {1, NULL, na_kanji0x7c31ad7};
const kanji_md * const na_kanji0x55f213b4[] = {&kanji_md5C0F};
const reading_md nanori_md0x55f213b4 = {1, NULL, na_kanji0x55f213b4};
const kanji_md * const na_kanji0xe116dbd4[] = {&kanji_md7A4D};
const reading_md nanori_md0xe116dbd4 = {1, NULL, na_kanji0xe116dbd4};
const kanji_md * const na_kanji0xaf07149b[] = {&kanji_md5468, &kanji_md79C0};
const reading_md nanori_md0xaf07149b = {2, NULL, na_kanji0xaf07149b};
const kanji_md * const na_kanji0x67b6d335[] = {&kanji_md7FBD, &kanji_md6607};
const reading_md nanori_md0x67b6d335 = {2, NULL, na_kanji0x67b6d335};
const kanji_md * const na_kanji0xf921ff09[] = {&kanji_md677E};
const reading_md nanori_md0xf921ff09 = {1, NULL, na_kanji0xf921ff09};
const kanji_md * const na_kanji0x8aab4a95[] = {&kanji_md79C0};
const reading_md nanori_md0x8aab4a95 = {1, NULL, na_kanji0x8aab4a95};
const kanji_md * const na_kanji0xfe33a294[] = {&kanji_md5F8C, &kanji_md77E5};
const reading_md nanori_md0xfe33a294 = {2, NULL, na_kanji0xfe33a294};
const kanji_md * const na_kanji0x70a9d129[] = {&kanji_md77E5};
const reading_md nanori_md0x70a9d129 = {1, NULL, na_kanji0x70a9d129};
const kanji_md * const na_kanji0xedbe341d[] = {&kanji_md6C88, &kanji_md666E, &kanji_md93AE, &kanji_md5B8D};
const reading_md nanori_md0xedbe341d = {4, NULL, na_kanji0xedbe341d};
const kanji_md * const na_kanji0x2814d70c[] = {&kanji_md4EBA, &kanji_md51FA, &kanji_md9053, &kanji_md826F, &kanji_md9045, &kanji_md5024, &kanji_md6A39, &kanji_md5BFF, &kanji_md4EC1, &kanji_md82BD, &kanji_md667A, &kanji_md751A, &kanji_md51B6, &kanji_md8305, &kanji_md58FD};
const reading_md nanori_md0x2814d70c = {15, NULL, na_kanji0x2814d70c};
const kanji_md * const na_kanji0x646b778d[] = {&kanji_md529B};
const reading_md nanori_md0x646b778d = {1, NULL, na_kanji0x646b778d};
const kanji_md * const na_kanji0xeff64f8e[] = {&kanji_md5883, &kanji_md55B0};
const reading_md nanori_md0xeff64f8e = {2, NULL, na_kanji0xeff64f8e};
const kanji_md * const na_kanji0x8101a345[] = {&kanji_md7B39};
const reading_md nanori_md0x8101a345 = {1, NULL, na_kanji0x8101a345};
const kanji_md * const na_kanji0x170af2f2[] = {&kanji_md5360};
const reading_md nanori_md0x170af2f2 = {1, NULL, na_kanji0x170af2f2};
const kanji_md * const na_kanji0x7ad0c003[] = {&kanji_md5EFB};
const reading_md nanori_md0x7ad0c003 = {1, NULL, na_kanji0x7ad0c003};
const kanji_md * const na_kanji0x230ba537[] = {&kanji_md6570, &kanji_md4F4F};
const reading_md nanori_md0x230ba537 = {2, NULL, na_kanji0x230ba537};
const kanji_md * const na_kanji0x54bc6746[] = {&kanji_md5BFF};
const reading_md nanori_md0x54bc6746 = {1, NULL, na_kanji0x54bc6746};
const kanji_md * const na_kanji0x23a16dad[] = {&kanji_md7D62};
const reading_md nanori_md0x23a16dad = {1, NULL, na_kanji0x23a16dad};
const kanji_md * const na_kanji0x3fa5409f[] = {&kanji_md53D7};
const reading_md nanori_md0x3fa5409f = {1, NULL, na_kanji0x3fa5409f};
const kanji_md * const na_kanji0x9463552[] = {&kanji_md9AD8};
const reading_md nanori_md0x9463552 = {1, NULL, na_kanji0x9463552};
const kanji_md * const na_kanji0xb4457c43[] = {&kanji_md751F, &kanji_md9580};
const reading_md nanori_md0xb4457c43 = {2, NULL, na_kanji0xb4457c43};
const kanji_md * const na_kanji0xca790e59[] = {&kanji_md5FD7, &kanji_md73CD, &kanji_md93AE};
const reading_md nanori_md0xca790e59 = {3, NULL, na_kanji0xca790e59};
const kanji_md * const na_kanji0xdd29f651[] = {&kanji_md65E5, &kanji_md6708, &kanji_md4EE3, &kanji_md9996, &kanji_md89D2, &kanji_md5468, &kanji_md5BF8, &kanji_md59B9, &kanji_md9676, &kanji_md73E0, &kanji_md6731, &kanji_md5D07, &kanji_md9DF2, &kanji_md83C5, &kanji_md6816};
const reading_md nanori_md0xdd29f651 = {15, NULL, na_kanji0xdd29f651};
const kanji_md * const na_kanji0xde1f74a1[] = {&kanji_md6C37};
const reading_md nanori_md0xde1f74a1 = {1, NULL, na_kanji0xde1f74a1};
const kanji_md * const na_kanji0x21da61ae[] = {&kanji_md5C45, &kanji_md5B63};
const reading_md nanori_md0x21da61ae = {2, NULL, na_kanji0x21da61ae};
const kanji_md * const na_kanji0xa7fc0eaf[] = {&kanji_md7BA1, &kanji_md6E05, &kanji_md83C5};
const reading_md nanori_md0xa7fc0eaf = {3, NULL, na_kanji0xa7fc0eaf};
const kanji_md * const na_kanji0xd0a9755[] = {&kanji_md6B21};
const reading_md nanori_md0xd0a9755 = {1, NULL, na_kanji0xd0a9755};
const kanji_md * const na_kanji0x1fa42163[] = {&kanji_md751F};
const reading_md nanori_md0x1fa42163 = {1, NULL, na_kanji0x1fa42163};
const kanji_md * const na_kanji0x8176e708[] = {&kanji_md5BBF, &kanji_md53E5, &kanji_md57CE, &kanji_md6DD1};
const reading_md nanori_md0x8176e708 = {4, NULL, na_kanji0x8176e708};
const kanji_md * const na_kanji0x547e64db[] = {&kanji_md76F4, &kanji_md5091};
const reading_md nanori_md0x547e64db = {2, NULL, na_kanji0x547e64db};
const kanji_md * const na_kanji0xaa368bbb[] = {&kanji_md82F1, &kanji_md8C6A, &kanji_md5353, &kanji_md4FCA, &kanji_md9A4D};
const reading_md nanori_md0xaa368bbb = {5, NULL, na_kanji0xaa368bbb};
const kanji_md * const na_kanji0x89991c60[] = {&kanji_md76F8, &kanji_md53F3, &kanji_md4ECB, &kanji_md627F, &kanji_md8CC7, &kanji_md88D5, &kanji_md5178, &kanji_md4F50, &kanji_md8CC3, &kanji_md660C, &kanji_md54C9, &kanji_md7950, &kanji_md8F14, &kanji_md4EAE, &kanji_md4E1E, &kanji_md865E, &kanji_md4F51, &kanji_md5141, &kanji_md752B, &kanji_md5F3C};
const reading_md nanori_md0x89991c60 = {20, NULL, na_kanji0x89991c60};
const kanji_md * const na_kanji0xa410423a[] = {&kanji_md83C5};
const reading_md nanori_md0xa410423a = {1, NULL, na_kanji0xa410423a};
const char *na_olist0x4fc7399_00[] = {""};
const okuri_md na_okuri_md0x4fc7399_00 = {1, NULL, na_olist0x4fc7399_00};
const char *na_olist0x4fc7399_01[] = {"\xe3\x82\x80"};
const okuri_md na_okuri_md0x4fc7399_01 = {1, NULL, na_olist0x4fc7399_01};
const okuri_md * const na_okuri0x4fc7399[] = {&na_okuri_md0x4fc7399_00, &na_okuri_md0x4fc7399_01};
const kanji_md * const na_kanji0x4fc7399[] = {&kanji_md6F84, &kanji_md9081};
const reading_md nanori_md0x4fc7399 = {2, na_okuri0x4fc7399, na_kanji0x4fc7399};
const kanji_md * const na_kanji0x21850685[] = {&kanji_md664B, &kanji_md8FEA};
const reading_md nanori_md0x21850685 = {2, NULL, na_kanji0x21850685};
const kanji_md * const na_kanji0xf39a14d6[] = {&kanji_md5C06, &kanji_md594F, &kanji_md664B, &kanji_md4F91, &kanji_md8FEA};
const reading_md nanori_md0xf39a14d6 = {5, NULL, na_kanji0xf39a14d6};
const kanji_md * const na_kanji0x81447462[] = {&kanji_md7D17, &kanji_md9438};
const reading_md nanori_md0x81447462 = {2, NULL, na_kanji0x81447462};
const kanji_md * const na_kanji0xf6a50e44[] = {&kanji_md51FA, &kanji_md5BFF};
const reading_md nanori_md0xf6a50e44 = {2, NULL, na_kanji0xf6a50e44};
const kanji_md * const na_kanji0x54978467[] = {&kanji_md51FA};
const reading_md nanori_md0x54978467 = {1, NULL, na_kanji0x54978467};
const kanji_md * const na_kanji0x9e6a5a7a[] = {&kanji_md662F, &kanji_md6DF3};
const reading_md nanori_md0x9e6a5a7a = {2, NULL, na_kanji0x9e6a5a7a};
const kanji_md * const na_kanji0x45dc8255[] = {&kanji_md5F37};
const reading_md nanori_md0x45dc8255 = {1, NULL, na_kanji0x45dc8255};
const kanji_md * const na_kanji0x8f04aa17[] = {&kanji_md6625, &kanji_md58A8};
const reading_md nanori_md0x8f04aa17 = {2, NULL, na_kanji0x8f04aa17};
const kanji_md * const na_kanji0xc8a30976[] = {&kanji_md898F};
const reading_md nanori_md0xc8a30976 = {1, NULL, na_kanji0xc8a30976};
const kanji_md * const na_kanji0xc87f1f3c[] = {&kanji_md4F4F, &kanji_md89D2, &kanji_md7D14, &kanji_md6E05, &kanji_md6F84, &kanji_md5BFF, &kanji_md6816};
const reading_md nanori_md0xc87f1f3c = {7, NULL, na_kanji0xc87f1f3c};
const kanji_md * const na_kanji0xed654924[] = {&kanji_md6E08};
const reading_md nanori_md0xed654924 = {1, NULL, na_kanji0xed654924};
const kanji_md * const na_kanji0xe28f5cf3[] = {&kanji_md647A, &kanji_md99FF};
const reading_md nanori_md0xe28f5cf3 = {2, NULL, na_kanji0xe28f5cf3};
const kanji_md * const na_kanji0x3dbac09d[] = {&kanji_md96C6, &kanji_md4E3B, &kanji_md90FD, &kanji_md5C0B, &kanji_md6D25, &kanji_md9234, &kanji_md9DB4, &kanji_md745E};
const reading_md nanori_md0x3dbac09d = {8, NULL, na_kanji0x3dbac09d};
const kanji_md * const na_kanji0xe5c0ba99[] = {&kanji_md6CC9};
const reading_md nanori_md0xe5c0ba99 = {1, NULL, na_kanji0xe5c0ba99};
const kanji_md * const na_kanji0x909cfacd[] = {&kanji_md585A};
const reading_md nanori_md0x909cfacd = {1, NULL, na_kanji0x909cfacd};
const kanji_md * const na_kanji0xd8bd05ed[] = {&kanji_md6708, &kanji_md9644};
const reading_md nanori_md0xd8bd05ed = {2, NULL, na_kanji0xd8bd05ed};
const kanji_md * const na_kanji0xf7a448e3[] = {&kanji_md9020};
const reading_md nanori_md0xf7a448e3 = {1, NULL, na_kanji0xf7a448e3};
const kanji_md * const na_kanji0x5b331818[] = {&kanji_md91CE};
const reading_md nanori_md0x5b331818 = {1, NULL, na_kanji0x5b331818};
const kanji_md * const na_kanji0x8ed30164[] = {&kanji_md7DCF, &kanji_md7E3D};
const reading_md nanori_md0x8ed30164 = {2, NULL, na_kanji0x8ed30164};
const kanji_md * const na_kanji0x82f28311[] = {&kanji_md7DB2};
const reading_md nanori_md0x82f28311 = {1, NULL, na_kanji0x82f28311};
const kanji_md * const na_kanji0x4d9915ee[] = {&kanji_md59BB, &kanji_md7026};
const reading_md nanori_md0x4d9915ee = {2, NULL, na_kanji0x4d9915ee};
const kanji_md * const na_kanji0x1531807b[] = {&kanji_md6C34, &kanji_md89D2, &kanji_md7A4D, &kanji_md6CC9, &kanji_md66C7, &kanji_md68F2};
const reading_md nanori_md0x1531807b = {6, NULL, na_kanji0x1531807b};
const kanji_md * const na_kanji0xefd13508[] = {&kanji_md8A70};
const reading_md nanori_md0xefd13508 = {1, NULL, na_kanji0xefd13508};
const kanji_md * const na_kanji0x2cffc806[] = {&kanji_md96F2};
const reading_md nanori_md0x2cffc806 = {1, NULL, na_kanji0x2cffc806};
const kanji_md * const na_kanji0x4ff85c4e[] = {&kanji_md9762};
const reading_md nanori_md0x4ff85c4e = {1, NULL, na_kanji0x4ff85c4e};
const kanji_md * const na_kanji0xb4390ee0[] = {&kanji_md647A};
const reading_md nanori_md0xb4390ee0 = {1, NULL, na_kanji0xb4390ee0};
const kanji_md * const na_kanji0x2603928d[] = {&kanji_md9023};
const reading_md nanori_md0x2603928d = {1, NULL, na_kanji0x2603928d};
const kanji_md * const na_kanji0x615493c2[] = {&kanji_md6240, &kanji_md52E2, &kanji_md6226, &kanji_md8FEB, &kanji_md5144, &kanji_md6E05, &kanji_md8C37, &kanji_md59B9, &kanji_md8056, &kanji_md65CB, &kanji_md7A32};
const reading_md nanori_md0x615493c2 = {11, NULL, na_kanji0x615493c2};
const kanji_md * const na_kanji0xf7c0891c[] = {&kanji_md702C, &kanji_md82B9};
const reading_md nanori_md0xf7c0891c = {2, NULL, na_kanji0xf7c0891c};
const kanji_md * const na_kanji0x37406775[] = {&kanji_md6298, &kanji_md78B5};
const reading_md nanori_md0x37406775 = {2, NULL, na_kanji0x37406775};
const kanji_md * const na_kanji0x5ed0ebd7[] = {&kanji_md8FEB};
const reading_md nanori_md0x5ed0ebd7 = {1, NULL, na_kanji0x5ed0ebd7};
const kanji_md * const na_kanji0x5787a94c[] = {&kanji_md96EA, &kanji_md702C, &kanji_md6442};
const reading_md nanori_md0x5787a94c = {3, NULL, na_kanji0x5787a94c};
const kanji_md * const na_kanji0x89ff5cec[] = {&kanji_md77F3};
const reading_md nanori_md0x89ff5cec = {1, NULL, na_kanji0x89ff5cec};
const kanji_md * const na_kanji0x93a70c06[] = {&kanji_md616E, &kanji_md81B3};
const reading_md nanori_md0x93a70c06 = {2, NULL, na_kanji0x93a70c06};
const kanji_md * const na_kanji0x9cb7d00e[] = {&kanji_md57CE, &kanji_md6CC9};
const reading_md nanori_md0x9cb7d00e = {2, NULL, na_kanji0x9cb7d00e};
const kanji_md * const na_kanji0x7e1b7b07[] = {&kanji_md6CC9};
const reading_md nanori_md0x7e1b7b07 = {1, NULL, na_kanji0x7e1b7b07};
const kanji_md * const na_kanji0x6efded50[] = {&kanji_md751F, &kanji_md5341, &kanji_md65E9, &kanji_md5DE6, &kanji_md8349, &kanji_md5B97, &kanji_md8358, &kanji_md5F81, &kanji_md78EF, &kanji_md60E3};
const reading_md nanori_md0x6efded50 = {10, NULL, na_kanji0x6efded50};
const kanji_md * const na_kanji0xefe97936[] = {&kanji_md8972, &kanji_md526F};
const reading_md nanori_md0xefe97936 = {2, NULL, na_kanji0xefe97936};
const kanji_md * const na_kanji0xca67751a[] = {&kanji_md751F, &kanji_md4E09, &kanji_md5341, &kanji_md7C9F};
const reading_md nanori_md0xca67751a = {4, NULL, na_kanji0xca67751a};
const kanji_md * const na_kanji0x89bb4ffc[] = {&kanji_md6DFB, &kanji_md526F};
const reading_md nanori_md0x89bb4ffc = {2, NULL, na_kanji0x89bb4ffc};
const kanji_md * const na_kanji0x829e1e0d[] = {&kanji_md5B97};
const reading_md nanori_md0x829e1e0d = {1, NULL, na_kanji0x829e1e0d};
const kanji_md * const na_kanji0xc52d11d7[] = {&kanji_md5F7C};
const reading_md nanori_md0xc52d11d7 = {1, NULL, na_kanji0xc52d11d7};
const kanji_md * const na_kanji0x16a7466[] = {&kanji_md4ED9};
const reading_md nanori_md0x16a7466 = {1, NULL, na_kanji0x16a7466};
const kanji_md * const na_kanji0xda2f7779[] = {&kanji_md67D3};
const reading_md nanori_md0xda2f7779 = {1, NULL, na_kanji0xda2f7779};
const kanji_md * const na_kanji0xb475ca46[] = {&kanji_md53CD};
const reading_md nanori_md0xb475ca46 = {1, NULL, na_kanji0xb475ca46};
const kanji_md * const na_kanji0x7073919[] = {&kanji_md6210};
const reading_md nanori_md0x7073919 = {1, NULL, na_kanji0x7073919};
const kanji_md * const na_kanji0x57852da[] = {&kanji_md4E09, &kanji_md9808};
const reading_md nanori_md0x57852da = {2, NULL, na_kanji0x57852da};
const kanji_md * const na_kanji0x2fc854b8[] = {&kanji_md6DFB};
const reading_md nanori_md0x2fc854b8 = {1, NULL, na_kanji0x2fc854b8};
const kanji_md * const na_kanji0x8736aa17[] = {&kanji_md85E4};
const reading_md nanori_md0x8736aa17 = {1, NULL, na_kanji0x8736aa17};
const kanji_md * const na_kanji0x1f1e3d42[] = {&kanji_md4F4D};
const reading_md nanori_md0x1f1e3d42 = {1, NULL, na_kanji0x1f1e3d42};
const kanji_md * const na_kanji0x2601e294[] = {&kanji_md5712, &kanji_md8597};
const reading_md nanori_md0x2601e294 = {2, NULL, na_kanji0x2601e294};
const kanji_md * const na_kanji0xb6bd4e92[] = {&kanji_md5D50};
const reading_md nanori_md0xb6bd4e92 = {1, NULL, na_kanji0xb6bd4e92};
const kanji_md * const na_kanji0x352aeb03[] = {&kanji_md5927, &kanji_md9AD8, &kanji_md5411, &kanji_md5973, &kanji_md5C4B, &kanji_md5929, &kanji_md697D, &kanji_md53CD, &kanji_md539F, &kanji_md7A2E, &kanji_md99AC, &kanji_md6D77, &kanji_md4E39, &kanji_md6CF0};
const reading_md nanori_md0x352aeb03 = {14, NULL, na_kanji0x352aeb03};
const kanji_md * const na_kanji0xcd97382f[] = {&kanji_md5F53, &kanji_md70AC, &kanji_md79E6};
const reading_md nanori_md0xcd97382f = {3, NULL, na_kanji0xcd97382f};
const kanji_md * const na_kanji0xdb446c4c[] = {&kanji_md5E73};
const reading_md nanori_md0xdb446c4c = {1, NULL, na_kanji0xdb446c4c};
const kanji_md * const na_kanji0xf3b6770c[] = {&kanji_md6210, &kanji_md8010, &kanji_md7D17};
const reading_md nanori_md0xf3b6770c = {3, NULL, na_kanji0xf3b6770c};
const kanji_md * const na_kanji0xda710b80[] = {&kanji_md8003, &kanji_md597D, &kanji_md5B66, &kanji_md80FD, &kanji_md5FDC, &kanji_md592A, &kanji_md516C, &kanji_md767B, &kanji_md8CB4, &kanji_md656C, &kanji_md5C06, &kanji_md5B85, &kanji_md6319, &kanji_md5C0A, &kanji_md5EF6, &kanji_md4EAC, &kanji_md8056, &kanji_md5C31, &kanji_md8A89, &kanji_md8CE2, &kanji_md5353, &kanji_md5B97, &kanji_md5B87, &kanji_md9298, &kanji_md7AF9, &kanji_md9867, &kanji_md81E3, &kanji_md6602, &kanji_md9686, &kanji_md5D07, &kanji_md5C1A, &kanji_md525B, &kanji_md5EF7, &kanji_md5B5D, &kanji_md5B9C, &kanji_md4EAB, &kanji_md5CB3, &kanji_md5CFB, &kanji_md5D69, &kanji_md55AC, &kanji_md7422, &kanji_md5C2D, &kanji_md965F, &kanji_md5BF6, &kanji_md595D, &kanji_md8EC5};
const reading_md nanori_md0xda710b80 = {46, NULL, na_kanji0xda710b80};
const kanji_md * const na_kanji0xf756c921[] = {&kanji_md5927, &kanji_md9577, &kanji_md5929, &kanji_md7BC0, &kanji_md8CB4, &kanji_md656C, &kanji_md5F8B, &kanji_md5E79, &kanji_md5353, &kanji_md4E18, &kanji_md6602, &kanji_md9686, &kanji_md5D07, &kanji_md5C1A, &kanji_md5B5D, &kanji_md5C90, &kanji_md4EAB, &kanji_md5CFB, &kanji_md5D69, &kanji_md55AC, &kanji_md5DCD, &kanji_md7690, &kanji_md5C2D, &kanji_md655E, &kanji_md9ADE};
const reading_md nanori_md0xf756c921 = {25, NULL, na_kanji0xf756c921};
const kanji_md * const na_kanji0xaf55eb72[] = {&kanji_md5D07};
const reading_md nanori_md0xaf55eb72 = {1, NULL, na_kanji0xaf55eb72};
const kanji_md * const na_kanji0xb7236af9[] = {&kanji_md7528};
const reading_md nanori_md0xb7236af9 = {1, NULL, na_kanji0xb7236af9};
const kanji_md * const na_kanji0xf2bd7835[] = {&kanji_md5DBD};
const reading_md nanori_md0xf2bd7835 = {1, NULL, na_kanji0xf2bd7835};
const kanji_md * const na_kanji0xdc484754[] = {&kanji_md8A6B};
const reading_md nanori_md0xdc484754 = {1, NULL, na_kanji0xdc484754};
const kanji_md * const na_kanji0xf1e64e2d[] = {&kanji_md5DE7};
const reading_md nanori_md0xf1e64e2d = {1, NULL, na_kanji0xf1e64e2d};
const kanji_md * const na_kanji0x2a46a6b6[] = {&kanji_md5168, &kanji_md9577, &kanji_md548C, &kanji_md5EFA, &kanji_md5A01, &kanji_md5065, &kanji_md656C, &kanji_md5B85, &kanji_md5C0A, &kanji_md731B, &kanji_md8C6A, &kanji_md96C4, &kanji_md8A89, &kanji_md864E, &kanji_md5091, &kanji_md525B, &kanji_md6BC5, &kanji_md7A40, &kanji_md5D69, &kanji_md5B5F, &kanji_md5F6A, &kanji_md8D73, &kanji_md658C};
const reading_md nanori_md0x2a46a6b6 = {23, NULL, na_kanji0x2a46a6b6};
const kanji_md * const na_kanji0x847f0299[] = {&kanji_md5F6A};
const reading_md nanori_md0x847f0299 = {1, NULL, na_kanji0x847f0299};
const kanji_md * const na_kanji0x52324f0a[] = {&kanji_md5A01, &kanji_md5065, &kanji_md6B66, &kanji_md731B, &kanji_md8C6A, &kanji_md525B, &kanji_md6BC5, &kanji_md5B5F, &kanji_md5F6A, &kanji_md8D73, &kanji_md6D38, &kanji_md58EF};
const reading_md nanori_md0x52324f0a = {12, NULL, na_kanji0x52324f0a};
const kanji_md * const na_kanji0x13466caa[] = {&kanji_md731B};
const reading_md nanori_md0x13466caa = {1, NULL, na_kanji0x13466caa};
const kanji_md * const na_kanji0xe063f686[] = {&kanji_md6B66, &kanji_md5CB3};
const reading_md nanori_md0xe063f686 = {2, NULL, na_kanji0xe063f686};
const kanji_md * const na_kanji0x7f3fd1b4[] = {&kanji_md4F46};
const reading_md nanori_md0x7f3fd1b4 = {1, NULL, na_kanji0x7f3fd1b4};
const kanji_md * const na_kanji0x2c56de5a[] = {&kanji_md7950, &kanji_md8F14, &kanji_md4EAE, &kanji_md4F51, &kanji_md5F3C};
const reading_md nanori_md0x2c56de5a = {5, NULL, na_kanji0x2c56de5a};
const kanji_md * const na_kanji0x23ea40a7[] = {&kanji_md9DB4};
const reading_md nanori_md0x23ea40a7 = {1, NULL, na_kanji0x23ea40a7};
const kanji_md * const na_kanji0xcdb3152[] = {&kanji_md5FE0};
const reading_md nanori_md0xcdb3152 = {1, NULL, na_kanji0xcdb3152};
const kanji_md * const na_kanji0xf5bb77a[] = {&kanji_md6E5B};
const reading_md nanori_md0xf5bb77a = {1, NULL, na_kanji0xf5bb77a};
const kanji_md * const na_kanji0x9811aa64[] = {&kanji_md6E5B};
const reading_md nanori_md0x9811aa64 = {1, NULL, na_kanji0x9811aa64};
const kanji_md * const na_kanji0xeba6aeb1[] = {&kanji_md946A};
const reading_md nanori_md0xeba6aeb1 = {1, NULL, na_kanji0xeba6aeb1};
const kanji_md * const na_kanji0x82565e74[] = {&kanji_md7406, &kanji_md4E09, &kanji_md5185, &kanji_md771F, &kanji_md5FE0, &kanji_md653F, &kanji_md8056, &kanji_md4F0A, &kanji_md6589, &kanji_md7763, &kanji_md658E, &kanji_md5F81, &kanji_md7965, &kanji_md5BB0, &kanji_md60DF, &kanji_md5321};
const reading_md nanori_md0x82565e74 = {16, NULL, na_kanji0x82565e74};
const kanji_md * const na_kanji0x13ca140d[] = {&kanji_md7406, &kanji_md6B63, &kanji_md771F, &kanji_md7AEF, &kanji_md516C, &kanji_md7FA9, &kanji_md898F, &kanji_md5FE0, &kanji_md96C5, &kanji_md7763, &kanji_md662F, &kanji_md8C9E, &kanji_md77E9, &kanji_md8087, &kanji_md5321, &kanji_md798E, &kanji_md4F83};
const reading_md nanori_md0x13ca140d = {17, NULL, na_kanji0x13ca140d};
const kanji_md * const na_kanji0x629d68f1[] = {&kanji_md7D00};
const reading_md nanori_md0x629d68f1 = {1, NULL, na_kanji0x629d68f1};
const kanji_md * const na_kanji0xd9fef6dc[] = {&kanji_md65E5, &kanji_md7ACB, &kanji_md9928, &kanji_md57CE, &kanji_md9678, &kanji_md6714, &kanji_md8218};
const reading_md nanori_md0xd9fef6dc = {7, NULL, na_kanji0xd9fef6dc};
const kanji_md * const na_kanji0x5749bcb0[] = {&kanji_md6A39};
const reading_md nanori_md0x5749bcb0 = {1, NULL, na_kanji0x5749bcb0};
const kanji_md * const na_kanji0xb0dc34df[] = {&kanji_md7ACB};
const reading_md nanori_md0xb0dc34df = {1, NULL, na_kanji0xb0dc34df};
const kanji_md * const na_kanji0x52a8edc1[] = {&kanji_md7ACB, &kanji_md5EFA, &kanji_md6A39, &kanji_md8526};
const reading_md nanori_md0x52a8edc1 = {4, NULL, na_kanji0x52a8edc1};
const kanji_md * const na_kanji0x1826a5b0[] = {&kanji_md6A39};
const reading_md nanori_md0x1826a5b0 = {1, NULL, na_kanji0x1826a5b0};
const kanji_md * const na_kanji0xb16f76f6[] = {&kanji_md5EFA, &kanji_md5E2F, &kanji_md5065, &kanji_md8CE2};
const reading_md nanori_md0xb16f76f6 = {4, NULL, na_kanji0xb16f76f6};
const kanji_md * const na_kanji0xb93a836b[] = {&kanji_md7A19};
const reading_md nanori_md0xb93a836b = {1, NULL, na_kanji0xb93a836b};
const kanji_md * const na_kanji0x4413a12[] = {&kanji_md62B1, &kanji_md7159, &kanji_md628A};
const reading_md nanori_md0x4413a12 = {3, NULL, na_kanji0x4413a12};
const kanji_md * const na_kanji0xb49864a2[] = {&kanji_md74B0, &kanji_md78A7, &kanji_md745E, &kanji_md572D, &kanji_md73B2, &kanji_md7396};
const reading_md nanori_md0xb49864a2 = {6, NULL, na_kanji0xb49864a2};
const kanji_md * const na_kanji0xfffdc51f[] = {&kanji_md74B0};
const reading_md nanori_md0xfffdc51f = {1, NULL, na_kanji0xfffdc51f};
const kanji_md * const na_kanji0x25b9fe20[] = {&kanji_md4E39};
const reading_md nanori_md0x25b9fe20 = {1, NULL, na_kanji0x25b9fe20};
const kanji_md * const na_kanji0x264be6a4[] = {&kanji_md7DAD};
const reading_md nanori_md0x264be6a4 = {1, NULL, na_kanji0x264be6a4};
const kanji_md * const na_kanji0xe2e407f9[] = {&kanji_md5E73};
const reading_md nanori_md0xe2e407f9 = {1, NULL, na_kanji0xe2e407f9};
const kanji_md * const na_kanji0xcc60210d[] = {&kanji_md8DB3};
const reading_md nanori_md0xcc60210d = {1, NULL, na_kanji0xcc60210d};
const kanji_md * const na_kanji0x79538771[] = {&kanji_md6E21, &kanji_md8C37};
const reading_md nanori_md0x79538771 = {2, NULL, na_kanji0x79538771};
const kanji_md * const na_kanji0x99966c88[] = {&kanji_md5584, &kanji_md5782};
const reading_md nanori_md0x99966c88 = {2, NULL, na_kanji0x99966c88};
const kanji_md * const na_kanji0xc1f342b2[] = {&kanji_md7530, &kanji_md8C37, &kanji_md5510};
const reading_md nanori_md0xc1f342b2 = {3, NULL, na_kanji0xc1f342b2};
const kanji_md * const na_kanji0x276ebecf[] = {&kanji_md4F0A};
const reading_md nanori_md0x276ebecf = {1, NULL, na_kanji0x276ebecf};
const kanji_md * const na_kanji0xbc6d7571[] = {&kanji_md68AF};
const reading_md nanori_md0xbc6d7571 = {1, NULL, na_kanji0xbc6d7571};
const kanji_md * const na_kanji0x93c16d55[] = {&kanji_md7009};
const reading_md nanori_md0x93c16d55 = {1, NULL, na_kanji0x93c16d55};
const kanji_md * const na_kanji0x9df0417[] = {&kanji_md6E20};
const reading_md nanori_md0x9df0417 = {1, NULL, na_kanji0x9df0417};
const kanji_md * const na_kanji0xb8cc6b38[] = {&kanji_md97C3};
const reading_md nanori_md0xb8cc6b38 = {1, NULL, na_kanji0xb8cc6b38};
const kanji_md * const na_kanji0x3c977430[] = {&kanji_md7ACB};
const reading_md nanori_md0x3c977430 = {1, NULL, na_kanji0x3c977430};
const kanji_md * const na_kanji0x5d6d1a2a[] = {&kanji_md7058};
const reading_md nanori_md0x5d6d1a2a = {1, NULL, na_kanji0x5d6d1a2a};
const kanji_md * const na_kanji0x3172d0af[] = {&kanji_md795E};
const reading_md nanori_md0x3172d0af = {1, NULL, na_kanji0x3172d0af};
const kanji_md * const na_kanji0xe564ef13[] = {&kanji_md5782};
const reading_md nanori_md0xe564ef13 = {1, NULL, na_kanji0xe564ef13};
const kanji_md * const na_kanji0x2deb0433[] = {&kanji_md7389};
const reading_md nanori_md0x2deb0433 = {1, NULL, na_kanji0x2deb0433};
const kanji_md * const na_kanji0x3c2569b2[] = {&kanji_md5185, &kanji_md5341, &kanji_md5F62, &kanji_md4E94, &kanji_md548C, &kanji_md90FD, &kanji_md5E02, &kanji_md5200, &kanji_md5203, &kanji_md76E4, &kanji_md6D25, &kanji_md8305, &kanji_md771E};
const reading_md nanori_md0x3c2569b2 = {13, NULL, na_kanji0x3c2569b2};
const kanji_md * const na_kanji0xdf234b74[] = {&kanji_md5C0F};
const reading_md nanori_md0xdf234b74 = {1, NULL, na_kanji0xdf234b74};
const kanji_md * const na_kanji0x753ab1d1[] = {&kanji_md9593, &kanji_md5143, &kanji_md89AA, &kanji_md611B, &kanji_md671D, &kanji_md5468, &kanji_md7FA9, &kanji_md96A3, &kanji_md53F2, &kanji_md592E, &kanji_md614E, &kanji_md93AE, &kanji_md6148, &kanji_md7766, &kanji_md54C9, &kanji_md5CFB, &kanji_md723E, &kanji_md5141, &kanji_md5C39, &kanji_md608C};
const reading_md nanori_md0x753ab1d1 = {20, NULL, na_kanji0x753ab1d1};
const kanji_md * const na_kanji0xba0af2b5[] = {&kanji_md8FE9};
const reading_md nanori_md0xba0af2b5 = {1, NULL, na_kanji0xba0af2b5};
const kanji_md * const na_kanji0xa3326099[] = {&kanji_md5152};
const reading_md nanori_md0xa3326099 = {1, NULL, na_kanji0xa3326099};
const kanji_md * const na_kanji0x371091a9[] = {&kanji_md79E9};
const reading_md nanori_md0x371091a9 = {1, NULL, na_kanji0x371091a9};
const kanji_md * const na_kanji0x5cef7611[] = {&kanji_md79E9};
const reading_md nanori_md0x5cef7611 = {1, NULL, na_kanji0x5cef7611};
const kanji_md * const na_kanji0xd7195ca0[] = {&kanji_md5F79};
const reading_md nanori_md0xd7195ca0 = {1, NULL, na_kanji0xd7195ca0};
const kanji_md * const na_kanji0x957823fa[] = {&kanji_md982D};
const reading_md nanori_md0x957823fa = {1, NULL, na_kanji0x957823fa};
const kanji_md * const na_kanji0x7b1f77d7[] = {&kanji_md8336};
const reading_md nanori_md0x7b1f77d7 = {1, NULL, na_kanji0x7b1f77d7};
const kanji_md * const na_kanji0xe516a387[] = {&kanji_md4EF2};
const reading_md nanori_md0xe516a387 = {1, NULL, na_kanji0xe516a387};
const kanji_md * const na_kanji0x71fb5c37[] = {&kanji_md654F, &kanji_md6A17};
const reading_md nanori_md0x71fb5c37 = {2, NULL, na_kanji0x71fb5c37};
const kanji_md * const na_kanji0x5f66c450[] = {&kanji_md751F, &kanji_md6563};
const reading_md nanori_md0x5f66c450 = {2, NULL, na_kanji0x5f66c450};
const kanji_md * const na_kanji0x37f5c7f[] = {&kanji_md6E05};
const reading_md nanori_md0x37f5c7f = {1, NULL, na_kanji0x37f5c7f};
const kanji_md * const na_kanji0x95de7e03[] = {&kanji_md6CBB};
const reading_md nanori_md0x95de7e03 = {1, NULL, na_kanji0x95de7e03};
const kanji_md * const na_kanji0x27191473[] = {&kanji_md6C34, &kanji_md56DB, &kanji_md5965, &kanji_md53F8, &kanji_md5FB9, &kanji_md585A, &kanji_md9DB4, &kanji_md62D3, &kanji_md67D8, &kanji_md844E};
const reading_md nanori_md0x27191473 = {10, NULL, na_kanji0x27191473};
const kanji_md * const na_kanji0x422d0df2[] = {&kanji_md7ACB, &kanji_md7BC9};
const reading_md nanori_md0x422d0df2 = {2, NULL, na_kanji0x422d0df2};
const kanji_md * const na_kanji0xdbf637ed[] = {&kanji_md5BB6, &kanji_md53F8};
const reading_md nanori_md0xdbf637ed = {2, NULL, na_kanji0xdbf637ed};
const kanji_md * const na_kanji0xdf78df6b[] = {&kanji_md5E2B, &kanji_md52D9, &kanji_md53F8, &kanji_md55E3};
const reading_md nanori_md0xdf78df6b = {4, NULL, na_kanji0xdf78df6b};
const kanji_md * const na_kanji0x4735d335[] = {&kanji_md5973, &kanji_md5C5E, &kanji_md7BC9};
const reading_md nanori_md0x4735d335 = {3, NULL, na_kanji0x4735d335};
const kanji_md * const na_kanji0x570dc3f7[] = {&kanji_md4E8C, &kanji_md8ABF, &kanji_md65CF, &kanji_md627F, &kanji_md4E9C, &kanji_md55E3, &kanji_md80E4};
const reading_md nanori_md0x570dc3f7 = {7, NULL, na_kanji0x570dc3f7};
const kanji_md * const na_kanji0x3a541233[] = {&kanji_md571F, &kanji_md7BC9, &kanji_md7B51};
const reading_md nanori_md0x3a541233 = {3, NULL, na_kanji0x3a541233};
const kanji_md * const na_kanji0x6955bd54[] = {&kanji_md4E8C, &kanji_md6B21, &kanji_md7D9A, &kanji_md627F, &kanji_md7D39, &kanji_md5C0B, &kanji_md5E8F, &kanji_md7DAD, &kanji_md4E9C, &kanji_md55E3, &kanji_md80E4, &kanji_md980C, &kanji_md97F6, &kanji_md7E8C};
const reading_md nanori_md0x6955bd54 = {14, NULL, na_kanji0x6955bd54};
const kanji_md * const na_kanji0xd1a81c92[] = {&kanji_md91CE, &kanji_md4ED8};
const reading_md nanori_md0xd1a81c92 = {2, NULL, na_kanji0xd1a81c92};
const kanji_md * const na_kanji0xd06d87ae[] = {&kanji_md5BFE, &kanji_md5C0D};
const reading_md nanori_md0xd06d87ae = {2, NULL, na_kanji0xd06d87ae};
const kanji_md * const na_kanji0x9f56e1ff[] = {&kanji_md4F1D};
const reading_md nanori_md0x9f56e1ff = {1, NULL, na_kanji0x9f56e1ff};
const kanji_md * const na_kanji0x83c98d43[] = {&kanji_md4EF2, &kanji_md7E8C};
const reading_md nanori_md0x83c98d43 = {2, NULL, na_kanji0x83c98d43};
const kanji_md * const na_kanji0x55def286[] = {&kanji_md529B, &kanji_md529F, &kanji_md8302, &kanji_md5B5F, &kanji_md60C7};
const reading_md nanori_md0x55def286 = {5, NULL, na_kanji0x55def286};
const kanji_md * const na_kanji0x13282379[] = {&kanji_md662F, &kanji_md4E4B};
const reading_md nanori_md0x13282379 = {2, NULL, na_kanji0x13282379};
const kanji_md * const na_kanji0x3fa0b531[] = {&kanji_md7D4C, &kanji_md6BCE, &kanji_md5178, &kanji_md5E79, &kanji_md5EB8, &kanji_md77E9, &kanji_md7D93};
const reading_md nanori_md0x3fa0b531 = {7, NULL, na_kanji0x3fa0b531};
const kanji_md * const na_kanji0x98f16eb4[] = {&kanji_md693F};
const reading_md nanori_md0x98f16eb4 = {1, NULL, na_kanji0x98f16eb4};
const kanji_md * const na_kanji0x2e8a339e[] = {&kanji_md5186, &kanji_md5713};
const reading_md nanori_md0x2e8a339e = {2, NULL, na_kanji0x2e8a339e};
const kanji_md * const na_kanji0x6031ebe8[] = {&kanji_md5B2C};
const reading_md nanori_md0x6031ebe8 = {1, NULL, na_kanji0x6031ebe8};
const kanji_md * const na_kanji0x183f026b[] = {&kanji_md7A4D};
const reading_md nanori_md0x183f026b = {1, NULL, na_kanji0x183f026b};
const kanji_md * const na_kanji0xf2cd99f1[] = {&kanji_md6458};
const reading_md nanori_md0xf2cd99f1 = {1, NULL, na_kanji0xf2cd99f1};
const kanji_md * const na_kanji0xc456a638[] = {&kanji_md982D};
const reading_md nanori_md0xc456a638 = {1, NULL, na_kanji0xc456a638};
const kanji_md * const na_kanji0xdf923b07[] = {&kanji_md5F69};
const reading_md nanori_md0xdf923b07 = {1, NULL, na_kanji0xdf923b07};
const kanji_md * const na_kanji0xc129660c[] = {&kanji_md525B, &kanji_md6BC5};
const reading_md nanori_md0xc129660c = {2, NULL, na_kanji0xc129660c};
const kanji_md * const na_kanji0x7f26b30a[] = {&kanji_md96C4, &kanji_md5E79, &kanji_md58EE, &kanji_md525B, &kanji_md6BC5, &kanji_md5F6A, &kanji_md5F4A};
const reading_md nanori_md0x7f26b30a = {7, NULL, na_kanji0x7f26b30a};
const kanji_md * const na_kanji0x18a0dac4[] = {&kanji_md8CAB};
const reading_md nanori_md0x18a0dac4 = {1, NULL, na_kanji0x18a0dac4};
const kanji_md * const na_kanji0xc94e7a28[] = {&kanji_md91E3};
const reading_md nanori_md0xc94e7a28 = {1, NULL, na_kanji0xc94e7a28};
const kanji_md * const na_kanji0xc2938cf9[] = {&kanji_md6566, &kanji_md970D};
const reading_md nanori_md0xc2938cf9 = {2, NULL, na_kanji0xc2938cf9};
const kanji_md * const na_kanji0xef9b5b2[] = {&kanji_md9023};
const reading_md nanori_md0xef9b5b2 = {1, NULL, na_kanji0xef9b5b2};
const kanji_md * const na_kanji0x656c4367[] = {&kanji_md982D, &kanji_md56F3, &kanji_md9DB4};
const reading_md nanori_md0x656c4367 = {3, NULL, na_kanji0x656c4367};
const kanji_md * const na_kanji0x8f0d9c48[] = {&kanji_md7BC9, &kanji_md7B51};
const reading_md nanori_md0x8f0d9c48 = {2, NULL, na_kanji0x8f0d9c48};
const kanji_md * const na_kanji0xcc955626[] = {&kanji_md4F5C, &kanji_md9020};
const reading_md nanori_md0xcc955626 = {2, NULL, na_kanji0xcc955626};
const kanji_md * const na_kanji0x4ffbdc3b[] = {&kanji_md9644};
const reading_md nanori_md0x4ffbdc3b = {1, NULL, na_kanji0x4ffbdc3b};
const kanji_md * const na_kanji0x717acc0d[] = {&kanji_md7832};
const reading_md nanori_md0x717acc0d = {1, NULL, na_kanji0x717acc0d};
const kanji_md * const na_kanji0xaa3803a9[] = {&kanji_md90FD, &kanji_md8A70};
const reading_md nanori_md0xaa3803a9 = {2, NULL, na_kanji0xaa3803a9};
const kanji_md * const na_kanji0x2b64883b[] = {&kanji_md5929, &kanji_md5B88, &kanji_md9054, &kanji_md56E0, &kanji_md5F1F, &kanji_md8C4A, &kanji_md6BBF, &kanji_md52C5, &kanji_md6A0B, &kanji_md6C40, &kanji_md9039};
const reading_md nanori_md0x2b64883b = {11, NULL, na_kanji0x2b64883b};
const kanji_md * const na_kanji0x5aee65bc[] = {&kanji_md888B, &kanji_md4FE4};
const reading_md nanori_md0x5aee65bc = {2, NULL, na_kanji0x5aee65bc};
const kanji_md * const na_kanji0x2a81fef0[] = {&kanji_md9244, &kanji_md5FB9, &kanji_md54F2};
const reading_md nanori_md0x2a81fef0 = {3, NULL, na_kanji0x2a81fef0};
const kanji_md * const na_kanji0x10561ad6[] = {&kanji_md9054};
const reading_md nanori_md0x10561ad6 = {1, NULL, na_kanji0x10561ad6};
const kanji_md * const na_kanji0xbf6adf7e[] = {&kanji_md54F2};
const reading_md nanori_md0xbf6adf7e = {1, NULL, na_kanji0xbf6adf7e};
const kanji_md * const na_kanji0xf1a1e52f[] = {&kanji_md5149, &kanji_md7167, &kanji_md6620, &kanji_md8F1D, &kanji_md6804, &kanji_md592E, &kanji_md66DC, &kanji_md662D, &kanji_md6681, &kanji_md65ED, &kanji_md6643, &kanji_md7693, &kanji_md745B, &kanji_md6689};
const reading_md nanori_md0xf1a1e52f = {14, NULL, na_kanji0xf1a1e52f};
const kanji_md * const na_kanji0xc9843062[] = {&kanji_md5F97};
const reading_md nanori_md0xc9843062 = {1, NULL, na_kanji0xc9843062};
const kanji_md * const na_kanji0x7c9c0829[] = {&kanji_md4E00, &kanji_md51FA};
const reading_md nanori_md0x7c9c0829 = {2, NULL, na_kanji0x7c9c0829};
const kanji_md * const na_kanji0xf18ae416[] = {&kanji_md7530, &kanji_md8C4A, &kanji_md514C};
const reading_md nanori_md0xf18ae416 = {3, NULL, na_kanji0xf18ae416};
const kanji_md * const na_kanji0xbf746b92[] = {&kanji_md5085};
const reading_md nanori_md0xbf746b92 = {1, NULL, na_kanji0xbf746b92};
const kanji_md * const na_kanji0xd482b2d3[] = {&kanji_md4EBA, &kanji_md6642, &kanji_md540D, &kanji_md97F3, &kanji_md52DD, &kanji_md592B, &kanji_md5229, &kanji_md77F3, &kanji_md968E, &kanji_md9580, &kanji_md7B49, &kanji_md9CE5, &kanji_md6C38, &kanji_md95D8, &kanji_md8C4A, &kanji_md5BCC, &kanji_md5409, &kanji_md5200, &kanji_md5203, &kanji_md85E4, &kanji_md535A, &kanji_md6D25, &kanji_md4EC1, &kanji_md81E3, &kanji_md6A0B, &kanji_md6D9B, &kanji_md51A8, &kanji_md7576, &kanji_md792A, &kanji_md783A};
const reading_md nanori_md0xd482b2d3 = {30, NULL, na_kanji0xd482b2d3};
const kanji_md * const na_kanji0xc74b0a4f[] = {&kanji_md5341, &kanji_md4EFB, &kanji_md7530, &kanji_md90CE, &kanji_md6D1E};
const reading_md nanori_md0xc74b0a4f = {5, NULL, na_kanji0xc74b0a4f};
const kanji_md * const na_kanji0x271d61c5[] = {&kanji_md6C5F};
const reading_md nanori_md0x271d61c5 = {1, NULL, na_kanji0x271d61c5};
const kanji_md * const na_kanji0x3b296d1d[] = {&kanji_md66A2, &kanji_md4E98, &kanji_md4EA8};
const reading_md nanori_md0x3b296d1d = {3, NULL, na_kanji0x3b296d1d};
const kanji_md * const na_kanji0x1052ca37[] = {&kanji_md6771, &kanji_md67D4, &kanji_md9050};
const reading_md nanori_md0x1052ca37 = {3, NULL, na_kanji0x1052ca37};
const kanji_md * const na_kanji0xc68261cc[] = {&kanji_md7406, &kanji_md9054, &kanji_md900F, &kanji_md5BA3, &kanji_md5FB9, &kanji_md4EAB, &kanji_md66A2, &kanji_md4EA8};
const reading_md nanori_md0xc68261cc = {8, NULL, na_kanji0xc68261cc};
const kanji_md * const na_kanji0x29dd5d41[] = {&kanji_md4EA8};
const reading_md nanori_md0x29dd5d41 = {1, NULL, na_kanji0x29dd5d41};
const kanji_md * const na_kanji0xa9f51984[] = {&kanji_md8A00, &kanji_md4FE1, &kanji_md8AAC, &kanji_md5E38, &kanji_md658E, &kanji_md8FB0};
const reading_md nanori_md0xa9f51984 = {6, NULL, na_kanji0xa9f51984};
const kanji_md * const na_kanji0x978c62bd[] = {&kanji_md6642};
const reading_md nanori_md0x978c62bd = {1, NULL, na_kanji0x978c62bd};
const kanji_md * const na_kanji0xccd80c15[] = {&kanji_md89E3};
const reading_md nanori_md0xccd80c15 = {1, NULL, na_kanji0xccd80c15};
const kanji_md * const na_kanji0xa1535abf[] = {&kanji_md660E, &kanji_md4E16, &kanji_md597D, &kanji_md8981, &kanji_md5229, &kanji_md53B3, &kanji_md9806, &kanji_md92ED, &kanji_md798F, &kanji_md5065, &kanji_md529F, &kanji_md656C, &kanji_md8F09, &kanji_md53F2, &kanji_md654F, &kanji_md5B63, &kanji_md7D00, &kanji_md5B97, &kanji_md5BFF, &kanji_md667A, &kanji_md7984, &kanji_md4FCA, &kanji_md6BC5, &kanji_md8061, &kanji_md6DD1, &kanji_md99FF, &kanji_md54C9, &kanji_md5CFB, &kanji_md6167, &kanji_md5F57, &kanji_md7A14, &kanji_md8087, &kanji_md752B, &kanji_md58FD, &kanji_md60C7};
const reading_md nanori_md0xa1535abf = {35, NULL, na_kanji0xa1535abf};
const kanji_md * const na_kanji0xbcb5c6e2[] = {&kanji_md5BFF};
const reading_md nanori_md0xbcb5c6e2 = {1, NULL, na_kanji0xbcb5c6e2};
const kanji_md * const na_kanji0x6de9d79b[] = {&kanji_md69CB};
const reading_md nanori_md0x6de9d79b = {1, NULL, na_kanji0x6de9d79b};
const kanji_md * const na_kanji0x516ae645[] = {&kanji_md9CE5};
const reading_md nanori_md0x516ae645 = {1, NULL, na_kanji0x516ae645};
const kanji_md * const na_kanji0xc7c34d9b[] = {&kanji_md8FDA};
const reading_md nanori_md0xc7c34d9b = {1, NULL, na_kanji0xc7c34d9b};
const kanji_md * const na_kanji0xa179e6a9[] = {&kanji_md820D};
const reading_md nanori_md0xa179e6a9 = {1, NULL, na_kanji0xa179e6a9};
const kanji_md * const na_kanji0x7d75d79e[] = {&kanji_md98DB};
const reading_md nanori_md0x7d75d79e = {1, NULL, na_kanji0x7d75d79e};
const kanji_md * const na_kanji0xb5d31f6f[] = {&kanji_md6CCA};
const reading_md nanori_md0xb5d31f6f = {1, NULL, na_kanji0xb5d31f6f};
const kanji_md * const na_kanji0x67b4a5ee[] = {&kanji_md798F, &kanji_md81E3, &kanji_md667A};
const reading_md nanori_md0x67b4a5ee = {3, NULL, na_kanji0x67b4a5ee};
const kanji_md * const na_kanji0xebcdc3e5[] = {&kanji_md7559};
const reading_md nanori_md0xebcdc3e5 = {1, NULL, na_kanji0xebcdc3e5};
const kanji_md * const na_kanji0x47de5ad1[] = {&kanji_md5927, &kanji_md77E5, &kanji_md4F5C, &kanji_md671D, &kanji_md5177, &kanji_md8996, &kanji_md8208, &kanji_md5E78, &kanji_md548C, &kanji_md516C, &kanji_md4E08, &kanji_md4E0E, &kanji_md57FA, &kanji_md4F34, &kanji_md7D00, &kanji_md5442, &kanji_md5E79, &kanji_md90A3, &kanji_md8AA0, &kanji_md5949, &kanji_md5BDB, &kanji_md73E0, &kanji_md667A, &kanji_md502B, &kanji_md5DF4, &kanji_md5BC5, &kanji_md5141, &kanji_md798E, &kanji_md608C, &kanji_md5858};
const reading_md nanori_md0x47de5ad1 = {30, NULL, na_kanji0x47de5ad1};
const kanji_md * const na_kanji0x1173b8c3[] = {&kanji_md6A0B};
const reading_md nanori_md0x1173b8c3 = {1, NULL, na_kanji0x1173b8c3};
const kanji_md * const na_kanji0x1e5b8c7e[] = {&kanji_md5F6A};
const reading_md nanori_md0x1e5b8c7e = {1, NULL, na_kanji0x1e5b8c7e};
const kanji_md * const na_kanji0x9f485cb3[] = {&kanji_md90E8, &kanji_md820E};
const reading_md nanori_md0x9f485cb3 = {2, NULL, na_kanji0x9f485cb3};
const kanji_md * const na_kanji0x4bc520db[] = {&kanji_md6A0B};
const reading_md nanori_md0x4bc520db = {1, NULL, na_kanji0x4bc520db};
const kanji_md * const na_kanji0x9157e172[] = {&kanji_md901A, &kanji_md5BCC};
const reading_md nanori_md0x9157e172 = {2, NULL, na_kanji0x9157e172};
const kanji_md * const na_kanji0x811a702b[] = {&kanji_md9053, &kanji_md9060, &kanji_md6C34, &kanji_md53CB, &kanji_md767E, &kanji_md66C7, &kanji_md8C46, &kanji_md8FF9};
const reading_md nanori_md0x811a702b = {8, NULL, na_kanji0x811a702b};
const kanji_md * const na_kanji0xff7d8fef[] = {&kanji_md72EC};
const reading_md nanori_md0xff7d8fef = {1, NULL, na_kanji0xff7d8fef};
const kanji_md * const na_kanji0x61fa110b[] = {&kanji_md7B54, &kanji_md767E};
const reading_md nanori_md0x61fa110b = {2, NULL, na_kanji0x61fa110b};
const kanji_md * const na_kanji0xa6999535[] = {&kanji_md901A};
const reading_md nanori_md0xa6999535 = {1, NULL, na_kanji0xa6999535};
const kanji_md * const na_kanji0xdd3f42cf[] = {&kanji_md9060};
const reading_md nanori_md0xdd3f42cf = {1, NULL, na_kanji0xdd3f42cf};
const kanji_md * const na_kanji0xf02df693[] = {&kanji_md901A};
const reading_md nanori_md0xf02df693 = {1, NULL, na_kanji0xf02df693};
const kanji_md * const na_kanji0x12563400[] = {&kanji_md72EC};
const reading_md nanori_md0x12563400 = {1, NULL, na_kanji0x12563400};
const kanji_md * const na_kanji0xe4647057[] = {&kanji_md6E9D};
const reading_md nanori_md0xe4647057 = {1, NULL, na_kanji0xe4647057};
const kanji_md * const na_kanji0x5fd87f7e[] = {&kanji_md5730};
const reading_md nanori_md0x5fd87f7e = {1, NULL, na_kanji0x5fd87f7e};
const kanji_md * const na_kanji0xa6e838a[] = {&kanji_md6B62};
const reading_md nanori_md0xa6e838a = {1, NULL, na_kanji0xa6e838a};
const kanji_md * const na_kanji0x8da8cae9[] = {&kanji_md53D6};
const reading_md nanori_md0x8da8cae9 = {1, NULL, na_kanji0x8da8cae9};
const kanji_md * const na_kanji0xe0fc00d8[] = {&kanji_md6BBF};
const reading_md nanori_md0xe0fc00d8 = {1, NULL, na_kanji0xe0fc00d8};
const kanji_md * const na_kanji0xca745a39[] = {&kanji_md65B9, &kanji_md9577, &kanji_md4ECA, &kanji_md5411, &kanji_md5973, &kanji_md6D41, &kanji_md96E3, &kanji_md516B, &kanji_md4E03, &kanji_md548C, &kanji_md7A74, &kanji_md6A39, &kanji_md8FB2, &kanji_md963F, &kanji_md7A32, &kanji_md6960, &kanji_md8304};
const reading_md nanori_md0xca745a39 = {17, NULL, na_kanji0xca745a39};
const kanji_md * const na_kanji0xc5c090e9[] = {&kanji_md888B};
const reading_md nanori_md0xc5c090e9 = {1, NULL, na_kanji0xc5c090e9};
const kanji_md * const na_kanji0xa1b9af70[] = {&kanji_md5C1A};
const reading_md nanori_md0xa1b9af70 = {1, NULL, na_kanji0xa1b9af70};
const kanji_md * const na_kanji0xdc228c4c[] = {&kanji_md4F5C, &kanji_md771F, &kanji_md76F4, &kanji_md6210, &kanji_md6709, &kanji_md9806, &kanji_md6E29, &kanji_md5DE8, &kanji_md5FE0, &kanji_md80D6};
const reading_md nanori_md0xdc228c4c = {10, NULL, na_kanji0xdc228c4c};
const kanji_md * const na_kanji0xa689a320[] = {&kanji_md53F2, &kanji_md592E, &kanji_md7965};
const reading_md nanori_md0xa689a320 = {3, NULL, na_kanji0xa689a320};
const kanji_md * const na_kanji0xe9170dfa[] = {&kanji_md4EF2};
const reading_md nanori_md0xe9170dfa = {1, NULL, na_kanji0xe9170dfa};
const kanji_md * const na_kanji0xc0b7f9bc[] = {&kanji_md826F, &kanji_md4E45, &kanji_md4FEE, &kanji_md6804, &kanji_md5442, &kanji_md5BFF, &kanji_md7965, &kanji_md66A2, &kanji_md9149, &kanji_md4EA8, &kanji_md8129};
const reading_md nanori_md0xc0b7f9bc = {11, NULL, na_kanji0xc0b7f9bc};
const kanji_md * const na_kanji0xdb5edc95[] = {&kanji_md6D41};
const reading_md nanori_md0xdb5edc95 = {1, NULL, na_kanji0xdb5edc95};
const kanji_md * const na_kanji0xa4fa4f48[] = {&kanji_md67F3, &kanji_md6E1A};
const reading_md nanori_md0xa4fa4f48 = {2, NULL, na_kanji0xa4fa4f48};
const kanji_md * const na_kanji0x947426db[] = {&kanji_md8304};
const reading_md nanori_md0x947426db = {1, NULL, na_kanji0x947426db};
const kanji_md * const na_kanji0xf338f621[] = {&kanji_md65B9};
const reading_md nanori_md0xf338f621 = {1, NULL, na_kanji0xf338f621};
const kanji_md * const na_kanji0xf70ed94b[] = {&kanji_md6D0B};
const reading_md nanori_md0xf70ed94b = {1, NULL, na_kanji0xf70ed94b};
const kanji_md * const na_kanji0xca9ba0e[] = {&kanji_md64AB};
const reading_md nanori_md0xca9ba0e = {1, NULL, na_kanji0xca9ba0e};
const kanji_md * const na_kanji0x73890067[] = {&kanji_md64AB};
const reading_md nanori_md0x73890067 = {1, NULL, na_kanji0x73890067};
const kanji_md * const na_kanji0x959cd826[] = {&kanji_md96E3, &kanji_md6D6A};
const reading_md nanori_md0x959cd826 = {2, NULL, na_kanji0x959cd826};
const kanji_md * const na_kanji0xf71f1afb[] = {&kanji_md751F};
const reading_md nanori_md0xf71f1afb = {1, NULL, na_kanji0xf71f1afb};
const kanji_md * const na_kanji0x6dcd55ba[] = {&kanji_md4E26};
const reading_md nanori_md0x6dcd55ba = {1, NULL, na_kanji0x6dcd55ba};
const kanji_md * const na_kanji0x75903b1f[] = {&kanji_md8FBA, &kanji_md908A, &kanji_md9089};
const reading_md nanori_md0x75903b1f = {3, NULL, na_kanji0x75903b1f};
const kanji_md * const na_kanji0x5ad51fea[] = {&kanji_md5929};
const reading_md nanori_md0x5ad51fea = {1, NULL, na_kanji0x5ad51fea};
const kanji_md * const na_kanji0xddd1dfa[] = {&kanji_md884C, &kanji_md5357, &kanji_md6D6A, &kanji_md51E1, &kanji_md752B, &kanji_md701A};
const reading_md nanori_md0xddd1dfa = {6, NULL, na_kanji0xddd1dfa};
const kanji_md * const na_kanji0x263a9b81[] = {&kanji_md884C};
const reading_md nanori_md0x263a9b81 = {1, NULL, na_kanji0x263a9b81};
const kanji_md * const na_kanji0xec5760d4[] = {&kanji_md6ED1};
const reading_md nanori_md0xec5760d4 = {1, NULL, na_kanji0xec5760d4};
const kanji_md * const na_kanji0x646dac3f[] = {&kanji_md4F53, &kanji_md6210, &kanji_md696D, &kanji_md9CF4, &kanji_md793C, &kanji_md767E, &kanji_md6E08, &kanji_md82B8, &kanji_md57CE, &kanji_md5C31, &kanji_md6589, &kanji_md5C1A, &kanji_md7A14};
const reading_md nanori_md0x646dac3f = {13, NULL, na_kanji0x646dac3f};
const kanji_md * const na_kanji0x8927f1b4[] = {&kanji_md6210, &kanji_md611B, &kanji_md9CF4, &kanji_md5FB3, &kanji_md7A14};
const reading_md nanori_md0x8927f1b4 = {5, NULL, na_kanji0x8927f1b4};
const kanji_md * const na_kanji0xe2efdb93[] = {&kanji_md8F2A};
const reading_md nanori_md0xe2efdb93 = {1, NULL, na_kanji0xe2efdb93};
const kanji_md * const na_kanji0x9d31c26[] = {&kanji_md7058};
const reading_md nanori_md0x9d31c26 = {1, NULL, na_kanji0x9d31c26};
const kanji_md * const na_kanji0xcfbda5d1[] = {&kanji_md65E5, &kanji_md5165, &kanji_md5408, &kanji_md7406, &kanji_md65B0};
const reading_md nanori_md0xcfbda5d1 = {5, NULL, na_kanji0xcfbda5d1};
const kanji_md * const na_kanji0xdc5422e6[] = {&kanji_md4E8C};
const reading_md nanori_md0xdc5422e6 = {1, NULL, na_kanji0xdc5422e6};
const kanji_md * const na_kanji0xba4a52f1[] = {&kanji_md751F};
const reading_md nanori_md0xba4a52f1 = {1, NULL, na_kanji0xba4a52f1};
const kanji_md * const na_kanji0xeee67dbf[] = {&kanji_md548C};
const reading_md nanori_md0xeee67dbf = {1, NULL, na_kanji0xeee67dbf};
const kanji_md * const na_kanji0xed1132ac[] = {&kanji_md6FC1};
const reading_md nanori_md0xed1132ac = {1, NULL, na_kanji0xed1132ac};
const kanji_md * const na_kanji0x14644ddb[] = {&kanji_md9326};
const reading_md nanori_md0x14644ddb = {1, NULL, na_kanji0x14644ddb};
const kanji_md * const na_kanji0xc395917f[] = {&kanji_md4F3C};
const reading_md nanori_md0xc395917f = {1, NULL, na_kanji0xc395917f};
const kanji_md * const na_kanji0x1906e7d3[] = {&kanji_md65E5, &kanji_md65B0};
const reading_md nanori_md0x1906e7d3 = {2, NULL, na_kanji0x1906e7d3};
const kanji_md * const na_kanji0x7a24a849[] = {&kanji_md65E5, &kanji_md65B0};
const reading_md nanori_md0x7a24a849 = {2, NULL, na_kanji0x7a24a849};
const kanji_md * const na_kanji0x9d369b4e[] = {&kanji_md85AB};
const reading_md nanori_md0x9d369b4e = {1, NULL, na_kanji0x9d369b4e};
const kanji_md * const na_kanji0x23fb515c[] = {&kanji_md751F, &kanji_md6577};
const reading_md nanori_md0x23fb515c = {2, NULL, na_kanji0x23fb515c};
const kanji_md * const na_kanji0x1d5d6a2c[] = {&kanji_md91CE, &kanji_md5974, &kanji_md5FFD, &kanji_md6E1F};
const reading_md nanori_md0x1d5d6a2c = {4, NULL, na_kanji0x1d5d6a2c};
const kanji_md * const na_kanji0xa3608282[] = {&kanji_md7E2B};
const reading_md nanori_md0xa3608282 = {1, NULL, na_kanji0xa3608282};
const kanji_md * const na_kanji0xb884ad7f[] = {&kanji_md9952};
const reading_md nanori_md0xb884ad7f = {1, NULL, na_kanji0xb884ad7f};
const kanji_md * const na_kanji0x3d8ed1d6[] = {&kanji_md984D};
const reading_md nanori_md0x3d8ed1d6 = {1, NULL, na_kanji0x3d8ed1d6};
const kanji_md * const na_kanji0x191f8f00[] = {&kanji_md629C};
const reading_md nanori_md0x191f8f00 = {1, NULL, na_kanji0x191f8f00};
const kanji_md * const na_kanji0x831f2113[] = {&kanji_md708E, &kanji_md8CAB};
const reading_md nanori_md0x831f2113 = {2, NULL, na_kanji0x831f2113};
const kanji_md * const na_kanji0x5ae4385c[] = {&kanji_md4EBA, &kanji_md5E74, &kanji_md5408, &kanji_md5341, &kanji_md7720, &kanji_md5A66, &kanji_md79F0, &kanji_md5982, &kanji_md5DBA, &kanji_md7A14};
const reading_md nanori_md0x5ae4385c = {10, NULL, na_kanji0x5ae4385c};
const kanji_md * const na_kanji0x88d65c67[] = {&kanji_md82D7};
const reading_md nanori_md0x88d65c67 = {1, NULL, na_kanji0x88d65c67};
const kanji_md * const na_kanji0x7e9c07db[] = {&kanji_md5B50};
const reading_md nanori_md0x7e9c07db = {1, NULL, na_kanji0x7e9c07db};
const kanji_md * const na_kanji0x2ad8d008[] = {&kanji_md7DF4};
const reading_md nanori_md0x2ad8d008 = {1, NULL, na_kanji0x2ad8d008};
const kanji_md * const na_kanji0xc651d8ac[] = {&kanji_md5165, &kanji_md80FD, &kanji_md5E03, &kanji_md7D0D, &kanji_md53CA, &kanji_md6FC3, &kanji_md5178, &kanji_md6CC9, &kanji_md8FB2, &kanji_md9952, &kanji_md7BE0, &kanji_md4E3F};
const reading_md nanori_md0xc651d8ac = {12, NULL, na_kanji0xc651d8ac};
const kanji_md * const na_kanji0x6557d119[] = {&kanji_md76F4};
const reading_md nanori_md0x6557d119 = {1, NULL, na_kanji0x6557d119};
const kanji_md * const na_kanji0x9fc4759f[] = {&kanji_md76F4};
const reading_md nanori_md0x9fc4759f = {1, NULL, na_kanji0x9fc4759f};
const kanji_md * const na_kanji0xe6e4e82a[] = {&kanji_md5965};
const reading_md nanori_md0xe6e4e82a = {1, NULL, na_kanji0xe6e4e82a};
const kanji_md * const na_kanji0xc309e89d[] = {&kanji_md5E2B};
const reading_md nanori_md0xc309e89d = {1, NULL, na_kanji0xc309e89d};
const kanji_md * const na_kanji0xb6f2b3b2[] = {&kanji_md5E0C};
const reading_md nanori_md0xb6f2b3b2 = {1, NULL, na_kanji0xb6f2b3b2};
const kanji_md * const na_kanji0xf09dd1ba[] = {&kanji_md5E0C};
const reading_md nanori_md0xf09dd1ba = {1, NULL, na_kanji0xf09dd1ba};
const kanji_md * const na_kanji0x7ca88c1[] = {&kanji_md5185};
const reading_md nanori_md0x7ca88c1 = {1, NULL, na_kanji0x7ca88c1};
const kanji_md * const na_kanji0xd4a9d618[] = {&kanji_md4FE1};
const reading_md nanori_md0xd4a9d618 = {1, NULL, na_kanji0xd4a9d618};
const kanji_md * const na_kanji0xceec2617[] = {&kanji_md4FE1, &kanji_md5E38, &kanji_md696D, &kanji_md9032, &kanji_md7D4C, &kanji_md559C, &kanji_md53CE, &kanji_md9806, &kanji_md5186, &kanji_md4F38, &kanji_md4FEE, &kanji_md81F3, &kanji_md623F, &kanji_md5C55, &kanji_md5145, &kanji_md5EF6, &kanji_md53F2, &kanji_md5BA3, &kanji_md8AA0, &kanji_md5BFF, &kanji_md5BDB, &kanji_md4E4B, &kanji_md9673, &kanji_md5B9C, &kanji_md6052, &kanji_md8FB0, &kanji_md66A2, &kanji_md85AB, &kanji_md5EB8, &kanji_md5BC5, &kanji_md60DF, &kanji_md9756, &kanji_md6566, &kanji_md4E98, &kanji_md664B, &kanji_md5289, &kanji_md5141, &kanji_md4E99, &kanji_md980C, &kanji_md8129};
const reading_md nanori_md0xceec2617 = {40, NULL, na_kanji0xceec2617};
const kanji_md * const na_kanji0x2fd94d30[] = {&kanji_md8FB0, &kanji_md66A2};
const reading_md nanori_md0x2fd94d30 = {2, NULL, na_kanji0x2fd94d30};
const kanji_md * const na_kanji0x6f581703[] = {&kanji_md5EF6};
const reading_md nanori_md0x6f581703 = {1, NULL, na_kanji0x6f581703};
const kanji_md * const na_kanji0x757ad33d[] = {&kanji_md767B};
const reading_md nanori_md0x757ad33d = {1, NULL, na_kanji0x757ad33d};
const kanji_md * const na_kanji0x84a72163[] = {&kanji_md4E0A, &kanji_md767B};
const reading_md nanori_md0x84a72163 = {2, NULL, na_kanji0x84a72163};
const kanji_md * const na_kanji0x94a7f35f[] = {&kanji_md5BA3, &kanji_md6602, &kanji_md5347, &kanji_md6572, &kanji_md965F};
const reading_md nanori_md0x94a7f35f = {5, NULL, na_kanji0x94a7f35f};
const kanji_md * const na_kanji0x84f2de8c[] = {&kanji_md96F2};
const reading_md nanori_md0x84f2de8c = {1, NULL, na_kanji0x84f2de8c};
const kanji_md * const na_kanji0xa18d3197[] = {&kanji_md82D7};
const reading_md nanori_md0xa18d3197 = {1, NULL, na_kanji0xa18d3197};
const kanji_md * const na_kanji0x4c6949df[] = {&kanji_md77E5, &kanji_md5EA6, &kanji_md7406, &kanji_md771F, &kanji_md6559, &kanji_md6210, &kanji_md8A18, &kanji_md4E57, &kanji_md89AA, &kanji_md5B66, &kanji_md683C, &kanji_md80FD, &kanji_md8B70, &kanji_md5229, &kanji_md793C, &kanji_md5F0F, &kanji_md5468, &kanji_md7FA9, &kanji_md5E2B, &kanji_md767B, &kanji_md5100, &kanji_md9806, &kanji_md4EE4, &kanji_md81F3, &kanji_md6C38, &kanji_md529F, &kanji_md656C, &kanji_md898F, &kanji_md88D5, &kanji_md5C55, &kanji_md7E54, &kanji_md8F09, &kanji_md5BA3, &kanji_md7D71, &kanji_md7948, &kanji_md6607, &kanji_md7814, &kanji_md5F8B, &kanji_md614E, &kanji_md795D, &kanji_md7BC4, &kanji_md5FB3, &kanji_md7D00, &kanji_md8CE2, &kanji_md8A13, &kanji_md5B97, &kanji_md96C5, &kanji_md5BFF, &kanji_md5BDB, &kanji_md4EC1, &kanji_md54F2, &kanji_md667A, &kanji_md8CC0, &kanji_md5B54, &kanji_md4ED9, &kanji_md502B, &kanji_md7A42, &kanji_md5B5D, &kanji_md5B9C, &kanji_md61B2, &kanji_md4E43, &kanji_md66A2, &kanji_md52C5, &kanji_md6566, &kanji_md8A54, &kanji_md77E9, &kanji_md798E, &kanji_md5C2D};
const reading_md nanori_md0x4c6949df = {68, NULL, na_kanji0x4c6949df};
const kanji_md * const na_kanji0x68348473[] = {&kanji_md9593, &kanji_md4E8C, &kanji_md9577, &kanji_md534A, &kanji_md756A, &kanji_md516B, &kanji_md571F, &kanji_md5357, &kanji_md91DD, &kanji_md7C73, &kanji_md4F2F, &kanji_md82B3, &kanji_md5E61, &kanji_md8429};
const reading_md nanori_md0x68348473 = {14, NULL, na_kanji0x68348473};
const kanji_md * const na_kanji0x81f81dff[] = {&kanji_md5B5F, &kanji_md699B};
const reading_md nanori_md0x81f81dff = {2, NULL, na_kanji0x81f81dff};
const kanji_md * const na_kanji0xa52e8207[] = {&kanji_md9AD8, &kanji_md535A};
const reading_md nanori_md0xa52e8207 = {2, NULL, na_kanji0xa52e8207};
const kanji_md * const na_kanji0xdf57c4b9[] = {&kanji_md4F5C};
const reading_md nanori_md0xdf57c4b9 = {1, NULL, na_kanji0xdf57c4b9};
const kanji_md * const na_kanji0x10b59caa[] = {&kanji_md7B65};
const reading_md nanori_md0x10b59caa = {1, NULL, na_kanji0x10b59caa};
const kanji_md * const na_kanji0x7da17103[] = {&kanji_md8FEB};
const reading_md nanori_md0x7da17103 = {1, NULL, na_kanji0x7da17103};
const kanji_md * const na_kanji0x8e4bfd8b[] = {&kanji_md8FEB};
const reading_md nanori_md0x8e4bfd8b = {1, NULL, na_kanji0x8e4bfd8b};
const kanji_md * const na_kanji0x5d948289[] = {&kanji_md9593, &kanji_md72ED, &kanji_md633E, &kanji_md964C, &kanji_md7872};
const reading_md nanori_md0x5d948289 = {5, NULL, na_kanji0x5d948289};
const kanji_md * const na_kanji0x515ec694[] = {&kanji_md8FEB};
const reading_md nanori_md0x515ec694 = {1, NULL, na_kanji0x515ec694};
const kanji_md * const na_kanji0x6e5e112f[] = {&kanji_md9593, &kanji_md968E, &kanji_md5544};
const reading_md nanori_md0x6e5e112f = {3, NULL, na_kanji0x6e5e112f};
const kanji_md * const na_kanji0x1c5b36c5[] = {&kanji_md8D70};
const reading_md nanori_md0x1c5b36c5 = {1, NULL, na_kanji0x1c5b36c5};
const kanji_md * const na_kanji0x63309a40[] = {&kanji_md4E00, &kanji_md5927, &kanji_md5143, &kanji_md7B46, &kanji_md5275, &kanji_md5553, &kanji_md54C9, &kanji_md5B5F, &kanji_md752B, &kanji_md5F0C};
const reading_md nanori_md0x63309a40 = {10, NULL, na_kanji0x63309a40};
const kanji_md * const na_kanji0xfbdee1e2[] = {&kanji_md8377, &kanji_md6CF0, &kanji_md8299, &kanji_md84C9};
const reading_md nanori_md0xfbdee1e2 = {4, NULL, na_kanji0xfbdee1e2};
const kanji_md * const na_kanji0x7713a430[] = {&kanji_md6BC5};
const reading_md nanori_md0x7713a430 = {1, NULL, na_kanji0x7713a430};
const kanji_md * const na_kanji0x6386aeab[] = {&kanji_md79E6};
const reading_md nanori_md0x6386aeab = {1, NULL, na_kanji0x6386aeab};
const kanji_md * const na_kanji0x996e66a0[] = {&kanji_md5E73};
const reading_md nanori_md0x996e66a0 = {1, NULL, na_kanji0x996e66a0};
const kanji_md * const na_kanji0x5f031e91[] = {&kanji_md767D, &kanji_md521D, &kanji_md670D, &kanji_md516B};
const reading_md nanori_md0x5f031e91 = {4, NULL, na_kanji0x5f031e91};
const kanji_md * const na_kanji0xbb8d3d86[] = {&kanji_md670D, &kanji_md6CCA, &kanji_md5EFF, &kanji_md8087};
const reading_md nanori_md0xbb8d3d86 = {4, NULL, na_kanji0xbb8d3d86};
const kanji_md * const na_kanji0xc5cea0ea[] = {&kanji_md82F1, &kanji_md5484, &kanji_md7560, &kanji_md5859, &kanji_md7E90};
const reading_md nanori_md0xc5cea0ea = {5, NULL, na_kanji0xc5cea0ea};
const kanji_md * const na_kanji0x58044539[] = {&kanji_md843C};
const reading_md nanori_md0x58044539 = {1, NULL, na_kanji0x58044539};
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
