maccody/KanaChordPlus/software/onyomi.h

/* onyomi.h */
/**
This file is part of KanaChordPlus Keyboard.
 Copyright (C) 2024 Mac A. Cody

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
 You should have received a copy of the GNU General Public License
 along with this program.  If not, see <http://www.gnu.org/licenses/>.
**/

#ifndef AFFIX_ENUM
#define AFFIX_ENUM
enum affix_enum {
  none,   // No enhancments to reading (e.g., xyz).
  prefix, // Reading is a prefix (e.g., wxyz-).
  suffix, // Reading is a suffix (e.g., -wxyz).
  jword,  // Japanese word string with jukujikun or irregular reading.
  meaning // English meaning string for Japanese word enumerated above.
};
#endif

#ifndef OKURI_METADATA_TYPE
#define OKURI_METADATA_TYPE
typedef struct okuri_md {
  const uint8_t len;
  const affix_enum * const alist;
  const char **clist;
} okuri_md;
#endif

#ifndef READING_METADATA_TYPE
#define READING_METADATA_TYPE
typedef struct reading_md {
  const uint16_t len;
  const okuri_md * const * olist;
  const kanji_md * const * klist;
} reading_md;
#endif
const kanji_md * const on_kanji0x3741c033[] = {&kanji_md963F, &kanji_md5516, &kanji_md4E9C, &kanji_md7AAA, &kanji_md86D9, &kanji_md9D09, &kanji_md580A, &kanji_md75FE, &kanji_md941A, &kanji_md5A40, &kanji_md4E9E, &kanji_md95BC, &kanji_md54C7, &kanji_md5A03, &kanji_md930F, &kanji_md7317, &kanji_md897E};
const reading_md onyomi_md0x3741c033 = {17, NULL, on_kanji0x3741c033};
const kanji_md * const on_kanji0xcc6b5b3c[] = {&kanji_md611B, &kanji_md54C0, &kanji_md6328, &kanji_md57C3, &kanji_md66D6, &kanji_md9744, &kanji_md4E43, &kanji_md7A62, &kanji_md978B, &kanji_md77EE, &kanji_md9698, &kanji_md85F9, &kanji_md566B, &kanji_md5EFC, &kanji_md9749, &kanji_md59F6, &kanji_md77B9, &kanji_md54C7, &kanji_md5A03, &kanji_md8FFA, &kanji_md9628, &kanji_md6B38};
const reading_md onyomi_md0xcc6b5b3c = {22, NULL, on_kanji0xcc6b5b3c};
const kanji_md * const on_kanji0x4c3c10d5[] = {&kanji_md60AA, &kanji_md63E1, &kanji_md5516, &kanji_md627C, &kanji_md8EDB, &kanji_md6E25, &kanji_md580A, &kanji_md5E44, &kanji_md9F77, &kanji_md9DFD, &kanji_md60E1, &kanji_md9628};
const reading_md onyomi_md0x4c3c10d5 = {12, NULL, on_kanji0x4c3c10d5};
const kanji_md * const on_kanji0x599d05c8[] = {&kanji_md5727, &kanji_md8ECB, &kanji_md65A1, &kanji_md95BC, &kanji_md904F, &kanji_md624E, &kanji_md58D3};
const reading_md onyomi_md0x599d05c8 = {7, NULL, on_kanji0x599d05c8};
const kanji_md * const on_kanji0x1b965983[] = {&kanji_md884C, &kanji_md5B89, &kanji_md6697, &kanji_md6848, &kanji_md95C7, &kanji_md53AD, &kanji_md978D, &kanji_md5EB5, &kanji_md674F, &kanji_md6309, &kanji_md6BB7, &kanji_md9921, &kanji_md8AF3, &kanji_md664F, &kanji_md9EEF, &kanji_md83F4, &kanji_md9B9F, &kanji_md95B9, &kanji_md7F68, &kanji_md9EF6};
const reading_md onyomi_md0x1b965983 = {20, NULL, on_kanji0x1b965983};
const kanji_md * const on_kanji0xb928b548[] = {&kanji_md610F, &kanji_md4EE5, &kanji_md56F2, &kanji_md9055, &kanji_md7570, &kanji_md4F4D, &kanji_md79FB, &kanji_md8863, &kanji_md5A01, &kanji_md70BA, &kanji_md6613, &kanji_md907A, &kanji_md533B, &kanji_md552F, &kanji_md6905, &kanji_md4F9D, &kanji_md5049, &kanji_md6170, &kanji_md86C7, &kanji_md59D4, &kanji_md4F0A, &kanji_md80C3, &kanji_md7DAD, &kanji_md6590, &kanji_md754F, &kanji_md840E, &kanji_md7DEF, &kanji_md5C09, &kanji_md9640, &kanji_md98F4, &kanji_md8466, &kanji_md92F3, &kanji_md8B02, &kanji_md5937, &kanji_md5E37, &kanji_md60DF, &kanji_md6D1F, &kanji_md5F59, &kanji_md9824, &kanji_md7E0A, &kanji_md5DF2, &kanji_md75CD, &kanji_md501A, &kanji_md502D, &kanji_md9950, &kanji_md97CB, &kanji_md58EC, &kanji_md71A8, &kanji_md875F, &kanji_md4F57, &kanji_md605A, &kanji_md9BAA, &kanji_md6B39, &kanji_md566B, &kanji_md6E2D, &kanji_md77E3, &kanji_md851A, &kanji_md6021, &kanji_md9749, &kanji_md8A51, &kanji_md61FF, &kanji_md8CBD, &kanji_md7232, &kanji_md59E8, &kanji_md56D7, &kanji_md9912, &kanji_md75FF, &kanji_md5F5D, &kanji_md5E43, &kanji_md91AB, &kanji_md570D, &kanji_md8084, &kanji_md9036, &kanji_md7317, &kanji_md5F5C, &kanji_md82E1};
const reading_md onyomi_md0xb928b548 = {76, NULL, on_kanji0xb928b548};
const kanji_md * const on_kanji0xd159c0f2[] = {&kanji_md57DF, &kanji_md6216, &kanji_md95BE};
const reading_md onyomi_md0xd159c0f2 = {3, NULL, on_kanji0xd159c0f2};
const kanji_md * const on_kanji0x4fafaf5e[] = {&kanji_md80B2, &kanji_md62D7, &kanji_md7CA5, &kanji_md90C1, &kanji_md71E0, &kanji_md9B3B, &kanji_md58BA, &kanji_md6FB3, &kanji_md6BD3, &kanji_md6631, &kanji_md5F67, &kanji_md715C};
const reading_md onyomi_md0x4fafaf5e = {12, NULL, on_kanji0x4fafaf5e};
const kanji_md * const on_kanji0x6d7d1756[] = {&kanji_md7726, &kanji_md7725};
const reading_md onyomi_md0x6d7d1756 = {2, NULL, on_kanji0x6d7d1756};
const kanji_md * const on_kanji0x96c2526e[] = {&kanji_md4E00, &kanji_md59EA, &kanji_md58F1, &kanji_md58F9, &kanji_md5F0C, &kanji_md807F};
const reading_md onyomi_md0x96c2526e = {6, NULL, on_kanji0x96c2526e};
const kanji_md * const on_kanji0x5490e16d[] = {&kanji_md4E00, &kanji_md9038, &kanji_md6EA2, &kanji_md4E59, &kanji_md59EA, &kanji_md58F1, &kanji_md564E, &kanji_md63D6, &kanji_md4F5A, &kanji_md6C68, &kanji_md93B0, &kanji_md58F9, &kanji_md9DF8, &kanji_md5F0C, &kanji_md8EFC, &kanji_md807F};
const reading_md onyomi_md0x5490e16d = {16, NULL, on_kanji0x5490e16d};
const kanji_md * const on_kanji0x3ba79f0c[] = {&kanji_md97F3, &kanji_md5F15, &kanji_md98F2, &kanji_md54E1, &kanji_md96A0, &kanji_md5370, &kanji_md56E0, &kanji_md9670, &kanji_md9662, &kanji_md54BD, &kanji_md6DEB, &kanji_md852D, &kanji_md97FB, &kanji_md6147, &kanji_md59FB, &kanji_md5BC5, &kanji_md80E4, &kanji_md9E1A, &kanji_md6BB7, &kanji_md9695, &kanji_md7B4D, &kanji_md5141, &kanji_md8693, &kanji_md6E6E, &kanji_md5C39, &kanji_md543D, &kanji_md5A6C, &kanji_md8335, &kanji_md8D07, &kanji_md6041, &kanji_md6B9E, &kanji_md7B0B, &kanji_md6C24, &kanji_md5819, &kanji_md96B1, &kanji_md98EE, &kanji_md97F5, &kanji_md6600};
const reading_md onyomi_md0x3ba79f0c = {38, NULL, on_kanji0x3ba79f0c};
const kanji_md * const on_kanji0x65300466[] = {&kanji_md6709, &kanji_md53F3, &kanji_md512A, &kanji_md7FBD, &kanji_md96E8, &kanji_md5B87, &kanji_md80E1, &kanji_md8FC2, &kanji_md70CF, &kanji_md55DA, &kanji_md828B, &kanji_md8B33, &kanji_md7950, &kanji_md7D06, &kanji_md4F51, &kanji_md71E0, &kanji_md4E8E, &kanji_md76C2, &kanji_md79B9, &kanji_md50B4, &kanji_md4F91, &kanji_md5401, &kanji_md5AD7, &kanji_md9F72, &kanji_md6859, &kanji_md5862, &kanji_md6327};
const reading_md onyomi_md0x65300466 = {27, NULL, on_kanji0x65300466};
const kanji_md * const on_kanji0xf147fee7[] = {&kanji_md8334};
const reading_md onyomi_md0xf147fee7 = {1, NULL, on_kanji0xf147fee7};
const kanji_md * const on_kanji0x4fed33e9[] = {&kanji_md9B31, &kanji_md6B1D, &kanji_md71A8, &kanji_md851A};
const reading_md onyomi_md0x4fed33e9 = {4, NULL, on_kanji0x4fed33e9};
const kanji_md * const on_kanji0xba6d2bbd[] = {&kanji_md904B, &kanji_md96F2, &kanji_md82B8, &kanji_md6028, &kanji_md4E91, &kanji_md6688, &kanji_md85DD, &kanji_md9695, &kanji_md6B1D, &kanji_md860A, &kanji_md543D, &kanji_md9942, &kanji_md8018, &kanji_md891E, &kanji_md8580, &kanji_md614D, &kanji_md7E67, &kanji_md7D1C, &kanji_md6B9E, &kanji_md9DA4};
const reading_md onyomi_md0xba6d2bbd = {20, NULL, on_kanji0xba6d2bbd};
const kanji_md * const on_kanji0xd93dec88[] = {&kanji_md4F1A, &kanji_md56DE, &kanji_md753B, &kanji_md8863, &kanji_md7D75, &kanji_md61D0, &kanji_md58CA, &kanji_md6075, &kanji_md885B, &kanji_md4F9D, &kanji_md6F70, &kanji_md6B6A, &kanji_md5EFB, &kanji_md9688, &kanji_md4E5F, &kanji_md5F8A, &kanji_md7A62, &kanji_md6167, &kanji_md5F57, &kanji_md6DEE, &kanji_md6703, &kanji_md60E0, &kanji_md54C7, &kanji_md885E, &kanji_md7E6A, &kanji_md61F7, &kanji_md756B, &kanji_md930F, &kanji_md8FF4, &kanji_md56D8, &kanji_md58DE, &kanji_md8559};
const reading_md onyomi_md0xd93dec88 = {32, NULL, on_kanji0xd93dec88};
const kanji_md * const on_kanji0xdd5979fa[] = {&kanji_md5F71, &kanji_md6620, &kanji_md92ED, &kanji_md6C38, &kanji_md6804, &kanji_md55B6, &kanji_md82F1, &kanji_md885B, &kanji_md6CF3, &kanji_md6D29, &kanji_md7FF3, &kanji_md66F3, &kanji_md8A60, &kanji_md88D4, &kanji_md53E1, &kanji_md6CC4, &kanji_md5B30, &kanji_md7E0A, &kanji_md9950, &kanji_md76C8, &kanji_md9719, &kanji_md6BAA, &kanji_md745B, &kanji_md74D4, &kanji_md514C, &kanji_md7F4C, &kanji_md8811, &kanji_md7A4E, &kanji_md8D0F, &kanji_md7E93, &kanji_md69AE, &kanji_md9834, &kanji_md548F, &kanji_md668E, &kanji_md6F41, &kanji_md66F5, &kanji_md885E, &kanji_md584B, &kanji_md777F, &kanji_md7469, &kanji_md701B, &kanji_md90E2, &kanji_md749F, &kanji_md71DF, &kanji_md9348, &kanji_md6979, &kanji_md67BB, &kanji_md514A};
const reading_md onyomi_md0xdd5979fa = {48, NULL, on_kanji0xdd5979fa};
const kanji_md * const on_kanji0x4c863caf[] = {&kanji_md5FAD};
const reading_md onyomi_md0x4c863caf = {1, NULL, on_kanji0x4c863caf};
const kanji_md * const on_kanji0x236e341d[] = {&kanji_md5F79, &kanji_md6613, &kanji_md99C5, &kanji_md6DB2, &kanji_md76CA, &kanji_md75AB, &kanji_md814B, &kanji_md4EA6, &kanji_md5955, &kanji_md8734, &kanji_md7E79, &kanji_md8AE1, &kanji_md6396, &kanji_md9BE3, &kanji_md8993, &kanji_md8B1A, &kanji_md876A, &kanji_md9A5B, &kanji_md61CC};
const reading_md onyomi_md0x236e341d = {19, NULL, on_kanji0x236e341d};
const kanji_md * const on_kanji0x7f2ce80c[] = {&kanji_md8D8A, &kanji_md60A6, &kanji_md54BD, &kanji_md95B2, &kanji_md66F0, &kanji_md8B01, &kanji_md9950, &kanji_md564E, &kanji_md925E, &kanji_md514C, &kanji_md7CA4, &kanji_md6209, &kanji_md514A};
const reading_md onyomi_md0x7f2ce80c = {13, NULL, on_kanji0x7f2ce80c};
const kanji_md * const on_kanji0x354ed157[] = {&kanji_md9060, &kanji_md7E01, &kanji_md5186, &kanji_md5727, &kanji_md7159, &kanji_md6F14, &kanji_md5712, &kanji_md5EF6, &kanji_md708E, &kanji_md63F4, &kanji_md6CBF, &kanji_md57A3, &kanji_md5869, &kanji_md4FFA, &kanji_md5BB4, &kanji_md925B, &kanji_md7FA8, &kanji_md733F, &kanji_md8276, &kanji_md5B9B, &kanji_md6028, &kanji_md54BD, &kanji_md6DF5, &kanji_md53AD, &kanji_md7114, &kanji_md71D5, &kanji_md5830, &kanji_md82D1, &kanji_md6D8E, &kanji_md9CF6, &kanji_md6DF9, &kanji_md7109, &kanji_md63A9, &kanji_md5A49, &kanji_md56A5, &kanji_md7B75, &kanji_md5A9B, &kanji_md95BB, &kanji_md9695, &kanji_md70DF, &kanji_md51A4, &kanji_md81D9, &kanji_md8712, &kanji_md5944, &kanji_md873F, &kanji_md839A, &kanji_md884D, &kanji_md6E6E, &kanji_md9D1B, &kanji_md9B58, &kanji_md5AE3, &kanji_md8F45, &kanji_md5043, &kanji_md7230, &kanji_md8C4C, &kanji_md8881, &kanji_md6E15, &kanji_md63BE, &kanji_md8597, &kanji_md5713, &kanji_md6350, &kanji_md6A90, &kanji_md95BC, &kanji_md6E72, &kanji_md5A1F, &kanji_md7C37, &kanji_md5BC3, &kanji_md95B9, &kanji_md7F68, &kanji_md571C, &kanji_md9E7D, &kanji_md8277, &kanji_md92FA, &kanji_md8983, &kanji_md8B8C, &kanji_md8306, &kanji_md9EF6, &kanji_md6ADE, &kanji_md58D3, &kanji_md7BF6, &kanji_md6081, &kanji_md6E0A};
const reading_md onyomi_md0x354ed157 = {82, NULL, on_kanji0x354ed157};
const kanji_md * const on_kanji0x389ea08f[] = {&kanji_md60AA, &kanji_md548C, &kanji_md6C5A, &kanji_md963F, &kanji_md70CF, &kanji_md55DA, &kanji_md65BC, &kanji_md4E4E, &kanji_md580A, &kanji_md6DE4, &kanji_md98EB, &kanji_md60E1, &kanji_md5862, &kanji_md5539};
const reading_md onyomi_md0x389ea08f = {14, NULL, on_kanji0x389ea08f};
const kanji_md * const on_kanji0xf5b3ec9a[] = {&kanji_md6A2A, &kanji_md5FDC, &kanji_md62BC, &kanji_md5965, &kanji_md5727, &kanji_md9EC4, &kanji_md533A, &kanji_md738B, &kanji_md592E, &kanji_md5F80, &kanji_md6BB4, &kanji_md685C, &kanji_md7687, &kanji_md62D7, &kanji_md9DF9, &kanji_md53AD, &kanji_md6B27, &kanji_md8956, &kanji_md65FA, &kanji_md9D28, &kanji_md51F9, &kanji_md8B33, &kanji_md5614, &kanji_md7FC1, &kanji_md9DAF, &kanji_md61CA, &kanji_md9D0E, &kanji_md7515, &kanji_md9E1A, &kanji_md592D, &kanji_md51F0, &kanji_md72CE, &kanji_md6789, &kanji_md71E0, &kanji_md5321, &kanji_md9D26, &kanji_md81BA, &kanji_md93D6, &kanji_md5ABC, &kanji_md6C6A, &kanji_md600F, &kanji_md5340, &kanji_md7F4C, &kanji_md9ECC, &kanji_md61C9, &kanji_md6AFB, &kanji_md5967, &kanji_md9785, &kanji_md6B83, &kanji_md59F6, &kanji_md5AD7, &kanji_md9D2C, &kanji_md750C, &kanji_md58BA, &kanji_md74EE, &kanji_md6FB3, &kanji_md84CA, &kanji_md5F83, &kanji_md6CD3, &kanji_md71C1, &kanji_md56B6, &kanji_md6B50, &kanji_md6CF1, &kanji_md58D3, &kanji_md79E7, &kanji_md5C22, &kanji_md715C};
const reading_md onyomi_md0xf5b3ec9a = {67, NULL, on_kanji0xf5b3ec9a};
const kanji_md * const on_kanji0xce6051d[] = {&kanji_md5C4B, &kanji_md61B6, &kanji_md81C6, &kanji_md5104, &kanji_md6C83, &kanji_md566B, &kanji_md5967, &kanji_md6FB3, &kanji_md6A8D};
const reading_md onyomi_md0xce6051d = {9, NULL, on_kanji0xce6051d};
const kanji_md * const on_kanji0xba344146[] = {&kanji_md8D8A, &kanji_md4E59, &kanji_md8183, &kanji_md69B2};
const reading_md onyomi_md0xba344146 = {4, NULL, on_kanji0xba344146};
const kanji_md * const on_kanji0xf175e969[] = {&kanji_md97F3, &kanji_md9060, &kanji_md98F2, &kanji_md96A0, &kanji_md6E29, &kanji_md95C7, &kanji_md7A4F, &kanji_md6069, &kanji_md6028, &kanji_md53AD, &kanji_md852D, &kanji_md82D1, &kanji_md8AF3, &kanji_md9D1B, &kanji_md543D, &kanji_md8881, &kanji_md8597, &kanji_md891E, &kanji_md8580, &kanji_md614D, &kanji_md9C2E, &kanji_md96B1, &kanji_md98EE, &kanji_md761F, &kanji_md7A69};
const reading_md onyomi_md0xf175e969 = {25, NULL, on_kanji0xf175e969};
const kanji_md * const on_kanji0x865b3bf[] = {&kanji_md4E0B, &kanji_md4F55, &kanji_md5BB6, &kanji_md679C, &kanji_md7A81, &kanji_md5316, &kanji_md904E, &kanji_md52A0, &kanji_md53EF, &kanji_md706B, &kanji_md548C, &kanji_md82B1, &kanji_md500B, &kanji_md4FA1, &kanji_md8377, &kanji_md6B4C, &kanji_md590F, &kanji_md83EF, &kanji_md4EEE, &kanji_md79D1, &kanji_md6687, &kanji_md9774, &kanji_md6CB3, &kanji_md8AB2, &kanji_md507D, &kanji_md53F1, &kanji_md7A3C, &kanji_md5AC1, &kanji_md5629, &kanji_md82DB, &kanji_md6E26, &kanji_md67B6, &kanji_md8CA8, &kanji_md83D3, &kanji_md934B, &kanji_md7B87, &kanji_md971E, &kanji_md8888, &kanji_md4F10, &kanji_md74DC, &kanji_md798D, &kanji_md5BE1, &kanji_md99D5, &kanji_md4F3D, &kanji_md4F73, &kanji_md5475, &kanji_md8A1B, &kanji_md8DE8, &kanji_md8FE6, &kanji_md5609, &kanji_md7AA9, &kanji_md6A3A, &kanji_md56EE, &kanji_md67B7, &kanji_md5925, &kanji_md8304, &kanji_md8766, &kanji_md698E, &kanji_md7455, &kanji_md8C3A, &kanji_md8A36, &kanji_md5366, &kanji_md846D, &kanji_md581D, &kanji_md73C8, &kanji_md592D, &kanji_md8E1D, &kanji_md7F45, &kanji_md8778, &kanji_md6208, &kanji_md54E5, &kanji_md8DCF, &kanji_md9846, &kanji_md73C2, &kanji_md8CC8, &kanji_md79BE, &kanji_md5EC8, &kanji_md5440, &kanji_md53A6, &kanji_md5D0B, &kanji_md80EF, &kanji_md67EF, &kanji_md88F9, &kanji_md8238, &kanji_md8EFB, &kanji_md9C15, &kanji_md5047, &kanji_md7B33, &kanji_md75C2, &kanji_md54BC, &kanji_md9050, &kanji_md9335, &kanji_md50F9, &kanji_md935C, &kanji_md50DE, &kanji_md874C, &kanji_md8B0C, &kanji_md4E2A, &kanji_md8B41};
const reading_md onyomi_md0x865b3bf = {99, NULL, on_kanji0x865b3bf};
const kanji_md * const on_kanji0x268c2299[] = {&kanji_md4F1A, &kanji_md958B, &kanji_md89E3, &kanji_md754C, &kanji_md56DE, &kanji_md6539, &kanji_md968E, &kanji_md753B, &kanji_md4ECB, &kanji_md5FEB, &kanji_md6D77, &kanji_md602A, &kanji_md8857, &kanji_md639B, &kanji_md5C4A, &kanji_md7D75, &kanji_md6094, &kanji_md61D0, &kanji_md58CA, &kanji_md7686, &kanji_md7070, &kanji_md6212, &kanji_md84CB, &kanji_md68B0, &kanji_md6F70, &kanji_md9AB8, &kanji_md584A, &kanji_md54B3, &kanji_md5208, &kanji_md5EFB, &kanji_md93A7, &kanji_md62D0, &kanji_md82A5, &kanji_md6666, &kanji_md51F1, &kanji_md5F8A, &kanji_md87F9, &kanji_md6A9C, &kanji_md9B41, &kanji_md9BAD, &kanji_md6062, &kanji_md978B, &kanji_md583A, &kanji_md8AE7, &kanji_md9082, &kanji_md5080, &kanji_md736A, &kanji_md5366, &kanji_md4EA5, &kanji_md6B47, &kanji_md8C48, &kanji_md81BE, &kanji_md4E56, &kanji_md5599, &kanji_md6F11, &kanji_md6977, &kanji_md7F6B, &kanji_md99ED, &kanji_md5055, &kanji_md8AA1, &kanji_md82C5, &kanji_md69D0, &kanji_md75A5, &kanji_md61C8, &kanji_md8AA8, &kanji_md858A, &kanji_md6DEE, &kanji_md6867, &kanji_md6703, &kanji_md8334, &kanji_md827E, &kanji_md5B69, &kanji_md769A, &kanji_md6302, &kanji_md5793, &kanji_md9C60, &kanji_md9BA0, &kanji_md9697, &kanji_md5D6C, &kanji_md7470, &kanji_md85A4, &kanji_md8588, &kanji_md6060, &kanji_md86D4, &kanji_md4E10, &kanji_md7E6A, &kanji_md54BC, &kanji_md61F7, &kanji_md756B, &kanji_md8FF4, &kanji_md91A2, &kanji_md8462, &kanji_md56D8, &kanji_md69BF, &kanji_md6922, &kanji_md8902, &kanji_md5EE8, &kanji_md6137, &kanji_md559F, &kanji_md67B4, &kanji_md58DE, &kanji_md5274, &kanji_md6B38, &kanji_md76D6, &kanji_md91AF, &kanji_md4E42, &kanji_md592C, &kanji_md63E9, &kanji_md5C46, &kanji_md6D04, &kanji_md89E7};
const reading_md onyomi_md0x268c2299 = {111, NULL, on_kanji0x268c2299};
const kanji_md * const on_kanji0xc44de59e[] = {&kanji_md899A, &kanji_md683C, &kanji_md78BA, &kanji_md89D2, &kanji_md753B, &kanji_md5BA2, &kanji_md5404, &kanji_md811A, &kanji_md9769, &kanji_md9694, &kanji_md8F03, &kanji_md7372, &kanji_md62E1, &kanji_md63B4, &kanji_md6BBB, &kanji_md90ED, &kanji_md6838, &kanji_md6DF5, &kanji_md95A3, &kanji_md7A6B, &kanji_md9DB4, &kanji_md5687, &kanji_md6DB8, &kanji_md5ED3, &kanji_md652A, &kanji_md70D9, &kanji_md652B, &kanji_md8D6B, &kanji_md5283, &kanji_md9998, &kanji_md5580, &kanji_md7893, &kanji_md77CD, &kanji_md64F1, &kanji_md6BBC, &kanji_md64B9, &kanji_md688F, &kanji_md5859, &kanji_md9B29, &kanji_md6E15, &kanji_md970D, &kanji_md72E2, &kanji_md606A, &kanji_md8C89, &kanji_md7845, &kanji_md69E8, &kanji_md87AB, &kanji_md9ABC, &kanji_md89BA, &kanji_md58D1, &kanji_md9DFD, &kanji_md74E0, &kanji_md630C, &kanji_md8188, &kanji_md8195, &kanji_md756B, &kanji_md54AF, &kanji_md5E57, &kanji_md6877, &kanji_md64F4, &kanji_md8816, &kanji_md8988, &kanji_md99EE, &kanji_md6901, &kanji_md9481, &kanji_md7668, &kanji_md9B32, &kanji_md6E0A};
const reading_md onyomi_md0xc44de59e = {68, NULL, on_kanji0xc44de59e};
const kanji_md * const on_kanji0xf15aedc7[] = {&kanji_md845B};
const reading_md onyomi_md0xf15aedc7 = {1, NULL, on_kanji0xf15aedc7};
const kanji_md * const on_kanji0x342932c7[] = {&kanji_md5408, &kanji_md6070};
const reading_md onyomi_md0x342932c7 = {2, NULL, on_kanji0x342932c7};
const kanji_md * const on_kanji0xc01cd63e[] = {&kanji_md6D3B, &kanji_md5272, &kanji_md6ED1, &kanji_md559D, &kanji_md6E07, &kanji_md7B48, &kanji_md8910, &kanji_md845B, &kanji_md95CA, &kanji_md62EC, &kanji_md8F44, &kanji_md733E, &kanji_md62EE, &kanji_md6FF6, &kanji_md6B47, &kanji_md798A, &kanji_md874E, &kanji_md522E, &kanji_md8C41, &kanji_md880D, &kanji_md621B, &kanji_md621E, &kanji_md7FAF, &kanji_md86DE, &kanji_md9EE0, &kanji_md9821, &kanji_md9DBB, &kanji_md97A8, &kanji_md66F7, &kanji_md778E, &kanji_md63E9, &kanji_md78C6};
const reading_md onyomi_md0xc01cd63e = {32, NULL, on_kanji0xc01cd63e};
const kanji_md * const on_kanji0x10fe7ab7[] = {&kanji_md9593, &kanji_md611F, &kanji_md95A2, &kanji_md5DFB, &kanji_md89B3, &kanji_md5B8C, &kanji_md7C21, &kanji_md7518, &kanji_md6163, &kanji_md5BD2, &kanji_md6C57, &kanji_md7532, &kanji_md7BA1, &kanji_md5B98, &kanji_md63DB, &kanji_md9928, &kanji_md52D8, &kanji_md4E7E, &kanji_md5E72, &kanji_md6B53, &kanji_md770B, &kanji_md76E3, &kanji_md8CAB, &kanji_md809D, &kanji_md74B0, &kanji_md520A, &kanji_md9665, &kanji_md5E79, &kanji_md6F22, &kanji_md582A, &kanji_md52E7, &kanji_md7DE9, &kanji_md9084, &kanji_md9451, &kanji_md60A3, &kanji_md6562, &kanji_md559A, &kanji_md5BDB, &kanji_md9591, &kanji_md7729, &kanji_md51A0, &kanji_md7F36, &kanji_md9837, &kanji_md68FA, &kanji_md8266, &kanji_md6ABB, &kanji_md7647, &kanji_md7AFF, &kanji_md608D, &kanji_md59E6, &kanji_md4E32, &kanji_md5D4C, &kanji_md704C, &kanji_md61BE, &kanji_md51FD, &kanji_md9E78, &kanji_md5978, &kanji_md97D3, &kanji_md83C5, &kanji_md8AEB, &kanji_md9F3E, &kanji_md7F50, &kanji_md67D1, &kanji_md71D7, &kanji_md65A1, &kanji_md77B0, &kanji_md4E98, &kanji_md8271, &kanji_md64BC, &kanji_md76E5, &kanji_md7DB8, &kanji_md7FB9, &kanji_md6173, &kanji_md687F, &kanji_md65F1, &kanji_md558A, &kanji_md839E, &kanji_md5769, &kanji_md9F95, &kanji_md6B3E, &kanji_md929C, &kanji_md7FF0, &kanji_md9921, &kanji_md8ACC, &kanji_md7156, &kanji_md7B9D, &kanji_md75B3, &kanji_md7DD8, &kanji_md681E, &kanji_md5BA6, &kanji_md4E99, &kanji_md6F45, &kanji_md7165, &kanji_md6853, &kanji_md9475, &kanji_md54B8, &kanji_md6DB5, &kanji_md9051, &kanji_md6A44, &kanji_md6D63, &kanji_md9163, &kanji_md9874, &kanji_md4F83, &kanji_md5563, &kanji_md839F, &kanji_md9E79, &kanji_md9257, &kanji_md6F97, &kanji_md9436, &kanji_md701A, &kanji_md8218, &kanji_md6E19, &kanji_md90AF, &kanji_md51F5, &kanji_md9C25, &kanji_md6746, &kanji_md7A08, &kanji_md99FB, &kanji_md7BCF, &kanji_md6E72, &kanji_md9E1B, &kanji_md7F55, &kanji_md5950, &kanji_md9452, &kanji_md574E, &kanji_md7FAE, &kanji_md7E5D, &kanji_md5377, &kanji_md89C0, &kanji_md5BF0, &kanji_md6B61, &kanji_md67EC, &kanji_md571C, &kanji_md95DC, &kanji_md9B1F, &kanji_md7696, &kanji_md8484, &kanji_md9677, &kanji_md51FE, &kanji_md6221, &kanji_md8F57, &kanji_md63C0, &kanji_md6FA3, &kanji_md5382, &kanji_md6DE6, &kanji_md9A69, &kanji_md8B99, &kanji_md86B6, &kanji_md625E, &kanji_md5AFA, &kanji_md52F8, &kanji_md7147, &kanji_md5AFB, &kanji_md8C62, &kanji_md6B49, &kanji_md5BEC, &kanji_md61FD, &kanji_md9210, &kanji_md9AAD};
const reading_md onyomi_md0x10fe7ab7 = {159, NULL, on_kanji0x10fe7ab7};
const kanji_md * const on_kanji0x35a7dc1b[] = {&kanji_md753B, &kanji_md6211, &kanji_md590F, &kanji_md96C5, &kanji_md82BD, &kanji_md7259, &kanji_md74E6, &kanji_md8A1D, &kanji_md8CC0, &kanji_md9913, &kanji_md81E5, &kanji_md4FC4, &kanji_md99D5, &kanji_md4F3D, &kanji_md86FE, &kanji_md5CE8, &kanji_md9D5E, &kanji_md59DC, &kanji_md8859, &kanji_md5A25, &kanji_md9D5D, &kanji_md5440, &kanji_md7912, &kanji_md5CE9, &kanji_md756B, &kanji_md83AA};
const reading_md onyomi_md0x35a7dc1b = {26, NULL, on_kanji0x35a7dc1b};
const kanji_md * const on_kanji0x9e2daa6a[] = {&kanji_md5916, &kanji_md5BB3, &kanji_md8857, &kanji_md84CB, &kanji_md6DAF, &kanji_md9AB8, &kanji_md6168, &kanji_md54B3, &kanji_md6982, &kanji_md5208, &kanji_md5D16, &kanji_md93A7, &kanji_md8A72, &kanji_md51F1, &kanji_md52BE, &kanji_md613E, &kanji_md788D, &kanji_md4EA5, &kanji_md8C48, &kanji_md6F11, &kanji_md502A, &kanji_md99ED, &kanji_md82C5, &kanji_md5D14, &kanji_md7919, &kanji_md5540, &kanji_md5B69, &kanji_md769A, &kanji_md5793, &kanji_md9BA0, &kanji_md5D15, &kanji_md8462, &kanji_md69BF, &kanji_md775A, &kanji_md78D1, &kanji_md5274, &kanji_md76D6, &kanji_md9857, &kanji_md4E42};
const reading_md onyomi_md0x9e2daa6a = {39, NULL, on_kanji0x9e2daa6a};
const kanji_md * const on_kanji0x14073d61[] = {&kanji_md697D, &kanji_md5B66, &kanji_md984D, &kanji_md984E, &kanji_md6115, &kanji_md5CB3, &kanji_md9354, &kanji_md9C10, &kanji_md5DBD, &kanji_md7627, &kanji_md5B78, &kanji_md8AE4, &kanji_md843C, &kanji_md6A02, &kanji_md54A2, &kanji_md58D1, &kanji_md855A, &kanji_md9D9A, &kanji_md9102, &kanji_md9F76};
const reading_md onyomi_md0x14073d61 = {20, NULL, on_kanji0x14073d61};
const kanji_md * const on_kanji0x6e600f10[] = {&kanji_md97A8, &kanji_md6B79, &kanji_md8ECF};
const reading_md onyomi_md0x6e600f10 = {3, NULL, on_kanji0x6e600f10};
const kanji_md * const on_kanji0xdadb3b4c[] = {&kanji_md5408};
const reading_md onyomi_md0xdadb3b4c = {1, NULL, on_kanji0xdadb3b4c};
const kanji_md * const on_kanji0xa3b1085[] = {&kanji_md6708, &kanji_md6B79};
const reading_md onyomi_md0xa3b1085 = {2, NULL, on_kanji0xa3b1085};
const kanji_md * const on_kanji0x12290763[] = {&kanji_md9854, &kanji_md5143, &kanji_md9858, &kanji_md773C, &kanji_md4E38, &kanji_md542B, &kanji_md9811, &kanji_md5CB8, &kanji_md5CA9, &kanji_md9837, &kanji_md73A9, &kanji_md96C1, &kanji_md5DCC, &kanji_md764C, &kanji_md8D0B, &kanji_md9F95, &kanji_md7FEB, &kanji_md839F, &kanji_md5DD6, &kanji_md9D08, &kanji_md984F, &kanji_md5050, &kanji_md72E0, &kanji_md5D52};
const reading_md onyomi_md0x12290763 = {24, NULL, on_kanji0x12290763};
const kanji_md * const on_kanji0x766bd2aa[] = {&kanji_md6C17, &kanji_md8D77, &kanji_md8A18, &kanji_md6A5F, &kanji_md5E30, &kanji_md5BC4, &kanji_md671F, &kanji_md5668, &kanji_md5947, &kanji_md5371, &kanji_md559C, &kanji_md8CB4, &kanji_md8F1D, &kanji_md866B, &kanji_md808C, &kanji_md898F, &kanji_md57FA, &kanji_md5E0C, &kanji_md5DF1, &kanji_md7948, &kanji_md673A, &kanji_md9B3C, &kanji_md5E7E, &kanji_md4F01, &kanji_md63EE, &kanji_md5B09, &kanji_md5B63, &kanji_md7D00, &kanji_md68C4, &kanji_md72A0, &kanji_md65D7, &kanji_md5FCC, &kanji_md65E2, &kanji_md98E2, &kanji_md5D0E, &kanji_md59EB, &kanji_md4E5E, &kanji_md4E80, &kanji_md9A0E, &kanji_md7A00, &kanji_md8ECC, &kanji_md7DBA, &kanji_md7ABA, &kanji_md5C90, &kanji_md6C7D, &kanji_md6BC5, &kanji_md51E0, &kanji_md60B8, &kanji_md78EF, &kanji_md5176, &kanji_md68CB, &kanji_md4F0E, &kanji_md8DEA, &kanji_md5C53, &kanji_md6BC0, &kanji_md5993, &kanji_md57FC, &kanji_md675E, &kanji_md8A6D, &kanji_md6AC3, &kanji_md8475, &kanji_md7947, &kanji_md54A5, &kanji_md9EBE, &kanji_md757F, &kanji_md9C2D, &kanji_md6127, &kanji_md9BA8, &kanji_md613E, &kanji_md63C6, &kanji_md69FB, &kanji_md5FBD, &kanji_md501A, &kanji_md8C48, &kanji_md7B95, &kanji_md9E92, &kanji_md8006, &kanji_md7578, &kanji_md7F88, &kanji_md87F2, &kanji_md9951, &kanji_md9BAA, &kanji_md8667, &kanji_md8AF1, &kanji_md7155, &kanji_md8B4F, &kanji_md5180, &kanji_md858A, &kanji_md6B39, &kanji_md5C4E, &kanji_md9A65, &kanji_md9997, &kanji_md7678, &kanji_md6B37, &kanji_md6689, &kanji_md594E, &kanji_md77B6, &kanji_md898A, &kanji_md5349, &kanji_md67B3, &kanji_md7199, &kanji_md9A0F, &kanji_md7C23, &kanji_md7FB2, &kanji_md9035, &kanji_md6C23, &kanji_md79A7, &kanji_md6C82, &kanji_md7941, &kanji_md7895, &kanji_md71B9, &kanji_md797A, &kanji_md6B78, &kanji_md7F87, &kanji_md7188, &kanji_md9F9C, &kanji_md68CA, &kanji_md6DC7, &kanji_md71EC, &kanji_md7688, &kanji_md50D6, &kanji_md638E, &kanji_md4E9F, &kanji_md5E43, &kanji_md65E1, &kanji_md994B, &kanji_md550F, &kanji_md5331, &kanji_md66C1, &kanji_md5D5C, &kanji_md573B, &kanji_md72A7, &kanji_md7C4F, &kanji_md559F, &kanji_md89AC, &kanji_md7426, &kanji_md665E, &kanji_md7147, &kanji_md6199, &kanji_md9321, &kanji_md742A, &kanji_md5F03, &kanji_md6C14, &kanji_md525E, &kanji_md6615, &kanji_md66E6, &kanji_md671E, &kanji_md8DC2};
const reading_md onyomi_md0x766bd2aa = {148, NULL, on_kanji0x766bd2aa};
const kanji_md * const on_kanji0x9ae03c0b[] = {&kanji_md7825};
const reading_md onyomi_md0x9ae03c0b = {1, NULL, on_kanji0x9ae03c0b};
const kanji_md * const on_kanji0xad29b67a[] = {&kanji_md83CA, &kanji_md63AC, &kanji_md9EB9, &kanji_md97A0, &kanji_md6908, &kanji_md97AB};
const reading_md onyomi_md0xad29b67a = {6, NULL, on_kanji0xad29b67a};
const kanji_md * const on_kanji0x642bb4a7[] = {&kanji_md4E5E};
const reading_md onyomi_md0x642bb4a7 = {1, NULL, on_kanji0x642bb4a7};
const kanji_md * const on_kanji0x2b475717[] = {&kanji_md8A70, &kanji_md5409, &kanji_md4F76};
const reading_md onyomi_md0x2b475717 = {3, NULL, on_kanji0x2b475717};
const kanji_md * const on_kanji0x8a2d79d[] = {&kanji_md8A70, &kanji_md5409, &kanji_md55AB, &kanji_md4E5E, &kanji_md5C79, &kanji_md5403, &kanji_md6A58, &kanji_md8FC4, &kanji_md62EE, &kanji_md613E, &kanji_md6854, &kanji_md9AFB, &kanji_md4F76, &kanji_md8B4E, &kanji_md8A16, &kanji_md9821};
const reading_md onyomi_md0x8a2d79d = {16, NULL, on_kanji0x8a2d79d};
const kanji_md * const on_kanji0x4e53f058[] = {&kanji_md811A, &kanji_md4F3D};
const reading_md onyomi_md0x4e53f058 = {2, NULL, on_kanji0x4e53f058};
const kanji_md * const on_kanji0x30d6b2e8[] = {&kanji_md683C, &kanji_md5BA2, &kanji_md811A, &kanji_md9699, &kanji_md5374, &kanji_md8B14, &kanji_md537B, &kanji_md7845, &kanji_md90E4, &kanji_md9481};
const reading_md onyomi_md0x30d6b2e8 = {10, NULL, on_kanji0x30d6b2e8};
const kanji_md * const on_kanji0xbfc4856a[] = {&kanji_md6025, &kanji_md4F11, &kanji_md6C42, &kanji_md6CE3, &kanji_md5438, &kanji_md4E5D, &kanji_md4E45, &kanji_md6551, &kanji_md7D1A, &kanji_md53CA, &kanji_md6271, &kanji_md7D66, &kanji_md5BAE, &kanji_md7403, &kanji_md7A76, &kanji_md65E7, &kanji_md7AAE, &kanji_md4E18, &kanji_md55C5, &kanji_md4E80, &kanji_md5F13, &kanji_md4EC7, &kanji_md6C72, &kanji_md548E, &kanji_md673D, &kanji_md9CE9, &kanji_md7CFE, &kanji_md81FC, &kanji_md53A9, &kanji_md67E9, &kanji_md8205, &kanji_md7CFA, &kanji_md7078, &kanji_md97A0, &kanji_md6BEC, &kanji_md7A79, &kanji_md759A, &kanji_md97EE, &kanji_md86AF, &kanji_md8EAC, &kanji_md7B08, &kanji_md7396, &kanji_md90B1, &kanji_md5ED0, &kanji_md88D8, &kanji_md8D73, &kanji_md5ECF, &kanji_md7FD5, &kanji_md9B2E, &kanji_md820A, &kanji_md9F9C, &kanji_md7E46, &kanji_md8C85, &kanji_md7680, &kanji_md9011, &kanji_md6A1B, &kanji_md6B59, &kanji_md644E};
const reading_md onyomi_md0xbfc4856a = {58, NULL, on_kanji0xbfc4856a};
const kanji_md * const on_kanji0x6ae8ffd9[] = {&kanji_md53BB, &kanji_md5C45, &kanji_md8A31, &kanji_md62E0, &kanji_md6319, &kanji_md8DDD, &kanji_md5DE8, &kanji_md5618, &kanji_md865A, &kanji_md62D2, &kanji_md636E, &kanji_md88FE, &kanji_md589F, &kanji_md907D, &kanji_md92F8, &kanji_md70AC, &kanji_md6B05, &kanji_md6E20, &kanji_md8E1E, &kanji_md7B65, &kanji_md6B54, &kanji_md5028, &kanji_md91B5, &kanji_md82E3, &kanji_md9245, &kanji_md64DA, &kanji_md64E7, &kanji_md79EC};
const reading_md onyomi_md0x6ae8ffd9 = {28, NULL, on_kanji0x6ae8ffd9};
const kanji_md * const on_kanji0xed0741aa[] = {&kanji_md5F37, &kanji_md6559, &kanji_md7D4C, &kanji_md6050, &kanji_md80F8, &kanji_md7D9A, &kanji_md8EFD, &kanji_md8208, &kanji_md4F9B, &kanji_md9A5A, &kanji_md97FF, &kanji_md5171, &kanji_md53EB, &kanji_md5883, &kanji_md72C2, &kanji_md6821, &kanji_md93E1, &kanji_md5144, &kanji_md982C, &kanji_md9999, &kanji_md656C, &kanji_md72ED, &kanji_md9803, &kanji_md6CC1, &kanji_md5354, &kanji_md8107, &kanji_md6A4B, &kanji_md4EAC, &kanji_md90F7, &kanji_md8105, &kanji_md7AF6, &kanji_md602F, &kanji_md7AAE, &kanji_md51F6, &kanji_md631F, &kanji_md6070, &kanji_md5B5D, &kanji_md53F6, &kanji_md52AB, &kanji_md5B0C, &kanji_md6681, &kanji_md4EAB, &kanji_md72E1, &kanji_md65FA, &kanji_md606D, &kanji_md830E, &kanji_md537F, &kanji_md5CE1, &kanji_md622E, &kanji_md77EF, &kanji_md674F, &kanji_md5147, &kanji_md92CF, &kanji_md9957, &kanji_md4FA0, &kanji_md9A55, &kanji_md81A0, &kanji_md854E, &kanji_md50E5, &kanji_md6897, &kanji_md689F, &kanji_md77DC, &kanji_md6493, &kanji_md70AF, &kanji_md83A2, &kanji_md6846, &kanji_md7ADF, &kanji_md55AC, &kanji_md62F1, &kanji_md593E, &kanji_md88B7, &kanji_md7A79, &kanji_md8DEB, &kanji_md59DC, &kanji_md8A91, &kanji_md633E, &kanji_md99A8, &kanji_md6A47, &kanji_md5162, &kanji_md7B50, &kanji_md768E, &kanji_md56C2, &kanji_md4EA8, &kanji_md9903, &kanji_md5321, &kanji_md8D99, &kanji_md50D1, &kanji_md8EAC, &kanji_md9A4D, &kanji_md8941, &kanji_md56AE, &kanji_md978F, &kanji_md7A96, &kanji_md605F, &kanji_md8F4E, &kanji_md6A7F, &kanji_md7586, &kanji_md86DF, &kanji_md5308, &kanji_md70F1, &kanji_md614A, &kanji_md8591, &kanji_md51B5, &kanji_md5F4A, &kanji_md7E8C, &kanji_md4F7C, &kanji_md7B7A, &kanji_md531D, &kanji_md7BCB, &kanji_md50F5, &kanji_md7F8C, &kanji_md66C9, &kanji_md7AC5, &kanji_md78FD, &kanji_md7D93, &kanji_md965C, &kanji_md7680, &kanji_md72F9, &kanji_md5EFE, &kanji_md749F, &kanji_md5CFD, &kanji_md86E9, &kanji_md6D36, &kanji_md6B59, &kanji_md518F, &kanji_md7E66, &kanji_md5182, &kanji_md604A, &kanji_md6282, &kanji_md754A, &kanji_md91D7, &kanji_md4EB0, &kanji_md5227, &kanji_md57AC, &kanji_md5FBC, &kanji_md7AF8, &kanji_md7B74, &kanji_md8396, &kanji_md9830};
const reading_md onyomi_md0xed0741aa = {139, NULL, on_kanji0xed0741aa};
const kanji_md * const on_kanji0x9ab0fc2c[] = {&kanji_md5C40, &kanji_md6975, &kanji_md66F2, &kanji_md68D8, &kanji_md65ED, &kanji_md9AF7, &kanji_md9998, &kanji_md95BE, &kanji_md8DFC, &kanji_md8540, &kanji_md8195, &kanji_md4E9F, &kanji_md52D7, &kanji_md6D2B};
const reading_md onyomi_md0x9ab0fc2c = {14, NULL, on_kanji0x9ab0fc2c};
const kanji_md * const on_kanji0xf9d9f1c8[] = {&kanji_md8FD1, &kanji_md4ECA, &kanji_md91D1, &kanji_md7D4C, &kanji_md8EFD, &kanji_md7B4B, &kanji_md7DCA, &kanji_md7981, &kanji_md52E4, &kanji_md4EAC, &kanji_md8A13, &kanji_md895F, &kanji_md5747, &kanji_md4E80, &kanji_md5DFE, &kanji_md8B39, &kanji_md50C5, &kanji_md7434, &kanji_md9326, &kanji_md83CC, &kanji_md61C3, &kanji_md79BD, &kanji_md6A8E, &kanji_md6B23, &kanji_md5664, &kanji_md887F, &kanji_md77DC, &kanji_md9949, &kanji_md8171, &kanji_md887E, &kanji_md83EB, &kanji_md65A4, &kanji_md6B3D, &kanji_md7A98, &kanji_md82B9, &kanji_md747E, &kanji_md64D2, &kanji_md921E, &kanji_md89B2, &kanji_md69FF, &kanji_md76B9, &kanji_md76B8, &kanji_md9ED4, &kanji_md9F9C, &kanji_md6380, &kanji_md6196, &kanji_md542C, &kanji_md91FF, &kanji_md91C1, &kanji_md9E95, &kanji_md4EB0, &kanji_md7B9F, &kanji_md5FFB, &kanji_md6615};
const reading_md onyomi_md0xf9d9f1c8 = {54, NULL, on_kanji0xf9d9f1c8};
const kanji_md * const on_kanji0x2a77a704[] = {&kanji_md8B70, &kanji_md7591, &kanji_md7FA9, &kanji_md5100, &kanji_md6280, &kanji_md507D, &kanji_md72A0, &kanji_md622F, &kanji_md6B3A, &kanji_md5D16, &kanji_md5B9C, &kanji_md5C90, &kanji_md64EC, &kanji_md6BC5, &kanji_md87FB, &kanji_md5176, &kanji_md4F0E, &kanji_md5993, &kanji_md86FE, &kanji_md7947, &kanji_md8ABC, &kanji_md9C2D, &kanji_md9B4F, &kanji_md8264, &kanji_md5DCD, &kanji_md769A, &kanji_md7FB2, &kanji_md5D6C, &kanji_md6C82, &kanji_md7912, &kanji_md6232, &kanji_md50DE, &kanji_md72A7, &kanji_md5DB7, &kanji_md9857, &kanji_md66E6, &kanji_md8413};
const reading_md onyomi_md0x2a77a704 = {37, NULL, on_kanji0x2a77a704};
const kanji_md * const on_kanji0xfff4a3ac[] = {&kanji_md4F3D};
const reading_md onyomi_md0xfff4a3ac = {1, NULL, on_kanji0xfff4a3ac};
const kanji_md * const on_kanji0x2e5f5866[] = {&kanji_md9006, &kanji_md8650, &kanji_md8B14, &kanji_md7627};
const reading_md onyomi_md0x2e5f5866 = {4, NULL, on_kanji0x2e5f5866};
const kanji_md * const on_kanji0x10ad1409[] = {&kanji_md725B};
const reading_md onyomi_md0x10ad1409 = {1, NULL, on_kanji0x10ad1409};
const kanji_md * const on_kanji0x7b9d741d[] = {&kanji_md5FA1, &kanji_md9B5A, &kanji_md6F01, &kanji_md79A6, &kanji_md99AD, &kanji_md8859, &kanji_md5704, &kanji_md5709};
const reading_md onyomi_md0x7b9d741d = {8, NULL, on_kanji0x7b9d741d};
const kanji_md * const on_kanji0xbe163cdb[] = {&kanji_md884C, &kanji_md5F62, &kanji_md696D, &kanji_md4EF0, &kanji_md51DD, &kanji_md6681, &kanji_md50E5, &kanji_md9903, &kanji_md9A4D, &kanji_md582F, &kanji_md7FF9, &kanji_md5C2D, &kanji_md6F86, &kanji_md66C9, &kanji_md723B, &kanji_md8FE5, &kanji_md87EF};
const reading_md onyomi_md0xbe163cdb = {17, NULL, on_kanji0xbe163cdb};
const kanji_md * const on_kanji0x56e049b6[] = {&kanji_md7389, &kanji_md5DB7, &kanji_md95A0};
const reading_md onyomi_md0x56e049b6 = {3, NULL, on_kanji0x56e049b6};
const kanji_md * const on_kanji0x58cc3645[] = {&kanji_md9280, &kanji_md541F, &kanji_md5C91, &kanji_md6C82, &kanji_md9F66, &kanji_md6196, &kanji_md57A0, &kanji_md5F88, &kanji_md573B, &kanji_md5D1F, &kanji_md8ABE};
const reading_md onyomi_md0x58cc3645 = {11, NULL, on_kanji0x58cc3645};
const kanji_md * const on_kanji0x892a60b0[] = {&kanji_md53E3, &kanji_md82E6, &kanji_md4F9B, &kanji_md516C, &kanji_md4E5D, &kanji_md53E5, &kanji_md5DE5, &kanji_md4E45, &kanji_md99C6, &kanji_md5EAB, &kanji_md533A, &kanji_md529F, &kanji_md7D05, &kanji_md5BAE, &kanji_md7A76, &kanji_md57A2, &kanji_md5B54, &kanji_md99D2, &kanji_md9CE9, &kanji_md8CA2, &kanji_md8EAF, &kanji_md60E7, &kanji_md99C8, &kanji_md88B4, &kanji_md622E, &kanji_md5614, &kanji_md9264, &kanji_md52FE, &kanji_md72D7, &kanji_md5036, &kanji_md543C, &kanji_md61FC, &kanji_md7078, &kanji_md77E9, &kanji_md7AB6, &kanji_md920E, &kanji_md97EE, &kanji_md8862, &kanji_md91E6, &kanji_md82DF, &kanji_md98B6, &kanji_md849F, &kanji_md4E8E, &kanji_md7396, &kanji_md5340, &kanji_md5D87, &kanji_md50B4, &kanji_md4F5D, &kanji_md5D0B, &kanji_md5401, &kanji_md52AC, &kanji_md9F72, &kanji_md67B8, &kanji_md77BF, &kanji_md9A45, &kanji_md5EFE, &kanji_md7B9C, &kanji_md7166, &kanji_md6829, &kanji_md644E, &kanji_md91ED, &kanji_md6998};
const reading_md onyomi_md0x892a60b0 = {62, NULL, on_kanji0x892a60b0};
const kanji_md * const on_kanji0xd55b5d7c[] = {&kanji_md7A7A, &kanji_md4F9B, &kanji_md5BAE, &kanji_md54BC};
const reading_md onyomi_md0xd55b5d7c = {4, NULL, on_kanji0xd55b5d7c};
const kanji_md * const on_kanji0x2ff84bd1[] = {&kanji_md99A5};
const reading_md onyomi_md0x2ff84bd1 = {1, NULL, on_kanji0x2ff84bd1};
const kanji_md * const on_kanji0xb2a37fd9[] = {&kanji_md5C48, &kanji_md6398, &kanji_md7A9F, &kanji_md5800, &kanji_md53A5, &kanji_md5D1B, &kanji_md5014};
const reading_md onyomi_md0xb2a37fd9 = {7, NULL, on_kanji0xb2a37fd9};
const kanji_md * const on_kanji0x3534ea68[] = {&kanji_md5F8A};
const reading_md onyomi_md0x3534ea68 = {1, NULL, on_kanji0x3534ea68};
const kanji_md * const on_kanji0x8148bed8[] = {&kanji_md541B, &kanji_md8A13, &kanji_md99B4, &kanji_md52F2, &kanji_md85AB, &kanji_md71FB, &kanji_md88D9, &kanji_md91BA, &kanji_md76B9, &kanji_md8477, &kanji_md76B8, &kanji_md52F3, &kanji_md718F, &kanji_md9E95, &kanji_md52DB, &kanji_md7147, &kanji_md85B0};
const reading_md onyomi_md0x8148bed8 = {17, NULL, on_kanji0x8148bed8};
const kanji_md * const on_kanji0x572e35df[] = {&kanji_md5177, &kanji_md4F9B, &kanji_md6C42, &kanji_md5DE5, &kanji_md611A, &kanji_md4EC7, &kanji_md60E7, &kanji_md5F18, &kanji_md5036, &kanji_md81FC, &kanji_md5BD3, &kanji_md67E9, &kanji_md9B28, &kanji_md865E, &kanji_md98B6, &kanji_md543D, &kanji_md88D8, &kanji_md79BA, &kanji_md85D5, &kanji_md5D4E, &kanji_md9277};
const reading_md onyomi_md0x572e35df = {21, NULL, on_kanji0x572e35df};
const kanji_md * const on_kanji0xcff5c4e9[] = {&kanji_md9685, &kanji_md5076, &kanji_md5BAE, &kanji_md9047, &kanji_md5BD3, &kanji_md79BA, &kanji_md85D5, &kanji_md5D4E};
const reading_md onyomi_md0xcff5c4e9 = {8, NULL, on_kanji0xcff5c4e9};
const kanji_md * const on_kanji0x6bd0f97b[] = {&kanji_md7FA4, &kanji_md8ECD, &kanji_md90E1, &kanji_md7FA3};
const reading_md onyomi_md0x6bd0f97b = {4, NULL, on_kanji0x6bd0f97b};
const kanji_md * const on_kanji0x98b0a259[] = {&kanji_md6C17, &kanji_md5BB6, &kanji_md5316, &kanji_md82B1, &kanji_md602A, &kanji_md4FA1, &kanji_md83EF, &kanji_md4EEE, &kanji_md5E0C, &kanji_md61F8, &kanji_md5629, &kanji_md584A, &kanji_md7A00, &kanji_md8888, &kanji_md74DC, &kanji_md82A5, &kanji_md8FE6, &kanji_md95A8, &kanji_md6062, &kanji_md572D, &kanji_md613E, &kanji_md5366, &kanji_md7F45, &kanji_md81BE, &kanji_md7F6B, &kanji_md61C8, &kanji_md858A, &kanji_md5349, &kanji_md6302, &kanji_md9C60, &kanji_md6C23, &kanji_md7941, &kanji_md5047, &kanji_md6060, &kanji_md75C2, &kanji_md54BC, &kanji_md4E9F, &kanji_md65E1, &kanji_md50F9, &kanji_md8902, &kanji_md5EE8, &kanji_md8B41, &kanji_md6C14};
const reading_md onyomi_md0x98b0a259 = {43, NULL, on_kanji0x98b0a259};
const kanji_md * const on_kanji0x6c8092b[] = {&kanji_md5F62, &kanji_md7D4C, &kanji_md8A08, &kanji_md8EFD, &kanji_md4FC2, &kanji_md666F, &kanji_md5883, &kanji_md578B, &kanji_md8B66, &kanji_md50BE, &kanji_md639B, &kanji_md93E1, &kanji_md5144, &kanji_md656C, &kanji_md9803, &kanji_md6075, &kanji_md7D99, &kanji_md4EAC, &kanji_md7CFB, &kanji_md5211, &kanji_md7AF6, &kanji_md63B2, &kanji_md643A, &kanji_md7A3D, &kanji_md5951, &kanji_md5F84, &kanji_md7E4B, &kanji_md61A9, &kanji_md9D8F, &kanji_md75D9, &kanji_md5553, &kanji_md6176, &kanji_md9838, &kanji_md86CD, &kanji_md8A63, &kanji_md830E, &kanji_md537F, &kanji_md811B, &kanji_md6E13, &kanji_md6842, &kanji_md6167, &kanji_md61AC, &kanji_md95A8, &kanji_md9BAD, &kanji_md572D, &kanji_md77DC, &kanji_md70AF, &kanji_md5F57, &kanji_md7ADF, &kanji_md7566, &kanji_md52C1, &kanji_md87A2, &kanji_md99A8, &kanji_md981A, &kanji_md834A, &kanji_md798A, &kanji_md9AFB, &kanji_md74CA, &kanji_md7B04, &kanji_md7F6B, &kanji_md8E76, &kanji_md73EA, &kanji_md8C3F, &kanji_md5048, &kanji_md858A, &kanji_md8E4A, &kanji_md594E, &kanji_md88BF, &kanji_md595A, &kanji_md6AA0, &kanji_md70F1, &kanji_md6EAA, &kanji_md78EC, &kanji_md7DAE, &kanji_md6302, &kanji_md8B26, &kanji_md60E0, &kanji_md7845, &kanji_md9015, &kanji_md516E, &kanji_md5244, &kanji_md9EE5, &kanji_md7724, &kanji_md9DC4, &kanji_md7D93, &kanji_md5F91, &kanji_md7D45, &kanji_md9288, &kanji_md9D03, &kanji_md749F, &kanji_md8FE5, &kanji_md8F15, &kanji_md76FB, &kanji_md7162, &kanji_md8902, &kanji_md518F, &kanji_md5F51, &kanji_md7E7C, &kanji_md5182, &kanji_md6308, &kanji_md91AF, &kanji_md95A0, &kanji_md4EB0, &kanji_md5338, &kanji_md651C, &kanji_md7AF8, &kanji_md8396, &kanji_md8559};
const reading_md onyomi_md0x6c8092b = {108, NULL, on_kanji0x6c8092b};
const kanji_md * const on_kanji0x3720555f[] = {&kanji_md9699, &kanji_md6A84, &kanji_md9B29, &kanji_md95C3, &kanji_md9D59, &kanji_md89A1, &kanji_md90E4, &kanji_md9D03, &kanji_md5C50};
const reading_md onyomi_md0x3720555f = {9, NULL, on_kanji0x3720555f};
const kanji_md * const on_kanji0x3e8eec2[] = {&kanji_md7D50, &kanji_md7E88, &kanji_md9821, &kanji_md51B3, &kanji_md592C};
const reading_md onyomi_md0x3e8eec2 = {5, NULL, on_kanji0x3e8eec2};
const kanji_md * const on_kanji0x89f7559a[] = {&kanji_md7D50, &kanji_md6C7A, &kanji_md8840, &kanji_md6B20, &kanji_md7A74, &kanji_md6F54, &kanji_md5091, &kanji_md9801, &kanji_md8882, &kanji_md8A23, &kanji_md6289, &kanji_md9F67, &kanji_md62EE, &kanji_md6954, &kanji_md6854, &kanji_md6B47, &kanji_md56D3, &kanji_md8E76, &kanji_md95D5, &kanji_md8568, &kanji_md7357, &kanji_md5048, &kanji_md7FAF, &kanji_md7AED, &kanji_md53A5, &kanji_md8B4E, &kanji_md6840, &kanji_md7E88, &kanji_md7F3A, &kanji_md5B51, &kanji_md78A3, &kanji_md9821, &kanji_md9D03, &kanji_md6770, &kanji_md8988, &kanji_md8A10, &kanji_md9779, &kanji_md51B3, &kanji_md5214, &kanji_md6308, &kanji_md592C};
const reading_md onyomi_md0x89f7559a = {41, NULL, on_kanji0x89f7559a};
const kanji_md * const on_kanji0xf7efb7fd[] = {&kanji_md898B, &kanji_md9593, &kanji_md5DFB, &kanji_md80A9, &kanji_md4EF6, &kanji_md5ACC, &kanji_md5EFA, &kanji_md9A13, &kanji_md967A, &kanji_md7C21, &kanji_md6B20, &kanji_md6A29, &kanji_md5263, &kanji_md5065, &kanji_md72AC, &kanji_md691C, &kanji_md4E7E, &kanji_md9063, &kanji_md61F8, &kanji_md7814, &kanji_md9375, &kanji_md8ED2, &kanji_md55A7, &kanji_md5805, &kanji_md62F3, &kanji_md517C, &kanji_md8CE2, &kanji_md52E7, &kanji_md732E, &kanji_md770C, &kanji_md7D79, &kanji_md9855, &kanji_md72FD, &kanji_md5238, &kanji_md8B19, &kanji_md77BC, &kanji_md938C, &kanji_md570F, &kanji_md727D, &kanji_md61B2, &kanji_md5026, &kanji_md6372, &kanji_md59E6, &kanji_md4E32, &kanji_md9E78, &kanji_md8654, &kanji_md83C5, &kanji_md7D62, &kanji_md5039, &kanji_md786F, &kanji_md8171, &kanji_md7737, &kanji_md8271, &kanji_md8852, &kanji_md5DAE, &kanji_md9C39, &kanji_md6173, &kanji_md7E6D, &kanji_md8431, &kanji_md7156, &kanji_md7B9D, &kanji_md8B74, &kanji_md72F7, &kanji_md7B67, &kanji_md598D, &kanji_md9874, &kanji_md8706, &kanji_md9257, &kanji_md6F97, &kanji_md9D51, &kanji_md5708, &kanji_md8737, &kanji_md7F82, &kanji_md614A, &kanji_md5A1F, &kanji_md7F3A, &kanji_md7504, &kanji_md81C9, &kanji_md5294, &kanji_md9A2B, &kanji_md7E5D, &kanji_md7E23, &kanji_md5377, &kanji_md8E47, &kanji_md9ED4, &kanji_md6D93, &kanji_md67EC, &kanji_md5271, &kanji_md528D, &kanji_md6380, &kanji_md6106, &kanji_md5292, &kanji_md96AA, &kanji_md6B0A, &kanji_md986F, &kanji_md63C0, &kanji_md60D3, &kanji_md70AB, &kanji_md9A57, &kanji_md6AA2, &kanji_md6434, &kanji_md9249, &kanji_md8B99, &kanji_md84B9, &kanji_md737B, &kanji_md4FD4, &kanji_md52F8, &kanji_md7147, &kanji_md75C3, &kanji_md8AE0, &kanji_md8C62, &kanji_md6B49, &kanji_md92E7, &kanji_md7DA3, &kanji_md5109, &kanji_md6081, &kanji_md6684, &kanji_md9210};
const reading_md onyomi_md0xf7efb7fd = {118, NULL, on_kanji0xf7efb7fd};
const kanji_md * const on_kanji0xe22a9607[] = {&kanji_md4E0B, &kanji_md5916, &kanji_md89E3, &kanji_md590F, &kanji_md622F, &kanji_md7259, &kanji_md8A1D, &kanji_md5D16, &kanji_md971E, &kanji_md8766, &kanji_md788D, &kanji_md5048, &kanji_md7919, &kanji_md769A, &kanji_md9BA0, &kanji_md6232, &kanji_md9857, &kanji_md4E42, &kanji_md89E7};
const reading_md onyomi_md0xe22a9607 = {19, NULL, on_kanji0xe22a9607};
const kanji_md * const on_kanji0xc5ea6ec3[] = {&kanji_md8FCE, &kanji_md82B8, &kanji_md5150, &kanji_md7768, &kanji_md8A63, &kanji_md85DD, &kanji_md9BE8, &kanji_md502A, &kanji_md730A, &kanji_md56C8, &kanji_md827E, &kanji_md9713, &kanji_md5152, &kanji_md9EE5, &kanji_md8C8E, &kanji_md9E91};
const reading_md onyomi_md0xc5ea6ec3 = {16, NULL, on_kanji0xc5ea6ec3};
const kanji_md * const on_kanji0x5e0c532c[] = {&kanji_md9006, &kanji_md6FC0, &kanji_md6483, &kanji_md5287, &kanji_md9699, &kanji_md621F, &kanji_md9B29, &kanji_md95C3, &kanji_md9D59, &kanji_md89A1, &kanji_md90E4, &kanji_md9D03, &kanji_md5C50, &kanji_md9DC1};
const reading_md onyomi_md0x5e0c532c = {14, NULL, on_kanji0x5e0c532c};
const kanji_md * const on_kanji0x41029b77[] = {&kanji_md6770};
const reading_md onyomi_md0x41029b77 = {1, NULL, on_kanji0x41029b77};
const kanji_md * const on_kanji0x25f8703f[] = {&kanji_md6708, &kanji_md7DB4, &kanji_md9F67, &kanji_md56D3, &kanji_md8616, &kanji_md8ECF};
const reading_md onyomi_md0x25f8703f = {6, NULL, on_kanji0x25f8703f};
const kanji_md * const on_kanji0xfb5c0c9[] = {&kanji_md8A00, &kanji_md73FE, &kanji_md5143, &kanji_md539F, &kanji_md9650, &kanji_md5ACC, &kanji_md773C, &kanji_md9A13, &kanji_md53B3, &kanji_md6E1B, &kanji_md7384, &kanji_md6E90, &kanji_md5E7B, &kanji_md9019, &kanji_md62F3, &kanji_md545F, &kanji_md7729, &kanji_md5F66, &kanji_md5F26, &kanji_md8237, &kanji_md8AFA, &kanji_md786F, &kanji_md7D43, &kanji_md8852, &kanji_md54B8, &kanji_md513C, &kanji_md962E, &kanji_md613F, &kanji_md5050, &kanji_md56B4, &kanji_md5E7F, &kanji_md9A57, &kanji_md72E0, &kanji_md75C3};
const reading_md onyomi_md0xfb5c0c9 = {34, NULL, on_kanji0xfb5c0c9};
const kanji_md * const on_kanji0x18e7929e[] = {&kanji_md547C, &kanji_md53BB, &kanji_md53E4, &kanji_md5C45, &kanji_md6238, &kanji_md56FA, &kanji_md6545, &kanji_md500B, &kanji_md62E0, &kanji_md5EAB, &kanji_md8A87, &kanji_md5618, &kanji_md865A, &kanji_md5DF1, &kanji_md5B64, &kanji_md9F13, &kanji_md80A1, &kanji_md67AF, &kanji_md88FE, &kanji_md96C7, &kanji_md9867, &kanji_md6E56, &kanji_md864E, &kanji_md80E1, &kanji_md51B4, &kanji_md7B87, &kanji_md72D0, &kanji_md58FA, &kanji_md7CCA, &kanji_md61AE, &kanji_md5F27, &kanji_md88B4, &kanji_md59D1, &kanji_md8DE8, &kanji_md4E4E, &kanji_md6DB8, &kanji_md7425, &kanji_md92F8, &kanji_md70AC, &kanji_md675E, &kanji_md9190, &kanji_md745A, &kanji_md58F7, &kanji_md6248, &kanji_md8831, &kanji_md6019, &kanji_md8C3A, &kanji_md6CBD, &kanji_md8E1E, &kanji_md8F9C, &kanji_md83F0, &kanji_md5233, &kanji_md7B8D, &kanji_md54E5, &kanji_md6EF8, &kanji_md932E, &kanji_md75FC, &kanji_md8CC8, &kanji_md9237, &kanji_md5028, &kanji_md77BD, &kanji_md9D23, &kanji_md80EF, &kanji_md5471, &kanji_md8A41, &kanji_md86C4, &kanji_md846B, &kanji_md76B7, &kanji_md74E0, &kanji_md4F30, &kanji_md89DA, &kanji_md64DA, &kanji_md51B1, &kanji_md6C8D, &kanji_md6EEC, &kanji_md8774, &kanji_md4E2A, &kanji_md4E55, &kanji_md864D, &kanji_md992C, &kanji_md684D, &kanji_md695C, &kanji_md73D6};
const reading_md onyomi_md0x18e7929e = {83, NULL, on_kanji0x18e7929e};
const kanji_md * const on_kanji0xe4755ba8[] = {&kanji_md884C, &kanji_md5F8C, &kanji_md9AD8, &kanji_md53E3, &kanji_md8003, &kanji_md5411, &kanji_md597D, &kanji_md5149, &kanji_md5E83, &kanji_md683C, &kanji_md78BA, &kanji_md4EA4, &kanji_md7D9A, &kanji_md8208, &kanji_md5E78, &kanji_md964D, &kanji_md516C, &kanji_md69CB, &kanji_md8352, &kanji_md5DE5, &kanji_md6297, &kanji_md539A, &kanji_md52B9, &kanji_md4EF0, &kanji_md7532, &kanji_md6821, &kanji_md9EC4, &kanji_md533A, &kanji_md9999, &kanji_md529F, &kanji_md72ED, &kanji_md5C3B, &kanji_md7D05, &kanji_md653B, &kanji_md66F4, &kanji_md53E9, &kanji_md5019, &kanji_md565B, &kanji_md5589, &kanji_md786C, &kanji_md5EB7, &kanji_md63A7, &kanji_md8B1B, &kanji_md5DE7, &kanji_md84CB, &kanji_md7D5E, &kanji_md602F, &kanji_md8F03, &kanji_md6C5F, &kanji_md62E1, &kanji_md6E2F, &kanji_md7DB1, &kanji_md614C, &kanji_md9805, &kanji_md822A, &kanji_md5CA1, &kanji_md7A3F, &kanji_md6602, &kanji_md7687, &kanji_md90CA, &kanji_md6070, &kanji_md80AF, &kanji_md62D8, &kanji_md57A2, &kanji_md8F5F, &kanji_md5B54, &kanji_md6E9D, &kanji_md6DF5, &kanji_md548E, &kanji_md8CFC, &kanji_md5B5D, &kanji_md92FC, &kanji_md52AB, &kanji_md8CA2, &kanji_md7E1E, &kanji_md85C1, &kanji_md8017, &kanji_md8015, &kanji_md4EAB, &kanji_md9271, &kanji_md8861, &kanji_md72E1, &kanji_md6841, &kanji_md6052, &kanji_md6D2A, &kanji_md8679, &kanji_md5F18, &kanji_md604D, &kanji_md4FAF, &kanji_md5CE1, &kanji_md818F, &kanji_md7526, &kanji_md80B4, &kanji_md676D, &kanji_md714C, &kanji_md5DF7, &kanji_md5B8F, &kanji_md54EE, &kanji_md9264, &kanji_md52FE, &kanji_md8154, &kanji_md5FA8, &kanji_md5CAC, &kanji_md5E4C, &kanji_md72D7, &kanji_md6D69, &kanji_md674F, &kanji_md5016, &kanji_md54C4, &kanji_md543C, &kanji_md8292, &kanji_md6FE0, &kanji_md540E, &kanji_md58D5, &kanji_md80B1, &kanji_md652A, &kanji_md54AC, &kanji_md81A0, &kanji_md9175, &kanji_md5751, &kanji_md6897, &kanji_md6BEB, &kanji_md7CE0, &kanji_md9BAB, &kanji_md9005, &kanji_md6493, &kanji_md4E98, &kanji_md9B28, &kanji_md5477, &kanji_md809B, &kanji_md7BDD, &kanji_md777E, &kanji_md5D17, &kanji_md9D3B, &kanji_md62F1, &kanji_md7FB9, &kanji_md593E, &kanji_md66E0, &kanji_md88B7, &kanji_md6643, &kanji_md6572, &kanji_md95A4, &kanji_md7693, &kanji_md86E4, &kanji_md9D60, &kanji_md51F0, &kanji_md72CE, &kanji_md6DC6, &kanji_md5BC7, &kanji_md5E9A, &kanji_md6177, &kanji_md80F1, &kanji_md7CDF, &kanji_md768E, &kanji_md920E, &kanji_md80DB, &kanji_md4E99, &kanji_md4EA8, &kanji_md9903, &kanji_md8757, &kanji_md5ABE, &kanji_md60F6, &kanji_md93AC, &kanji_md76D2, &kanji_md64B9, &kanji_md4EA2, &kanji_md91E6, &kanji_md82DF, &kanji_md7D18, &kanji_md85A8, &kanji_md5686, &kanji_md9051, &kanji_md803F, &kanji_md56AE, &kanji_md7690, &kanji_md5EE3, &kanji_md5323, &kanji_md543D, &kanji_md5859, &kanji_md6634, &kanji_md89AF, &kanji_md7A96, &kanji_md5340, &kanji_md6E15, &kanji_md7292, &kanji_md8A0C, &kanji_md7334, &kanji_md86DF, &kanji_md9D7A, &kanji_md7D56, &kanji_md6046, &kanji_md9ECC, &kanji_md7BC1, &kanji_md86A3, &kanji_md69D3, &kanji_md9760, &kanji_md6D3D, &kanji_md8093, &kanji_md9598, &kanji_md6C5E, &kanji_md4F5D, &kanji_md8591, &kanji_md7926, &kanji_md80EF, &kanji_md509A, &kanji_md6263, &kanji_md9C47, &kanji_md5CAB, &kanji_md7D73, &kanji_md6537, &kanji_md7E8C, &kanji_md4F7C, &kanji_md865F, &kanji_md6667, &kanji_md51A6, &kanji_md6832, &kanji_md95D4, &kanji_md6D38, &kanji_md95A7, &kanji_md84BF, &kanji_md5AE6, &kanji_md67B8, &kanji_md7F94, &kanji_md7FAE, &kanji_md58D9, &kanji_md5025, &kanji_md968D, &kanji_md7D4E, &kanji_md7E90, &kanji_md660A, &kanji_md542D, &kanji_md93D7, &kanji_md9D3F, &kanji_md78FD, &kanji_md965C, &kanji_md7680, &kanji_md6772, &kanji_md72F9, &kanji_md7D4B, &kanji_md7CB3, &kanji_md5CFD, &kanji_md723B, &kanji_md4F09, &kanji_md768B, &kanji_md8462, &kanji_md8AA5, &kanji_md991D, &kanji_md6E5F, &kanji_md7B9C, &kanji_md7BCC, &kanji_md6548, &kanji_md625B, &kanji_md64F4, &kanji_md5F88, &kanji_md945B, &kanji_md66A0, &kanji_md6406, &kanji_md6E98, &kanji_md6EEC, &kanji_md76CD, &kanji_md783F, &kanji_md9865, &kanji_md68E1, &kanji_md6EC9, &kanji_md69C1, &kanji_md7C27, &kanji_md980F, &kanji_md9360, &kanji_md69F9, &kanji_md77FC, &kanji_md9C09, &kanji_md663F, &kanji_md6C86, &kanji_md754A, &kanji_md76D6, &kanji_md6644, &kanji_md91ED, &kanji_md5227, &kanji_md54FD, &kanji_md57AC, &kanji_md6760, &kanji_md690C, &kanji_md6B43, &kanji_md6E0A, &kanji_md73D6, &kanji_md9277};
const reading_md onyomi_md0xe4755ba8 = {286, NULL, on_kanji0xe4755ba8};
const kanji_md * const on_kanji0x2619c453[] = {&kanji_md9ED2, &kanji_md544A, &kanji_md53EF, &kanji_md56FD, &kanji_md523B, &kanji_md77F3, &kanji_md9177, &kanji_md8C37, &kanji_md6BBB, &kanji_md514B, &kanji_md6216, &kanji_md7A40, &kanji_md63AC, &kanji_md54ED, &kanji_md570B, &kanji_md9D60, &kanji_md524B, &kanji_md6BBC, &kanji_md688F, &kanji_md659B, &kanji_md5700, &kanji_md69F2, &kanji_md8F42, &kanji_md56D7, &kanji_md8195, &kanji_md5C05};
const reading_md onyomi_md0x2619c453 = {26, NULL, on_kanji0x2619c453};
const kanji_md * const on_kanji0xd3e7e8cd[] = {&kanji_md4E5E};
const reading_md onyomi_md0xd3e7e8cd = {1, NULL, on_kanji0xd3e7e8cd};
const kanji_md * const on_kanji0xd9f595f1[] = {&kanji_md9AA8, &kanji_md6ED1, &kanji_md60DA, &kanji_md4E5E, &kanji_md7A9F, &kanji_md5FFD, &kanji_md7CCA, &kanji_md7B0F, &kanji_md5140, &kanji_md69BE, &kanji_md6C68, &kanji_md9DBB};
const reading_md onyomi_md0xd9f595f1 = {12, NULL, on_kanji0xd9f595f1};
const kanji_md * const on_kanji0x64dce940[] = {&kanji_md8FD1, &kanji_md4ECA, &kanji_md91D1, &kanji_md6839, &kanji_md56F0, &kanji_md5EFA, &kanji_md6DF7, &kanji_md5A5A, &kanji_md6068, &kanji_md9B42, &kanji_md75D5, &kanji_md732E, &kanji_md61C7, &kanji_md7D3A, &kanji_md660F, &kanji_md6E3E, &kanji_md6606, &kanji_md68CD, &kanji_md67D1, &kanji_md6B23, &kanji_md887F, &kanji_md68B1, &kanji_md890C, &kanji_md58BE, &kanji_md5764, &kanji_md6EFE, &kanji_md6B3D, &kanji_md826E, &kanji_md8DDF, &kanji_md5D11, &kanji_md849F, &kanji_md58FC, &kanji_md711C, &kanji_md9C25, &kanji_md6EB7, &kanji_md889E, &kanji_md83CE, &kanji_md7DE1, &kanji_md9F66, &kanji_md8AE2, &kanji_md9BE4, &kanji_md743F, &kanji_md6083, &kanji_md8F57, &kanji_md5F88, &kanji_md6DE6, &kanji_md72E0, &kanji_md737B, &kanji_md9BC0, &kanji_md4E28, &kanji_md6615, &kanji_md9DA4};
const reading_md onyomi_md0x64dce940 = {52, NULL, on_kanji0x64dce940};
const kanji_md * const on_kanji0xf6b10d3c[] = {&kanji_md5F8C, &kanji_md8A9E, &kanji_md671F, &kanji_md4E94, &kanji_md964D, &kanji_md8B77, &kanji_md609F, &kanji_md4E92, &kanji_md5FA1, &kanji_md5348, &kanji_md8AA4, &kanji_md62D2, &kanji_md80E1, &kanji_md51B4, &kanji_md7CCA, &kanji_md543E, &kanji_md5449, &kanji_md5A2F, &kanji_md4F0D, &kanji_md5176, &kanji_md7881, &kanji_md540E, &kanji_md6A8E, &kanji_md9190, &kanji_md745A, &kanji_md79A6, &kanji_md9F6C, &kanji_md8323, &kanji_md68A7, &kanji_md8859, &kanji_md8708, &kanji_md6664, &kanji_md5704, &kanji_md5BE4, &kanji_md51B1, &kanji_md6C8D, &kanji_md5709, &kanji_md7BCC, &kanji_md5FE4, &kanji_md6D6F, &kanji_md727E, &kanji_md5514, &kanji_md671E, &kanji_md73F8};
const reading_md onyomi_md0xf6b10d3c = {44, NULL, on_kanji0xf6b10d3c};
const kanji_md * const on_kanji0x8746b0a0[] = {&kanji_md5408, &kanji_md5F37, &kanji_md697D, &kanji_md696D, &kanji_md683C, &kanji_md53F7, &kanji_md8C6A, &kanji_md565B, &kanji_md90F7, &kanji_md6602, &kanji_md8F5F, &kanji_md50B2, &kanji_md525B, &kanji_md52AB, &kanji_md62F7, &kanji_md65FA, &kanji_md6FE0, &kanji_md58D5, &kanji_md6BEB, &kanji_md9D3B, &kanji_md56C2, &kanji_md54C8, &kanji_md6A02, &kanji_md5F4A, &kanji_md55F7, &kanji_md6556, &kanji_md9DD9, &kanji_md9C32, &kanji_md85D5, &kanji_md9F07, &kanji_md71AC, &kanji_md6282, &kanji_md87AF, &kanji_md5227, &kanji_md9068};
const reading_md onyomi_md0x8746b0a0 = {35, NULL, on_kanji0x8746b0a0};
const kanji_md * const on_kanji0x35c9d00f[] = {&kanji_md6975, &kanji_md7344};
const reading_md onyomi_md0x35c9d00f = {2, NULL, on_kanji0x35c9d00f};
const kanji_md * const on_kanji0x5ccd0faf[] = {&kanji_md8ECF};
const reading_md onyomi_md0x5ccd0faf = {1, NULL, on_kanji0x5ccd0faf};
const kanji_md * const on_kanji0xd43316df[] = {&kanji_md8ECF};
const reading_md onyomi_md0xd43316df = {1, NULL, on_kanji0xd43316df};
const kanji_md * const on_kanji0x9384bd41[] = {&kanji_md8A00, &kanji_md91D1, &kanji_md53B3, &kanji_md6A29, &kanji_md52E4, &kanji_md50C5, &kanji_md7434, &kanji_md61C3, &kanji_md6A8E, &kanji_md6B23, &kanji_md826E, &kanji_md56B4, &kanji_md6B0A, &kanji_md57A0, &kanji_md8ABE, &kanji_md9210};
const reading_md onyomi_md0x9384bd41 = {16, NULL, on_kanji0x9384bd41};
const kanji_md * const on_kanji0x909924e2[] = {&kanji_md4F5C, &kanji_md5DEE, &kanji_md5DE6, &kanji_md518D, &kanji_md8336, &kanji_md7802, &kanji_md67FB, &kanji_md9396, &kanji_md4F50, &kanji_md6C99, &kanji_md5750, &kanji_md4E9B, &kanji_md632B, &kanji_md88DF, &kanji_md8A50, &kanji_md55DF, &kanji_md5506, &kanji_md53C9, &kanji_md70B8, &kanji_md7D17, &kanji_md55C4, &kanji_md976D, &kanji_md84D1, &kanji_md9771, &kanji_md7463, &kanji_md5D6F, &kanji_md5A11, &kanji_md505A, &kanji_md9F5F, &kanji_md4E4D, &kanji_md7E12, &kanji_md548B, &kanji_md8E49, &kanji_md6268, &kanji_md7C11, &kanji_md6467, &kanji_md78CB, &kanji_md5EC8, &kanji_md91F5, &kanji_md68AD, &kanji_md6E23, &kanji_md53A6, &kanji_md976B, &kanji_md7051, &kanji_md9B93, &kanji_md7473, &kanji_md9BCA, &kanji_md838E, &kanji_md7C14, &kanji_md69CE, &kanji_md82F4, &kanji_md5C6E, &kanji_md6413, &kanji_md6260, &kanji_md5470, &kanji_md67E4};
const reading_md onyomi_md0x909924e2 = {56, NULL, on_kanji0x909924e2};
const kanji_md * const on_kanji0x5f1d3646[] = {&kanji_md6700, &kanji_md5207, &kanji_md7D30, &kanji_md6BBA, &kanji_md969B, &kanji_md518D, &kanji_md6B73, &kanji_md897F, &kanji_md6E08, &kanji_md59BB, &kanji_md8CA1, &kanji_md624D, &kanji_md8F09, &kanji_md796D, &kanji_md88C1, &kanji_md7815, &kanji_md50AC, &kanji_md51C4, &kanji_md5F69, &kanji_md707D, &kanji_md63A1, &kanji_md83DC, &kanji_md6589, &kanji_md585E, &kanji_md658E, &kanji_md6D12, &kanji_md91C7, &kanji_md5BB0, &kanji_md6652, &kanji_md53C9, &kanji_md6B86, &kanji_md67F4, &kanji_md50B5, &kanji_md7826, &kanji_md683D, &kanji_md54C9, &kanji_md81CD, &kanji_md976D, &kanji_md731C, &kanji_md6ED3, &kanji_md84D1, &kanji_md5072, &kanji_md622A, &kanji_md8CFD, &kanji_md4F1C, &kanji_md7280, &kanji_md9771, &kanji_md5005, &kanji_md9F4E, &kanji_md7726, &kanji_md973D, &kanji_md7BE9, &kanji_md816E, &kanji_md9C13, &kanji_md91C6, &kanji_md780C, &kanji_md8C7A, &kanji_md5D14, &kanji_md5BE8, &kanji_md7C11, &kanji_md6467, &kanji_md8403, &kanji_md8521, &kanji_md91F5, &kanji_md7DB5, &kanji_md7E94, &kanji_md7725, &kanji_md96B9, &kanji_md984B, &kanji_md976B, &kanji_md7051, &kanji_md7E21, &kanji_md9F4B, &kanji_md5115, &kanji_md7C14, &kanji_md6FDF, &kanji_md9F4A, &kanji_md6DEC, &kanji_md64E0, &kanji_md8E8B, &kanji_md6DD2, &kanji_md788E, &kanji_md6413, &kanji_md97F2, &kanji_md72B2, &kanji_md840B, &kanji_md6CDA};
const reading_md onyomi_md0x5f1d3646 = {87, NULL, on_kanji0x5f1d3646};
const kanji_md * const on_kanji0x3fe4978c[] = {&kanji_md4F5C, &kanji_md6570, &kanji_md6628, &kanji_md7B56, &kanji_md7D22, &kanji_md932F, &kanji_md518A, &kanji_md524A, &kanji_md6349, &kanji_md96C0, &kanji_md67F5, &kanji_md70B8, &kanji_md643E, &kanji_md9061, &kanji_md9162, &kanji_md947F, &kanji_md7C00, &kanji_md6714, &kanji_md505A, &kanji_md7A84, &kanji_md4E4D, &kanji_md6EAF, &kanji_md548B, &kanji_md5616, &kanji_md612C, &kanji_md518C, &kanji_md9F6A, &kanji_md918B, &kanji_md69CA, &kanji_md7B70, &kanji_md6578, &kanji_md67DE, &kanji_md84B4, &kanji_md7B74, &kanji_md80D9};
const reading_md onyomi_md0x3fe4978c = {35, NULL, on_kanji0x3fe4978c};
const kanji_md * const on_kanji0xe62595a2[] = {&kanji_md85A9};
const reading_md onyomi_md0xe62595a2 = {1, NULL, on_kanji0xe62595a2};
const kanji_md * const on_kanji0xf0308db6[] = {&kanji_md65E9};
const reading_md onyomi_md0xf0308db6 = {1, NULL, on_kanji0xf0308db6};
const kanji_md * const on_kanji0x6ec6ee26[] = {&kanji_md6BBA, &kanji_md5BDF, &kanji_md62F6, &kanji_md672D, &kanji_md518A, &kanji_md5237, &kanji_md64AE, &kanji_md64E6, &kanji_md6492, &kanji_md5239, &kanji_md85A9, &kanji_md98AF, &kanji_md976D, &kanji_md56C3, &kanji_md9771, &kanji_md518C, &kanji_md976B, &kanji_md5273, &kanji_md7D2E, &kanji_md7B9A, &kanji_md624E};
const reading_md onyomi_md0x6ec6ee26 = {21, NULL, on_kanji0x6ec6ee26};
const kanji_md * const on_kanji0x4ed2cc4a[] = {&kanji_md7E89};
const reading_md onyomi_md0x4ed2cc4a = {1, NULL, on_kanji0x4ed2cc4a};
const kanji_md * const on_kanji0x71e75824[] = {&kanji_md4E09, &kanji_md6B8B, &kanji_md5C71, &kanji_md6563, &kanji_md53C2, &kanji_md7523, &kanji_md7B97, &kanji_md5C3D, &kanji_md64CD, &kanji_md60E8, &kanji_md8CDB, &kanji_md9178, &kanji_md65AC, &kanji_md5098, &kanji_md6749, &kanji_md6492, &kanji_md8B83, &kanji_md67F5, &kanji_md685F, &kanji_md9910, &kanji_md71E6, &kanji_md61FA, &kanji_md64B0, &kanji_md73CA, &kanji_md9582, &kanji_md7E82, &kanji_md8695, &kanji_md9730, &kanji_md8B92, &kanji_md947D, &kanji_md7C2A, &kanji_md7AC4, &kanji_md7C12, &kanji_md76DE, &kanji_md994C, &kanji_md849C, &kanji_md759D, &kanji_md8B9A, &kanji_md68E7, &kanji_md8DDA, &kanji_md6F7A, &kanji_md886B, &kanji_md6214, &kanji_md7E94, &kanji_md5B71, &kanji_md945A, &kanji_md6F78, &kanji_md53C3, &kanji_md76E1, &kanji_md8518, &kanji_md93E8, &kanji_md829F, &kanji_md6C55, &kanji_md7CB2, &kanji_md5D84, &kanji_md7228, &kanji_md8D0A, &kanji_md6505, &kanji_md5F61, &kanji_md522A, &kanji_md7E56, &kanji_md61F4, &kanji_md6158, &kanji_md8836, &kanji_md69E7, &kanji_md9A42, &kanji_md5DC9, &kanji_md7E89};
const reading_md onyomi_md0x71e75824 = {68, NULL, on_kanji0x71e75824};
const kanji_md * const on_kanji0xe8e2955b[] = {&kanji_md5EA7, &kanji_md5750, &kanji_md632B, &kanji_md84D9};
const reading_md onyomi_md0xe8e2955b = {4, NULL, on_kanji0xe8e2955b};
const kanji_md * const on_kanji0xf61bc047[] = {&kanji_md5728, &kanji_md7F6A, &kanji_md6750, &kanji_md8CA1, &kanji_md5264, &kanji_md85BA};
const reading_md onyomi_md0xf61bc047 = {6, NULL, on_kanji0xf61bc047};
const kanji_md * const on_kanji0x78b9c691[] = {&kanji_md96D1, &kanji_md96DC, &kanji_md894D};
const reading_md onyomi_md0x78b9c691 = {3, NULL, on_kanji0x78b9c691};
const kanji_md * const on_kanji0xce973985[] = {&kanji_md6B8B, &kanji_md60E8, &kanji_md65AC, &kanji_md66AB, &kanji_md61FA, &kanji_md615A, &kanji_md8B92, &kanji_md5879, &kanji_md9C52, &kanji_md7AC4, &kanji_md6159, &kanji_md7E94, &kanji_md93E8, &kanji_md5D84, &kanji_md6B98, &kanji_md61F4, &kanji_md69E7, &kanji_md5DC9};
const reading_md onyomi_md0xce973985 = {18, NULL, on_kanji0xce973985};
const kanji_md * const on_kanji0x817a4f7d[] = {&kanji_md601D, &kanji_md81EA, &kanji_md5B50, &kanji_md6B7B, &kanji_md6307, &kanji_md4F7F, &kanji_md6B21, &kanji_md59FF, &kanji_md4ED5, &kanji_md56DB, &kanji_md6B62, &kanji_md59CB, &kanji_md8996, &kanji_md58EB, &kanji_md652F, &kanji_md7D19, &kanji_md79C1, &kanji_md793A, &kanji_md523A, &kanji_md5E2B, &kanji_md6B6F, &kanji_md8A66, &kanji_md5FD7, &kanji_md5E02, &kanji_md81F3, &kanji_md8CC7, &kanji_md7CF8, &kanji_md77E2, &kanji_md53F2, &kanji_md53F8, &kanji_md6C0F, &kanji_md59C9, &kanji_md829D, &kanji_md679D, &kanji_md8A8C, &kanji_md65BD, &kanji_md7D2B, &kanji_md98FC, &kanji_md8A5E, &kanji_md8997, &kanji_md8102, &kanji_md65E8, &kanji_md8A69, &kanji_md662F, &kanji_md4F3A, &kanji_md80A2, &kanji_md9AED, &kanji_md4E4B, &kanji_md6F2C, &kanji_md4F8D, &kanji_md8210, &kanji_md5C4D, &kanji_md4ED4, &kanji_md53EA, &kanji_md8CDC, &kanji_md7345, &kanji_md96CC, &kanji_md6652, &kanji_md55DC, &kanji_md6B64, &kanji_md7B25, &kanji_md5F1B, &kanji_md67FF, &kanji_md67F4, &kanji_md98F4, &kanji_md646F, &kanji_md7940, &kanji_md8494, &kanji_md71BE, &kanji_md8328, &kanji_md6ECB, &kanji_md55E4, &kanji_md6ED3, &kanji_md5634, &kanji_md65AF, &kanji_md75E3, &kanji_md5072, &kanji_md8D04, &kanji_md5319, &kanji_md55E3, &kanji_md5DF3, &kanji_md75B5, &kanji_md7960, &kanji_md6063, &kanji_md7949, &kanji_md7947, &kanji_md53A0, &kanji_md5E5F, &kanji_md5D6F, &kanji_md6893, &kanji_md9BA8, &kanji_md7825, &kanji_md7FC5, &kanji_md6043, &kanji_md8AEE, &kanji_md7E12, &kanji_md9F4E, &kanji_md4FDF, &kanji_md7726, &kanji_md8332, &kanji_md5740, &kanji_md8006, &kanji_md4F88, &kanji_md5852, &kanji_md54AB, &kanji_md8DBE, &kanji_md5F11, &kanji_md7BE9, &kanji_md9F52, &kanji_md8F1C, &kanji_md9C13, &kanji_md8086, &kanji_md8DBA, &kanji_md5B5C, &kanji_md9D44, &kanji_md5C4E, &kanji_md8AE1, &kanji_md63E3, &kanji_md53B6, &kanji_md7957, &kanji_md7D72, &kanji_md5C38, &kanji_md557B, &kanji_md9C24, &kanji_md67B3, &kanji_md9BD4, &kanji_md7725, &kanji_md6CD7, &kanji_md6894, &kanji_md5EC1, &kanji_md99DB, &kanji_md8C55, &kanji_md9D1F, &kanji_md5F99, &kanji_md54A8, &kanji_md9DD9, &kanji_md7DC7, &kanji_md8B1A, &kanji_md89DC, &kanji_md962F, &kanji_md99DF, &kanji_md5E0B, &kanji_md74F7, &kanji_md7AE2, &kanji_md7CA2, &kanji_md53AE, &kanji_md5DF5, &kanji_md5EDD, &kanji_md801C, &kanji_md86A9, &kanji_md4E8A, &kanji_md5470, &kanji_md84CD, &kanji_md6C9A, &kanji_md4E28, &kanji_md5B73, &kanji_md673F, &kanji_md6CDA, &kanji_md7564, &kanji_md82E1, &kanji_md8CB2, &kanji_md91F6};
const reading_md onyomi_md0x817a4f7d = {162, NULL, on_kanji0x817a4f7d};
const kanji_md * const on_kanji0xf0189267[] = {&kanji_md5F11};
const reading_md onyomi_md0xf0189267 = {1, NULL, on_kanji0xf0189267};
const kanji_md * const on_kanji0x9647b173[] = {&kanji_md8272, &kanji_md8B58, &kanji_md5F0F, &kanji_md7E54, &kanji_md62ED, &kanji_md95BE, &kanji_md8EFE, &kanji_md991D};
const reading_md onyomi_md0x9647b173 = {8, NULL, on_kanji0x9647b173};
const kanji_md * const on_kanji0x59b36477[] = {&kanji_md8CEA, &kanji_md4E03, &kanji_md53F1, &kanji_md6089};
const reading_md onyomi_md0x59b36477 = {4, NULL, on_kanji0x59b36477};
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
